samansayad93/HomeIntelligence/documents/پایان نامه کارشناسی.pdf

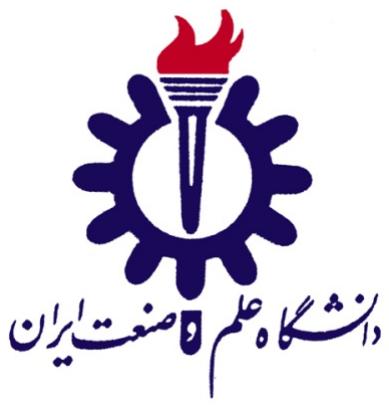
[picture p38: figure]

هدکشناد یسدنهم رتویپماک
هژورپ ینایاپ یسانشراک

## ناونع هژورپ : یحارط و هدایپ يزاس هناماس دنمشوه صیخشت دود و لرتنک تازیهجت یگناخ یتبم رب 32ESP

هدنراگن :
ناماس دایص لاعف
401521408

داتسا امنهار :
رتکد ریما يدهم ینیسح هزنم

رویرهش هام 1405

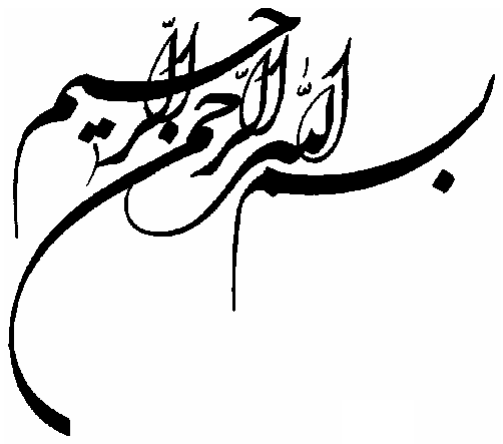
[picture p39: figure]

أ

هدیکچ

رد نیا ،هژورپ کی هناماـس دنمـشوه ینتبم رب درب 32ESP اب فده یحارط و هدایپ يزاـس کی دحاو هچراپکی يارب شیاپ طیارـش ،یطیحم صیخـشت طیارـش رطخ و لرتنک تازیهجت یکینورتکلا هعـسوت هداد هدـش تـسا . فده یلـصا ،هناماـس مهارف ندرک ناکما تفایرد و شزادرپ تاعلاطا یطیحم و لاقتنا اهنآ هب کی هناماـس مرن يرازفا زا قیرط هکبـش یب ،میـس رد رانک داجیا تیلباق لرتنک و را لاـس نامرف هب یخرب تازیهجت یکینورتکلا دوجوم رد طیحم تـسا . هب نم ظ رو شیاپ تیعـضو ،طیحم هاگتـسد هب هعومجم يا زا اهرگـسح لماـش رگـسح زاگ -2MQ، رگـسح امد و تبوطر 11DHT، رگـسح تدـش رون LDR و رگـسح صیخـشت تکرح PIR زهجم هدـش تـسا . رگـسح -2MQ اب هدافتـسا زا یجورخ ،گولانآ ناکما دنا هزا يریگ حطـس یبـسن زاگ و دود دوجوم رد طیحم ار مهارف یم دنک و رد تروـص روبع رادقم هزادنا يریگ هدـش زا هناتـسآ نییعت ،هدـش طیارـش هب ناونع تیعـضو رادشه ییاسانش هدش و هناماس مادقا هب لاعف يزاس رادشه یتوص یم دنک . نینچمه تاعلاطا طوبرم هب ،امد ،تبوطر تدـش رون و تیعـضو رح تک رد هزاب ياه ینامز صخـشم زا طیحم تفایرد هدـش و يارب شیاپ و شیامن تیعــضو متــسیــس رد رایتخا هناماــس مرن يرازفا رارق یم دریگ . هب روظنم شیازفا تیلباق يدربراک هاگتــسد رد هزوح لرتنک ،تازیهجت ود رتــسب یطابترا ییویدار RF رد سناکرف ياه 315 و 433 زترهاگم و نینچمه طابترا م نودا زمرق IR رد هناماـس رد رظن هتفرگ هدـش تـسا . نیا شخب ناکما تفایرد و ییاـسانـش نامرف ياه ییویدار و نودام ،زمرق هریخذ يزاـس اهنآ و هدافتـسا ددجم زا نامرف ياه هریخذ هدـش يارب لرتنک تازیهجت راگزاـس ار مهارف یم دنک . طابترا هاگتـسد اب هکبـش زا قیرط تیلباق WiFi درب 32ESP رارقرب هدـش و هب روظنم لاقتنا هداد و نامرف نایم هاگتــسد و هناماــس مرن يرازفا زا لکتورپ MQTT هدافتــسا هدــش تــسا . نینچمه يارب هداـس يزاـس هار يزادنا هیلوا و يریگولج زا یگتـسباو هب تاعلاطا هکبـش ،تباث کی راکوزاـس provisioning رد هاگتـسد هدایپ يزاـس هدـش تـسا هک زا یرط ق کی هطقن یـسرتـسد یب میـس و هاگرد يدنبرکیپ تحت ،بو ناکما نت ظ می تاـصخـشم هکبـش WiFi، تاعلاطا Broker MQTT ار مهارف یم دنک . رد شخب مرن يرازفا ربراک زین کی دروبـشاد تحت بو يارب شیامن هداد ياه تفایرد هدـش زا هاگتـسد و لاـسرا نامرف ياه یلرتنک یحارط هدـش تـسا . هب نیا ،بیترت ربراک یم دناوت نودب زاین هب یـسرتـسد میقتـسم هب تخـس ،رازفا تیعــضو طیحم ار شیاپ ،هدرک طیارــش رادــشه ار هدهاــشم هدومن و نامرف ياه دروم زاین ار يارب تازیهجت لاـسرا دنک . نیا هناماـس یم دناوت هب ناونع کی هنومن هیاپ يارب هعـسوت راکهار ياه دنمـشوه يزاـس طیحم ياه ینوکسم و دا ،يرا هناماس ياه شیاپ یطیحم و متسیس ياه لرتنک تازیهجت دروم هدافتسا رارق دریگ .

هژاو ياه يدیلک : هناخ ،دنمشوه نویساموتا ،یگناخ 32ESP، تنرتنیا ایشا ( IoT(

تسرهف بلاطم

ب

لصف :1 همدقم 1
-1-1 بی نا هلئسم | 2
-1-2 مها یت و ترورض هژورپ | 3
-1-3 فادها هژورپ | 4
-1-4 هدودحم هژورپ | 5
-1-5 شور ماجنا هژورپ | 5

لصف :2 نابم ی رظن ي 7
-2-1 ای تنرتن شا یا | 8
-2-1-1 ازجا ي لصا ی یک هناماس IoT | 8
-2-1-2 دربراک ای تنرتن شا یا رد هناخ دنمشوه | 9
-2-2 سی متس اه ي هناخ دنمشوه | 9
-2-3 می رلرتنکورک 32ESP | 10
10 | | | | | | | | | | | GPIO-2-3-2
-2-3-3 لدبم گولانآ هب دیجی لات ADC | 11
-2-4 رگسح اه ي حم یطی | 11
-2-4-1 رگسح -2MQ | 11
-2-4-2 رگسح 11DHT | 12
-2-4-3 رگسح تدش رون LDR | 13
-2-4-4 رگسح خشت یص تکرح PIR | 14
-2-5 رزاب | 14
-2-6 طابترا نودام زمرق | 15
-2-7 طابترا دار یو یی RF | 16
-2-8 طابترا WiFi | 17
18 ....... | | | | | | | | | Captive Portal-2-8-1
-2-9 لکتورپ MQTT | 18
18 ...... | | | | | | | | | MQTT Broker-2-9-1
-2-9-2 کیفیت ورس یس | 19
-2-9-3 طابترا MQTT زا رط یق WebSocket | 19
-2-10 خذ ی هر زاس ي تاعلاطا رد 32ESP | 20

لصف :3 لحت یل و حارط ی سی متس 21
-3-1 لحت یل نی دنمزا ي اه ي سی متس | 22
-3-2 رامعم ي لک ی سی متس | 24
-3-2-2 لایه تخس رازفا و عمج روآ ي هداد | 24
-3-2-3 لایه شزادرپ و لرتنک | 25
-3-2-4 لایه طابترا ی و طبار ربراک | 25
-3-3 حارط ی تخس رازفا | 26
-3-3-1 دحاو شزادرپ زکرم ي و لاصتا اهرگسح | 26
-3-3-2 سی متس طابترا سناکرف دار یو یی | 27
-3-3-3 سی متس طابترا نودام زمرق | 27
-3-3-4 سی متس رادشه و امن یش عضو یت | 28

تسرهف بلاطم

ج

-3-4 حارط ی مرن رازفا و راتخاس Firmware | 29
-3-4-1 راتخاس رلاوژام Firmware | 29
-3-4-2 هار زادنا ي و ارجا ي لصا ی سی متس | 30
-3-4-3 دم یریت اهرگسح و قطنم رادشه | 31
-3-5 حارط ی طابترا WiFi و MQTT | 32
-3-5-1 پی دنبرک ي و طابترا WiFi | 33
-3-5-2 طابترا MQTT | 33
-3-6 حارط ی سی متس RF | 34
-3-6-1 رد ی تفا و خذ ی هر زاس ي سی لانگ RF | 34
-3-6-2 شخپزاب و دم یریت سی لانگ RF | 35
-3-7 حارط ی سی متس نودام مرق ز | 35
-3-7-1 رد ی تفا و خذ ی هر زاس ي سی لانگ IR | 36
-3-7-2 شخپزاب و دم یریت سی لانگ IR | 36
-3-8 حارط ی سی متس خذ ی هر زاس ي | 36
-3-8-1 خذ ی هر ظنت ی تام و تاعلاطا هاگتسد | 37
-3-8-2 خذ ی هر زاس ي سی لانگ RF و IR | 37
-3-9 حارط ی سی متس Provisioning و Portal Captive | 38
-3-10 حارط ی Dashboard Web | 38

لصف :4 پی هدا زاس ي هناماس 40
-4-1 حم یط و رازبا اه ي هعسوت | 41.
-4-2 پی هدا زاس ي تخس رازفا | 42
-4-2-1 پی هدا زاس ي رگسح اه ي حم یطی | 42
-4-2-2 پی هدا زاس ي سی متس شه راد توص ی | 45
-4-3 پی هدا زاس ي سی متس طابترا دار یو یی RF | 46
-4-3-1 رد ی تفا و خذ ی هر زاس ي سی لانگ RF | 47
-4-3-2 شخپزاب و دم یریت سی لانگ RF | 47
-4-3-3 قطنم لک ی رد ی تفا و لاسرا RF | 49
-4-4 پی هدا زاس ي سی متس ودام ن زمرق IR | 49
-4-4-1 رد ی تفا و خذ ی هر زاس ي سی لانگ IR | 50
-4-4-2 شخپزاب و دم یریت سی لانگ IR | 51
-4-4-3 قطنم لک ی رد ی تفا و لاسرا IR | 53
-4-5 پی هدا زاس ي طابترا WiFi و MQTT | 53
-4-5-1 ای داج و هار زادنا ي Client MQTT | 53
-4-5-2 رارقرب ي و دم یریت لاصتا WiFi و MQTT | 54
-4-5-3 رد ی تفا و راشتنا نامرف اه ي MQTT | 56
-4-6 پی هدا زاس ي پی دنبرک ي لوا یه و دم یریت لاصتا هب هکبش | 57
-4-6-1 راتخاس تاعلاطا و هار زادنا ي | 57
-4-6-2 پی هدا زاس ي Portal Captive و دم یریت تساوخرد اه ي HTTP | 59
-4-6-3 رد ی تفا ، جنسرابتعا ی و خذ ی هر ظنت ی تام | 60
-4-7 پی هدا زاس ي دم یریت هظفاح و خذ ی هر زاس ي تاعلاطا | 60
-4-7-1 خذ ی هر و زاب ی با ی عضو یت هاگتسد | 61
-4-7-2 خذ ی هر و زاب ی با ی سی لانگ اه ي RF و IR | 61

تسرهف بلاطم

د

-4-8 هار زادنا ي و گنهامه ی لوژام اه | 61
-4-8-1 دم یریت نامرف اه ي سی متس | 63
-4-8-2 دم یریت اهرگسح و اظو یف هرود اي | 64
-4-9 پی هدا زاس ي دروبشاد بو و طبار ربراک ي | 65
-4-9-2 لاصتا هب Broker MQTT و رد ی تفا تاعلاطا | 65
-4-9-3 لاسرا نامرف و دم یریت عضو یت هناماس | 66

لصف :5 نومزآ و زرا ی با ی سی متس 67
-5-1 شور نومزآ و زرا ی با ی هناماس | 68
-5-2 نومزآ درکلمع اهرگسح | 68
-5-2-1 نومزآ رگسح امد و تبوطر | 69
-5-2-2 نومزآ رگسح رون | 69
-5-2-3 نومزآ رگسح دود و شتآ | 70
-5-2-4 نومزآ رگسح خشت یص تکرح | 71
-5-3 نومزآ هناماس رادشه | 71
-5-4 نومزآ لاصتا هب WiFi و Broker MQTT | 72
-5-5 نومزآ دروبشاد هناماس | 72
-5-6 نومزآ سی متس RF | 74
-5-6-1 نومزآ رد ی تفا سی لانگ RF | 74
-5-6-2 نومزآ لاسرا سی لانگ RF | 74
-5-6-3 نومزآ دم یریت سی لانگ RF | 75
-5-7 نومزآ سی متس IR | 75
-5-7-1 نومزآ رد ی تفا سی لانگ IR | 76
-5-7-2 نومزآ لاسرا سی لانگ IR | 76
-5-7-3 نومزآ دم یریت سی لانگ IR | 77
-5-8 نومزآ زیر هناماس Provisioning | 77

لصف :6 تن ی هج گیري 79
-6-1 عمج دنب ي لحارم ماجنا هژورپ | 80
-6-2 اتن یج لصاح زا پی هدا زاس ي | 80
-6-3 دودحم یت اه ي هژورپ | 81
-6-4 پی داهنش اه ي هعسوت رد آی هدن | 81
-6-5 عمج دنب ي اهن یی | 82

لصف :7 عجارم 83

لصف :8 تسویپ اه 85

تسرهف لاکشا

ه

لکش ( 1-2 ) می رلرتنکورک 32ESP | 10.
لکش ( 2-2 ) رگسح -2MQ | 12
لکش ( 3-2 ) رگسح 11DHT | 12
لکش ( 4-2 ) رگسح تدش رون | 13
لکش ( 5-2 ) رگسح خشت یص تکرح PIR | 14
لکش ( 6-2 ) رزاب | 14.
لکش ( 7-2 ) گی هدنر و هدنتسرف نودام زمرق | 15
لکش ( 8-2 ) گی هدنر دار یو یی | 16
لکش ( 9-2 ) هدنتسرف دار یو یی | 16
لکش ( 1-3 ) رامعم ي لک ی سی متس | 24.
لکش ( 2-3 ) دنور هار زادنا ي سی متس | 30
لکش ( 3-3 ) دنور ارجا ي هقلح لصا ی سی متس | 31
لکش ( 4-3 ) دنور دم یریت رگسح اه | 31
لکش ( 5-3 ) دنور دم یریت رگسح -2MQ | 31
لکش ( 1-4 ) دنور تخاس و راذگراب ي Firmware | 42
لکش ( 2-4 ) ارف ی دن رد ی تفا سی لانگ RF | 49
لکش ( 3-4 ) ارف ی دن لاسرا سی لانگ RF | 49
لکش ( 4-4 ) ارف ی دن رد ی تفا سی لانگ IR | 53
لکش ( 5-4 ) ارف ی دن لاسرا سی لانگ IR | 53
لکش ( 6-4 ) هحفص ظنت ی تام | 59
لکش ( 7-4 ) دروبشاد بو | 65
لکش ( 1-5 ) اتن یج رگسح امد و تبوطر | 69
لکش ( 2-5 ) تن ی هج رگسح رون | 69
لکش ( 3-5 ) اتن یج رگسح دود و شتآ | 70
لکش ( 4-5 ) اتن یج رگسح خشت یص تکرح | 71
لکش ( 5-5 ) تن ی هج نومزآ لاصتا هب هکبش و Broker MQTT | 72
لکش ( 6-5 ) امن یش تاعلاطا اهرگسح رد دروبشاد | 72
لکش ( 7-5 ) امن یش رادشه رد دروبشاد | 73
لکش ( 8-5 ) لاسرا نامرف زا دروبشاد | 73
لکش ( 9-5 ) رد ی تفا سی لانگ RF | 74
لکش (10-5 ) لاسرا سی لانگ RF | 74
لکش ( 11-5 ) دم یریت سی لانگ RF | 75
لکش ( 12-5 ) رد ی تفا سی لانگ IR | 76
لکش (13-5 ) لاسرا سی لانگ IR | 76
لکش ( 14-5 ) دم یریت سی لانگ IR | 77
لکش ( 15-5 ) هحفص ظنت ی تام Provisioning | 78

تسرهف لوادج

و

لودج ( 1-3) اپ یه اه ي 32ESP | 28
لودج ( 2-3) ظو ی هف لوژام اه ي Firmware | 29
لودج ( 3-3)Topic اه ي برم طو هب اهرگسح | 33
لودج ( 4-3) تاصخشم AP | 38
لودج ( 1-4) راتخاس هداد ظنت ی تام Provisioning | 58.

# لصف 1 :

# همدقم

حارط ی و پی هدا زاس ی خشت دنمشوھ ھناماس یص ھجت لرتنک و دود ی تاز گناخ ی تبم ی رب 32ESP

2

ھمدقم
رد لاـس ياه ،ریخا هعـسوت يروانف ياه یطابترا و هناماـس ياه هتفهن بجوم شرتـسگ هدافتـسا زا متـسیـس ياه دنمـشوه رد طیحم ياه ،ینوکـسم يرادا و یتعنـص هدـش تـسا . یکی زا مهم نیرت هزوح ياه لـصاح زا نیا ،هعـسوت تنرتنیا یـشا ا ( Things of Internet ای IoT ( تـسا . تنرتنیا ایـشا هب کبـش ه يا زا تازیهجت یکیزیف قلاطا یم دوـش هک اب هرهب يریگ زا ،اهرگـسح دنزادرپ ه ،اه مرن اهرازفا و طـساو ياه ،یطابترا تیلباق مج ع ،يروآ ،شزادرپ لدابت تاعلاطا و رد یخرب دراوم لامعا لرتنک رب طیحم نوماریپ دوخ ار دنراد .[1] رد نینچ هناماـس ،ییاه اهرگــسح هفیظو تفایرد تاعلاطا زا ،طیحم دحاو یــشزادرپ هفیظو لیلحت و تیریدم هداد اه و شخب یطابترا هفیظو لاقتنا تاعلاطا و تفایرد نامرف ياه یلرتنک ار رب هدهع دراد [1] [2]. یکی زا ياهدربراک مهم تنرتنیا ،ایـشا هعـسوت هناماـس ياه دنمـشوه یگناخ تـسا . رد کی طیحم ،دنمـشوه تازیهجت فلتخم یم دنناوت زا قیرط کی هکبـش یطابترا اب رگیدکی و اب ربراک لماعت هتـشاد دنـشاب . نیا لماعت یم دناوت لماــش شیاپ طیارــش ،یطیحم صیخــشت دادخر ياه ،يداعریغ لاــسرا ،رادــشه لرتنک تازیهجت یکیرتکلا و تبث تاعلاطا دــشاب . هدافتــسا زا نینچ هناماــس ییاه یم دناوت ناکما تراظن زا هار رود و شهاک یگتسباو هب لرتنک یتسد تازیهجت ار مهارف دنک . رد نیا ،هژورپ کی باه دنمـشوه ینتبم رب درب 32ESP یحارط و دایپ ه يزاـس هدـش ـسا ت . 32ESP کی هناماـس يور هـــشارت اـب تـیلباـق WiFi رد دـناـب 2.4 ،زترهاـگیگ هدـنزادرپ 32 یتیب و هـعومجم يا زا طـــساو ياـه يدورو / یجورخ لاتیجید و انآ گول تـسا هک طـسوت تکرـش Espressif هئارا هدـش و يارب ییاهدربراک زا هلمج تازیهجت دنمـشوه یگناخ و تنرتنیا ایـشا بـسانم ـسا ت [3]. نیا گژیو ی اه ثعاب هدـش تـسا 32ESP دناوتب هولاع رب شزادرپ داد ه ياه ،اهرگـسح طابترا کبـش ه يا و لرتنک تازیهجت یبناج را زین رد کی دحاو تخـس يرازفا ماجنا دهد .
متـسیـس هعـسوت هتفای رد نیا هژورپ هولاع رب صیخـشت دود و ،زاگ ناکما هزادنا يریگ ،امد تبوطر و تدـش رون و نینچمه صیخـــشت تـکرح ار مهارف یم دـنک . نینچمه يارب شیازفا تـیلباـق لرتنک تازیهجت ،فلتخم ود هـعومجم طاـبترا ییویدار رد سناـکرف ياـه 315 و 433 زترهاـگم و کـی هـعومجم طاـبترا نوداـم زمرق رد رظن هتفرگ هدـش تـسا . هب نیا ،بیترت متـسیـس رداق تـسا یخرب لانگیـس ياه ییویدار و نودام زمرق ار ،تفایرد هریخذ و رد تروص زاین شخپزاب دنک . طابترا نایم باه دنمـشوه و تخاـسریز مرن يرازفا متـسیـس زا قیرط WiFi و لکتورپ MQTT ماجنا یم دوـش . MQTT کی لکتورپ یطابترا کبـس ینتبم رب يوگلا راـشتنا / كارتـشا (Subscribe/Publish (تـسا هک هب روط هژیو يارب طیحم ياه ياراد تیدودحم عبانم و ياهدربراک نیـشام به نیـشام و تنرتنیا ایـشا بـسانم یحارط هدـش ـسا ت [4]. رد یا ن ،هژورپ هداد ياه اهرگـسح زا قیرط MQTT رـشتنم هدـش و امرف ن ياه یلرتنک زین زا قیرط نیمه رتسب هب 32ESP لاسرا یم دنوش . زا يوــس ،رگید يارب لماعت ربراک اب ،متــسیــس کی دروبــشاد تحت بو یحارط هدــش تــسا هک زا قیرط WebSocket هب Broker MQTT لـصتم یم دوـش . نیا دروبـشاد ناکما هدهاـشم تاعلاطا ،اهرگـسح هدهاـشم اهرادـشه و لاـسرا نامرف ياه یلرتنک ار مهارف یم دنک . رد ،هجیتن هژورپ رـضاح ار یم ناوت کی باه دنمـشوه نچ د هروظنم تــسناد هک فیاظو شیاپ ،طیحم صیخــشت ،دادخر داجیا ،رادــشه طابترا بــش هک يا و لرتنک تازیهجت ار رد کی هناماس هچراپکی ماجنا یم دهد .

-1-1 نایب هلئسم

رد يرایـسب زا طیحم ياه ینوکـسم و ،يرادا تازیهجت یکیرتکلا و هناماـس ياه فلتخم هب تروـص لقتـسم دروم هدافتـسا رارق یم دنریگ و تاعلاطا طوبرم هب طیارـش یطیحم زین ًلاومعم هب تروـص زکرمتم و رمتـسم عمج

3

ھمدقم
يروآ من ی دوــش . رد شور ياه ،یتنــس صیخــشت ییاهدادخر دننام یازفا ش نازیم دود ای ،زاگ تارییغت ،امد روـضح دارفا ای رییغت دیدـش طیارـش يرون نکمم تـسا هب تروـص یتـسد ای طـسوت تازیهجت لقتـسم ماجنا دوـش . نینچ يدرکیور هولاع رب شیازفا یگدـیچیپ ،متـــسیـــس ناـکما شیاـپ هـچراـپکی و لرتنک زا هار رود ار دودـحم یم دنک .
زا فرط ،رگید يرایــسب زا تازیهجت وم دوج رد طیحم ياه یگناخ زا شور ياه یطابترا یتوافتم يارب لرتنک هداـفتـــسا یم دـننک . یخرب تازیهجت زا ومیر ت ياـه نوداـم زمرق و یخرب رگید زا تومیر ياـه ییویدار رد سناـکرف ییاـه دـنناـم 315 اـی 433 زترهاـگم هداـفتـــسا یم دـننک . رد ،هـجیتن يارب لرتنک هـچراـپکی نیا تازیهجت ًلاومعم این ز هب نیدنچ رتنک ل هدننک و طساو ازجم دوجو دراد . هلئـسم یلـصا نیا ،هژورپ یحارط و هدایپ يزاـس کی هناماـس هچراپکی تـسا هک دناوتب تاعلاطا طوبرم هب طیارـش طیحم ار زا قیرط هعومجم يا زا اهرگـسح تفایرد ،هدرک اهنآ ار رد کی دحاو یـشزادرپ تیریدم ،دنک تاعلاطا ار زا قیرط هـکبـــش WiFi و MQTT رد راـیتخا مرن رازفا رارق دـهد و ناـکما لرتنک تازیهجت یکیرتکلا ار زین مهارف دنک .
يارب یبایتسد هب نیا ،فده زا 32ESP هب ناونع هتسه یشزادرپ و یطابترا متسیس هدافتسا هدش تسا . رد شخب شیاپ ،طیحم روـسنـس -2MQ يارب صیخـشت دود و ياهزاگ لباق ،لاعتـشا روـسنـس 11DHT يارب هزادنا يریگ امد و ،تبوطر رگـسح يرون LDR يارب هزادنا يریگ یبـسن تدـش رون و رگـسح یتکرح PIR يارب صیخـشت تکرح دروم هدافتـسا رارق هتفرگ دنا . تاعلاطا به تـسد هدمآ زا نیا اهرگـسح هب تروـص هرود يا شزادرپ و زا قیرط MQTT رشتنم یم دنوش . رد شخب لرتنک زین متــسیــس زا گ هدنری و هدنتــسرف ياه RF رد ود دناب 315 و 433 زترهاگم و نینچمه هدنریگ و هدنتـسرف نودام زمرق هدافتـسا یم دنک . هناخباتک RCSwitch ناکما تفایرد و لاـسرا ياهدک یخرب تازیهجت ییویدار جیار رد سناـکرف ياـه 315 و 433 زترهاـگم ار مهارف یم دـنک [5] . نینچمه هـناـخباـتک 8266IRremoteESP يارب تفایرد و لاسرا لانگیس ه يا نودام زمرق دروم هدافتسا رارق هتفرگ تسا [6]. ،نیاربانب هلئـسم نیا هژورپ ار یم ناوت هب تروـص یحارط کی باه دنمـشوه فیرعت درک هک هـس هفیظو یلـصا شیاپ طیارـش ،یطیحم صیخـشت دادخر و داجیا رادـشه و لرتنک تازیهجت یکیرتکلا ار رد کی رتـسب دحاو بیکرت یم نک د.

-1-2 تیمها و ترورض هژورپ

شیازفا هدافتـسا زا تازیهجت یکیرتکلا و شرتـسگ متـسیـس ياه ،دنمـشوه زاین هب هناماـس ییاه ار شیازفا هداد تـسا هک دناوتب هولاع رب لرتنک ،تازیهجت تیعضو طیحم ار زین شیاپ دننک . یکی زا تیزم ياه یلصا هدافتسا زا تنرتنیا ایـشا رد نینچ هناماـس ،ییاه داجیا طابترا نایم يایند یکیزیف و هناماـس ياه مرن يرازفا ؛تـسا هب گ هنو يا هک تاعلاطا رگسح اه یم دنناوت ،تفایرد لقتنم و رد شخب مرن يرازفا شزادرپ دنوش . دوجو نیدنچ رگـسح رد کی هناماـس ناکما عمج آ يرو هم نامز تاعلاطا فلتخم یطیحم ار مهارف یم دنک . رد هژورپ ،رـضاح تاعلاطا طوبرم هب ،امد ،تبوطر تدـش ،رون نازیم دود و تیعـضو تکرح رد رایتخا متـسیـس رارق یم دریگ . نیا تاعلاطا یم دنناوت يارب یـسررب تیعـضو ظحل ه يا طیحم و صیخـشت یخرب طیارـش يداعریغ دروم هدافتسا رارق دنریگ .
هدافتسا زا روسنس ياه یطیحم ناکما شنکاو یرس ع رت متسیس تبسن هب ییاهدادخر دننام شیازفا رادقم زاگ ای دود و صیخـشت تکرح ار مهارف یم دنک . رد هژورپ ،رـضاح رد تروـص روبع رادقم دناوخ ه هدـش زا روـسنـس -2MQ زا هناتسآ نییعت ،هدش متسیس تیعضو رادشه ار لاعف هدرک و مایپ هطوبرم ار زا قیرط MQTT رشتنم

4

ھمدقم
یم دنک . نینچمه رد تروص صیخشت ،تکرح ناکما داجیا رادشه و لاعف يزاس رزاب دوجو دراد . طابترا WiFi و MQTT ثعاب یم ـش دو تاعلاطا مج ع يروآ هدـش اهنت رد حطـس دوخ هاگتـسد یقاب دنامن و ناوتب اـهنآ ار هـب کـی Broker و مرن ياـهرازفا رگید لـقتنم درک . MQTT هـب لـیلد هداـفتـــسا زا لدـم Subscribe/Publish، ناکما يزاـسادج هدننکدیلوت و فرـصم هدننک هداد ار مهارف یم دنک و يارب طابترا نایم تازیهجت IoT م بسان تسا [4]. یکی زا یگژیو ياه مهم ،هژورپ بیکرت شیاپ طیحم اب لرتنک تازیهجت یکیرتکلا تــسا . متــسیــس یم دناوت انگیـس ل ياه RF رد ود دناب 315 و 433 زترهاگم ار تفایرد و هریخذ هدرک و رد نامز بـسانم شخپزاب دنک . هـناـخباـتک RCSwitch زین يارب لرتنک تازیهجت ییویدار جیار اـب دـنتـــسرف ه اـه و هدـنریگ ياـه 315 و 433 زترهاگم یحارط هدـش تـسا [5]. نینچمه هدافتـسا زا طابترا نودام زمرق ثعاب یم دوـش متـسیـس دناوتب اب یخرب تازیهجت زهجم هب تومیر IR لماعت هتـشاد دـشاب . هناخباتک 8266IRremoteESP يارب 32ESP ناکما تفایرد و لاسرا لانگیس ياه نودام زمرق و ینابیتشپ زا لکتورپ ياه ددعتم ار مهارف یم دنک [6]. بیکرت نیدنچ تیلباق رد کی درب 32ESP ثعاب یم دوـش هب ياج هدافتـسا زا دنچ متـسیـس لقتـسم يارب شیاپ ،طیحم تفایرد نامرف ياه بی میس و لرتنک ،تازیهجت ناوتب شخب لباق یهجوت زا نیا فیاظو ار رد کی باه دحاو هدایپ يزاـس درک . نینچمه يرامعم رلاوژام مرن ،رازفا هدافتـسا زا MQTT و تیلباق ياه یطابترا 32ESP ناکما هعـسوت متـسیـس رد هدنیآ ار مهارف یم دنک . يارب ،لاثم یم ناوت ياهرگـسح ،دیدج تازیهجت یلرتنک رتشیب ای سیورس ياه مرن يرازفا رگید ار نودب رییغت یساسا رد راتخاس یلک متسیس هب نآ هفاضا درک .

-1-3 فادها هژورپ

فده یلـصا نیا ،هژورپ یحارط و هدایپ يزاـس کی هناماـس دنمـشوه ینتبم رب 32ESP يارب صیخـشت دود و شتآ و شیاپ طیحم و لرتنک تازیهجت یکیرتکلا زا قیرط هکبـش WiFi تـسا و نینچمه فادها یعرف هژورپ ترابع دنا زا :
.1 یحارط و هدایپ يزاس شخب تخس يرازفا ینتبم رب 32ESP .2 صیخشت دوجو دود و طیارش طبترم اب شتآ اب هدافتسا زا -2MQ .3 هزادنا يریگ امد و تبوطر طیحم اب هدافتسا زا 11DHT .4 هزادنا يریگ تدش رون طیحم اب هدافتسا زا LDR .5 صیخشت روضح ای تکرح رد طیحم اب هدافتسا زا رگسح PIR .6 داجیا متسیس رادشه یتوص اب هدافتسا زا رزاب .7 تفایرد لانگیس ياه نودام زمرق زا رلرتنک تازیهجت فلتخم .8 هریخذ نامرف ياه نودام زمرق تفایرد هدش .9 لاسرا لانگیس ياه نودام زمرق يارب لرتنک تازیهجت لتخم ف .10 تفایرد و لاسرا لانگیس ياه ییویدار يارب لرتنک تازیهجت ییویدار .11 يرارقرب طابترا هاگتسد اب هکبش WiFi .12 هدافتسا زا MQTT يارب لدابت تاعلاطا نایم هاگتسد و هناماس مرن يرازفا

5

ھمدقم
.13 داجیا تیلباق شیاپ متسیس زا هار رود .14 مهارف ندرک ناکما لرتنک تازیهجت یکیرتکلا زا قیرط هناماس مرن يرازفا .15 داجیا يراتخاس لباق هعسوت يارب هفاضا ندرک اهرگسح و تیلباق ياه دیدج رد هدنیآ

-1-4 هدودحم هژورپ

هدودحم نیا هژورپ لماـش یحارط و هدایپ يزاـس کی هنومن یتایلمع زا هناماـس دنمـشوه شیاپ و لرتنک طیحم ینتبم رب 32ESP تـــسا . رد نیا ،هژورپ 32ESP هـب ناونع دـحاو شزادرپ يزکرم هـفیظو تـفاـیرد ا تاـعلاط زا ،اهرگـسح شزادرپ هداد ،اه تیریدم تاطابترا و لاـسرا ای تفایرد لانگیـس ياه نودام زمرق و ییویدار ار رب هدهع دراد .
- صیخشت دود و طیارش طبترم اب شتآ
- هزادنا يریگ امد و تبوطر و تدش رون
- صیخشت تکرح
- لاسرا و تفایرد لانگیس ياه نودام زمرق
- لاسرا و تفایرد لانگیس ياه ییویدار
- لاصتا هاگتسد هب WiFi
- طابترا اب هناماس مرن يرازفا
- لاسرا تاعلاطا اهرگسح هب هناماس مرن يرازفا
- تفایرد نامرف زا هناماس مرن يرازفا يارب لرتنک تاریهجت یکیرتکلا اب دوجو تیلباق ياه ،قوف هژورپ ياراد هدودحم یـصخـشم تـسا . يارب ،لاثم درکلمع صیخـشت شتآ رد نیا هژورپ رد حطـس کی هناماـس هنومن و یـشزومآ / یـسدنهم رد رظن هتفرگ هدـش و دیابن نآ ار هب ناونع نیزگیاج تازیهجت ینمیا و ملاعا قیرح ياراد هـیدـییاـت درادـناـتـــسا يارب دربراـک ياـه یتاـیح رد رظن تـفرگ . نینچمه لرتنک تازیهجت زا قیرط IR و RF هب عون لکتورپ و يراگزاس تازیهجت دصقم هتسباو سا ت.

-1-5 شور ماجنا هژورپ

دنیارف ماجنا هژورپ هب تروـص هلحرم يا و رب ساـسا يدنمزاین ياه تخـس يرازفا و مرن يرازفا متـسیـس ماجنا هدـش تـسا . رد هلحرم ،تـسخن هلئـسم و يدنمزاین ياه یلـصا متـسیـس لماـش صیخـشت طیارـش ،رطخ شیاپ طیحم و لرتنک تازیهجت یکیرتکلا یـسررب دـش . سپـس يرامعم یلک متـسیـس و هوحن طابترا ایم ن ،اهرگـسح 32ESP و هناماـس مرن يرازفا صخـشم دیدرگ . رد هلحرم ،دعب تاعطق تخـس يرازفا زایندروم باختنا و رادم هیلوا یحارط دش . 32ESP هب ناونع لرتنک هدننک يزکرم باختنا ؛دش اریز هولاع رب تیلباق ،یشزادرپ تاناکما یطاـبترا زاـیندروم هژورپ زا هـلمج WiFi ار رد راـیتخا رارق یم دـهد . سپ زا یحارط تـخـــس ،رازفا Firmware هاگتــسد هعــسوت هداد دــش . نیا شخب هفیظو ندناوخ تاعلاطا ،اهرگــسح صیخــشت تیعــضو ياه ،فلتخم تیریدم يدورو و یجورخ ،اه تفایرد و لاـسرا لانگیـس ياه IR و RF و نینچمه تیریدم طابترا هکبـش ار رب هدهع دراد . رد شخب ،یطابترا هاگتــسد زا قیرط WiFi هب هکبــش لــصتم هدــش و طابترا نایم 32ESP و

6

ھمدقم
هناماـس مرن يرازفا اب هدافتـسا زا MQTT رارقرب هدـش تـسا . رد نیا ،يرامعم هاگتـسد یم دناوت تاعلاطا طوبرم هب اهرگـسح و تیعـضو دوخ ار رد Topic ياه صخـشم رـشتنم دنک و رد ،لباقم مایپ ياه یلرتنک ار زا Topic ياه هطوبرم تفایرد یامن د. رد همادا شخب مرن يرازفا هعـسوت هداد هدـش و تیلباق هدهاـشم تاعلاطا و لاـسرا نامرف ياه یلرتنک رد نآ مهارف هدـش تـسا . سپ زا لاـصتا يازجا ،فلتخم شیامزآ ياه طوبرم هب ،اهرگـسح طابترا WiFi، لدابت مایپ MQTT و درکلمع هدنتـسرف و هدنریگ ياه IR و RF ماجنا هدـش تـسا . رد ،تیاهن درکلمع یلک هناماس اب یسررب ویرانس ياه فلتخم دروم یبایزرا رارق هتفرگ تسا .

# لصف 2 :

# ینابم يرظن

نابم ی رظن ی

شرتـسگ يروانف ياه ،یطابترا رلرتنکورکیم ياه مک فرـصم و هکبـش ياه یب میـس ثعاب هدـش تـسا هک تازیهجت یکینورتکلا دـنناوتب هولاع رب ماـجنا فیاـظو ،یلرتنک تاـعلاطا طیحم نوماریپ دوخ ار زین تـفاـیرد و زا قیرط هکبــش لقتنم دننک . نیا درکیور یکی زا هیاپ ياه یلــصا لکــش يریگ تنرتنیا ایــشا ( of Internet Things ای IoT ( تسا .
رد هناماـس ياه ،دنمـشوه بیکرت رگـسح ،اه دحاو ،شزادرپ طابترا هکبـش و مرن رازفا يدربراک ناکما شیاپ رــش طیا یطیحم و لرتنک تازیهجت ار مهارف یم دنک . رد کی هناخ ،دنمــشوه نینچ هناماــس يا یم دناوت یتاعلاطا دننام ،امد ،تبوطر تدـش ،رون دوجو دود ای شتآ ار تفایرد هدرک و رد ،لباقم تازیهجت فلتخم ار زا قیرط تاطابترا یب میس لرتنک دنک . هژورپ رــضاح کی متــسیــس دنمــشوه ینتبم رب 32ESP تــسا هک هولاع رب شیاپ طیارــش ،یطیحم تیلباق یخـشت ص دود و ،شتآ صیخـشت ،تکرح داجیا رادـشه یتوـص و تفایرد و لاـسرا نامرف ياه نودام زمرق و ییویدار ار مهارف یم دنک . طابترا هاگتــسد اب تخاــسریز هکبــش زا قیرط WiFi و لدابت هداد اب تــسا هداف زا لکتورپ MQTT ماجنا یم دوش .

-2-1 تنرتنیا ایشا

تنرتنیا ایــشا هب هعومجم يا زا تازیهجت یکیزیف هتفگ یم دوــش هک ياراد ،رگــسح تیلباق شزادرپ و طابترا هکبـش هدوب و یم دنناوت تاعلاطا طوبرم هب طیحم ای تیعـضو دوخ ار عمج يروآ و اب ریاـس هناماـس اه هلدابم دننک [1]. رد کی هناماـس IoT ًلاومعم هـس هفیظو یلـصا تفایرد تاعلاطا زا طیحم ، شزادرپ و ریـسفت تاعلاطا ، لاــسرا تاعلاطا ای يارجا نامرف دوجو دراد . رد هژورپ ،رــضاح ياهرگــسح -2MQ، 11DHT،LDR و PIR هـفیظو تـفاـیرد تاـعلاطا یطیحم ار رب هدـهع دـنراد 32.ESP هـفیظو شزادرپ هـیلوا ار ماـجنا هداد و WiFi و MQTT يارب لاقتنا تاعلاطا هب راک یم دنور .

-2-1-1 يازجا یلصا کی هناماس IoT

کی هناماـس تنرتنیا ایـشا زا هعومجم يا زا يازجا تخـس يرازفا و مرن يرازفا لیکـشت یم دوـش هک هفیظو تـفاـیرد تاـعلاطا زا ،طیحم شزادرپ هداد ،اـه يرارقرب طاـبترا و هـئارا تاـمدـخ هـب ربراـک ار رب هدـهع دـنراد . لاومعم یم ناوت درکلمع یلک اهنآ ار رد راهچ شخب یلــصا لماــش هیلا ،رگــسح هیلا ،شزادرپ هیلا یطابترا و هیلا دربراک یـسررب درک . رد نیا ،راتخاـس هداد ادتبا زا طیحم تفایرد یم ،دوـش سپـس طـسوت دحاو یـشزادرپ دروم شزادرپ رارق هتفرگ و زا قیرط ب رتـس یطابترا هب ریاـس يازجا هناماـس لقتنم یم دوـش . رد ،تیاهن هداد ياه شزادرپ هدـش رد رایتخا ربراک ای ریاـس سیورـس ياه يدربراک رارق هتفرگ و ناکما ماجنا تایلمع یلرتنک زین مهارف یم دوش .

-2-1-1-1 هیلا رگسح
هیلا رگـسح نیتـسخن شخب هناماـس IoT تـسا هک امیقتـسم اب طیحم یکیزیف طابترا د درا . هفیظو یلـصا نیا ،هـیلا تـفاـیرد تـیمک اـه و دادـخر ياـه یکیزیف دوجوم رد طیحم و لـیدـبت اـهنآ هـب هداد يا تـــسا هـک دـحاو یــشزادرپ دناوتب نآ ار تفایرد و لیلحت دنک . تیمک ییاه دننام ،امد ،تبوطر تدــش ،رون دوجو دود ای زاگ و تکرح دارفا زا هلمج یتاعلاطا دنتــسه هک یم دنناوت ــسوت ط رگــسح ياه فلتخم هزادنا يریگ دنوــش . عون

نابم ی رظن ی

رگـسح ياه دروم هدافتـسا رد نیا هیلا هب دربراک هناماـس یگتـسب دراد و لاومعم يارب شـشوپ هداد نیدنچ هبنج زا تیعضو ،طیحم زا هعومجم يا زا رگسح اه هب تروص مه نامز هدافتسا یم دوش .

-2-1-1-2 هیلا شزادرپ
هیلا شزادرپ هفیظو تفایرد هداد ياه صاح ل زا هیلا ،رگسح تیریدم اهنآ و يارجا قطنم یلرتنک هناماس ار رب هدهع دراد . نیا هیلا رد عقاو هتـسه میمـصت يریگ هناماـس IoT بوـسحم یم دوـش و یم دناوت یتایلمع دننام ندناوخ هرود يا رگـسح ،اه یـسررب طیارـش ،صاخ صیخـشت دادخر ،اه تیریدم اهرادـشه و هدامآ يزاـس هداد اه يارب لاقتنا هب هکبـش ار ماجنا دهد . رد هناماـس ياه ینتبم رب ،رلرتنکورکیم نیا فیاظو لاومعم طـسوت کی درب یــشزادرپ ماجنا یم دوــش هک ع هولا رب تردق ،یــشزادرپ طبار ياه يدورو و یجورخ و تاناکما یطابترا دروم زاین ار رد رایتخا متسیس رارق یم دهد .

-2-1-1-3 هیلا یطابترا
هیلا یطابترا لوئـسم داجیا طابترا نایم ،تازیهجت دحاو یـشزادرپ و سیورـس ياه مرن يرازفا تـسا . رد کی هناماـس IoT، هداد ياه دیلوت هدـش طـسوت اهرگـسح مز ینا شزرا يدربراک يرتشیب ادیپ یم دننک هک ناوتب اهنآ ار زا قیرط کی هکبـش هب ریاـس شخب ياه متـسیـس لقتنم درک . نینچمه نیا هیلا دیاب ناکما نا ت لاق تاعلاطا رد تهج ،سوکعم ینعی زا ریاـس شخب ياه متـسیـس هب هاگتـسد ار زین مهارف دنک . باختنا يروانف و لکتورپ یطابترا بسانم ریثات یمیقتسم رب هوحن درکلمع و هعسوت يریذپ هناماس IoT دراد .

-2-1-1-4 هیلا دربراک
هیلا دربراک نیرتلااب حطــس يرامعم هناماــس IoT تــسا و هفیظو نآ لیدبت هداد اه و تیلباق ياه هیلا ياه نییاپ رت هب تامدخ لباق هدافتـسا يارب ربراک تـسا . رد نیا ،هیلا تاعلاطا تفایرد هدـش زا تازیهجت و گـسح ر اه یم دنناوت هب لکش بسانم هب ربراک شیامن هداد دنوش و رد ،لباقم نامرف ياه دروم رظن ربراک زین زا قیرط طبار يربراک هب هناماس لاسرا دنوش . رد عقاو نیا هیلا هطقن لماعت میقتسم ربراک اب هناماس بوسحم یم دوش و دیاب دناوتب تیعضو متسیس ار هب یلکش لباق مهف هئارا دنک .

-2-1-2 دربراک تنرتنیا ایشا رد هناخ دنمشوه

هناخ دنمشوه یکی زا مهم نیرت هزوح ياه دربراک تنرتنیا ایشا تسا . رد کی هناماس هناخ دنمشوه ، تازیهجت و رگـسح ياه فلتخم زا قیرط کی هکبـش یطابترا هب رگیدکی لـصتم یم دنوـش و ناکما عمج يروآ ،تاعلاطا شیاپ تیعضو و لرتنک تازیهجت مهارف می دوش . نیا تازیهجت یم دناوت لماش رگسح ياه ،یطیحم متسیس ياه ،رادـشه تازیهجت ،ییانـشور مزاول یگناخ و ریاـس تازیهجت یکینورتکلا دنـشاب . لاـصتا نیا ازجا هب کی هناماـس يزکرم ای رتـسب مرن يرازفا ثعاب یم دوـش تاعلاطا یطیحم رد کی لحم لباق هدهاـشم هدوب و يرایـسب زا تایلمع تنک یلر نودب زاین هب روضح یکیزیف ربراک ماجنا دنوش .

-2-2 متسیس ياه هناخ دنمشوه

هناخ دنمـشوه هب یطیحم قلاطا یم دوـش هک رد نآ تازیهجت و هناماـس ياه فلتخم اب هدافتـسا زا يروانف ياه یطابترا و یـشزادرپ هب رگیدکی لـصتم هدـش و ناکما ،شیاپ تیریدم و لرتنک تازیهجت و طیارـش یطیحم

نابم ی رظن ی

هب تروـص راکدوخ ای زا هار دود مهارف یم دوـش . رد نینچ هناماـس ،ییاه تاعلاطا طیحم طـسوت گـسح ر ياه فلتخم عمج يروآ هدـش و سپ زا ،شزادرپ زا قیرط کی رتـسب یطابترا هب شخب مرن يرازفا لقتنم یم دنوـش . رد ،لباقم ربراک زین یم دناوت اب لاـسرا نامرف ياه ،یلرتنک درکلمع تازیهجت لـصتم هب هناماـس ار رییغت دهد . يرواـنف ییاـه دـنناـم Zigbee، Bluetooth، WiFi و Wave-Z زا هـلمج يرواـنف ياـه دروم هداـفتـــسا رد هداـیپ يزاس هناماس ياه هناخ دنمشوه دنتسه .

-2-3 رلرتنکورکیم 32ESP

SoC (تکرـش Systems Espressif تـسا هک يارب | 1 | 32ESP هداوناخ يا زا هـشارت ياه متـسیـس يور هـشارت (
دربراک ياه یطابترا و متـسیـس ياه هتفهن یحارط هدـش تـسا . نیا هداوناخ ياراد هدنزادرپ 32 ،یتیب ،هظفاح WiFi، ADC، Bluetooth و هعومجم يا زا طبار ياه یبناج تـسا . قبط تادنتـسم ،یمـسر 32ESP زا WiFi اب درادناتـــسا ياه n/g/b802.11 ینابیتـــشپ هدرک و ياراد ADC دزاود ه ،یتیب GPIO ياه ،ددعتم PWM، C2I، SPI و ریاـس دحاو ياه یبناج تـسا [3]. دوجو WiFi یلخاد یکی زا لیلاد یلـصا باختنا 32ESP يارب نیا هژورپ ؛تسا اریز هاگتسد یم دناوت نودب زاین هب لوژام یطابترا هناگادج هب هکبش لصتم دوش .

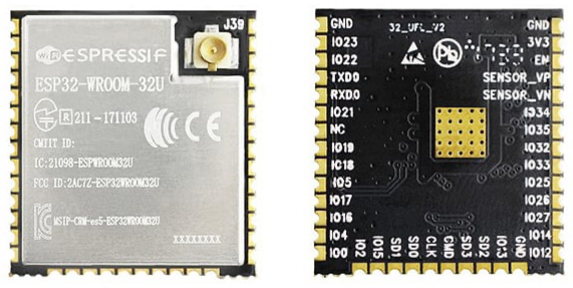
[picture p40: figure]

لکش (2-1 ) رلرتنکورکیم 32ESP

GPIO -2-3-2

2
GPIO ففخم تراـبع Output/Input Purpose General تـــسا و هـب هـیاـپ ياـه يدورو و یجورخ یمومع رلرتنکورکیم قلاطا یم دوـش . نیا هیاپ اه لباق تی همانرب يزیر دنراد و یم دنناوت هتـسب هب زاین متـسیـس هب ناونع يدورو ای یجورخ دروم هدافتـسا رارق دنریگ . زا قیرط GPIO یم اوت ن تیعـضو تازیهجت فلتخم ار تفایرد ای لانگیس ياه نک ت یلر دروم زاین ار هب تازیهجت یجراخ لاسرا درک .
رادـم عمتجم هـچراـپکی يا هـک شخب ياـه فلتخم دروم زاـین يارب شزادرپ و ،لرتنک زا هـلمج دـحاو ،هدـنزادرپ هـظفاـح و یخرب طبار ياـه یطاـبترا و یبناـج | 1
ار رد کی هشارت بیکرت یم نک د.
هیاپ ياه لباق همانرب يزیر رلرتنکورکیم هک یم دنناوت يارب تفایرد ای لاـسرا لانگیـس ياه لاتیجید هب تازیهجت و رگـسح ياه یجراخ دروم هدافتـسا | 2
رارق نریگ د.

نابم ی رظن ی

-2-3-3 لدبم گولانآ هب لاتیجید ADC

ADC ای Converter Digital-to-Analog یکی زا دحاو ياه مهم 32ESP تـسا هک هفیظو لیدبت لانگیـس | 1
ياه ژاتلو گولانآ هب قم ادیر لاتیجید لباق شزادرپ ت طـسو رلرتنکورکیم ار رب هدهع دراد . يرایـسب زا اهرگـسح یجورخ دوخ ار هب تروـص کی ژاتلو ریغتم دیلوت یم دننک و يارب شزادرپ نیا لانگیـس طـسوت ،رلرتنکورکیم مزلا تسا رادقم نآ طسوت ADC هنومن يرادرب و هب کی رادقم لاتیجید لیدبت دوش . رد هژورپ رـضاح ، یجورخ گولانآ ود رگـسح یلـصا هب ADC لـصتم هدـش تـسا . نیا اهرگـسح لماـش LDR يارب هزادنا يریگ تدــش رون طیحم و -2MQ يارب صیخــشت و هزادنا يریگ یبــسن اهزاگ و دود دنتــسه . ریداقم هدناوخ هدـش زا نیا اهرگـسح سپ زا لیدبت هب هداد ،لاتیجید طـسوت 32ESP شزادرپ هدـش و یم دنناوت يارب اپ شی تیعضو طیحم و يارجا قطنم یلرتنک متسیس دروم هدافتسا رارق دنریگ . ADC دروم هدافتــسا رد 32ESP ياراد حوــضو 12 تیب تــسا . ،نیاربانب رد تلاح هدیا لآ رادقم لاتیجید لـــصاـح زا لـیدـبت کـی يدورو گولاـنآ رد هزاـب 0 اـت 4095 رارق یم دریگ . رد نیا ،تـلاـح رادـقم رفـــص رگناـیب نیرتمک دقم را لباق هزادنا يریگ و 4095 رگنایب نیرتـشیب رادقم رظانتم اب هدودحم هزادنا يریگ ADC تـسا . رادقم یعقاو هدناوخ هدـش یم دناوت تحت ریثات یلماوع دننام هدودحم ژاتلو ،يدورو نویـساربیلاک ADC، زیون و طیارش رادم رارق دریگ .

-2-4 رگسح ياه یطیحم

رگـسح ياه یطیحم یکی زا يازجا یلـصا ـس هناما یحارط هدـش رد نیا هژورپ دنتـسه و هفیظو تفایرد تاعلاطا طوبرم هب طیارــش طیحم فارطا ار رب هدهع دنراد . هداد ياه لــصاح زا نیا اهرگــسح طــسوت رلرتنکورکیم 32ESP تفایرد و شزادرپ هدـش و رد ،همادا يارب شیاپ تیعـضو طیحم و يارجا ياهدرکلمع فلتخم متـسیـس دروم هدافتسا رارق یم دنریگ .

-2-4-1 رگسح -2MQ

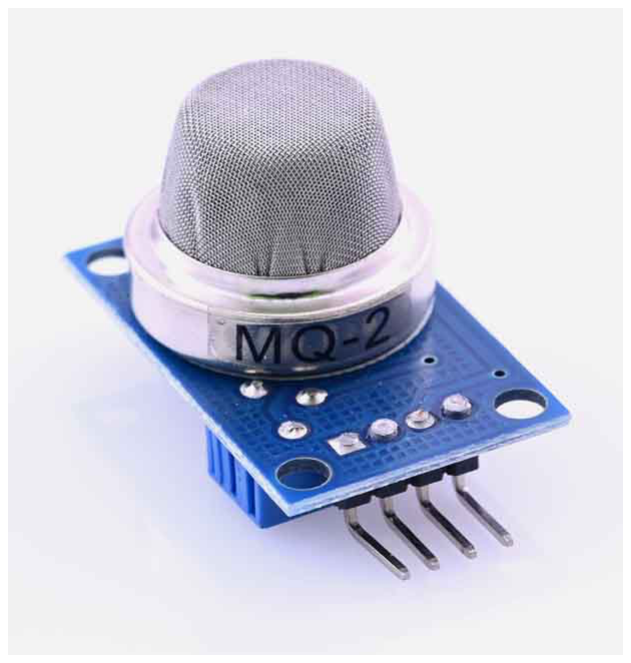
[picture p41: figure]

یلدبم هک لانگیس یکیرتکلا گولانآ ار هب کی رادقم لاتیجید لباق شزادرپ طسوت دحاو هدنزادرپ لیدبت یم دنک . | 1

نابم ی رظن ی
لکش (2-2 ) رگسح -2MQ

-2MQ یکی زا رگـسح ياه يزاگ دربراکرپ زا هداوناخ رگـسح ياه يزاگ یتمواقم تـسا هک هب روظنم صیخـشت دوجو یخرب زاگ ياه لباق لاعتـشا و نینچمه دود رد طیحم دروم هدافتـسا رارق یم دریگ . نیا رگـسح هب لیلد راتخاـس هداـس و هنیزه ًاتبـسن ،نییاپ رد هژورپ ياه ،یـشزومآ هناماـس ياه شیاپ طیحم ی و یخرب دربراک ياه یهاگـشیامزآ دروم هدافتـسا رارق یم دریگ . قباطم تاعلاطا ینف رـشتنم هدـش ، نیا رگـسح يارب صیخـشت يداوم دننام LPG، ،ناتم ،ناپورپ ،ناتوب ،لکلا نژوردیه و دود دربراک دراد [7]. درکلمع -2MQ رب ساـسا رییغت تمواقم یکیرتکلا هدام ساـسح هب زاگ رد رثا رارق نتفرگ رد ضرعم زاگ ياه رظندروم تــسا . اب رییغت تظلغ زاگ رد ،طیحم تمواقم رــصنع ساــسح رییغت هدرک و رد ،هجیتن هــصخــشم یکیرتکلا یجورخ رگسح زین رییغت یم دنک . رد لوژام ياه لوادتم -2MQ ، نیا رییغت یم دناوت هب تروص کی ژاتلو گولانآ رد رایتخا رلرتنکورکیم رارق دریگ . شیپ شیامرگ -2MQ
رگـسح ياه هداوناخ MQ يارب یبایتـسد هب طیارـش يراک ًاتبـسن رادیاپ هب کی هرود مرگ ندـش زاین دنراد . هب نیمه ،لیلد رادقم یجورخ رگـسح هلـصافلاب سپ زا نـشور ندـش یمن دناوت هب ناونع کی رادقم رادیاپ و لباق اکتا يارب میمـصت يریگ رد رظن هتفرگ دوـش . رد نیا هژورپ زین سپ زا نـشور ندـش ،متـسیـس کی هرود شیپ شیامرگ يارب رگـسح -2MQ رد رظن هتفرگ هدـش تـسا ات رـصنع ساـسح رگـسح هب طیارـش يراک بـسانم کیدزن دوش [7].
تیدودحم -2MQ
-2MQ کی رگـسح یمومع يارب صیخـشت دوجو دود و یخرب زاگ ياه لباق لاعتـشا تـسا و رادقم یجورخ نآ هب لماوع یفلتخم زا هلمج عون و تظلغ ،زاگ يامد ،طیحم ،تبوطر تدم نامز شیپ شیامرگ و طیارــش رادم هتـسباو تـسا . ،نیاربانب یجورخ نیا رگـسح ار یمن ناوت نودب نویـساربیلاک و لیلحت بـسانم هب ناونع هزادنا يریگ قیقد تظلغ کی زاگ صاخ رد رظن تفرگ . ،نینچمه -2MQ هب ییاهنت کی هناماـس درادناتـسا صیخـشت و ملاعا قیرح بوـسحم یمن دوـش . رد هژورپ ،رـضاح نیا رگـسح هب ناونع یکی زا عبانم یتاعلاطا يارب شیاپ طیارـش طیحم و صیخـشت هیلوا دود ای دوجو زاگ دروم هدافتـسا رارق رگ هتف تـسا و میمـصت يریگ متـسیـس یم دناوت اب رد رظن نتفرگ ریاس تاعلاطا یطیحم ماجنا دوش .

-2-4-2 رگسح 11DHT

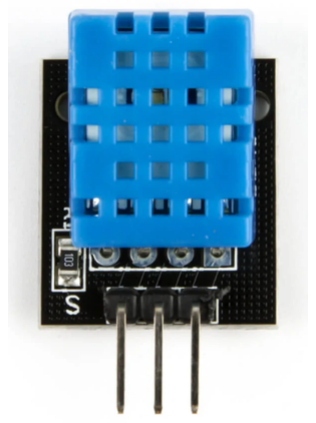
[picture p42: figure]

لکش (2-3 ) رگسح 11DHT

نابم ی رظن ی

11DHT کی رگـسح لاتیجید يارب هزادنا يریگ مه نامز امد و تبوطر یبـسن تـسا . رب فلاخ رگـسح ییاه هک یجورخ اهنآ هب تروـص گولانآ هئارا یم ،دوـش 11DHT هداد ياه هزادنا يریگ هدـش ار هب تروـص لاتیجید و زا قیرط کی طبار یطابترا صخــشم هب رلرتنکورکیم لقتنم یم دنک . هدافتــسا زا 11DHT رد نیا هژورپ ناکما شیاپ ود رتماراپ مهم یطیحم امد و تبوطر ار مهارف یم دنک . طاـبترا 11DHT اـب رلرتنکورکیم زا قیرط کـی طخ هداد و رب ساـــسا کـی لـکتورپ يدـنبناـمز هدـــش ماـجنا یم دوش . رد نیا ،دنیارف رلرتنکورکیم تساوخرد تفایرد تاعلاطا ار هب رگسح لاسرا هدرک و سپس 11DHT هداد ياـه طوبرم هـب اـمد و تـبوطر ار زا قیرط طخ یطاـبترا هـب رلرتنکورکیم لـقتنم یم دـنک . رد نیا هژورپ يارب هداـس يزاـس دنیارف طابترا و تفایرد هداد اه زا 11DHT، زا هناخباتک DHT Adafruit هدافتـسا هدـش تـسا . نیا هناخباتک ناکما داجیا یـش DHT و ندناوخ میقتـسم امد و تبوطر ار مهارف یم دنک . تادنتـسم یمـسر نیا هناخباتک یعباوت دننام ()readTemperature و ()readHumidity ار هئارا یم دهد [8].

-2-4-3 رگسح تدش رون LDR

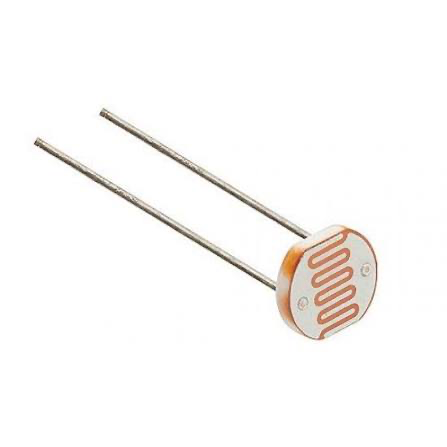
[picture p43: figure]

لکش (2-4 ) رگسح تدش رون

LDR ای Resistor Dependant Light کی تمواقم هتــسباو هب رون تــسا هک رادقم تمواقم یکیرتکلا نآ اب نازیم رون یتفایرد رییغت یم دنک . نیا یگژیو ثعاب یم دوـش ناوتب زا LDR هب ناونع کی رـصنع هداـس يارب صیخـشت و شیاپ تدـش رون طیحم هدافتـسا درک . زا اجنآ هک رلرتنکورکیم 32ESP يارب تفایرد نیا تاعلاطا دنمزاین کی لانگیـس لباق هزادنا يریگ ،تـسا LDR لاومعم رد رانک کی تمواقم رگید هب تروـص رادم میـسقت ژاتلو رق را یم دریگ . رد نیا ،راتخاـس رییغت تمواقم LDR ثعاب رییغت ژاتلو یجورخ رادم هدـش و نیا ژاتلو یم دناوت طسوت ADC رلرتنکورکیم هزادنا يریگ دوش .

نابم ی رظن ی

-2-4-4 رگسح صیخشت تکرح PIR

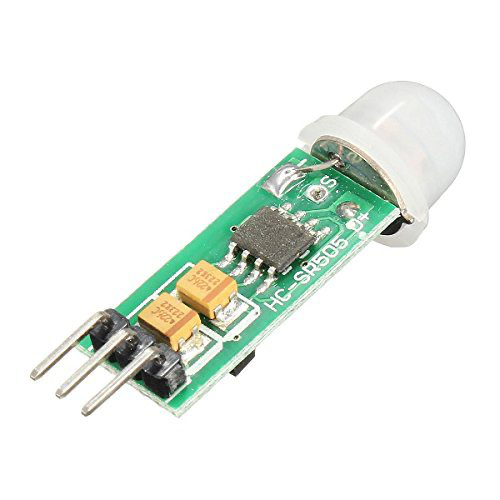
[picture p44: figure]

لکش (2-5 ) رگسح صیخشت تکرح PIR

رگـسح PIR ای Sensor Infrared Passive یکی زا رگـسح ياه جیار يارب صیخـشت تکرح ماـسجا ،مرگ هب هژیو ،ناـسنا رد طیحم تـسا . نیا رگسح اب هدافتسا زا تارییغت شبات نودام زمرق دوجوم رد هدودحم دید ،دوخ تکرح ار صیخــشت یم دهد . مامت ماــسجا ياراد يامد رتلااب زا رفــص ،قلطم بــسانتم اب يامد دوخ شبات یـسیطانغمورتکلا رـشتنم یم دننک هک شخب لباق یهجوت زا نآ رد هدودحم نودام زمرق رارق دراد . ندب ناـسنا زین هب لیلد نتـشاد يامد رتلااب زا ،طیحم شبات نودام زمرق رـشتنم یم دنک . یماگنه هک کی مـسج مرگ رد هدودحم صیخـشت رگـسح تکرح یم ،دنک يوگلا شبات نودام زمرق تفایرد هدـش طـسوت رگـسح رییغت هدرک و نیا رییغت طـسوت رادم PIR صیخـشت داد ه یم دوـش . یجورخ لوژام ياه PIR لاومعم هب تروـص کی لانگیـس لاتیجید هئارا یم دوـش . ،نیاربانب رد تروـص صیخـشت ،تکرح تیعـضو یجورخ رییغت هدرک و رلرتنکورکیم یم دناوت نیا رییغت تیعضو ار زا قیرط یکی زا هیاپ ياه GPIO صیخشت دهد .

-2-5 رزاب

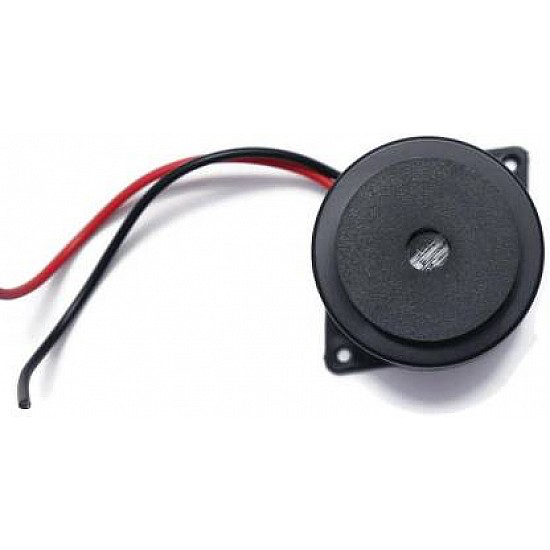
[picture p45: figure]

لکش (2-6 ) رزاب

رزاب کی لدبم یکیرتکلا هب یتوـص ـسا ت هک اب تفایرد کی لانگیـس یکیرتکلا بـسانم ، يژرنا یکیرتکلا ار هب تاعاـشترا یکیناکم و رد تیاهن توـص لیدبت یم دنک . زا رزاب اه هب لیلد راتخاـس هداـس و تیلباق دیلوت يادـص

نابم ی رظن ی

،رادشه رد هناماس ياه ،یکینورتکلا تازیهجت ملاعا تیعضو و متسیس ياه رادشه هدافتسا یم دوش . رد هژورپ ح ،رـضا رزاب هب یکی زا هیاپ ياه GPIO رلرتنکورکیم لـصتم هدـش و يارب داجیا رادـشه یتوـص دروم هدافتـسا رارق هتفرگ تسا .

-2-6 طابترا نودام زمرق

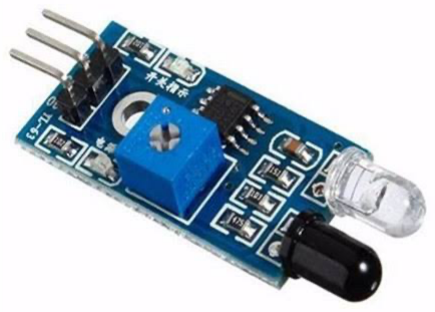
[picture p46: figure]

لکش (2-7 ) هدنریگ و هدنتسرف نودام زمرق

Infrared یـشخب زا فیط جاوما یـسیطانغمورتکلا تـسا هک لوط جوم نآ رتـشیب زا رون زمرق | 1 | نودام زمرق ای
یئرم تـــسا . نیا هیحان زا فیط یـــسیطانغمورتکلا رد يرایـــسب زا دربراک ياه یکینورتکلا و یطابترا دروم هدافتـسا رارق یم دریگ . یکی زا دربراک ياه جیار نودام ،زمرق هدافتـسا رد متـسیـس ياه لرتنک زا هار رود تـسا هک رد نآ لاطا تاع و نامرف ياه لاتیجید اب تارییغت ینامز تدـش شبات نودام زمرق لقتنم یم دنوـش . لرتنک زا هار رود يرایــسب زا تازیهجت ،یگناخ زا هلمج ،نویزیولت متــسیــس ياه هیوهت ،عوبطم شخپ هدننک ياه یتوص و يریوصت و ریاس تازیهجت ،یکینورتکلا رب هیاپ طابترا نودام زمرق ماجنا یم دوش . یگ هدـنر IR هـفیظو تـفاـیرد شباـت نوداـم زمرق لاـــسرا هدـــش زا لرتنک هدـننک و لـیدـبت نآ هـب کـی لاـنگیـــس یکیرتکلا لباق شزادرپ طـسوت رلرتنکورکیم ار رب هدهع دراد . هدنریگ اب صیخـشت تارییغت تدـش شبات و نامز يدنب سلاپ ياه ،یتفایرد يوگلا لانگیــس ار رد رایتخا رلرتنکورکیم رارق یم دهد . در ،لباقم هدنتــسرف IR هفیظو لیدبت لانگیـس یکیرتکلا دیلوت هدـش طـسوت رلرتنکورکیم هب شبات نودام زمرق و لاـسرا نآ هب تمـس هاگتسد دصقم ار رب هدهع دراد . لرتنک ياـه زا هار رود تازیهجت فلتخم زا لـکتورپ ياـه یطاـبترا یتواـفتم يارب يراذـگدـک و لاـقتنا ناـمرف اـه هدافتسا یم دننک . ره ،لکتورپ راتخاس و هوحن نامز يدنب یصاخ يارب شیامن تاعلاطا دراد . زا هلمج لکتورپ ياه جیار دروم هدافتـسا رد تازیهجت یکینورتکلا یم ناوت هب NEC، Sony، Samsung و Panasonic هراـشا درک . تواـفت ناـیم نیا لـکتورپ اـه رد هوحن يراذـگدـک هداد ،اـه راـتخاـــس ،میرف ناـمز يدـنب سلاـپ اـه و ریاـــس تاصخشم لانگیس تسا .
رد نیا هژورپ يارب هداـیپ يزاـــس تـیلباـق تـفاـیرد و لاـــسرا لاـنگیـــس ياـه نوداـم زمرق زا هـناـخباـتک 8266IRremoteESP هدافتــسا هدــش تــسا . نیا هناخباتک کی هژورپ نتم زاب يارب مرفتلپ ياه 8266ESP و 32ESP تـسا هک تاناکما مزلا يارب ،تفایرد شزادرپ و لاـسرا یـس لانگ ياه نودام زمرق ار مهارف یم دنک .

1
یعون شبات یـسیطانغمورتکلا رد هدودحم خرـسورف تـسا هک رد هناماـس ياه لرتنک زا هار رود يارب لاـسرا و تفایرد نامرف اه دروم هدافتـسا رارق یم دریگ .

نابم ی رظن ی

هـناـخباـتک 8266IRremoteESP زا فیط هدرتـــسگ يا زا لـکتورپ ياـه جیار لرتنک زا هار رود و عاونا فلتخم هدنریگ اه و هدنتــسرف ياه نودام زمرق ینابیتــشپ یم دنک [6] . هب نیا ،بیترت شخب نودام زمرق متــسیــس هولاع رب ناـکما تـفاـیرد ناـمرف ياـه لرتنک زا هار ،رود تـیلباـق هریخذ و شخپزاـب ناـمرف ياـه IR ار زین مهارف یم دنک . نیا تیلباق یکی زا شخب ياه یلـصا درکلمع یلرتنک هاگتـسد هدوب و ناکما هدافتـسا زا 32ESP هب ناونع یطساو يارب لرتنک تازیهجت یکینورتکلا زهجم هب هدنریگ نودام زمرق ار مهارف یم دزاس .

-2-7 را طابت ییویدار RF

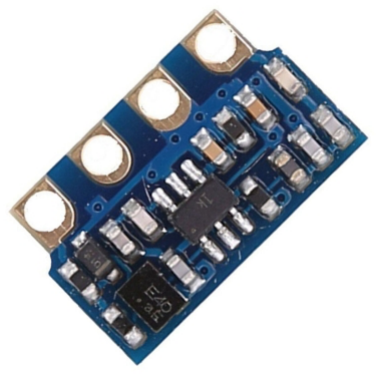
[picture p47: figure]

لکش (2-8 ) هدنریگ ییویدار

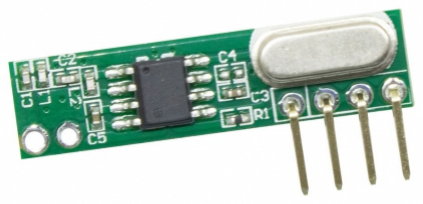
[picture p48: figure]

لکش (2-9 ) هدنتسرف ییویدار

سناکرف ییویدار ¹ ای Frequency Radio هب یــشخب زا فیط جاوما یــسیطانغمورتکلا هتفگ یم دوــش هک یم ناوت زا نآ يارب لاقتنا تاعلاطا هب تروـص یب میـس هدافتـسا درک . تاطابترا RF رد يرایـسب زا هناماـس ياه یکینورتکلا و تازیهجت لرتنک زا هار رود دروم هدافتـسا رارق یم دنریگ و ناکما لاقتنا هداد نودب زاین هب لاـصتا کیزیف ی نایم هدنتـسرف و هدنریگ ار مهارف یم دنک . کی متـسیـس ییویدار هداـس یم دناوت زا ود شخب ،یلـصا ینعی هدنتسرف و هدنریگ لیکشت دوش . هدنتسرف هفیظو لیدبت تاعلاطا ای دک یلرتنک هب کی لانگیس ییویدار و لاــسرا نآ ار رب هدهع دراد . رد فرط ،لباقم هدنریگ لانگیــس ياه ییویدار ار رد تفای هدرک و نآ ار هب کی

هب هدودحم يا زا جاوما یسیطانغمورتکلا هتفگ یم دوش هک يارب لاقتنا تاعلاطا هب تروص یب میس دروم هدافتسا رارق یم دنریگ . | 1

نابم ی رظن ی

لانگیـس یکیرتکلا لباق شزادرپ لیدبت یم دنک . رد تازیهجت لرتنک زا هار رود ،جیار دناب ياه یـسناکرف 315 و 433 زترهاگم زا هلمج سناکرف ياه دروم هدافتسا دنتسه . هـناـخباـتک RCSwitch یکی زا هـناـخباـتک ياـه رپ دربراـک يارب راـک اـب یخرب تازیهجت RF هداـــس در دـناـب ياـه یـسناکرف 315 و 433 زترهاگم تـسا . نیا هناخباتک تاناکما مزلا يارب تفایرد و لاـسرا دک ياه ییویدار دروم هدافتـسا رد يرایـسب زا لرتنک ياه زا هار رود هداـس ار مهارف یم دنک [5] . اب هدافتـسا زا RCSwitch، یم ناوت لانگیــس ياه یتفایرد زا هدنریگ RF ار طــسوت رلرتنکورکیم تفایرد و دک طوبرم هب نآ ار جارختــسا درک . سپـس رد تروـص ،زاین نامه دک یم دناوت زا قیرط لوژام هدنتـسرف RF اددجم لاـسرا دوـش . نیا تیلباق ناکما هدایپ يزاس درکلمع ،تفایرد هریخذ و شخپزاب دک ياه RF ار رد متسیس مهارف یم دنک .

-2-8 طابترا WiFi

WiFi کی يروانف طابترا ی یب میـس ینتبم رب هعومجم درادناتـسا ياه 802.11 IEEE تـسا هک ناکما يرارقرب طابترا و لدابت هداد نایم تازیهجت فلتخم ار زا قیرط هکبــش یب میــس مهارف یم دنک . نیا يروانف هب لیلد تلوهـس ،هدافتـسا شـشوپ بـسانم و ینابیتـشپ هدرتـسگ رد تازیهجت ،یکینورتکلا یکی زا شور ياه لوادتم يارب لاـصتا تازیهجت دنمـشوه و هناماـس ياه تنرتنیا ایـشا هب هکبـش بوـسحم یم دوـش . رلرتنکورکیم 32ESP هب تروـص یلخاد زا تیلباق WiFi ینابیتـشپ یم دنک و ناکما رب يرارق طابترا اب هکبـش ياه یب میـس ینتبم رب درادناتـسا ياه n/g/b802.11 ار مهارف یم دزاـس [3]. دوجو نیا تیلباق یلخاد ثعاب یم دوـش 32ESP نودب زاین هب هدافتـسا زا کی لوژام یطابترا یجراخ دناوتب هب هکبـش لـصتم هدـش و هداد ياه زایندروم ار لاـسرا ای تفایرد دنک .
32ESP یم دناوت رد دنچ تلاح فلتخم يارب يرارقرب طابترا WiFi دروم هدافتــسا رارق دریگ . یکی زا تلاح ياه ،یلـصا Station ای STA ا تـس . رد نیا ،تلاح 32ESP دننامه کی Client هب کی Point Access ،دوجوم دننام رتور ای ،مدوم لــصتم یم دوــش . سپ زا يرارقرب ،لاــصتا 32ESP یم دناوت زا قیرط هکبــش هب ریاــس تازیهجت و سیورـس ياه دوجوم یـسرتـسد هتـشاد دـشاب [9]. تلاح ،رگید Point Access ای AP تـسا . رد نیا ،تلاح دوخ 32ESP شقن هطقن یـسرتـسد یب میـس ار رب هدهع هتفرگ و کی هکبـش WiFi داجیا یم دنک . ریاـس تازیهجت یم دنناوت ًامیقتـسم هب هکبـش اجیا د هدـش طـسوت 32ESP لـصتم دنوـش . نیا تلاح هب هژیو رد یطیارـش هک هاگتـسد زونه هب هکبـش یلـصا یـسرتـسد درادن ای زاین هب ماجنا تامیظنت هیلوا دوجو ،دراد دربراک دراد [9]. نینچمه 32ESP زا تلاح STA+AP ینابیتـشپ یم دنک . رد نیا ،تلاح 32ESP هب تروـص نامزمه زا قیرط طبار STA هب هکبــش یلــصا لــصتم هدــش و رد شقن Point Access زین کی هکبــش WiFi داجیا یم دنک . ،نیاربانب ریاـس تازیهجت یم دنناوت هب هکبـش داجیا هدـش طـسوت 32ESP لـصتم وـش ،دن رد یلاح هک دوخ 32ESP نانچمه طابترا دوخ ار اب هکبـش یلـصا ظفح هدرک تـسا [9] . نیا تیلباق رد رف ا دنی يدنبرکیپ هیلوا هاگتسد یم دناوت دربراک هژیو يا هتشاد دشاب .

نابم ی رظن ی
Captive Portal -2-8-1
Portal Captive یـشور يارب هئارا کی هحفـص بو ای طبار تامیظنت هب ربراک سپ زا لاـصتا هب کی هکبـش | 1
تـسا . رد نیا ،شور هاگتـسد ربراک سپ زا لاـصتا هب هکبـش یب ،میـس هب ياج یـسرتـسد میقتـسم هب دـصقم ،رظندروم هب هحفـص يا تیاده یم دوـش هک یم دناوت يارب ماجنا تامیظنت ای دورو تاعلاطا دروم هدافتـسا رارق گ دری . رد هژورپ ،رـضاح زا Portal Captive هب روظنم يدنبرکیپ هیلوا هاگتـسد هدافتـسا هدـش تـسا . یماگنه هک 32ESP يارب نیتــسخن راب هار يزادنا یم دوــش ای تاعلاطا هکبــش دروم زاین ار رد رایتخا ،درادن یم دناوت رد تلاح Point Access کی هکبــش یب میــس داجیا دنک . ربراک اب لاــصتا فلت ن هارمه ای هنایار هب نیا ،هکبــش هب هحفـص تامیظنت هاگتـسد یـسرتـسد ادیپ هدرک و تاعلاطا دروم ،زاین دننام تاـصخـشم هکبـش WiFi و ریاـس تامیظنت ،یطابترا ار دراو یم دنک .

-2-9 لکتورپ MQTT

ای Transport Telemetry Queuing Message کی لکتورپ مایپ یناـسر کبـس و مک مجح تـسا | 2MQTT
هک رب ا ساـس يرامعم Server/Client و يوگلا یطابترا Subscribe/Publish یحارط هدـش تـسا . نیا لکتورپ هب روط هژیو يارب هناماـس ياه تنرتنیا ،ایـشا تازیهجت ياراد عبانم یـشزادرپ و هظفاح دودحم و هکبـش ییاه اب يانهپ دناب دودحم دروم هدافتـسا رارق یم دریگ . درادناتسا MQTT هخسن 5.0 طسوت نامزاس OASIS رشتنم هدـش تـسا [4]. یکی زا مهم نیرت یگژیو ياه MQTT، رابرـس مک و یگداـس راتخاـس مایپ اه تـسا . نیا یگژیو ثعاب یم دوـش نیا لکتورپ يارب طابترا نایم رلرتنکورکیم ،اه اهرگـسح و ریاـس تازیهجت دنمـشوه بـسانم دشاب . نینچمه MQTT با هدافتسا زا يرامعم Subscribe/Publish، هدنتسرف و هدنریگ مایپ ار زا رگیدکی ادج یم دنک و تیریدم طابترا نایم اهنآ ار هب کی هفلوم يزکرم هب مان Broker راذگاو یم دنک .

-2-9-1 MQTT Broker³

Broker هتــسه يزکرم طابترا رد يرامعم MQTT تــسا و هفیظو ،تفایرد تیریدم و لاــسرا مایپ اه ار رب هدهع دراد . یماگنه هک کی Client یمایپ ار رد کی Topic رـشتنم یم ،دنک Broker مایپ ار تفایرد هدرک و نآ ار يارب Client ییاه هک نآ Topic ار Subscribe درک ه دنا لاـسرا یم دنک . Client يا هک کی مایپ ار رد کی Topic رــشتنم یم ،دنک Publisher هدیمان یم دوــش . رد ،لباقم Client يا هک يارب تفایرد مایپ ياه طوبرم هـب کـی Topic تـبث ماـن یم ،دـنک Subscriber ماـن دراد . ،نیارباـنب کـی Client یم دـناوت ناـمزمه شقن Publisher و Subscriber ار هتـشاد دـشاب . Topic کی ریـسم یقطنم يارب هتـسد يدنب و ییاـسانـش مایپ ياه

هحفـص يا بو تـسا هک سپ زا لاـصتا ربراک هب کی ،هکبـش يارب ماجنا تامیظنت ای هئارا تاعلاطا زایندروم شیپ زا یـسرتـسد يداع هب هکبـش شیامن هداد | 1
یم دوش .
کی لکتورپ یطابترا کبـس ینتبم رب يوگلا راـشتنا / كارتـشا تـسا هک يارب لدابت مایپ نایم تازیهجت و هناماـس ياه ،لـصتم هب هژیو رد طیحم ياه | 2
تنرتنیا ،ایشا دافتسا ه یم دوش .
مرن يرازفا هک هفیظو ،تفایرد تیریدم و عیزوت مایپ ياه MQTT ار نایم Client ياه هدننکرشتنم و كرتشم رب هدهع دراد . | 3

نابم ی رظن ی

MQTT تـسا . ره مایپ رد کی Topic صخـشم رـشتنم یم دوـش و Subscriber اه اب Subscribe ندرک هب Topic ،رظندروم مایپ ياه طوبرم هب نآ ار تفایرد یم دننک . Topic اه ًلاومعم هب تروــص هلــسلــس یبتارم فیرعت یم دنوش ات هتسد يدنب و تیریدم مایپ اه هداس رت دوش . راتخاس یلک Topic اه هب تروص یز ر تسا : < topic > / < subtopic > / < subtopic >

Payload شخب یلـصا ياوتحم مایپ MQTT تـسا هک هداد رظندروم ار رد دوخ يرادهگن یم دنک . درادناتـسا | 1
MQTT بلاق یـصخـشم يارب ياوتحم Payload نییعت یمن دنک و باختنا بلاق هداد هب حارط متـسیـس راذگاو هدـش تـسا . ،نیاربانب Payload یم دناوت هب تروـص نتم ،هداـس JSON ای ریاـس بلاق ياه بـسانم يارب دربراک رظندروم لاسرا دوش [4].

-2-9-2 تیفیک سیورس

یکی زا تیلباق ياه مهم MQTT، ینابیتــشپ زا حوطــس فلتخم (QoS (Service of Quality تــسا . QoS صخـشم یم دنک هک مایپ اه اب هچ یحطـس زا نیمـضت لیوحت نایم Client و Broker لقتنم دنوـش . MQTT هس حطس QoS ار فیرعت یم دنک [4]: :(At Most One) راب کی رثکادح -QoS 0 رد نیا ،حطـس مایپ طقف رابکی لاـسرا یم دوـش و چیه ینیمـضت يارب لیوحت قفوم مایپ دوجو درادن . رد ،هجیتن رد تروـص زورب اطخ ای عطق ،طابترا نکمم تـسا مایپ هب دـصقم دـسرن . نیا حطـس نیرتمک رابرـس یطابترا ار دراد و يارب هداد ییاه هک زا تسد نتفر یخرب هنومن ياه اهنآ تیمها يدایز ،درادن بسانم تسا .

### 1 QoS- لقادح کی ب را (Once Least At(:

رد نیا ،حطـس لیوحت مایپ هب دـصقم نیمـضت یم ،دوـش اما رد یخرب طیارـش نکمم تـسا کی مایپ شیب زا کی راب تفایرد دوش . ،نیاربانب هدنریگ دیاب رد تروص زاین ناکما تیریدم مایپ ياه يرارکت ار هتشاد دشاب .

### 2 QoS- اقیقد کی راب (Once Exactly(:

رد نیا ،حطـس ورپ لکت يراکوزاـس يارب نانیمطا زا لیوحت مایپ هب تروـص اقیقد کی راب رد رظن یم دریگ . نیا حطس نیرتشیب نازیم نانیمطا و رد هجیتن رابرس و یگدیچیپ يرتشیب تبسن هب ود حطس رگید دراد .

-2-9-3 طابترا MQTT زا قیرط WebSocket

گرورم ر ياه بو هب تروـص لومعم يارب يرارقرب طابترا میقتـسم اب Broker MQTT زا قیرط لاـصتا TCP ماـخ یحارط هدـــشن دـنا . هـب نیمه ،لـیلد يارب داـجیا طاـبترا ناـیم کـی هـماـنرب تـحت بو و Broker MQTT 2WebSocket ًلاومعم زا
هداـفتـــسا یم دوـــش . WebSocket کـی طاـبترا ود هـفرط و رادـیاـپ ناـیم Browser و
شخب یلـصا و ياوتحم هداد کی مایپ تـسا هک تاعلاطا رظندروم يارب لاقتنا ار رد دوخ ياج یم ؛دهد رد MQTT، Payload یم دناوت لماـش هداد ياه | 1
،ینتم يددع ای راتخاس هتفای دشاب .
کـی لـکتورپ یطاـبترا تـــسا هـک ناـکما داـجیا کـی طاـبترا رادـیاـپ و ود هـیوـــس ناـیم Client و Server ار مهارف یم دـنک و يارب لداـبت هداد ياـه ردلاب گـن | 2
بسانم تسا .

نابم ی رظن ی

Server داجیا یم دنک و ناکما لاـــسرا و یرد تفا هداد ار نودب زاین هب داجیا کی لاـــصتا دیدج يارب ره مایپ مهارف یم دزاس .
رد نیا ،شور رگرورم زا قیرط WebSocket هب یـسیورـس لـصتم یم دوـش هک ناکما طابترا MQTT يور WebSocket ار مهارف هدرک تـــسا . سپ زا يرارقرب ،لاـــصتا همانرب تحت بو یم دناوت دننامه کی Client MQTT رد Topic ياه رظندروم Subscribe هدرک ای مایپ ییاه ار رد Topic ياه صخشم رشتنم دنک .

-2-10 هریخذ يزاس تاعلاطا رد 32ESP

32ESP ياراد هظفاح Flash يارب يرادهگن Firmware و هداد ياه یمئاد تسا . زا نیا هظفاح یم ناوت يارب
LittleFS کی لیاف متــسیــس بــسانم يارب | 1 | یتاعلاطا هدافتــسا درک هک دیاب دعب زا restart زین یقاب دنامب .
هظفاح Flash متـسیـس ياه هتفهن تـسا . رد 32ESP-Arduino، LittleFS هب ناونع یکی زا لیاف متـسیـس ياه لباق هدافتسا رد 32ESP یفرعم هدش تسا [10]
کی لیاف متـسیـس کبـس يارب هظفاح شلف تـسا هک ناکما هریخذ و یبایزاب لیاف اه و هداد ياه رادیاپ ار رد هناماـس ياه ینتبم رب رلرتنکورکیم مهارف | 1
یم دنک .

# لصف 3 :

# لیلحت و یحارط متسیس

لحت یل حارط و ی سی متس

رد نیا ،لصف دنیارف لیلحت و یحارط هناماس دنمشوه شیاپ طیحم و لرتنک تاریهجت ینتبم رب تنرتنیا ایشا هئارا یم دوـش . فده زا یحارط نیا ،هناماـس داجیا کی باه دنمـشوه ینتبم رب رلرتنکورکیم 32ESP تـسا هک دناوتب نمـض تفایرد و شزادرپ تاعلاطا ،یطیحم ناکما لاـسرا هداد اه زا یرط ق هکبـش یب ،میـس داجیا رادـشه رد طیارــش صخــشم و نینچمه تفایرد و شخپزاب لانگیــس ياه یلرتنک نودام زمرق و سناکرف ییویدار ار مهارف دنک .
هناماـس یحارط هدـش زا هعومجم يا زا رگـسح ياه یطیحم لماـش رگـسح امد و تبوطر 11DHT، رگـسح دود و زاگ -2MQ، رگسح رون ینتبم رب LDR و رگسح خشت صی تکرح PIR لیکشت هدش تسا . هداد ياه لصاح زا نیا رگـسح اه طـسوت 32ESP تفایرد و شزادرپ هدـش و رد هزاب ياه ینامز صخـشم زا قیرط هکبـش WiFi هب Broker MQTT لاسرا یم دنوش . هولاع رب تیلباق شیاپ ،طیحم هناماس ياراد متسیسریز یطابترا RF رد ود دناب یسناکرف 315 و 433 زترهاگم و کی متـسیـسریز طابترا نودام زمرق تـسا . نیا متـسیـسریز اه ناکما ،تفایرد هریخذ يزاـس و شخپزاب یخرب لانگیـس ياه یلرتنک تازیهجت فلتخم ار مهارف یم دننک . هب نیا ،بیترت 32ESP هب ناونع کی طـساو نایم تازیهجت ،یکیزیف هکبش و طبار يربراک لمع یم دنک .

-3-1 لیلحت يدنمزاین ياه متسیس

اب هجوت هب فادها هژورپ و تیلباق ياه دروم راظتنا زا ،هناماــس يدنمزاین ياه متــسیــس هب ود هورگ یلــصا يدنمزاین ياه يدرکلمع و يدنمزاین ياه يدرکلمعریغ میــسقت یم دنوــش . يدنمزاین ياه يدرکلمع ایب ن هدننک فیاظو و تیلباق ییاه دنتـسه هک هناماـس دیاب هئارا دهد و يدنمزاین ياه يدرکلمعریغ زین یگژیو ياه یفیک و تامازلا طوبرم هب هوحن ،درکلمع ،هعـسوت يرادهگن و يرادیاپ متـسیـس ار صخـشم یم دننک . رد یحارط هناماـس ،رـضاح فده یلـصا داجیا کی هاگتـسد دنمـشوه يارب شیاپ طیارـش ،یطیحم صیخـشت تیعـضو ياه ،يداعریغ داجیا رادــشه و مهارف ندرک ناکما لرتنک تازیهجت یکینورتکلا زا قیرط هکبــش ؛تــسا ،نیاربانب هعومجم يدنمزاین ياه فیرعت هدـش دیاب هولاع رب شـشوپ درکلمع ياه یلـصا ،هاگتـسد ناکما طابترا نایم شخب تخــس ،يرازفا مرن رازفا Firmware، رورــس ای Broker MQTT و طبار يربراک تحت بو ار زین مهارف دنک .
زا رظن يدنمزاین ه يا يدرکلمع ، هناماـس دیاب رداق دـشاب تاعلاطا یطیحم فلتخم ار طـسوت ياهرگـسح لـصتم هب 32ESP تفایرد و شزادرپ ؛دنک هب نیا تروـص هک يامد طیحم و تبوطر یبـسن طـسوت رگـسح 11DHT ، تدـش رون طـسوت LDR، تارییغت یـشان زا دوجو دود ای یخرب اهزاگ طـسوت -2MQ و تکرح رد طیحم طـسوت رگـسح PIR ییاـسانـش و هزادنا يریگ دنوـش . تاعلاطا تفایرد هدـش زا اهرگـسح دیاب طـسوت رلرتنکورکیم شزادرپ هدـش و رد تروـص روبع رتماراپ ياه ،صخـشم هب هژیو رادقم طوبرم هب دود ای ،زاگ زا هناتـسآ نییعت ،هدـش متـسیـس دناوتب تیعـضو رادـشه ار لاعف هدرک و اب هدافتـسا زا رزاب رادـشه یتوـص داجیا ک دن . نینچمه هناماـس دیاب ناکما لاقتنا تاعلاطا اهرگـسح و تیعـضو یلعف هاگتـسد ار زا قیرط هکبـش WiFi مهارف هدرک و دناوتب اب یک Broker MQTT طابترا رارقرب ؛دنک هب هنوگ يا هک هداد ياه طوبرم هب اهرگـــسح و تیعـــضو متـسیـس رد Topic ياه صخـشم رـشتنم هدـش و نامرف ياه یتفایرد زا یرط ق MQTT زین طـسوت 32ESP ،تفایرد شزادرپ و ارجا دنوش . یکی رگید زا يدنمزاین ياه یلـصا ،هناماـس مهارف ندرک ناکما لرتنک تازیهجت یکینورتکلا زا قیرط لانگیـس ياه RF و IR تـسا . رد نیا ،اتـسار متـسیـس دیاب تیلباق تفایرد لانگیـس ياه RF رد ود دناب یـسناکرف 315 و 433 زترهاگم و مه نینچ تفایرد لانگیس ياه نودام زمرق ار هتشاد دشاب و دناوتب لانگیس ياه تفایرد هدش

لحت یل حارط و ی سی متس

ار رد هظفاح هریخذ دنک ات رد نامز رظندروم اددجم زا قیرط هدنتـسرف هطوبرم لاـسرا دنوـش . ،نیاربانب هناماـس دیاب هولاع رب تفایرد ،لانگیـس تیلباق هریخذ يزاـس و شخپزاب لانگیـس ياه RF و IR ار زین هتـشاد دـشاب و تاعلاطا ریخذ ه هدـش دیاب سپ زا شوماخ و نـشور ندـش هاگتـسد نانچمه لباق یـسرتـسد دنـشاب . نینچمه يارب يریگولج زا یگتـسباو تامیظنت هاگتـسد هب دک Firmware هناماـس، دیاب ناکما میظنت تاعلاطا هکبـش WiFiو اصخشم ت MQTT ار نودب زاین هب رییغت و لیاپماک ددجم همانرب مهارف ؛دنک هب نیمه ،روظنم دنیآرف يدنبرکیپ هیلوا زا قیرط کی لاتروپ تامیظنت ماجنا هدش و ربراک یم دناوت تاعلاطا زایندروم ار زا قیرط طبار هئارا هدش دراو ای رییغت دهد . رد رانک ياهدرکلمع ،یلحم هناماــس دیاب کی طبار يربراک تحت بو زین رد رایتخا ربراک رارق هد د ات تاعلاطا تفایرد هدـش زا اهرگـسح و تیعـضو یلک متـسیـس رد نآ شیامن هداد دوـش و ربراک دناوتب نامرف ياه یلرتنک رظندروم دوخ ار لاـسرا دنک . طابترا نایم دروبـشاد تحت بو و شخب یطابترا متـسیـس رب هیاپ MQTT ماجنا هدــش و يارب مهارف ندرک ناکما طابترا MQTT رد طیحم رگرورم زا WebSocket هدافتــسا یم ؛دوــش رد ،هجیتن تاعلاطا اهرگــسح یم دنناوت رد دروبــشاد شیامن هداد هدــش و نامرف ياه ربراک زین زا قیرط نیمه ریـسم هب هاگتـسد لقتنم دنوـش . نیا راتخاـس ثعاب یم دوـش ربراک دناوتب نودب زاین هب یـسرتـسد میقتـسم هب تخس ،رازفا تیعضو طیحم ار هدهاشم هدرک و هجت تازی لصتم هب هناماس ار لرتنک دنک . زا رظن يدنمزاین ياه يدرکلمعریغ ، راتخاــس متــسیــس دیاب هب هنوگ يا یحارط دوــش هک ناکما هعــسوت و يرادهگن نآ رد هدنیآ دوجو هتـشاد دـشاب . هب نیمه ،روظنم Firmware هناماـس هب تروـص رلاوژام یحارط هدـش و شخب ییاه دننام تیریدم ،اهرگــسح طابترا MQTT، طابترا RF، طابترا IR، تیریدم رادــشه و تیریدم هظفاح زا رگیدکی کیکفت هدـش دنا ات هفاـضا ندرک تیلباق ياه دیدج ای حلاـصا کی ،شخب لقادح ریثأت ار رب ریاـس تمـسق ياه متـسیـس هتـشاد دـشاب . نینچمه تاعلاطا طوبرم هب هکبـش و لانگیـس ياه هریخذ هدـش دیابن اب شوماخ ندــش هاگتــسد زا نیب ؛دنورب نیاربانب زا متــسیــس لیاف LittleFS يارب هریخذ يزاــس رادیاپ نیا تاعلاطا هدافتـسا هدـش تـسا . یکی رگید زا تامازلا ،مهم يرادیاپ درکلمع یلحم متـسیـس ؛تـسا هب نیا انعم هک عطق طاـبترا اـب Broker MQTT اـی زورب للاتخا رد هـکبـــش دـیاـبن ثـعاـب فقوت درکلمع ییاـه دـنناـم ندـناوخ ،اهرگسح صیخشت تکرح ای لاعف يزاس متسیس رادشه دوش و شخب ياه یلصا هاگتسد دیاب دنناوتب لقتسم زا تیعضو طابترا هکبش هب درکلمع دوخ همادا دنهد . رد ،تیاهن هعومجم نیا يدنمزاین اه صخـشم یم دنک هک هناماـس یحارط هدـش اهنت کی هاگتـسد هزادنا يریگ هداـس ،تـسین هکلب کی یـس متـس دنمـشوه هچراپکی تـسا هک فیاظو شیاپ ،طیحم صیخـشت طیارـش ،يداعریغ داجیا ،رادـشه طابترا هکبـش ،يا تفایرد و شخپزاب لانگیـس ياه RF و IR، هریخذ يزاـس تاعلاطا و لرتنک تازیهجت زا قیرط طبار يربراـک تـحت بو ار رب هدـهع دراد . ،نیارباـنب يدـنمزاـین ياـه نییعت هدـــش هـب ناونع ییانبم يارب یحارط يرامعم تخـس رازفا و مرن رازفا متـسیـس دروم هدافتـسا رارق تفرگ ه دنا و رد لحارم يدعب یحارط و هدایپ ،يزاس درکلمع يازجا فلتخم هناماس رب ساسا نیا دنمزاین ي اه نییعت و یبایزرا دهاوخ دش .

لحت یل حارط و ی سی متس

-3-2 يرامعم یلک متسیس

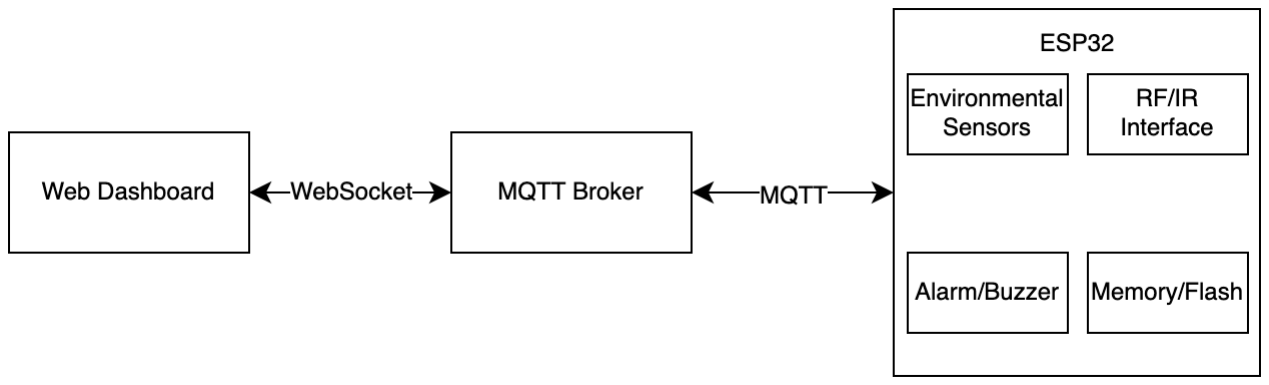
[picture p49: figure]

لکش (3-1 ) يرامعم یلک متسیس

يرامعم هناماـس هب هنوگ يا یحارط هدـش تـسا هک رلرتنکورکیم 32ESP هب ناونع هتـسه یلـصا یـشزادرپ و ،یطاـبترا رد زکرم لـماـعت ناـیم ،اـهرگـــسح تازیهجت ،یلرتنک تـخاـــسریز هـکبـــش و ربراـک رارق دریگ . رد نیا ،يرامعم تاعلاطا طوبرم هب طیارـش یطیحم طـسوت ياهرگـسح لـصتم هب 32ESP تفایرد هدـش و سپ زا ،شزادرپ زا قیرط هکبـش WiFi و لکتورپ MQTT هب تخاـسریز یطابترا هناماـس لاـسرا یم دنوـش . 32ESP هولاع رب تفایرد و شزادرپ تاعلاطا ،اهرگـسح تیلوئـسم تیریدم متـسیـس ،رادـشه تفایرد و لاـسرا لانگیـس ياه RF و IR، هریخذ يزاس تاعلاطا و يارجا نامرف ياه یلرتنک ار زین رب هدهع دراد . رد تمـس ،ربراک کی دروبـشاد تحت بو يارب شیامن تاعلاطا و لرتنک هناماـس رد رظن هتفرگ هدـش تـسا . ربراک یم ت دناو زا قیرط نیا دروبـشاد تیعـضو یلعف اهرگـسح و ریاـس شخب ياه متـسیـس ار هدهاـشم هدرک و نامرف ياـه یلرتنک رظندروم دوخ ار لاـــسرا دـنک . ناـمرف ياـه لاـــسرا هدـــش وت طـــس ربراـک ادـتبا زا قیرط طاـبترا WebSocket هب Broker MQTT لقتنم هدــش و سپــس رد بلاق مایپ MQTT رد رایتخا 32ESP رارق یم دنریگ . 32ESP سپ زا تفایرد ،مایپ نامرف هطوبرم ار شزادرپ هدرک و تایلمع رظندروم ار ارجا یم دنک . هب نیا ،بیترت طابترا نایم تخـس رازفا و ربراک هب روـص ت هفرطود رارقرب هدوب و مه تاعلاطا هاگتـسد هب تمـس ربراک لاسرا یم دنوش و مه نامرف ياه ربراک هب هاگتسد لقتنم یم دنوش . هب تروـص ،یلک يرامعم هناماـس ار یم ناوت زا رظن يدرکلمع هب هـس شخب یلـصا لماـش هیلا تخـس رازفا و عمج يروآ ،هداد هـیلا شزادرپ و لرتنک ینتبم رب 32ESP و هـیلا یطاـبترا و طبار ربراـک میـــسقت درک . نیا کیکفت هب روظنم صخـشم ندرک فیاظو ره شخب و شهاک یگتـسباو نایم يازجا فلتخم متـسیـس ماجنا هدـش تسا . هشقن کیتامش لماک رادم و هوحن لاصتا يازجا تخس يرازفا رد تسویپ -8-1 هئارا هدش تسا .

-3-2-2 هیلا تخس رازفا و عمج يروآ هداد

رد هیلا تخـس رازفا و عمج يروآ ،هداد هعومجم يا زا اهرگـسح و لوژام ياه یطابترا هب 32ESP لـصتم هدـش دنا هک هفیظو اهنآ تفایرد تاعلاطا زا طیحم و يرارقرب ا طابتر اب تازیهجت یجراخ تــسا . رگــسح 11DHT يارب هزادنا يریگ امد و تبوطر ،یبـسن رگـسح -2MQ يارب صیخـشت تارییغت یـشان زا دوجو دود و یخرب ،اهزاگ رگـسح LDR يارب شیاپ تدـش رون طیحم و رگـسح PIR يارب صیخـشت تکرح دروم هدافتـسا رارق

لحت یل حارط و ی سی متس

هتفرگ دنا . یجورخ نیا اهرگـسح هتـسب هب عون اهنآ هب تروـص لاتیجید ای گولانآ رد رایتخا 32ESP رارق هتفرگ و طسوت مرن رازفا Firmware شزادرپ یم دنوش . هولاع رب ياهرگسح ،یطیحم رد نیا هیلا تازیهجت یطابترا طوبرم هب لرتنک تازیهجت یجراخ زین رارق دنراد . هناماــس ياراد هدنریگ و هدنتــسرف RF يارب ياهدناب یــسناکرف 315 و 433 زترهاگم و نینچمه هدنریگ و هدنتــسرف نودام زمرق IR تــسا . نیا تازیهجت ناکما تفایرد لانگیــس ياه ،یلرتنک هریخذ يزاــس تاعلاطا طوبرم هب اهنآ و لاــسرا ددجم لانگیــس ياه هریخذ هدــش ار مهارف یم دننک . رد ،هجیتن هیلا تخــس يرازفا هولاع رب عمج يروآ تاعلاطا ،یطیحم هفیظو داجیا طــساو نایم 32ESP و تازیهجت یجراخ لباق لرتنک ار زین رب هدهع دراد .

-3-2-3 هیلا شزادرپ و لرتنک

32ESP هتسه یلصا شزادرپ و لرتنک هناماس تسا و هفیظو تیریدم شخب هدمع يا زا تایلمع متسیس ار رب هدهع دراد . هداد ياه تفایرد هدـش زا اهرگـسح رد نیا هیلا شزادرپ هدـش و تیعـضو یلعف طیحم نییعت یم دوـش . نینچمه قطنم طوبرم هب متـسیـس رادـشه رد نیا شخب ارجا هدـش و رد تروـص رارقرب ندـش طیارـش فیرعت ،هدـش رزاب لاعف یم دوـش . تیریدم هدنریگ اه و هدنتـسرف ياه RF و IR، شزادرپ نامرف ياه یتفایرد زا MQTT ، تیریدم تاعلاطا هریخذ هدش و قرب يرار طابترا اب Broker MQTT زین رد نیا هیلا ماجنا یم دوش . Firmware طوبرم هب 32ESP هب تروـص رلاوژام یحارط هدـش تـسا ات فیاظو فلتخم متـسیـس زا رگیدکی کیکفت دنوـش . يارب ره کی زا ياهرگـسح ،یلـصا زا هلمج 11DHT، -2MQ، LDR و PIR، شخب ياه مرن يرازفا هطوبرم رد رظن هتفرگ هدـش و تیریدم طابترا RF، طابترا IR، MQTT، ،هظفاح رادـشه و LED زین رد لوژام ياه لقتـسم ماجنا یم دوـش . نیا راتخاـس ثعاب یم دوـش ره شخب تیلوئـسم یـصخـشم هتـشاد دـشاب و ،رییغت حلاـصا ای هعـسوت کی ،تیلباق یگتـسباو يرتمک هب ریاـس شخب ياه مرن رازفا داجیا دنک . نینچمه نیا يرامعم کما نا هفاضا ندرک تیلباق اه و تازیهجت دیدج ار رد لحارم يدعب هعسوت هداس رت یم دنک .

-3-2-4 هیلا یطابترا و طبار ربراک

طابترا نایم 32ESP و تخاـسریز مرن يرازفا هناماـس زا قیرط WiFi رارقرب یم دوـش . سپ زا لاـصتا 32ESP هب ،هکبـش تاعلاطا هزادنا يریگ هدـش و تیعـضو متـسیـس رد بلاق مایپ ياه MQTT هب Broker MQTT لاـسرا یم دنوـش . رد نیا هژورپ زا io.emqx.broker هب ناونع Broker دروم هدافتـسا رد تاطابترا MQTT هدافتـسا هدـش تـسا . 32ESP یم دناوت تاعلاطا اهرگـسح و تیعـضو شخب ياه فلتخم متـسیـس ار رد Topic ياه صخــشم رــشتنم هدرک و نینچمه مایپ اه و نامرف ياه یلرتنک تفایرد هدــش زا قیرط MQTT ار شزادرپ دنک .
دروبـشاد تحت بو زین هب روظنم مهارف ندرک ناکما شیاپ و لرتنک متـسیـس يارب ربراک یحارط هدـش تـسا . نیا دروبـشاد زا قیرط WebSocket هب Broker MQTT لـصتم یم دوـش و یم دناوت یپ ما ياه رـشتنم هدـش طــسوت 32ESP ار تفایرد هدرک و یتاعلاطا دننام تیعــضو ،اهرگــسح ریداقم هزادنا يریگ هدــش و تیعــضو رادشه ار هب ربراک شیامن دهد . زا فرط ،رگید نامرف ییاه هک ربراک زا قیرط دروبشاد لاسرا یم ،دنک رد بلاق مایپ MQTT هب تمـس 32ESP لقتنم هدـش و سپ زا تفایرد ـسوت ط ،هاگتـسد طـسوت شخب تیریدم نامرف

لحت یل حارط و ی سی متس

شزادرپ و ارجا یم دنوش .

-3-3 یحارط تخس رازفا

رد یحارط تخـس يرازفا ،هناماـس لوژام -32WROOM32-ESP هب ناونع دحاو یـشزادرپ و یلرتنک یلـصا باختنا هدـش تـسا . باختنا نیا لوژام اب هجوت هب تیلباق یـشزادرپ ،بـسانم دادعت یفاک هیاپ ياه يدورو و ،یجورخ يرادروخرب زا لدبم گولانآ هب لاتیجید (ADC(، هظفاح بـــسانم و نینچمه ینابیتـــشپ یلخاد زا طابترا WiFi ماجنا هدـش تـسا . 32ESP رد نیا هناماـس شقن هتـسه يزکرم ار رب هدهع دراد و یمامت يازجا تخـس يرازفا لماـش رگـسح ياه ،یطیحم تازیهجت تفایرد و لاـسرا RF و IR، متـسیـس رادـشه و طبار ياه یطابترا هب تروـص میقتـسم ای میقتـسمریغ اب نآ رد طابترا دنتـسه . نیا راتخاـس ثعاب هدـش تـسا هک شزادرپ ،تاعلاطا لرتنک ،تازیهجت هریخذ يزاــس هداد اه و طابترا اب تخاــسریز مرن يرازفا متــسیــس رد کی دحاو يزکرم ماجنا دوش .

-3-3-1 دحاو شزادرپ يزکرم و لاصتا اهرگسح

لوژام -32WROOM32-ESP هفیظو تفایرد تاعلاطا ،اهرگــسح شزادرپ هداد ياه ،یتفایرد يارجا قطنم یلرتنک و ،رادـشه تیریدم تازیهجت RF و IR، هریخذ يزاـس تاعلاطا و يرارقرب طابترا اب هکبـش ار رب هدهع دراد . تیلباق WiFi یلخاد 32ESP يارب لاـصتا هناماـس هب هکبـش یلحم و يرارقرب طابترا اب Broker MQTT دروم هدافتـسا رارق هتفرگ تسا و هیاپ ياه GPIO زین يارب لاصتا تازیهجت لاتیجید و لرتنک یخرب لوژام اه هب راک هتفرگ هدـش دنا . نینچمه يارب تفایرد یجورخ گولانآ رگـسح ییاه دننام -2MQ و LDR زا هیاپ ياه ياراد تیلباق ADC هدافتسا هدش تسا . يارب هزادنا يریگ مد يا طیحم و تبوطر یبـسن زا رگـسح 11DHT هدافتـسا هدـش تـسا . نیا رگـسح زا قیرط کی طخ هداد لاتیجید اب 32ESP طابترا رارقرب یم دنک و تاعلاطا هزادنا يریگ هدـش ار هب تروـص لاتیجید رد راـیتخا رلرتنکورکیم رارق یم دـهد . رد هداـیپ يزاـــس Firmware، يارب طاـبترا اـب 11DHT زا هـناـخباـتک DHT Adafruit و عباوت ()readTemperature و ()readHumidity هدافتـسا هدـش تـسا و هیاپ هداد رگـسح هب 15GPIO لـصتم هدـش تـسا . تاعلاطا تفایرد هدـش سپ زا شزادرپ رد Firmware، هب تروـص هناگادج يارب امد و تبوطر تیریدم هدـش و زا قیرط MQTT رد رایتخا ریاـس شخب ياه هناماـس و دروبـشاد تحت بو رارق یم دنریگ .
يارب شیاپ دوجو دود و یخرب زاگ ياه لباق لاعتــشا زا رگــسح -2MQ هدافتــسا هدــش تــسا . رد نیا هژورپ یجورخ گولانآ نیا رگـسح هب 33GPIO لـصتم هدـش و رادقم نآ طـسوت ADC یلخاد 32ESP هزادنا يریگ یم دوــش . رگــسح -2MQ يارب یبایتــسد هب طیارــش يراک بــسانم هب کی رود ه شیپ شیامرگ زاین دراد و نیاربانب رادقم یجورخ نآ هلـصافلاب سپ زا هار يزادنا متـسیـس هب ناونع کی رادقم رادیاپ رد رظن هتفرگ یمن دوـش . رد یحارط ،رـضاح دنیارف هار يزادنا و مرگ ندـش رگـسح قباطم راتخاـس رادم و Firmware متـسیـس تیریدم یم دوـش و سپ زا هدامآ ندـش ،رگـسح رادقم خ یجور نآ طـسوت ADC هدناوخ یم دوـش . رادقم هب تـسد هدمآ هولاع رب لاـسرا زا قیرط MQTT، اب کی هناتـسآ زا شیپ نییعت هدـش هـسیاقم یم دوـش و رد تروـص روبع رادقم هزادنا يریگ هدش زا ،هناتسآ تیعضو رادشه لاعف هدش و رزاب هب ادص رد یم ؛دیآ نینچمه تیعضو

لحت یل حارط و ی سی متس

رادشه زا قیرط MQTT هب دروبشاد لاسرا یم دوش ات ربراک دناوتب تیعضو متسیس ار هدهاشم دنک . يارب شیاپ تدـش رون طیحم زین زا LDR هدافتـسا هدـش تـسا . زا اجنآ هک یجورخ LDR هب تروـص تارییغت ژاتلو رد کی رادم هزادنا يریگ داجیا یم ،دوش یجورخ نآ هب یکی زا يدورو ياه ADC لصتم هدش تسا . رد نیا هژورپ خ یجور طوبرم هب LDR هب 32GPIO لـصتم هدـش و رادقم نآ طـسوت ADC یلخاد 32ESP هدناوخ یم دوـش . Firmware رد هزاب ياه ینامز صخـشم رادقم یجورخ ار هنومن يرادرب هدرک و رادقم لصاح ار يارب شیاپ تیعضو ییانشور طیحم زا قیرط MQTT رشتنم یم دنک . هب روظنم صیخــشت تکرح رد طیحم زا کی م لوژا PIR هدافتــسا هدــش تــسا هک یجورخ لاتیجید نآ هب 13GPIO لـصتم هدـش تـسا . یماگنه هک رگـسح دوجو تکرح ار رد هدودحم تحت شـشوپ دوخ صیخـشت ،دهد تیعـضو یجورخ لاتیجید نآ رییغت هدرک و 32ESP نیا رییغت تیعـضو ار تفایرد و شزادرپ یم دنک . تیعـضو صیخـشت تکرح سپ زا شزادرپ طـسوت Firmware زا قیرط MQTT رـشتنم یم دوـش و رد تروـص لاعف ندوب تیلباق رادـشه ،تکرح عوقو تکرح یم دناوت بجوم لاعف ندـش متـسیـس رادـشه یتوـص و لاـسرا تیعضو هطوبرم هب دروبشاد دوش .

-3-3-2 متسیس طابترا سناکرف ییویدار

یکی زا تیلباق ياه یلـصا ،هناماـس ناکما ،تفایرد هریخذ يزاـس و شخپزاب لانگیـس ياه سناکرف ییویدار رد ود دناب 315 و 433 زترهاگم تـسا . اب هجوت هب توافت یـسناکرف نیا ود ،هورگ يارب ره دناب کی هدنریگ و کی هدنتـسرف لقتـسم رد رظن هتفرگ هدـش تـسا ات 32ESP دناوتب تفایرد و لاـسرا لانگیـس اه ار هب تروـص هناگادج تـیریدـم دـنک . رد شخب طوبرم هـب دـناـب 315 ،زترهاـگم زا لوژاـم هدـنریگ 61RXB و لوژاـم هدـنتـــسرف S34H هدافتـسا هدـش تـسا هک یجورخ هداد هدنریگ هب 22GPIO و يدورو هداد هدنتـسرف هب 23GPIO لـصتم هدـش دنا . يارب دناب 433 زترهاگم زین زا هدنریگ 35RXB و هدنتـسرف S34H ـسا هدافت هدـش تـسا هک یجورخ هدنریگ هب 14GPIO و يدورو هداد هدنتسرف هب 27GPIO لصتم هدش دنا . رد دنیارف تفایرد ،لانگیــس 32ESP تاعلاطا یتفایرد زا هدنریگ ياه RF ار تفایرد و طــسوت Firmware شزادرپ یم دنک . لانگیــس ياه رظندروم سپ زا تفایرد یم دنناوت اب کی مان صخــشم رد هظفاح متــسیــس هریخذ دنوــش ات رد نامز يرگید ناکما هدافتــسا ددجم زا اهنآ دوجو هتــشاد دــشاب . رد ماگنه لاــسرا ،زین Firmware رب ساـسا تاعلاطا هریخذ هدـش و دناب یـسناکرف طوبرم هب ،لانگیـس هدنتـسرف بـسانم ار باختنا هدرک و هداد رظندروم ار يارب شخپزاب هب نآ لاسرا یم دنک . يارب هدایپ س يزا شخب تفایرد و لاسرا لانگیس ياه RF زا هناخباتک RCSwitch هدافتـسا هدـش تـسا هک ناکما راک اب يرایـسب زا تازیهجت لرتنک زا هار رود RF هداس رد ياهدناب رظندروم ار مهارف یم دنک .

-3-3-3 متسیس طابترا نودام زمرق

يارب مهارف ندرک تیلباق تفایرد و شخپزاب لانگیـس ياه نودام ،زمرق زا کی هدنریگ IR و هعومجم يا لماـش راهچ LED نودام زمرق هدافتــسا هدــش تــسا . هدنریگ نودام زمرق هب 17GPIO لــصتم هدــش و LED ياه هدنتـسرف نودام زمرق زا قیرط 4GPIO لرتنک یم دنوـش . هدنریگ IR لانگیـس ياه لاـسرا هدـش طـسوت لرتنک ياه نودام زمرق ار تفایرد هدرک و تاعلاطا برم طو هب لانگیس طسوت 32ESP شزادرپ یم دوش . لانگیس ياه

لحت یل حارط و ی سی متس

تفایرد هدـش یم دنناوت اب کی مان صخـشم رد هظفاح متـسیـس هریخذ دنوـش ات رد نامز يرگید لباق یبایزاب و شخپزاب دنـشاب . رد دنیارف ،لاـسرا 32ESP تاعلاطا لانگیـس هریخذ هدـش ار یبایزاب هدرک و يوگلا هطوبرم ار زا قیرط LED ياه م نودا زمرق لاـسرا یم ؛دنک هب نیا ،بیترت هاگتـسد یم دناوت شقن کی طـساو دنمـشوه يارب تـفاـیرد و شخپزاـب ناـمرف ياـه لرتنک زا هار رود نوداـم زمرق ار اـفیا دـنک . يارب هداـیپ يزاـــس تـیلباـق تـفاـیرد و لاسرا لانگیس ياه IR زا هناخباتک 8266IRremoteESP هدافتسا هدش تسا .

-3-3-4 متسیس رادشه و شیامن تیعضو

يارب داجیا رادـشه یتوـص رد هناماـس زا کی Buzzer Active هدافتـسا هدـش تـسا هک يدورو نآ هب 19GPIO لـصتم هدـش تـسا . لاعف يزاـس رزاب طـسوت Firmware و رب ساـسا طیارـش فیرعت هدـش رد قطنم متـسیـس ماجنا یم ؛دوـش يارب ،لاثم رد تروـص روبع رادقم هدناوخ هدـش زا رگـسح -2MQ زا هناتـسآ نییعت هدـش ای رد تروـص صیخـشت تکرح یماگنه هک تیلباق رادـشه تکرح لاعف ،دـشاب 32ESP یم دناوت رزاب ار لاعف هدرک و رادـشه یتوـص داجیا دنک . تیعـضو رادـشه زین نامزمه یم دناوت زا قیرط MQTT هب دروبـشاد لاـسرا دوـش ات ربراک هولاع رب تفایرد رادشه ،یلحم تیعضو هاگتسد ار زا قیرط طبار يربراک زین هدهاشم دنک . هب روظنم هئارا دروخزاب يرـصب زا تیعـضو درکلمع هاگتـسد زین کی LED تیعـضو رد رظن هتفرگ هدـش تـسا . نیا LED هب 25GPIO لـصتم هدـش و طـسوت Firmware يارب شیامن تیعـضو تیلاعف متـسیـس و نینچمه شیامن یخرب ياهدادیور مهم دننام تفایرد ای لاـسرا ـس لانگی ياه RF و IR دروم هدافتـسا رارق یم دریگ . هدافتـسا زا LED تیعـضو ثعاب یم دوـش ربراک دناوتب نودب زاین هب هدهاـشم دروبـشاد ای لاـصتا هب ،هکبـش یخرب تیعضو ياه یتایلمع هاگتسد ار هب تروص میقتسم هدهاشم دنک .

لودج (3-1 ) هیاپ ياه 32ESP
| | | ر فید زیهجت هیاپ 32ESP عون يدورو / یجورخ
| | | 1 11DHT 15GPIO يدورو لاتیجید
لاتیجید یجورخ | GPIO26 | MQ-2 Heater | 2
گولانآ يدورو | GPIO33 | MQ-2 ADC | 3
گولانآ يدورو | GPIO32 | LDR ADC | 4
| | | 5 PIR 13GPIO يدورو لاتیجید
لاتیجید يدورو | GPIO22 | RF 315MHz Receiver | 6
لاتیجید یجورخ | GPIO23 | RF 315MHz Transmitter | 7
لاتیجید يدورو | GPIO14 | RF 433MHz Receiver | 8
لاتیجید یجورخ | GPIO27 | RF 433 MHz Transmitter | 9
لاتیجید يدورو | GPIO17 | IR Receiver | 10
لاتیجید یجورخ | GPIO4 | IR LED | 11
| | | 12 Buzzer 19GPIO یجورخ لاتیجید
لاتیجید یجورخ | GPIO25 | Status LED | 13

لحت یل حارط و ی سی متس

-3-4 یحارط مرن رازفا و راتخاس Firmware

Firmware هناماــس رب يور لوژام -32WROOM32-ESP و اب هدافتــسا زا طیحم هعــسوت PlatformIO و بوچراچ Arduino هدایپ يزاـس هدـش تـسا . اب هجوت هب ددعت فیاظو متـسیـس و دوجو شخب ياه یفلتخم دننام تیریدم ،اهرگـسح طابترا ،هکبـش طابترا MQTT، تفایرد و لاـسرا لانگیـس ياه RF و IR، تیریدم رادـشه و هریخذ يزاـس ،تاعلاطا راتخاـس Firmware هب تروـص رلاوژام یحارط هدـش تـسا . رد نیا ،راتخاـس ره شخب زا مرن رازفا تیلوئـسم یـصخـشم دراد و فیاظو متـسیـس نایم لوژام ياه فلتخم میـسقت هدـش ؛دنا هب نیمه ،لیلد رییغت ای هعـسوت کی تیلباق یم دناوت اب نیرتمک یگتـسباو هب ریاـس تمـسق اه ماجنا دوـش و دنیارف ،یسررب لاکشا ییادز و يرادهگن Firmware زین هداس رت دهاوخ دوب .

-3-4-1 راتخاس وژام رلا Firmware

لوژام ياه فلتخم Firmware رب ساسا فیاظو متسیس زا رگیدکی کیکفت هدش دنا . لوژام main لوئسم هار يزادـنا هـیلوا و لرتنک ناـیرج یلـــصا هـماـنرب تـــسا و لوژاـم Sensors هـفیظو یگنهاـمه و تـیریدـم هرود يا اهرگـسح و دادیور ياه یطیحم ار رب هدهع دراد . رد شخب اهرگـسح زین م لوژا ياه یـصاـصتخا DHT، -MQ ،2 LDR و PIR هـب بـیترت يارب تـفاـیرد تاـعلاطا اـمد و ،تـبوطر شیاـپ دود و ،زاـگ هزادـنا يریگ تدـــش رون و صیخـشت تکرح دروم هدافتـسا رارق هتفرگ دنا . لوژام MQTT هفیظو يرارقرب طابترا اب Broker MQTT و تیریدم لاـسرا و تفایرد مایپ اه ار رب هدهع ،دراد رد یلاح هک لوژام ياه RF و IR يارب ،تفایرد شزادرپ و لاــسرا ددجم لانگیــس ياه سناکرف ییویدار و نودام زمرق هدافتــسا یم دنوــش . نینچمه لوژام Alarm تیعــضو رادــشه و درکلمع رزاب ار تیریدم ،هدرک لوژام LED لوئــسم لرتنک LED تیعــضو تــسا و
Provisioning دنیارف تفایرد و میظنت تاعلاطا WiFi و MQTT ار تیریدم یم دنک . يارب هریخذ و یبایزاب | 1
تاـعلاطا زین لوژاـم Memory اـب متـــسیـــس لـیاـف LittleFS رد طاـبترا هدوب و لوژاـم Serial يارب ،تـفاـیرد شزادرپ و شیامن نامرف اه و تاعلاطا زا قیرط طابترا لایرــس دروم هدافتــسا رارق هتفرگ تــسا . رد ،تیاهن رتماراپ اه و تامیظنت تباث دروم زاین متسیس رد لوژام Config يرادهگن یم دنوش .

لودج (3-2 ) هفیظو لوژام ياه Firmware لوژام هفیظو
main هار يزادنا و لرتنک نایرج یلصا همانرب Sensors تیریدم هرود يا رگسح اه و دادیور ياه یطیحم DHT تفایرد امد و تبوطر
-2MQ تفایرد رادقم زاگ و دود LDR تفایرد رادقم رون
PIR صیخشت تکرح
دنیارف هدامآ يزاـس و يدنبرکیپ هیلوا کی هاگتـسد يارب لاـصتا هب هکبـش و سیورـس ياه ،زایندروم زا هلمج ،تفایرد یجنـسرابتعا و هریخذ تامیظنت | 1
یطابترا تسا .

لحت یل حارط و ی سی متس

| MQTT يرارقرب طابترا اب Broker و لاسرا و تفایرد مایپ
| RF تفایرد و لاسرا لانگیس ياه RF
| IR تفایرد و لاسرا لانگیس ياه نودام زمرق
| Alarm تیریدم تیعضو رادشه و رزاب
| LED تیریدم LED تیعضو
MQTT و WiFi يدنبرکیپ | Provisioning
| Memory هریخذ و یبایزاب تاعلاطا رد LittleFS
شزادرپ نامرف ياه ینتم | Serial پاچ و تفایرد و
| Config يرادهگن تامیظنت و رتماراپ ياه تباث

-3-4-2 هار يزادنا و يارجا یلصا متسیس

سپ زا نـشور ندـش 32ESP، همانرب دراو عبات ()setup یم دوـش هک هفیظو هدامآ يزاـس هیلوا يازجا فلتخم هناماـس ار رب هدهع دراد . رد هلحرم ،تـسخن طابترا لایرـس يارب شیامن تاعلاطا هار يزادنا و تفایرد نامرف ياه یلامتحا رارقرب یم دوـش و سپـس تامیظنت و رتماراپ ياه زایندروم متـسیـس زا هظفاح هدناوخ یم دنوـش . رد یتروــص هک تاعلاطا زایندروم هکبــش WiFi و MQTT دوجوم دنــشابن ای زاین هب يدنبرکیپ ددجم دوجو هتـشاد ،دـشاب دنیآرف Provisioning ارجا هدـش و لاتروپ تامیظنت يارب تفایرد تاعلاطا هکبـش و تاـصخـشم MQTT رد راـیتخا ربراـک رارق یم دریگ . سپ زا لـیمکت ،يدـنبرکیپ اـهرگـــسح و لوژاـم ياـه یطاـبترا زاـیندروم هار يزادنا هدـش و متـسیـس شلات یم دنک ادتبا هب هکبـش WiFi و سپـس هب Broker MQTT لـصتم دوـش . سپ زا لـیمکت تـیقفوم زیمآ نیا ،لـحارم متـــسیـــس هداـمآ دورو هـب هـخرچ یلـــصا يارجا هـماـنرب ـهاوخ د دوب .

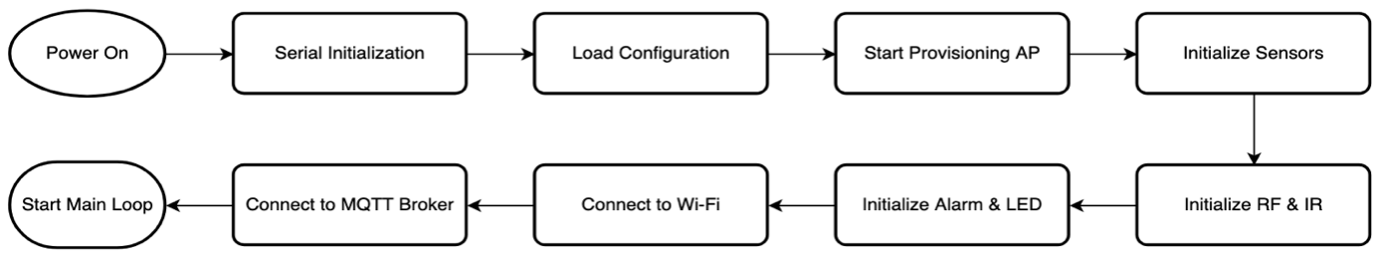
[picture p50: figure]

لکش (3-2 ) دنور هار يزادنا متسیس

پس زا نایاپ تایلمع هار ،يزادنا همانرب دراو عبات ()loop یم دوـــش . نیا عبات هب تروـــص موادم ارجا هدـــش و فیاظو یلـصا هناماـس ار تیریدم یم دنک . رد ره ،هخرچ تیعـضو طابترا لایرـس و MQTT یـسررب هدـش و رد تروـص تفایرد نامرف ،دیدج مایپ هطوبرم ادرپ شز یم ؛دوـش سپـس لوژام تیریدم اهرگـسح تیعـضو رگـسح ياه فلتخم ار یـــسررب هدرک و رد تروـــص ندیـــسر نامز هنومن ،يرادرب ریداقم دیدج ار تفایرد یم دنک . تاعلاطا لصاح زا اهرگسح سپ زا شزادرپ رد Topic ياه طوبرم هب MQTT رشتنم یم دنوش و دادیور ییاه دننام صیخـشت تکرح ای روبع رادقم -2MQ زا هناتـسآ نییعت هدـش زین رد نیمه دنیارف یـسررب و تیریدم یم دنوـش . راتخاـس يارجا همانرب هب هنوگ يا یحارط هدـش تـسا هک تایلمع فلتخم نودب فقوت ینلاوط رد کی شخب ماجنا دنوش و للاتخا رد طابترا ،هکبش ات دح ناکما بجوم فقوت درکلمع ياه یلحم هاگتسد دوشن .

لحت یل حارط و ی سی متس

لکش (3-3 ) دنور يارجا هقلح یلصا متسیس

-3-4-3 تیریدم اهرگسح و قطنم رادشه

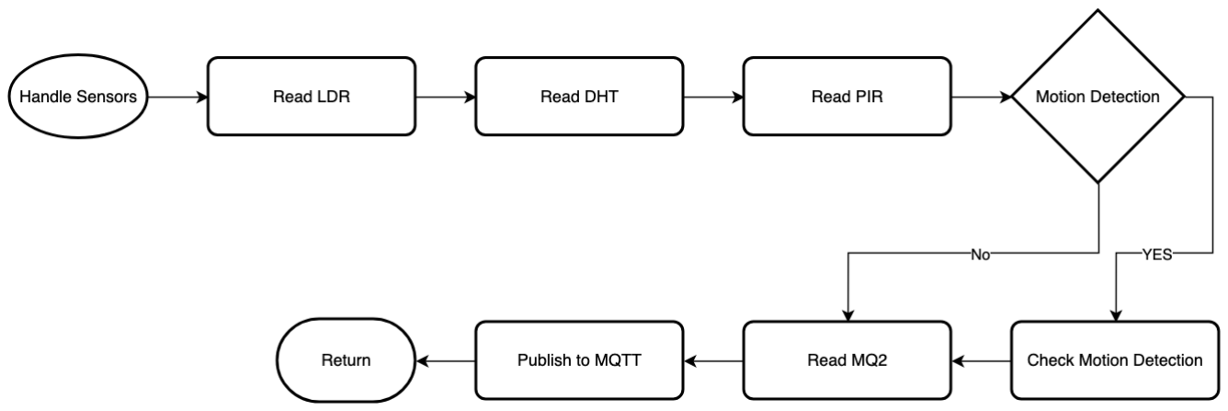
[picture p51: figure]

لکش (3-4 ) دنور تیریدم رگسح اه

تیریدم رگـسح ياه یطیحم طـسوت لوژام Sensors ماجنا یم دوـش و نیا لوژام شقن گنهامه هدننک نایم رویارد ياه طوبرم هب 11DHT، -2MQ، LDR و PIR ار رب هدهع دراد . تاعلاطا اهرگـسح رد هزاب ياه ینامز صخـشم تفایرد هدـش و سپ زا ،شزادرپ رادقم ره رگـسح رد Topic هطوبرم زا قیرط MQTT رـشتنم یم دوـش . رد هخـسن یلعف Firmware، هزاب ینامز یلـصا يارب هنومن يرادرب و راـشتنا تاعلاطا اهرگـسح 10 هیناث رد رظن هتفرگ هدـش تـسا . نیا شور ثعاب یم دوـش هداد ياه یطیحم هب تروـص هرود يا یناـسرزورب ،دنوـش رد یلاح هک شزادرپ موادم و يرورضریغ اهرگسح شهاک ادیپ یم دنک .

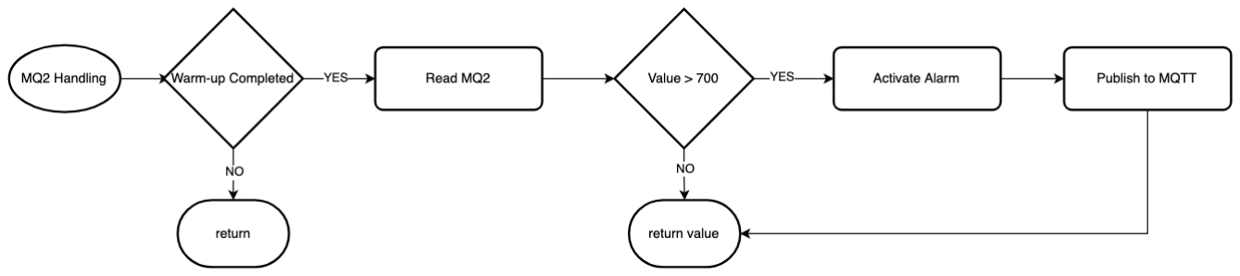
[picture p52: figure]

لکش (3-5 ) دنور تیریدم رگسح -2MQ

رد دروم رگـسح -2MQ، هب لیلد زاین نیا رگـسح هب شیپ ،شیامرگ Firmware سپ زا هار يزادنا هاگتـسد کی هرود هیلوا ار يارب هدامآ يزاـس نآ رد رظن یم دریگ و ات نایاپ نیا هرود رادقم رگـسح هب ناونع هداد لباق اکتا يارب میمـصت يریگ رادـشه هدافتـسا یمن دوـش . سپ زا نایاپ نامز شیپ ،شیامرگ یجورخ گولانآ -2MQ طـسوت ADC هدناوخ هدـش و رادقم هب تـسد هدمآ هولاع رب راـشتنا زا قیرط MQTT، اب هناتـسآ نییعت هدـش رد

لحت یل حارط و ی سی متس

Firmware هــسیاقم یم دوــش . رد هخــسن یلعف ،هژورپ نامز شیپ شیامرگ هیلوا هب لیلد تیدودحم ینامز شیامزآ اه 5 هقیقد و رادقم هناتـسآ 700 رد رظن هتفرگ هدـش تـسا . رد تروـص روبع رادقم هدناوخ هدـش زا نیا ،هناتـسآ لوژام Alarm لاعف هدـش و تیعـضو رادـشه هولاع رب يزاـسلاعف ،رزاب زا قیرط MQTT زین هب دروبـشاد لاـسرا یم دوـش . مزلا هب رکذ تـسا هک نیا ریداقم اب هجوت هب طیارـش شیامزآ و فده هنومن هیلوا باختنا هدـش دنا و رادقم بـسانم هناتـسآ -2MQ رد کی طیحم یعقاو دیاب رب ساـسا طیارـش ،طیحم ویـساربیلاک ن رگـسح و نومزآ ياه یلمع نییعت دوش . امد و تبوطر طیحم طـسوت رگـسح 11DHT هزادنا يریگ یم دنوـش و هداد ياه نآ رد لـصاوف ینامز نییعت هدــش طــسوت لوژام Sensors تفایرد یم دنوــش . يارب طابترا اب نیا رگــسح زا هناخباتک DHT Adafruit هدافتـسا هدـش تـسا و Firmware اب هدافتـسا زا عباوت ()readTemperature و ()readHumidity هب بیترت رادقم امد و تبوطر یبـسن ار تفایرد یم دنک . رادقم تدـش رون زین طـسوت LDR و يدورو ADC هدناوخ هدـش و دننام ریاـس هداد ياه یطیحم سپ زا شزادرپ رد رایتخا لوژام MQTT رارق یم دریگ . رگـسح PIR زین هب تروـص یجید لات یـسررب هدـش و رییغت تیعـضو یجورخ نآ هب ناونع دادیور صیخـشت تکرح رد رظن هتفرگ یم دوـش . تیلباق صیخـشت تکرح رد Firmware لباق لاعف ای لاعفریغ ندـش تـسا و نیا راک زا قیرط نامرف ياه on motion و off motion ماجنا یم دوـش . رد یتروـص هک تیلباق صیخـشت تکرح لاعف دـشاب وPIR و عوق تکرح ار شرازگ ،دنک دادیور هطوبرم طسوت متسیس شزادرپ هدش و یم دناوت ثعاب لاعف ندش تیعضو رادشه و لاسرا مایپ هطوبرم هب MQTT دوش . تیریدم تیعـضو رادـشه طـسوت لوژام Alarm ماجنا یم دوـش و نیا لوژام لوئـسم لرتنک Buzzer Active و نییعت تیعضو رادشه متسیس تسا . رد هدایپ يزاس یلعف ود دادیور یلصا یم دنناوت بجوم لاعف ندش رادشه دنوـش هک لماـش روبع رادقم -2MQ زا هناتـسآ نییعت هدـش و صیخـشت تکرح رد تروـص لاعف ندوب تیلباق صیخــشت تکرح تــسا . هولاع رب رادــشه ياه ،راکدوخ ناکما لرتنک میقتــسم رزاب زین زا قیرط نامرف ياه on buzzer و off buzzer مهارف هدـش تـسا . یماگنه هک تیعـضو رادـشه لاعف یم ،دوـش رزاب رب ساـسا قطنم ینامز فیرعت هدـش طـسوت Firmware لرتنک یم دوـش . رد هخـسن یلعف هخرچ ینامز لاعف و لاعفریغ ندـش نآ 2 هیناث رد رظن هتفرگ هدـش تـسا . نیا راتخاـس ثعاب یم دوـش متـسیـس دناوتب مه رد شنکاو هب ياهدادیور یطیحم و مه رد خساپ هب نامرف میقتسم ،ربراک رادشه یتوص داجیا دنک .

-3-5 یحارط طابترا WiFi و MQTT

طابترا کبـش ه يا هناماـس رب هیاپ تیلباق WiFi یلخاد 32ESP یحارط هدـش تـسا و نیا ،طابترا ریـسم یلـصا لدابت تاعلاطا نایم ،هاگتــسد Broker MQTT و اد دروبــش تحت بو ار مهارف یم دنک . 32ESP سپ زا هار يزادنا و تفایرد تامیظنت ،هکبـش هب هکبـش WiFi رظندروم لـصتم هدـش و زا قیرط نیا طابترا ناکما لاـسرا تاعلاطا ،اهرگــسح تیعــضو رادــشه و ریاــس هداد ياه هناماــس هب تخاــسریز مرن يرازفا ار مهارف یم دنک . نینچمه نیمه ریـسم يارب فایرد ت نامرف ياه یلرتنک زا تمـس ربراک دروم هدافتـسا رارق یم ؛دریگ نیاربانب طابترا هکبش يا متسیس هب تروص هفرطود یحارط هدش تسا .

لحت یل حارط و ی سی متس

-3-5-1 يدنبرکیپ و طابترا WiFi

رد هناماـس رـضاح زا تلاح STA_AP_WIFI هدافتـسا هدـش تـسا . رد نیا ،تلاح 32ESP یم دناوت هب تروـص نامزمه رد شقن Station هب هکبـش WiFi رظندروم لـصتم هدـش و رد رانک نآ کی Point Access یـصاـصتخا زین داجیا دنک . نیا تیلباق رد دنیآرف Provisioning دروم هدافتـسا رارق یم دریگ و هب هاگتـسد هزاجا یم دهد نودب زاین هب رییغت ای لیاپماک ددجم Firmware، لاطا تاع طوبرم هب هکبـش WiFi و ریاـس تامیظنت زایندروم ار زا ربراک تفایرد دنک . سپ زا ماجنا يدنبرکیپ و يرارقرب لاـصتا هب هکبـش ،یلـصا 32ESP زا طابترا WiFi هب ناونع ریسم یطابترا دوخ اب Broker MQTT هدافتسا یم دنک . هدافتـسا زا نیا راتخاـس ثعاب هدـش تـسا هک دنیآرف هار يزادنا هیلوا هاگتـسد زا تامیظنت تباث Firmware ادج دوــش و ربراک دناوتب تاعلاطا هکبــش ار رد نامز هار يزادنا ای رد تروــص زاین رد لحارم يدعب رییغت دهد . رد ،هجیتن هاگتــسد يارب هدافتــسا رد هکبــش ياه فلتخم يزاین هب رییغت دک همانرب دهاوخن تــشاد و تاعلاطا يدنبرکیپ هدـش زین یم ناوت دن رد هظفاح یلخاد هاگتـسد هریخذ هدـش و رد هار يزادنا ياه يدعب دروم هدافتـسا رارق دنریگ .

-3-5-2 طابترا MQTT

يارب لدابت تاعلاطا نایم 32ESP، Broker MQTT و دروبـشاد تحت بو زا لکتورپ MQTT هدافتـسا هدـش تـسا . نیا لکتورپ رب ساسا لدم Subscribe/Publish لمع یم دنک و ثعاب یم دوش ف هدنتسر و هدنریگ مایپ اه ًامیقتـسم هب رگیدکی هتـسباو دنـشابن . رد نیا ،يرامعم 32ESP تاعلاطا اهرگـسح و تیعـضو متـسیـس ار رد Topic ياه صخـشم رـشتنم یم دنک و دروبـشاد ای ریاـس Client ياه لـصتم هب Broker یم دنناوت Topic ياـه رظندروم ار Subscribe هدرک و ماـیپ ياـه هـطوبرم ار ـیرد تـفا دـننک . زا فرط ،رگید دروبـــشاد یم دـناوت نامرف ياه یلرتنک ار رد Topic ياه صخـشم رـشتنم دنک و 32ESP اب Subscribe ندرک هب نیا Topic ،اه مایپ ياه تفایرد هدش ار شزادرپ و ارجا دنک . رد نیا هژورپ زا io.emqx.broker هب ناونع Broker MQTT هدافتـسا هدـش تسا . يارب يریگولج زا یگدنکارپ Topic اه و داجیا کی راتخاـس ،مظنم کی Topic هیاپ اب رادقم homeintelligence رد رظن هتفرگ هدـش تـسا و مان هاگتـسد زین طـسوت ربراک نییعت یم دوـش . رب نیا ،ساـسا Topic ياه فلتخم هناماـس زا کی راتخاـس كرتـشم يوریپ یم دننک و عون داد ه ای درکلمع ره Topic زا شخب ییاهتنا ریـسم نآ صخـشم یم دوـش . هب تروص یلک یم ناوت راتخاس Topic ار هب تروص ریز رد رظن تفرگ : ℎomeintelligence / < device > / < subtopic > يارب تاعلاطا ،اهرگــسح ره عون هداد رد کی Topic ازجم رــشتنم یم دوــش ات رد تفای و شزادرپ نآ يارب دروبـشاد و ریاـس Client اه هداـس دـشاب . راتخاـس Topic ياه طوبرم هب ياهرگـسح یلـصا هناماـس رد لودج ریز هئارا هدش تسا

لودج (3-3 ) Topic ياه طوبرم هب اهرگسح
| Topic هداد
امد | ... /sensor/TEMP

لحت یل حارط و ی سی متس

تبوطر | ... /sensor/HUM
| LDR/sensor/ …تدش رون
| PIR/sensor/ …صیخشت تکرح
| 2MQ/sensor/ …دود و زاگ

رد رانک تاعلاطا ،اهرگـسح يارب علاطا یناـسر ادیور د ياه مهم متـسیـس زا Topic طوبرم هب رادـشه اب راتخاـس alarm.../ هدافتـسا هدـش تـسا . نیا Topic يارب لاـسرا مایپ ییاه هک ناـشن هدنهد عوقو ای رییغت تیعـضو کی دادیور رادـشه دنتـسه دروم هدافتـسا رارق یم دریگ . يارب ،لاثم رد تروـص روبع رادقم -2MQ زا هناتـسآ نییعت ،هدــش مایپ exceed threshold 2MQ رــشتنم یم دوــش و رد تروــص صیخــشت تکرح زین مایپ Motion Detected هب دروبــشاد لاــسرا یم دوــش . نینچمه رییغت تیعــضو تیلباق صیخــشت تکرح اب مایپ ياه ON Motion و OFF Motion علاطا یناسر یم دوش . يارب تفایرد نامرف ياه یلرتنک زا تمـس دروبـشاد زین Topic اب راتخاـس command.../ رد رظن هتفرگ هدـش ــسا ت . Firmware نیا Topic ار Subscribe هدرک و رد تروــص تفایرد مایپ ،دیدج نآ ار هب شخب تیریدم نامرف لقتنم یم دنک . نیا شخب رب ساـسا ياوتحم ،مایپ یلمع تا رظانتم ار ییاـسانـش و ارجا می دنک . هب نیا ،بیترت تیلباق ییاه دننام لاعف ای لاعفریغ ندرک صیخـشت ،تکرح لرتنک رزاب و ریاـس تایلمع یلرتنک یم دنناوت زا قیرط کی ریسم یطابترا صخشم تیریدم دنوش . هولاع رب هداد ياه رگـسح و نامرف ياه ،یلرتنک هناماـس دیاب تـسرهف لانگیـس ياه هریخذ هدـش RF و IR ار زین رد رایتخا دروبـشاد رارق دهد . يارب نیا روظنم زا Topic ياه list/RF.../ و list/IR.../ هدافتسا هدش تسا . مایپ ياه رـشتنم هدـش رد یا ن Topic اه رد بلاق JSON لاـسرا یم دنوـش و لماـش تاعلاطا طوبرم هب لانگیـس ياه هریخذ هدـش دنتـسه . دروبـشاد اب تفایرد نیا تاعلاطا یم دناوت تـسرهف انگیـس ل ياه دوجوم ار هب ربراک شیاـمن هداد و ناـکما باـختنا لاـنگیـــس رظندروم يارب ماـجنا تاـیلمع ،يدـعب دـنناـم لاـــسرا ددـجم اـی تـیریدـم تاعلاطا ریخذ ه ،هدش ار مهارف دنک .

-3-6 یحارط متسیس RF

یکی زا تیلباق ياه یلـصا ،هناماـس ناکما ،تفایرد هریخذ اـس يز و شخپزاب لانگیـس ياه ییویدار رد ود دناب یـسناکرف 315 و 433 زترهاگم تـسا . اب هجوت هب هکنیا هدنریگ اه و هدنتـسرف ياه دروم هدافتـسا رد ره دناب هب تروــص کت سناکرف لمع یم ،دننک يارب ره کی زا نیا ود دناب کی ریــسم لقتــسم يارب تفایرد و لاــسرا لانگیــس رد رظن هتفرگ هدــش تــسا . هب نیا ،بیترت هناماــس یم دناوت لانگیــس ياه طوبرم هب ره ود دناب ار تفایرد هدرک و سپ زا ییاــسانــش و هریخذ تاعلاطا ،اهنآ رد نامز زایندروم لانگیــس ار زا قیرط هدنتــسرف بـسانتم اب دناب یـسناکرف نآ شخپزاب دنک . تیریدم طابترا اب لوژام ياه RF و تفایرد و لاـسرا لانگیـس اه رد Firmware طسوت هناخباتک RCSwitch ماجنا هدش تسا .

-3-6-1 تفایرد و هریخذ يزاس لانگیس RF

دنیارف تفایرد لانگیـس RF زا قیرط نامرف <name <rx rf زاغآ یم دوـش هک رد نآ <name <یمان تـسا هک

لحت یل حارط و ی سی متس

ربراک يارب لانگیـس رظندروم نییعت یم دنک . سپ زا يارجا نیا ف ،نامر Firmware ره ود ریـسم تفایرد RF طوبرم هب ياهدناب 315 و 433 زترهاگم ار لاعف هدرک و تیعضو هدنریگ اه ار یسررب یم دنک . یماگنه هک کی لانگیـس طـسوت یکی زا هدنریگ اه تفایرد ،دوـش تاعلاطا طوبرم هب لانگیـس طـسوت هناخباتک RCSwitch جارختـسا هدـش و دناب یـسناکرف طوبرم هب هدنریگ يا هک لانگیـس ار تفایرد هدرک تـسا زین صخـشم یم دوـش . نیا تاعلاطا سپـس رد بلاق راتخاـس دروم هدافتـسا Firmware رارق هتفرگ و اب مان نییعت هدـش طـسوت ربراک رد هظفاح یمئاد هاگتسد هریخذ یم دوش . تاعلاطا لانگیـس ياه RF رد لیاف json.signals_rf/ رد متـسیـس لیاف LittleFS يرادهگن یم دنوـش . هدافتـسا زا هظفاح یمئاد ثعاب یم دوـش تاعلاطا لانگیـس ياه هریخذ هدـش اب شوماخ ای هار يزادنا ددجم 32ESP زا نیب دنورن و هاگتــسد دناوتب سپ زا هار يزادنا ،ددجم تاعلاطا یلبق ار زا هظفاح یبایزاب دنک . نینچمه هریخذ مان لانگیـس رد رانک تاعلاطا طوبرم هب دناب یـسناکرف ثعاب یم دوـش رد ماگنه ،شخپزاب متـسیـس دناوتب نودب تفایرد ددجم تاعلاطا زا ،ربراک هدنتسرف بسانم ار باختنا دنک .

-3-6-2 شخپزاب و تیریدم لانگیس RF

يارب شخپزاب کی لانگیس هریخذ هدش زا نامرف <name <tx rf هدافتسا یم دوش . سپ زا تفایرد نیا ،نامرف Firmware مان نگیـس لا رظندروم ار رد تاعلاطا هریخذ هدـش تـسج و وج هدرک و سپ زا یبایزاب تاعلاطا ،نآ دناب یـسناکرف طوبرم هب لانگیـس ار یـسررب یم دنک . سپـس رب ساـسا دناب تبث ،هدـش هدنتـسرف بـسانم باختنا هدـش و تاعلاطا لانگیـس زا قیرط نآ لاـسرا یم دوـش . رد ،هجیتن ربراک ماگنه شخپزاب لانگیـس زاین ي هب صخشم ندرک سناکرف درادن و باختنا ریسم لاسرا هب تروص راکدوخ طسوت Firmware ماجنا یم دوش . يارب تیریدم لانگیـس ياه هریخذ هدـش زین نامرف ياه list rf و <name <del rf رد رظن هتفرگ هدـش دنا . نامرف list rf تــسرهف لانگیــس ياه دوجوم رد هظفاح ار شیامن هداد و تاعلاطا یا ن تــسرهف ار زا قیرط MQTT زین رد رایتخا دروبـشاد رارق یم دهد ات ربراک دناوتب لانگیـس ياه هریخذ هدـش ار هدهاـشم و باختنا دنک . نامرف <name <del rf زین يارب فذح کی لانگیس صخشم زا هظفاح هدافتسا یم دوش .

-3-7 یحارط متسیس نودام زمرق

متـسیـس نودام زمرق هناماـس زا ود شخب یلـصا یگ هدنر و هدنتـسرف لیکـشت هدـش تـسا و هفیظو نآ ،تفایرد ،شزادرپ هریخذ يزاـس و شخپزاب نامرف ياه نودام زمرق دروم هدافتـسا رد تازیهجت فلتخم تـسا . رد نیا ،شخب هدنریگ نودام زمرق لانگیـس لاـسرا هدـش طـسوت لرتنک ياه زا هار رود ار تفایرد هدرک و تاعلاطا نآ طـسوت 32ESP شزادرپ یم ؛دوـش سپـس لانگیـس تفایرد هدـش اب کی مان صخـشم رد هظفاح یمئاد هاگتـسد هریخذ هدـش و رد نامز زایندروم یم ناوت نآ ار یبایزاب و زا قیرط LED ياه نودام زمرق شخپزاب درک . يارب هدایپ يزاس دنیارف تفایرد و لاسرا لانگیس ياه IR زا هناخباتک 8266IRremoteESP هدافتسا دش ه تسا هک ناکما راک اب يدادعت زا لکتورپ ياه جیار لرتنک زا هار رود ار مهارف یم دنک .

لحت یل حارط و ی سی متس

-3-7-1 تفایرد و هریخذ يزاس لانگیس IR

دنیارف تفایرد لانگیـس نودام زمرق اب يارجا نامرف <name <rx ir زاغآ یم دوـش هک رد نآ <name <یمان تــسا هک ربراک يارب لانگیــس رظندروم نییعت یم دنک . سپ از يارجا ،نامرف Firmware دراو تلاح تفایرد هدـش و رظتنم تفایرد کی لانگیـس نودام زمرق یم دنام . اب تفایرد ،لانگیـس تاعلاطا طوبرم هب نآ طـسوت هدنریگ تفایرد هدـــش و هناخباتک 8266IRremoteESP هداد ياه طوبرم هب لکتورپ و ياوتحم لانگیـــس ار جارختـسا و يارب شزادرپ رد رایتخا Firmware رارق یم دهد . هناماـس رداق هب ییاـسانـش و شزادرپ يدادعت زا لکتورپ ياه جیار دننام NEC، SONY، SAMSUNG و PANASONIC تــسا و رد یتروــص هک لکتورپ تفایرد هدـش طـسوت هناخباتک ییاـسانـش ای ینابیتـشپ ،دوـشن تاعلاطا ماخ لانگیـس زین لباق تفایرد و هریخذ يزاس دهاوخ دوب .
سپ زا تفایرد ،لانگیــس تاعلاطا نآ اب مان نییعت هدــش طــسوت ربراک رد هظفاح یمئاد هاگتــسد و رد بلاق JSON هریخذ یم دوــش . تاعلاطا طوبرم هب لانگیــس ياه IR رد لیاف json.signals_ir/ رد متــسیــس لیاف LittleFS يرادهگن یم دنوـش . هریخذ يزاـس رد هظفاح یمئاد ثعاب یم دوـش لانگیـس ه يا تبث هدـش سپ زا شوماخ و نـشور ندـش هاگتـسد زین ظفح دنوـش و رد هار يزادنا ياه يدعب ناکما یبایزاب و هدافتـسا ددجم زا اهنآ دوجو هتشاد دشاب .

-3-7-2 شخپزاب و تیریدم لانگیس IR

يارب شخپزاب کی لانگیس هریخذ هدش زا نامرف <name <tx ir هدافتسا یم دوش . سپ زا تفایرد نیا ،نامرف Firmware تاعلاطا لانگیــس رظندروم ار زا هظفاح یبایزاب هدرک و رب ساــسا تاعلاطا هریخذ ،هدــش شور بـسانم يارب لاـسرا نآ ار باختنا یم دنک . رد یتروـص هک لکتورپ لانگیـس طـسوت هناخباتک ینابیتـشپ ،دوـش هداد ياه طوبرم هب نآ اب هدافتـسا زا لکتورپ انـش ییاـس هدـش دیلوت و زا قیرط LED ياه نودام زمرق لاـسرا یم ؛دنوـش رد ریغ نیا ،تروـص تاعلاطا ماخ هریخذ هدـش دروم هدافتـسا رارق هتفرگ و لانگیـس هب تروـص ماخ شخپزاب یم دوـش . هب نیا ،بیترت هناماـس هولاع رب ینابیتـشپ زا لکتورپ ياه هتخانـش ،هدـش ناکما هریخذ و شخپزاب لانگیس ییاه ار هک لکتورپ اهنآ لباق ییاسانش تسین زین مهارف یم دنک . يارب تیریدم لانگیـس ياه هریخذ هدـش زین ود نامرف list ir و <name <del ir رد رظن هتفرگ هدـش تـسا . نامرف list ir تـسرهف لانگیـس ياه دوجوم رد هظفاح ار شیامن هداد و تاعلاطا طوبرم هب نیا تـسرهف ار زا قیرط MQTT زین رد رایتخا دروبــشاد رارق یم دهد ات ربراک دناوتب لانگیــس ياه تبث هدــش ار هدهاــشم و باختنا دنک . نامرف <name <del ir زین يارب فذح کی لانگیس صخشم زا هظفاح هدافتسا یم دوش .

-3-8 یحارط متسیس هریخذ يزاس

يارب هریخذ يزاـس یتاعلاطا هک دیاب سپ زا شوماخ و نـشور ندـش اگتـسد ه زین ظفح ،دنوـش زا متـسیـس لیاف LittleFS دوجوم رد 32ESP هدافتسا هدش تسا . هدافتسا زا نیا متسیس لیاف ناکما هریخذ يزاس تاعلاطا هب تروـص یمئاد و نودب زاین هب هظفاح یجراخ ار مهارف یم دنک و ثعاب یم دوـش تامیظنت هاگتـسد و تاعلاطا لانگیـس ياه تبث هدـش سپ زا هار يزادنا جم دد زین لباق یبایزاب دنـشاب . رد نیا هژورپ تاعلاطا یمئاد هناماـس

لحت یل حارط و ی سی متس

رد بلاق لیاف ياه JSON نامزاـس یهد هدـش تـسا ات راتخاـس هداد اه ،هداـس لباق ندناوخ و لباق شزادرپ طسوت Firmware دشاب .
رد ،عومجم راهچ لیاف یلــصا يارب يرادهگن تاعلاطا یمئاد هناماــس رد رظن هتفرگ هدــش تــسا هک هر کی هفیظو یـصخـشم رب هدهع دنراد . لیاف json.provisioning يارب يرادهگن تاعلاطا طوبرم هب هکبـش WiFi و MQTT، لیاف json.settings يارب تامیظنت یلخاد ،هاگتـسد لیاف json.signals_rf يارب يرادهگن لانگیـس ياه RF و لیاف json.signals_ir يارب يرادهگن لانگیس ياه نودام زمرق هدافتسا یم دوش .

-3-8-1 هریخذ تامیظنت و تاعلاطا هاگتسد

تاعلاطا طوبرم هب يدنبرکیپ هکبـش رد لیاف json.provisioning و هب تروـص JSON هریخذ یم دنوـش . نیا تاعلاطا لماــش SSID و زمر روبع هکبــش WiFi، سردآ و تروپ Broker MQTT، مان يربراک و زمر روبع MQTT رد تروـص هدافتـسا و مان یـصاـصتخا هاگتـسد تـسا . يرادهگن نیا تاعلاطا رد هظفاح یمئاد ثعاب یم دوـش هاگتـسد سپ زا هار يزادنا ددجم دناوتب تامیظنت یلبق ار یبایزاب هدرک و نودب زاین هب دراو ندرک ددجم تاعلاطا ،هکبش دنیارف لاصتا ار ماجنا دهد . تامیظنت طوبرم هب تیعـضو یلخاد هاگتـسد زین رد لیاف json.settings هریخذ یم دنوـش . رد هخـسن یلعف ،هژورپ یکی زا مهم نیرت تاعلاطا نیا لیاف تیعـضو لاعف ای لاعفریغ ندوب تیلباق صیخـشت تکرح تـسا . هب نیا ،بیترت یتامیظنت هک دیاب سپ زا شوماخ و نــشور ندــش هاگتــسد ظفح ،دنوــش زا تاعلاطا طوبرم هب يدنبرکیپ هکبـش و تاعلاطا لانگیـس اه ادج يرادهگن هدـش و ره هورگ زا هداد اه لیاف صوـصخم هب دوخ ار دراد .

-3-8-2 هریخذ يزاس لانگیس RF و IR

تاعلاطا طوبرم هب لانگیـس ياه RF رد لیاف json.signals_rf هریخذ یم دنوـش . يارب ره ،لانگیـس هولاع رب مان نییعت هدـــش طـــسوت ،ربراک تاعلاطا زایندروم يارب شخپزاب نآ زین رد هظفاح يرادهگن یم دوـــش . نیا تاعلاطا لماـش دک ،لانگیـس دادعت ،تیب ،لکتورپ لوط سلاپ و دناب یـسناکرف تـسا . هریخذ دناب یـسناکرف رد رانک ریاـس تاعلاطا لانگیـس تیمها ،دراد اریز متـسیـس ماگنه شخپزاب یم دناوت رب ساـسا نیا ،رادقم هدنتـسرف بسانم طوبرم هب دناب 315 ای 433 زترهاگم ار هب تروص راکدوخ باختنا دنک . لانگیـس ياه نودام زمرق زین رد لیاف json.signals_ir هریخذ یم دنوـش . تاعلاطا یلـصا ره لانگیـس لماـش مان ،لانگیـس ،لکتورپ دک انگیـس ل و دادعت تیب تـسا و رد يدراوم هک لکتورپ لانگیـس لباق ییاـسانـش ای ینابیتـشپ ،دـشابن تاعلاطا ماخ لانگیـس زین رد راتخاـس هریخذ يزاـس يرادهگن یم دوـش ات ناکما شخپزاب نآ رد هدنیآ دوجو هتـشاد دـشاب . نیا شور ثعاب هدـش تـسا هک متـسیـس اهنت هب لکتورپ ياه هتخانـش هدـش هتـسباو دشابن و دناوتب لانگیس ياه ماخ ار زین يارب هدافتسا ددجم هریخذ دنک .

لحت یل حارط و ی سی متس

### -3-9 یحارط متسیس Provisioning و Portal Captive

یکی زا تیلباق ياه مرن يرازفا ،هناماـس ناکما يدنبرکیپ تاعلاطا طوبرم هب هکبـش WiFi و MQTT نودب زاین هب رییغت ای لیاپماک ددجم Firmware تــسا . نیا تیلباق اب افتــسا هد زا مزیناکم Provisioning هدایپ يزاــس هدـش تـسا و هب ربراک هزاجا یم دهد رد نامز هار يزادنا ،هاگتـسد تاعلاطا زایندروم يارب لاـصتا هب هکبـش و Broker MQTT ار زا قیرط کـی طبار تـحت بو دراو و هریخذ دـنک . يارب يارجا نیا ،دـنیآرف 32ESP رد تلاح STA_AP_WIFI رارق یم ؛دریگ هب نیا بیترت هاگتـسد هولاع رب شلات يارب لاـصتا هب هکبـش WiFi میظنت ،هدـش کی Point Access یـصاـصتخا زین داجیا یم دنک هک يارب یـسرتـسد ربراک هب شخب يدنبرکیپ دروم هدافتسا رارق یم دریگ .

لودج (3-4 ) تاصخشم AP
| هصخشم رادقم
Intelligence_Setup | SSID
12345678 | Password
192.168.4.1 | IP
سپ زا لاصتا ربراک هب Point Access ،هاگتسد کی Portal Captive رد رایتخا يو رارق یم دریگ هک هب ناونع طبار يدنبرکیپ هناماـس لمع یم دنک . نیا هحفـص ناکما دراو ندرک تاعلاطا زایندروم يارب لاـصتا 32ESP هب هکبش WiFi و Broker MQTT ار مهارف یم دنک و ربراک یم دناوت یتاعلاطا دننام مان ،هکبش زمر روبع WiFi، سردآ و تروپ Broker MQTT و رد تروــص زاین تاعلاطا زارحا تیوه MQTT ار رد نآ دراو دنک . سپ زا لاـسرا و دییأت ،تاعلاطا Firmware هداد ياه تفایرد هدـش ار رد بلاق JSON رد لیاف json.provisioning دوجوم رد متسیس لیاف LittleFS هریخذ هدرک و سپس هاگتسد ار هار يزادنا ددجم یم دنک .

### Web Dashboard یحارط -3-10

دروبـشاد تحت بو هناماـس اب فده شیامن تاعلاطا ،یطیحم هدهاـشم تیعـضو درکلمع هاگتـسد و لاـسرا نامرف ياه یلرتنک هب 32ESP یحارط هدـش تـسا . نیا دروبـشاد هب تروـص Serverless هدایپ يزاـس هدـش و ب يار لدابت تاعلاطا ًامیقتــسم زا قیرط WebSocket هب Broker MQTT لــصتم یم ؛دوــش نیاربانب يارب طابترا نایم طبار ربراک و 32ESP يزاین هب داجیا کی رورـس طـساو یـصاـصتخا دوجو درادن . زا اجنآ هک رگرورم ياه بو هب تروـص میقتـسم زا طابترا MQTT رب رتـسب TCP ینابیتـشپ یمن ،دننک Broker MQTT دروم هدافتـسا دیاب تیلباق WebSocket ار لاعف هدرک دـشاب ات دروبـشاد دناوتب زا قیرط نیا لکتورپ هب Broker لـصتم هدـش و مایپ ياه MQTT ار تفایرد و لاسرا دنک . سپ زا يرارقرب ،لاــصتا دروبــشاد Topic ياه طوبرم هب تاعلاطا اهرگــسح ار Subscribe هدرک و هداد ياه رـشتنم دـش ه طـسوت 32ESP ار هب تروـص هظحل يا تفایرد یم دنک . تاعلاطا طوبرم هب ،امد ،تبوطر تدـش ،رون تیعـضو صیخـشت تکرح و رادقم طوبرم هب دود و زاگ رد شخب ياه هطوبرم شیامن هداد یم دنوـش و اب تفایرد ره مایپ ،دیدج رادقم شیامن هداد هدـش رد طبار ربراک یناـسرزورب یم ؛دوـش نیاربانب رب يا هدهاـشم تارییغت يزاین هب Refresh ندرک هحفـص دوجو درادن . هولاع رب تاعلاطا ،اهرگـسح دروبـشاد مایپ ياه طوبرم

لحت یل حارط و ی سی متس

هب تیعــضو رادــشه ار زین تفایرد هدرک و رد تروــص عوقو دادیور ییاه دننام روبع رادقم -2MQ زا هناتــسآ نییعت هدش ای صیخشت تکرح رد تلاح ،لاعف تیعضو رادشه ار هب ربراک شیامن یم دهد . دروبــشاد هولاع رب شیامن ،تاعلاطا ناکما لاــسرا نامرف ياه یلرتنک هب 32ESP ار زین مهارف یم دنک . نیا نامرف اه زا قیرط MQTT و رد Topic طوبرم هب command.../ لاــسرا هدــش و سپ زا تفایرد طــسوت 32ESP، طـسوت شخب تیریدم نامرف شزادرپ و ارجا یم دنوـش . نامرف ياه on buzzer و off buzzer يارب لرتنک رزاب و نامرف ياه on motion و off motion يارب لاعف ای لاعفریغ ندرک تیلباق صیخــشت تکرح دروم هدافتـسا رارق یم گ دنری . نینچمه نامرف ياه طوبرم هب تیریدم لانگیـس ياه RF و نامرف ياه طوبرم هب متـسیـس نودام زمرق هک ناکما تفایرد ، ،شخپزاب فذح و هدهاـشم تـسرهف لانگیـس ياه هریخذ هدـش ار زا قیرط طبار ربراک مهارف یم دنک .

# لصف 4 :

# هدایپ يزاس هناماس

پی هدا زاس ی ھناماس

رد نیا ،لـصف دنیارف هدایپ يزاـس هناماـس حیرـشت یم دوـش . سپ زا یـسررب ینابم يرظن و یحارط هناماـس رد لـصف ياه ،نیـشیپ رد نیا لـصف هوحن لیدبت یحارط هئارا هدـش هب کی هناماـس یتایلمع دروم یـسررب رارق یم دریگ . هدایپ يزاس ماجنا هدش لماش ود شخب یلصا Firmware هاگتسد و طبار يربراک تحت بو تسا . Firmware رب يور درب 32ESP و اـب هداـفتـــسا زا بوچراـچ Arduino هـعـــسوت هداد هدـــش و هـفیظو تـیریدـم ،اهرگسح شزادرپ هداد ياه ،یتفایرد لرتنک متسیس ،رادشه تفایرد و لاسرا لانگیس ياه RF و IR، تیریدم طابترا WiFi و MQTT و نینچمه هریخذ يزاـس تاعلاطا ار رب هدهع دراد . رد شخب تخـس ،يرازفا 32ESP هب هعومجم يا زا اهرگـسح و تازیهجت یبناج لماـش رگـسح امد و تبوطر 11DHT، رگـسح زاگ و دود -2MQ، رگـسح رون ینتبم رب LDR، رگـسح صیخـشت تکرح PIR، هدنریگ و هدنتـسرف RF رد دناب ياه 315 و 433 ،زترهاگم هدنریگ و هدنتـسرف نودام زمرق و رزاب لـصتم هدـش تـسا . تاعلاطا تفایرد دـش ه زا رگـسح اه طـسوت 32ESP شزادرپ هدـش و رد لـصاوف ینامز صخـشم هداتـسرف یم دوـش . رد شخب یطابترا هاگتـسد اب هدافتـسا زا WiFi هب هکبـش لـصتم هدـش و يارب لدابت هداد و تفایرد نامرف ياه یلرتنک زا لکتورپ MQTT هدافتـسا یم دنک . Broker MQTT دروم هدافتـسا رد هدایپ يزاـس ییاهن هژورپ ، سیورـس یمومع io.emqx.broker تـسا . نینچمه يارب يدنبرکیپ هیلوا و رییغت تامیظنت ،هکبش هناماسریز ینتبم رب Point Access و Portal Captive رد Firmware هدایپ يزاس هدش تسا . یکی رگید زا تیلباق ياه یلصا ،هناماس ناکما ،تفایرد هریخذ و شخپزاب لانگیـس ياه RF و IR تـسا . نیا تیلباق هاگتـسد ار زا کی هناماـس افرـص یتراظن هب کی طـساو یطابترا نایم تازیهجت یکینورتکلا و تخاـسریز دنمـشوه لیدبت یم دنک . رد ،تیاهن کی Dashboard Web يارب هدهاـشم هداد ياه ،اهرگـسح تفایرد رادـشه اه و لاـسرا نامرف ياه یلرتنک یحارط هدـش تـسا . نیا دروبـشاد امیقتـسم اب Broker MQTT طابترا رارقرب هدرک و ناکما لماعت ربراک اب هاگتـسد ار نودب زاین هب کی Backend یـصاـصتخا مهارف یم دنک .

-4-1 طیحم و رازبا ياه هعسوت

هعـسوت و هدایپ يزاـس Firmware هناماـس رب يور لوژام -32WROOM32-ESP اب هدافتـسا زا طیحم هعـسوت PlatformIO و بوچراچ مرن يرازفا Arduino ماجنا هدـش تـسا . تامیظنت طوبرم هب طیحم ،هعـسوت تاـصخـشم خـس ت يرازفا ،درب Framework دروم ،هدافتـسا تعرـس طابترا ،لایرـس متـسیـس لیاف و هناخباتک ياه زایندروم هژورپ رد لـیاـف ini.platformio فیرعت هدـــش دـنا . نیا لـیاـف هـب ناونع لـیاـف یلـــصا يدـنبرکیپ هژورپ رد PlatformIO، م طیح زاـیندروم يارب تـخاـــس و يراذـگراـب Firmware ار صخـــشم یم دـنک و ثـعاـب یم دوـــش یگتـسباو ياه مرن يرازفا و تامیظنت طوبرم هب درب هب تروـص هچراپکی رد هژورپ فیرعت دنوـش . رد نیا هژورپ زا مرفتلپ 32espressif يارب هعـسوت مرن رازفا طوبرم هب هداوناخ 32ESP هدافتـسا هدـش و Framework باختنا هدـش زین Arduino تـسا . رتماراپ platform مرفتلپ دروم هدافتـسا ار صخـشم یم دنک و رتماراپ board زین تامیظنت طوبرم هب درب ار نییعت یم دنک هک رد هژورپ رـضاح اب هجوت هب هدافتـسا زا درب یمومع DevKit 32ESP ، رادقم dev32esp يارب نآ رد رظن هتفرگ هدش تسا . يارب هاــشم هد مایپ ياه یجورخ Firmware و یــسررب تیعــضو درکلمع ،هاگتــسد طابترا لایرــس اب تعرــس baud 115200 میظنت هدـش تـسا . نیا طابترا رد لحارم ،هعـسوت شیامزآ و یبایاطخ هناماـس شقن یمهم دراد و ناکما هدهاـشم تاعلاطا طوبرم هب هار يزادنا هیلوا ،هاگتـسد تیعـضو ،اهرگـسح دنیآرف لاـصتا هب هکبـش WiFi و Broker MQTT، تـفاـیرد و يارجا ناـمرف اـه و نینچمه ماـیپ ياـه طوبرم هـب درکلمع شخب ياـه فلتخم Firmware ار مهارف یم دنک . هدافتـسا زا Monitor Serial ثعاب یم دوـش رد نامز هعـسوت ناوتب تیعـضو یلخاد

پی هدا زاس ی ھناماس

متـسیـس ار نودب زاین هب رازبا ياه یجراخ یـسررب درک و رد تروـص زورب اطخ رد شخب ییاه دننام لاصتا ،هکبش تفایرد لانگیس ياه RF و IR ای يارجا نامرف ،اه تاعلاطا مزلا يارب صیخشت لکشم رد رایتخا هعسوت هدنهد رارق دریگ .
رد شخب هریخذ يزاـس تاعلاطا یمئاد زین زا متـسیـس لیاف LittleFS هدافتـسا هدـش تـسا هک ناکما هدافتـسا زا هـظفاـح یلخاد 32ESP يارب يرادـهگن هداد ییاـه ار مهارف یم ک دـن هـک دـیاـب سپ زا شوماـخ و نـــشور ندـــش هاـگتـــسد ناـنچمه یقاـب دـنناـمب . رد نیا هژورپ زا LittleFS يارب هریخذ تاـعلاطا طوبرم هـب تاـمیظنت Provisioning، تامیظنت یلخاد هاگتـسد و نینچمه لانگیـس ياه هریخذ هدـش RF و IR هدافتـسا هدـش تـسا . ف لیا ياه طوبرم هب نیا تاعلاطا رد نامز هار يزادنا طــسوت Firmware یــسررب و رد تروــص ،دوجو تاعلاطا زایندروم زا اهنآ یبایزاب یم ؛دوـش نیاربانب رییغت تیعـضو هیذغت ای هار يزادنا ددجم هاگتـسد بجوم زا نیب نتفر تاعلاطا هریخذ هدش دهاوخن دش . سپ زا هدامآ يزاـس طیحم هعـسوت و ـصن ب هناخباتک اه و یگتـسباو ياه فیرعت هدـش رد لیاف ini.platformio، دنیارف تخاــس Firmware طــسوت PlatformIO ماجنا یم دوــش . رد نیا هلحرم دک ياه عبنم هژورپ هب هارمه هناخباتک ه يا دروم هدافتـسا لیاپماک هدش و لیاف ییارجا بسانم يارب 32ESP دیلوت یم دوش و سپ زا تیقفوم زیمآ ندوب دنیارف ،تخاــس Firmware زا قیرط طبار یطابترا بــسانم رب يور درب يراذگراب یم دوــش . سپ زا يراذگراب زین یم ناوت اب هدافتــسا زا Monitor Serial مایپ ياه یجورخ هاگتــسد ار هدهاــشم و درکلمع شخب ياه فلتخم متـسیـس ار یـسررب درک . رد ،هجیتن طیحم هعـسوت هژورپ هولاع رب رف مها ندرک رازبا ياه زایندروم يارب همانرب یــسیون و تخاــس Firmware، تاناکما مزلا يارب تیریدم یگتــسباو ،اه يراذگراب ،همانرب هریخذ يزاس تاعلاطا و یسررب درکلمع هناماس رد هلحرم هعسوت و شیامزآ ار زین رد رایتخا رارق یم دهد .

لکش (4-1 ) دنور تخاس و يراذگراب Firmware

-4-2 هدایپ يزاس تخس رازفا

رد هدایپ يزاـس تخـس يرازفا ،هناماـس ره کی زا اهرگـسح و تازیهجت یبناج هب یکی زا هیاپ ياه GPIO لوژام 32ESP لـصتم هدـش و طابترا نایم تخـس رازفا و Firmware رب ساـسا نیا تـشاگن ماجنا یم دوـش . هب روظنم يریگولج زا یگدنکارپ هرامــش هیاپ اه رد شخب ياه فلتخم انرب هم و نینچمه هداــس رت ندــش دنیارف رییغت تلااـصتا رد تروـص ،زاین یمامت هیاپ ياه دروم هدافتـسا رد لیاف يدنبرکیپ h.config فیرعت هدـش ؛دنا نیاربانب ره لوژام مرن يرازفا هب ياج هدافتـسا میقتـسم زا هرامـش ،هیاپ زا تباث فیرعت هدـش طوبرم هب نآ زیهجت هدافتـسا یم دنک و رد هجیتن رییغت کی لاـصتا تخـس يرازفا اهنت اب حلاـصا رادقم هطوبرم رد لیاف يدنبرکیپ ناکما ریذپ دهاوخ دوب . تشاگن لماک هیاپ ياه دروم هدافتسا رد لودج ( 1-3) هئارا هدش تسا

-4-2-1 هدایپ يزاس رگسح ياه یطیحم

يارب هزادنا يریگ امد و تبوطر طیحم زا رگـسح 11DHT و هناخباتک DHT Adafruit هدافتـسا هدـش تـسا . رد

پی هدا زاس ی ھناماس

ناـمز هار يزادـنا Firmware، عباـت ()setupDHT یناوخارف هدـــش و اـب يارجا ()begin.dht طاـبترا مرن رازفا اـب رگـسح هدامآ یم دوـش . سپ زا هار ،يزادنا تاعلاطا امد و تبوطر طـسوت عباوت هناگادج تفایرد یم دنوـش و رد تروص ربتعمان ندوب رادقم هدناوخ ،هدش مایپ اطخ رد Monitor Serial شیامن هداد یم دوش .

void setupDHT()
{
dht.begin();
}

float readHumidity()
{
float input = dht.readHumidity();
if (isnan(input))
{
Serial.println("Failed to read humidity from DHT sensor"); }
return input;
}

float readTemperature()
{
float input = dht.readTemperature();
if (isnan(input))
{
Serial.println("Failed to read temperature from DHT sensor"); }
return input;
}
رد نیا هداـیپ ،يزاـــس عباـت ()setupDHT اـهنت کـی راـب رد هـلحرم هار يزادـنا ارجا یم ،دوـــش رد یلاـح هـک عباوت ()readHumidity و ()readTemperature رد ناـمز هـنومن يرادرب رگـــسح یناوخارف هدـــش و رادـقم تـبوطر و يامد هزادنا يریگ هدـش ار رب یم دننادرگ . هدافتـسا زا ()isnan زین ثعاب یم دوـش رد تروـص مدع تفایرد هداد ربتعم زا ،رگسح تیعضو اطخ صخشم هدش و زا شزادرپ یب علاطا کی رادقم ربتعمان يریگولج دوش . ب يار هزادنا يریگ تدــش رون طیحم زا لوژام LDR هدافتــسا هدــش تــسا هک یجورخ نآ هب يدورو گولانآ 32ESP لـصتم هدـش و رادقم نآ طـسوت ADC هدناوخ یم دوـش . زا اجنآ هک رادقم یجورخ LDR هب تروـص ژاتلو گولانآ ،تـسا يارب لیدبت نیا رادقم هب هداد لباق شزادرپ طـسوت Firmware زا عبات ()analogRead هدافتـسا هدش تسا .

void setupLDR()
{
pinMode(LDR_PIN,INPUT);
}

int readLDR()
{
int input = analogRead(LDR_PIN);
return input;
}
عبات ()readLDR اب یناوخارف ()analogRead رادقم ADC طوبرم هب هیاپ PIN_LDR ار تفایرد هدرک و رادقم ماخ لیدبت هدش ار رب یم دنادرگ . نیا رادقم رد همادا طسوت لوژام تیریدم اهرگسح دروم هدافتسا رارق هتفرگ و

پی هدا زاس ی ھناماس

زا قیرط MQTT يارب شیامن رد دروبشاد لاسرا یم دوش . يارب صیخـشت دود و یخرب هزاگ يا لباق لاعتـشا زا رگـسح -2MQ هدافتـسا هدـش تـسا . یجورخ گولانآ رگـسح هب يدورو ADC لـصتم هدـش و رادقم نآ هب تروـص کی رادقم لاتیجید طـسوت 32ESP هدناوخ یم دوـش . زا اجنآ هک رادقم ماخ رگسح هب ییاهنت ناشن هدنهد عوقو طیارش رادشه ،تسین سپ زا تفایرد رادقم ADC ، رادقم نآ اب تسآ هنا زا شیپ نییعت هدش هسیاقم یم دوش .

void setupMQ2()
{
pinMode(MQ2_PIN, INPUT);
}

int readMQ2()
{
return analogRead(MQ2_PIN); }

bool checkThreshold(int value) {
if (value > MQ2_THRESHOLD) {
return true;
}
return false;
}
رد عبات ()2readMQ رادقم یجورخ گولانآ رگسح طسوت ADC هدناوخ یم دوش و رد عبات ()checkThreshold رادقم تفایرد هدـش اب تباث THRESHOLD_2MQ هـسیاقم یم دوـش . رد یتروـص هک رادقم هزادنا يریگ هدش زا هناتسآ نییعت هدش رتشیب ،دشاب رادقم true هدنادرگزاب هدش و متسیس یم دناوت نیا تیعضو ار هب ناونع طیارش رادـشه رد رظن دریگب . قطنم طوبرم هب لاعف ندرک رادـشه و لاـسرا تیعـضو نآ زا قیرط MQTT رد لوژام تیریدم اهرگسح و متسیس رادشه ماجنا یم دوش . يارب صیخـشت تکرح زا لوژام PIR هدافتـسا هدـش تـسا هک یجورخ لاتیجید نآ هب هیاپ صخـشم هدـش رد 32ESP لـصتم ـش هد تـسا . رد نامز هار ،يزادنا هیاپ طوبرم هب PIR هب ناونع يدورو میظنت هدـش و تیعـضو لاعف ندوب تیلباق صیخـشت تکرح زین زا هظفاح یمئاد یبایزاب یم دوـش ات میظنت باختنا هدـش طـسوت ربراک سپ زا هار يزادنا ددجم هاگتسد ظفح دوش .

void setupPIR()
{
pinMode(PIR_PIN, INPUT);

motionDetectionEnabled = loadMotionDetection();
if (motionDetectionEnabled)
{
Serial.println("Motion detection restored to ON"); }
}

int readPIR()
{
int input = digitalRead(PIR_PIN);

پی هدا زاس ی ھناماس

if (input == HIGH)
{
return 1;
}
return 0;
}
سپ زا هار ،يزادنا تیعـضو یجورخ PIR طـسوت عبات ()readPIR یـسررب یم دوـش . رد نیا ،عبات رادقم HIGH هب ناونع صیخشت تکرح و رادقم LOW هب ناونع مدع صیخشت تکرح رد رظن هتفرگ هدش تسا . هـب روظنم تـیریدـم تـیعـــضو تـیلباـق صیخـــشت ،تـکرح ود ریغتم motionDetectionEnabled و motionDetectionTriggered رد Firmware فیرعت هدش دنا هک ریغتم تسخن تیعضو لاعف ای لاعفریغ ندوب تیلباق صیخـشت تکرح ار صخـشم هدرک و ریغتم مود تیعـضو کیرحت ندـش متـسیـس رد هجیتن صیخـشت تکرح ار يرادهگن یم دنک . لاعف و لاعفریغ ندرک نیا تیلباق زین زا قیرط عباوت هطوبرم ماجنا هدـش و هولاع رب رییغت تیعـضو ،یلخاد ت میظن دیدج رد هظفاح هریخذ یم دوـش ات رد هار يزادنا يدعب زین لباق یبایزاب دـشاب . هب تروــص ،هباــشم يارب لاعفریغ ندرک تیلباق صیخــشت ،تکرح تیعــضو یلخاد رییغت هدرک و رادقم دیدج رد هظفاح هریخذ یم دوـش . رد ،هجیتن تیعـضو صیخـشت تکرح اهنت رد یتروـص یم دناوت بجوم داجیا رادـشه ـش دو هک رادقم motionDetectionEnabled لاعف دشاب و رد تروص ییاسانش ،تکرح تیعضو متسیس طسوت لوژام تیریدم اهرگـسح شزادرپ و رد تروـص زاین زا قیرط MQTT هب دروبـشاد ملاعا دهاوخ دـش . تایئزج هدایپ يزاـس نیا شخب رد لیاف cpp.pir/PIR/src رارق دراد .

-4-2-2 هدایپ يزاس متسیس رادشه یتوص

يارب داجیا رادــشه یتوــص زا کی Buzzer Active هدافتــسا هدــش تــسا هک اب قطنم Low-Active لرتنک یم ؛دوـش هب نیا ینعم هک رارق نتفرگ هیاپ یجورخ رد حطـس یقطنم LOW ثعاب لاعف ندـش رزاب و رارق نتفرگ نآ رد حطــس HIGH بجوم لاعفریغ ندــش نآ یم دوــش . رد نامز هار يزادنا Firmware، یاپ ه رزاب هب ناونع یجورخ میظنت هدــش و يارب يریگولج زا لاعف ندــش هتــساوخان ،رزاب تیعــضو نآ رد تلاح شوماخ رارق یم دریگ .

void setupBuzzer()
{
pinMode(BUZZER_PIN, OUTPUT); stopAlarm();
}

void startAlarm()
{
alarmActive = true;
buzzerOn = true;
lastBuzzerToggle = millis(); digitalWrite(BUZZER_PIN, LOW); }

void stopAlarm()
{
alarmActive = false;

پی هدا زاس ی ھناماس

buzzerOn = false;
digitalWrite(BUZZER_PIN, HIGH);
}
عبات ()startAlarm هفیظو لاعف ندرک تیعـضو رادـشه ار رب هدهع دراد و اب هجوت هب Low-Active ندوب ،رزاب هـیاـپ هـطوبرم ار رد حطـــس LOW رارق یم ،دـهد رد یلاـح هـک عباـت ()stopAlarm اـب رارق نداد هـیاـپ رد حطـــس HIGH رزاب ار لاعفریغ یم دنک . زا اجنآ هک رادـشه یتوـص هناماـس هب تروـص هتـسویپ لاعف یمن دوـش و يارب داجیا يوگلا ،رادـشه رزاب دیاب رد هزاب ياه ینامز صخـشم نـشور و شوماخ ،دوـش عبات ()updateAlarm رد هقلح یلـصا Firmware یناوخارف یم دوـش و رب ساـسا تیعـضو ینامز ،متـسیـس یجورخ رزاب ار رییغت یم دهد . رد ،هجیتن رد تروص لاعف ندوب ،رادشه رزاب قباطم هخرچ ینامز فیرعت هدش لاعف و لاعفریغ دش ه و رد تروص نایاپ طیارـش ،رادـشه هب تلاح شوماخ زاب یم ددرگ . تایئزج لماک هدایپ يزاـس متـسیـس رادـشه یتوـص رد لیاف . دراد رارق src/Alarm/alarm.cpp

-4-3 هدایپ يزاس متسیس طابترا ییویدار RF

یکی زا تیلباق ياه یلـصا ،هناماـس ناکما ،تفایرد هریخذ يزاـس و شخپزاب لانگیـس ياه ییویدار RF تـسا هک اـب فدـه مهارف ندرک ناـکما لرتنک تازیهجت یکیرتکلا زهجم هـب لرتنک زا هار رود رد نیا هژورپ هداـیپ يزاـــس هدـش تـسا . رد یحارط ماجنا ،هدـش متـسیـس RF زا ود دناب یـسناکرف 315 و 433 زترهاگم ینابیتـشپ یم دنک و يارب ره کی زا نیا دناب اه کی ریـسم لقتـسم يارب ایرد تف و لاـسرا لانگیـس رد رظن هتفرگ هدـش تـسا . زا اجنآ هک هدنریگ اه و هدنتـسرف ياه دروم هدافتـسا هب تروـص کت سناکرف لمع یم ،دننک يارب تیریدم ره دناب کی هنومن لقتـسم زا سلاک RCSwitch رد Firmware داجیا هدـش تـسا و نیدب بیترت متـسیـس یم دناوت لانگیـس ياه ود دناب ار هب تروـص م لقتـس تفایرد و شخپزاب دنک . تیریدم طابترا اب لوژام ياه RF زین اب هدافتـسا زا هناخباتک RCSwitch ماجنا هدــش تــسا هک ناکما تفایرد و لاــسرا دک ياه جیار تازیهجت RF ار رد رایتخا Firmware رارق یم دهد .
دنیارف هار يزادنا متـسیـس RF رد عبات ()setupRF ماجنا یم دوـش و رد نیا م هلحر هدنریگ و هدنتـسرف طوبرم هب ره ود دـناـب لاـعف یم دـنوـــش . رد ،هـجیتن سپ زا يارجا نیا ،عباـت ره ود هدـنریگ يارب تـفاـیرد لاـنگیـــس و ره ود هدنتــسرف يارب لاــسرا لانگیــس هدامآ دنهاوخ دوب . هیاپ ياه دروم هدافتــسا يارب نیا تازیهجت زین رد لیاف يدنبرکیپ هژورپ فیرعت هدـش دنا ات ن تـشاگ هیاپ اه زا قطنم یلـصا همانرب ادج دـشاب و رد تروـص رییغت رادم تخس ،يرازفا زاین هب رییغت شخب ياه فلتخم Firmware دوجو هتشادن دشاب .

void setupRF()
{
rfSwitch433.enableReceive(RF_RX_433_PIN); rfSwitch433.enableTransmit(RF_TX_433_PIN); rfSwitch315.enableReceive(RF_RX_315_PIN); rfSwitch315.enableTransmit(RF_TX_315_PIN);
}
يارب يرادهگن تاعلاطا لانگیـس ياه تفایرد ،هدـش يراتخاـس اب مان RFSignal فیرعت هدـش تـسا هک رتماراپ ياه یلـصا زایندروم يارب ،ییاـسانـش هریخذ و شخپزاب لانگیـس ار رد دوخ يرادهگن یم دنک . رد نیا ،راتخاـس ریغتم name مان صاــصتخا هداد هدــش هب ،لانگیــس code دک تفایرد ،هدــش bits دادعت تیب ياه ،لانگیــس protocol هرامـش لکتورپ صیخـشت هداد ،هدـش pulse لوط سلاپ و band دناب یـسناکرف لانگیـس ار صخـشم یم دنک . تاعلاطا لانگیـس ياه تفایرد هدـش رد هیارآ signals يرادهگن یم دنوـش و دادعت رـصانع ربتعم نیا

پی هدا زاس ی ھناماس

هیارآ زین طـسوت ریغتم signalCount صخـشم یم ـش دو . هدافتـسا زا نیا راتخاـس ثعاب هدـش تـسا تاعلاطا طوبرم هب ره لانگیـس هب تروـص کی هعومجم مجـسنم ن يرادهگ دوـش و تایلمع تـسج و ،وج ،فذح هریخذ يزاس و شخپزاب نآ هداس رت ماجنا دریگ .

RFSignal signals[MAX_SIGNALS];
size_t signalCount = 0;

struct RFSignal
{
String name;
uint32_t code;
uint16_t bits;
uint16_t protocol;
uint16_t pulse;
uint16_t band;
};

-4-3-1 تفایرد و هریخذ يزاس لانگیس RF

دنیارف تفایرد لانگیـس طـسوت عبات ()readRFSignal ماجنا یم دوـش . نیا ،عبات تیعـضو هدنریگ ياه 315 و 433 زترهاگم ار یــسررب هدرک و رد تروــص تفایرد ،لانگیــس هدنریگ يا هک لانگیــس ار تفایرد هدرک تــسا ییاـسانـش یم دنک . سپ زا ییاـسانـش هدنریگ ،لاعف رتماراپ ياه لانگیـس زا قیرط API هناخباتک RCSwitch جارختـسا هدـش و رد تروـص ربتعم ندوب ،هداد تاعلاطا طوبرم هب لانگیـس رد نیلوا تیعقوم دازآ هیارآ signals رارق یم دریگ . سپ زا ناـیاـپ شزادرپ زین هدـنریگ هـب تـیعـــضو بـــساـنم هدـنادرگزاـب یم دوـــش اـت ناـکما تـفاـیرد لانگیس يدعب مهارف دشاب .
تیریدم یلک دنیارف تفایرد و هریخذ يزاـس طـسوت عبات ()handleRFReceive ماجنا یم ؛دوـش هب نیا تروـص هک ادتبا تیعـضو متـسیـس زا رظن لاعف ندوب تلاح تفایرد یـسررب هدـش و سپ زا تفایرد قفوم ،لانگیـس تلاح تفایرد لاعفریغ هدـش و تاعلاطا هب تـسد هدمآ يارب هریخذ يزاـس یمئاد رد رایتخا شخب تیریدم هظفاح رارق یم دریگ . ،نیاربانب تفایرد لانگیـس و هریخذ يزاـس نآ هب تروـص ود هلحرم ازجم ماجنا هدـش تـسا هک نیا عوـضوم ثعاب کیکفت نم بـسا یلوئـسم ت اه رد راتخاـس Firmware یم دوـش . ایئزج ت لماک هدایپ يزاـس نیا شخب رد لیاف ياه cpp.receiver/RF/src و cpp.general/RF/src لباق هدهاشم تسا .

-4-3-2 شخپزاب و تیریدم لانگیس RF

يارب شخپزاب لانگیــس ياه هریخذ ،هدــش عبات ()transmitRFSignal دروم هدافتــسا رارق یم دریگ . رد نیا دنیارف ادتبا دوجو لانگیـس رظندروم و ربتعم ندوب رتماراپ ياه هریخذ هدـش یـسررب هدـش و سپـس رب ساـسا رادقم band، هدنتـسرف بـسانم باختنا یم دوـش . سپ زا باختنا ،هدنتـسرف لکتورپ و لوط سلاپ هریخذ هدـش هب نآ صاـصتخا هداد هدـش و رد تیاهن دک و ت دادع تیب ياه لانگیـس يارب لاـسرا رد رایتخا هناخباتک RCSwitch رارق یم دریگ . هب نیا ،بیترت ربراک ماگنه لاـسرا ددجم کی لانگیـس اهنت یفاک تـسا مان نآ ار صخـشم دنک و باختنا هدنتسرف و رتماراپ ياه دروم زاین طسوت Firmware ماجنا یم دوش .

پی هدا زاس ی ھناماس

هب روظنم یسرتسد هب لانگیس ياه ریخذ ه ،هدش عبات ()findRFSignalByName يارب تسج و يوج لانگیس رب ساـسا مان نآ هدایپ يزاـس هدـش تـسا . نیا عبات رـصانع ربتعم هیارآ signals ار زا ادتبا ات اهتنا یـسررب یم دنک و رد تروـص ادیپ ندـش یلانگیـس اب مان ،رظندروم ناکم نآ ار رب یم ؛دنادرگ رد یتروـص هک لانگیـس رظندروم رد هظفاح دوجو هتشادن ،دشاب رادقم nullptr هدنادرگزاب یم دوش .

RFSignal *findRFSignalByName(const String &name)
{
for (size_t i = 0; i < signalCount; i++)
{
if (signals[i].name == name)
{
return &signals[i];
}
}
return nullptr;
}
يارب فذح کی لانگیـس زین ادتبا اب هدافتـسا زا نیمه عبات دوجو لانگیـس یـسررب یم دوـش و سپ زا ادیپ ندـش ،نآ تیعقوم لانگیـس رد هیارآ صخـشم یم دوـش . سپـس رـصانع هتفرگرارق سپ زا نآ کی تیعقوم هب تمـس پچ لقتنم یم دنوــش ات ياــضف یلاخ اجیا د هدــش فذح دوــش و رادقم signalCount زین کی دحاو شهاک ادیپ یم دنک . رد ،همادا هیارآ دیدج رد هظفاح یمئاد هریخذ یم دوش .

RFSignal *signal = findRFSignalByName(name);
if (signal == nullptr)
{
Serial.println("RF signal not found"); return;
}

size_t index = signal - signals;
for (size_t i = index; i + 1 < signalCount; i++) {
signals[i] = signals[i + 1];
}
signalCount--;

if (saveRFSignals())
{
Serial.print("Deleted RF signal: "); Serial.println(name);
}
else
{
loadRFSignals();
Serial.println("Failed to delete RF signal");
}
نینچمه يارب شیامن تـسرهف لانگیـس ياه هریخذ ،هدـش عبات ()listRFSignals هدایپ يزاـس هدـش تـسا هک تاعلاطا لانگیـس اه ار لماـش ،مان دناب ،یـسناکرف ،دک دادعت تیب و لکتورپ جارختـسا هدرک و هولاع رب شیامن رد Monitor Serial، تاعلاطا ار رد بلاق JSON زا قیرط MQTT رـشتنم یم دنک . تاعلاطا نیا شخب زا قیرط Topic طوبرم هب list/RF رشتنم یم دوش .

پی هدا زاس ی ھناماس

تایئزج لماک هدایپ يزاـس نیا شخب رد لیاف cpp.transmitter/RF/src و cpp.general.RF/src لباق ـشم ا هده تسا .

-4-3-3 قطنم یلک تفایرد و ا لاسر RF

دنیارف تفایرد لانگیس رد هناماس هب تروص ریز تسا :


لکش (4-2 ) دنیارف تفایرد لانگیس RF

دنیارف لاسرا لانگیس رد هناماس هب تروص ریز تسا :

لکش (4-3 ) دنیارف لاسرا لانگیس RF

-4-4 هدایپ يزاس متسیس نودام زمرق IR

یکی رگید زا تیلباق ياه یلـصا ،هناماـس ناکما ،تفایرد هریخذ يزاـس و شخپزاب نامرف ياه نودام زمرق تـسا هک اب فده مهارف ندرک ناکما لرتنک یتازیهجت دننام ،نویزیولت متـسیـس ياه ،هیوهت شخپ هدننک اه و ریاـس تازیهجت یگناخ زهجم هب لرتنک زا هار رود نودام زمرق رد هژورپ هدایپ يزاــس هدــش تــسا . رد نیا ،شخب کی هدنریگ نودام زمرق يارب تفایرد انگیــس ل ياه یلاــسرا زا لرتنک اه و راهچ LED نودام زمرق يارب شخپزاب

پی هدا زاس ی ھناماس

لانگیـس ياه هریخذ هدـش دروم هدافتـسا رارق هتفرگ تـسا . ،شزادرپ صیخـشت لکتورپ و لاـسرا لانگیـس ياه IR طـسوت هناخباتک 8266IRremoteESP ماجنا یم دوـش و راتخاـس مرن يرازفا متـسیـس هب هنوگ يا یحارط هدـش تـسا هک هولاع بر لانگیـس ياه لباق Decode، ناکما هریخذ و شخپزاب لانگیـس ياه هتخانـشان هب تروـص هداد ماخ زین دوجو هتشاد دشاب .
يارب تیریدم شخب تفایرد و ،لاسرا کی یش زا سلاک IRrecv و کی یش زا سلاک IRsend داجیا هدش تسا هک هب بیترت لوئـسم تفایرد و Decode ندرک لانگیـس ياه نودام زمرق و هدامآ يزاـس و لاـسرا ددجم اهنآ دنتـسه . هار يزادنا نیا ود شخب رد عبات ()setupIR ماجنا یم دوـش . اب يارجا نیا ،عبات هدنریگ IR يارب تفایرد لانگیـس هدامآ هدـش و شخب لاـسرا زین هار يزادنا یم دوـش ات رد همادا Firmware دناوتب رب ساـسا نامرف ياه تفایرد ،هدش تایلمع رد تفای ای لاسرا لانگیس ار ماجنا دهد .

IRrecv irReceiver(IR_RX_PIN);
IRsend irTransmitter(IR_TX_PIN);

void setupIR()
{
irReceiver.enableIRIn();
irTransmitter.begin();
}
يارب يرادهگن تاعلاطا لانگیـس ياه تفایرد ،هدـش يراتخاـس اب مان IRSignal فیرعت هدـش تـسا هک هولاع رب تاعلاطا Decode ،هدـش هداد ماخ لانگیـس ار زین رد دوخ يرادهگن یم دنک . رد نیا ،راتخاـس ریغتم name مان صاـصتخا هداد هدـش هب ،لانگیـس protocol عون لکتورپ صیخـشت هداد ،هدـش value رادقم Decode ،هدـش bits دادـعت تـیب ياـه ،لاـنگیـــس rawLength دادـعت هـنومن ياـه هداد ماـخ و rawData هـیارآ طوبرم هـب هداد ماـخ لانگیـس ار يرادهگن یم دنک . هدافتـسا نامزمه زا تاعلاطا Decode هدـش و هداد ماخ تیمها ،دراد اریز همه لانگیـس ياه نودام زمرق امازلا طـسوت هناخباتک هب کی لکتورپ هتخانـش هدـش لباق صیخـشت دنتـسین و رد نینچ یطیارـش يارب شخپزاب حیحـص لانگیـس دیاب تاعلاطا ماخ نآ ظفح دوـش . لانگیـس ياه تفایرد هدـش رد هیارآ irSignals يرادهگن هدش و دادعت لانگیس ياه ربتعم زین طسوت ریغتم irSignalCount صخشم یم دوش . يارب هریخذ لاطا تاع لانگیس ياه نودام ،زمرق راتخاس IRSignal فیرعت هدش تسا :

IRSignal irSignals[MAX_SIGNALS];
size_t irSignalCount = 0;

struct IRSignal
{
String name;
decode_type_t protocol;
uint64_t value;
uint16_t bits;
uint16_t rawLength;
uint16_t rawData[MAX_IR_RAW_LENGTH]; };

-4-4-1 تفایرد و هریخذ يزاس لانگیس IR

دنیارف تفایرد و Decode لانگیــس نودام زمرق طــسوت عبات ()readIRSignal ماجنا یم دوــش . رد نیا دنیارف

پی هدا زاس ی ھناماس

ادتبا کی راتخاـس results_decode يارب يرادهگن هجیتن تفایرد و Decode داجیا هدـش و هدنریگ IR ـسررب ی یم دنک هک ایآ لانگیــس يدیدج تفایرد هدــش تــسا ای ریخ . سپ زا تفایرد ،لانگیــس ياهرتماراپ طوبرم هب تیعــضو تفایرد زا هلمج overflow و لوط هداد ماخ یــسررب یم دنوــش ات زا ربتعم ندوب تاعلاطا نانیمطا لـصاح دوـش . رد تروـص ربتعم ندوب ،هداد کی تیعقوم دازآ رد هیارآ irSignals خا صاـصت هداد هدـش و تاعلاطا طوبرم هب ،لکتورپ رادقم Decode ،هدش دادعت تیب اه و هداد ماخ لانگیس رد راتخاس هطوبرم هریخذ یم دنوش . یکی زا تاکن مهم رد نیا هدایپ ،يزاس هریخذ يزاس هداد ماخ رد رانک تاعلاطا Decode هدش ؛تسا اریز نکمم تـسا لکتورپ کی لرتنک زا هار رود طـسوت هناخباتک 8266IRremoteESP ییاـسانـش ،دوـشن اما لکـش جوم تفایرد هدـش نانچمه لباق شخپزاب دـشاب . ،نیاربانب يرادهگن هیارآ rawData ثعاب یم دوـش هناماـس دودحم هب لکتورپ ياه هتخانـش هدـش دـشابن و دناوتب رد تروـص هتخانـشان ندوب لکتورپ زین لانگیـس تفایرد هدـش ار رد بلاق ماخ هریخذ دنک .
تیریدم یلک دنیارف تفایرد طـسوت عبات ()handleIRReceive ماجنا یم دوـش . نیا عبات ادتبا یـسررب یم دنک هک متـسیـس رد تلاح تفایرد IR رارق هتـشاد دـشاب و رد تروـص تفایرد قفوم ،لانگیـس تلاح تفایرد ار لاعفریغ هدرک و تاعلاطا هب تـسد هدمآ ار يارب هریخذ يزاـس یمئاد رد رایتخا شخب تیریدم هظفاح رارق یم دهد . رد ،هجیتن تفایرد کی لانگیـس سپ زا يارجا نامرف هطوبرم اهنت ات نامز تفایرد نیلوا لانگیـس ربتعم همادا ادیپ یم دنک و سپ زا هریخذ ،تاعلاطا متسیس هب تلاح يداع يارجا Firmware زاب یم ددرگ . تایئزج هدایپ يزاس نیا شخب رد لیاف ياه cpp.receiver/IR/src و cpp.general/IR/src لباق هدهاشم تسا .

-4-4-2 شخپزاب و تیریدم لانگیس IR

يارب شخپزاب لانگیـس ياه هریخذ ،هدـش عبات ()transmitIRSignal دروم هدافتـسا رارق یم دریگ . رد يادتبا نیا دنیارف دوجو لانگیـس رظندروم و ربتعم ندوب تاعلاطا نآ یـسررب هدـش و سپـس رب ساـسا رادقم protocol، شور بـسانم يارب لاـسرا باختنا یم دوـش . رد یتروـص هک لکتورپ لانگیـس طـسوت Firmware ینابیتـشپ ،دوـش تاعلاطا Decode هدـش اب هدافتـسا زا ر شو لاـسرا طوبرم هب نامه لکتورپ لقتنم یم دوـش و رد یتروـص هک لکتورپ هتخانـشان دـشاب ای ناکما لاـسرا نآ هب تروـص Decode هدـش دوجو هتـشادن ،دـشاب هداد ماخ هریخذ هدـش رد rawData اب سناکرف لماح 38 زترهولیک شخپزاب یم دوش . رد هخــسن یلعف Firmware، لکتورپ ياه جیار NEC، SONY، SAMSUNG و PANASONIC ینابیتــشپ یم دنوـش و يارب ریاـس لانگیـس ،اه رد تروـص دوجو هداد ماخ ،ربتعم شور لاـسرا ماخ دروم هدافتـسا رارق یم دریگ . نیا شور ثعاب یم دوـش تیلباق شخپزاب هناماـس اهنت هب لکتورپ ياه هتخانـش هدـش دودحم دـشابن و ناکما هریخذ و هدافتــسا ددجم زا یخرب لانگیــس ییاه هک طــسوت هناخباتک لباق Decode دنتــسین زین مهارف دوش .
يارب ادیپ ندرک لانگیـس رب ساـسا ،مان عبات ()findIRSignalByName هدایپ يزاـس هدـش تـسا . نیا عبات رـصانع ربتعم هیارآ irSignals ار زا ادتبا ات اهتنا یـسررب یم دنک و رد تروـص ادیپ ندـش یلانگیـس اب مان ،رظندروم ناکم نآ ار رب یم ؛دنادرگ رد یتروـص هک لانگیـس رظندروم رد هظفاح دوجو هتـشادن ،دـشاب رادقم nullptr هدنادرگزاب یم دوش .

IRSignal *findIRSignalByName(const String &name)
{
for (size_t i = 0; i < irSignalCount; i++)

پی هدا زاس ی ھناماس

{
if (irSignals[i].name == name) {
return &irSignals[i];
}
}
return nullptr;
}
يارب فذح کی لانگیـس زین اب هدافتـسا زا نیمه عبات دوجو لانگیـس یـسررب یم دوـش و سپ زا ادیپ ندـش ،نآ تیعقوم لانگیـس رد هیارآ صخـشم یم دوـش . سپـس رـصانع هتفرگرارق سپ زا نآ کی تیعقوم هب تمـس پچ لقتنم یم دنوــش ات ياــضف یلاخ داجیا هدــش فذح دوــش و رادقم irSignalCount زین کی دحاو شهاک ادیپ یم دنک . رد ،همادا هیارآ دیدج رد هظفاح یمئاد هریخذ یم دوش .

IRSignal *signal = findIRSignalByName(name);
if (signal == nullptr)
{
Serial.println("IR signal not found"); return;
}

size_t index = signal - irSignals;
for (size_t i = index; i + 1 < irSignalCount; i++) {
irSignals[i] = irSignals[i + 1];
}
irSignalCount--;

if (saveIRSignals())
{
Serial.print("Deleted IR signal: "); Serial.println(name);
}
else
{
loadIRSignals();
Serial.println("Failed to delete IR signal");
}
نینچمه يارب شیامن تـسرهف لانگیـس ياه هریخذ ،هدـش عبات ()listIRSignals رد رظن هتفرگ هدـش تـسا هک تاعلاطا ره لانگیــس لماــش ،مان ،لکتورپ دادعت تیب و لوط هداد ماخ ار جارختــسا هدرک و هولاع رب شیامن رد Monitor Serial، اهنآ ار رد بلاق کی یــش JSON امآ هد هدرک و زا قیرط MQTT رــشتنم یم دنک . تاعلاطا تـسرهف لانگیـس اه زا قیرط Topic طوبرم هب list/IR رد رایتخا دروبـشاد رارق یم دریگ و رد هجیتن ربراک یم دناوت نودب یسرتسد میقتسم هب هظفاح ،هاگتسد لانگیس ياه هریخذ هدش ار هدهاشم و تیریدم دنک . تایئزج هدایپ يزاس رد لیاف cpp.transmitter/IR/src و cpp.general/IR/src لباق هدهاشم تسا .

پی هدا زاس ی ھناماس

-4-4-3 قطنم یلک تفایرد و لاسرا IR

دنیارف تفایرد لانگیس رد هناماس هب تروص ریز تسا :

لکش (4-4 ) دنیارف تفایرد لانگیس IR

دنیارف لاسرا لانگیس رد هناماس هب تروص ریز تسا :


لکش (4-5 ) دنیارف لاسرا لانگیس IR

-4-5 هدایپ يزاس طابترا WiFi و MQTT

هب روظنم داجیا طابترا نایم هاگتـسد و تخاـسریز مرن يرازفا ،هناماـس زا ود يروانف WiFi و MQTT هدافتـسا هدش تسا هک رد نیا ،راتخاس طابترا WiFi هفیظو لاصتا 32ESP هب هکبش یلحم و مهارف ندرک ریسم یطابترا نایم هاگتـسد و Broker MQTT ار رب هدهع دراد و لکتورپ MQTT زین يارب لدابت تاعلاطا ،اهرگـسح تیعـضو متـسیـس و نامرف ياه یلرتنک نایم 32ESP، Broker و دروبـشاد تحت بو دروم هدافتـسا رارق یم دریگ . هدایپ يزاـس نیا شخب هب هنوگ يا ماجنا هدـش تـسا هک عطق ای للاتخا تقوم رد طابترا هکبـش ثعاب فقوت درکلمع شخب ياه یلحم متسیس هدشن و Firmware دناوتب رد نامز بسانم يارب يرارقرب ددجم طابترا شلات دنک .

-4-5-1 داجیا و هار يزادنا Client MQTT

يارب هدایپ يزاـس طابترا MQTT زا هناخباتک PubSubClient هدافتـسا هدـش تـسا و رد يادتبا ،لوژام کی یـش زا سلاک WiFiClient هب ناونع تخاـسریز طابترا هکبـش و کی یـش زا سلاک PubSubClient يارب تیریدم طابترا MQTT داجیا هدــش ؛تــسا نینچمه هب روظنم يزاــسادج قطنم تفایرد مایپ زا شخب ،یطابترا کی Callback يارب تفایرد نامرف ياه MQTT فیرعت هدش تسا .

پی هدا زاس ی ھناماس

static WiFiClient wifiClient;
static PubSubClient mqttClient(wifiClient);
static MqttCommandHandler mqttCommandHandler = nullptr;
هفیظو هار يزادنا هیلوا طابترا MQTT طـسوت عبات ()setupMQTT ماجنا یم دوـش هک رد نآ Handler طوبرم هب نامرف اه تبث ،هدـش تاـصخـشم Broker MQTT زا تامیظنت Provisioning ای ریداقم شیپ ضرف هدناوخ هدش و سپس تاصخشم رورس يارب Client MQTT میظنت یم دوش .

void setupMQTT(MqttCommandHandler commandHandler)
{
mqttCommandHandler = commandHandler;

const char *host = provisioningConfig.mqttHost.length() > 0 ? provisioningConfig.mqttHost.c_str() : MQTT_HOST;
uint16_t port = provisioningConfig.mqttPort > 0
? provisioningConfig.mqttPort
: MQTT_PORT;

WiFi.setAutoReconnect(true); connectWiFi();
mqttClient.setServer(host, port); mqttClient.setCallback(mqttCallback); }

-4-5-2 يرارقرب و تیریدم لاصتا WiFi و MQTT

لاـصتا 32ESP هب هکبـش WiFi طـسوت عبات ()connectWiFi ماجنا یم دوـش هک ادتبا تیعـضو یلعف هکبـش ار یـسررب هدرک و رد تروـص لـصتم ندوب ،هاگتـسد زا داجیا لاـصتا ددجم يریگولج یم ؛دنک رد ریغ نیا ،تروـص تاصخشم هکبش زا تامیظنت هریخذ هدش Provisioning تفایرد هدش و رد تروص دوبن تاعلاطا ،ربتعم ریداقم ضرفشیپ دروم هدافتسا رارق یم دنریگ و رد تیاهن لاصتا هب هکبش اغآ ز یم دوش .

static void connectWiFi()
{
if (WiFi.status() == WL_CONNECTED) {
return;
}

const char *ssid = provisioningConfig.wifiSSID.length() > 0
? provisioningConfig.wifiSSID.c_str()
: WIFI_SSID;
const char *wpass = provisioningConfig.wifiPassword.length() > 0 ? provisioningConfig.wifiPassword.c_str() : WIFI_PASSWORD;

WiFi.begin(ssid, wpass);
}
سپ زا يرارقرب طابترا WiFi، لاـصتا هب Broker MQTT طـسوت عبات ()connectMQTT ماجنا یم دوـش . رد

پی هدا زاس ی ھناماس

نیا عبات ادتبا تاـصخـشم Broker لماـش ،سردآ ،تروپ مان يربراک و زمر روبع زا تامیظنت Provisioning ای ریداقم ضرفـشیپ تفایرد هدـش و سپـس اب هجوت هب دوجو ای مدع دوجو تاعلاطا زارحا ،تیوه شور بسانم يارب لاـصتا باختنا یم دوـش . سپ زا لاـصتا ،قفوم هاگتـسد رد Topic طوبرم هب نامرف اه Subscribe یم دنک ات دناوتب نامرف ياه لاـسرا هدـش زا تمـس دروبـشاد ای ریاـس Publisher اه ار تفایرد دنک . هب نیا ،بیترت 32ESP هولاع رب شقن Publisher يارب سرا لا تاعلاطا ،اهرگسح هب ناونع Subscriber زین رد متسیس MQTT تیلاعف یم دنک .

static bool connectMQTT()
{
const char *host = provisioningConfig.mqttHost.length() > 0
? provisioningConfig.mqttHost.c_str() : MQTT_HOST;
uint16_t port = provisioningConfig.mqttPort > 0
? provisioningConfig.mqttPort
: MQTT_PORT;
const char *mqttUser = provisioningConfig.mqttUser.length() > 0
? provisioningConfig.mqttUser.c_str()
: MQTT_USER;
const char *mqttPass = provisioningConfig.mqttPassword.length() > 0 ? provisioningConfig.mqttPassword.c_str() : MQTT_PASSWORD;

bool connected = false;
if (strlen(mqttUser) > 0)
{
connected = mqttClient.connect(MQTT_CLIENT_ID, mqttUser, mqttPass); }
else
{
connected = mqttClient.connect(MQTT_CLIENT_ID); }

if (!connected)
{
Serial.print("MQTT connect failed, state="); Serial.println(mqttClient.state());
return false;
}

String commandTopic = topicFor(MQTT_COMMAND_TOPIC); mqttClient.subscribe(commandTopic.c_str());
return true;
}
هب روظنم يریگولج زا فقوت همانرب رد تروـص عطق ،طابترا تیریدم لاـصتا رد لوط يارجا عبات ()loop طـسوت ()handleMQTT ماجنا یم دوـش . نیا عبات ادتبا تیعـضو WiFi و سپـس تیعـضو Broker MQTT ار یـسررب هدرک و رد تروــص عطق ندوب ره ،کی سپ زا تــشذگ هزاب ینامز صخــشم ،هدــش اددجم يارب ب يرارقر طابترا شلات یم ؛دنک رد یتروص هک طابترا رارقرب دشاب زین عبات ()loop.mqttClient ارجا یم دوش ات مایپ ياه دیدج تفایرد وCallback ياه هطوبرم شزادرپ دنوش .

void handleMQTT()
{

پی هدا زاس ی ھناماس

if (WiFi.status() != WL_CONNECTED)
{
unsigned long now = millis();
if (now - lastReconnectAttempt >= MQTT_RECONNECT_INTERVAL) {
lastReconnectAttempt = now;
connectMQTT();
}
return;
}

if (!mqttClient.connected())
{
unsigned long now = millis();
if (now - lastReconnectAttempt >= MQTT_RECONNECT_INTERVAL) {
lastReconnectAttempt = now;
connectMQTT();
}
return;
}

mqttClient.loop();
}

-4-5-3 تفایرد و راشتنا نامرف ياه MQTT

يارب تفایرد نامرف ياه MQTT زا Callback فیرعت هدـش رد نامز هار يزادنا Client هدافتـسا هدـش تـسا . نیا عبات Payload یتفایرد ار زا هیارآ تیاب هب کی هتـشر ینتم لیدبت ،هدرک هلـصاف ياه یفاـضا ار فذح یم دنک و سپــس نامرف لــصاح ار هب mqttCommandHandler لقتنم یم دیامن ات قطنم طوبرم هب شزادرپ نامرف رد شخب يرگید زا Firmware ماجنا دوـش . رد نیا ،راتخاـس لوژام MQTT لوئـسم صیخـشت عون نامرف ای يارجا میقتـــسم نآ ،تـــسین هـکلب اـهنت هـفیظو تـفاـیرد ماـیپ و لاـقتنا نآ هـب Handler هـطوبرم ار رب هدـهع ؛دراد نیا يزاـسادج بجوم شهاک یگتـسباو نایم شخب یطابترا و قطنم یلرتنک متـسیـس هدـش و ناکما هعـسوت نامرف ياه دیدج ار نودب داجیا تارییغت هدرتسگ رد لوژام MQTT مهارف یم دنک .

static void mqttCallback(char *topic, byte *payload, unsigned int length) {
String command;
command.reserve(length + 1);

for (unsigned int i = 0; i < length; i++)
{
command += static_cast<char>(payload[i]); }

command.trim();

پی هدا زاس ی ھناماس

Serial.print("MQTT command on "); Serial.print(topic);
Serial.print(": ");
Serial.println(command);

if (command.length() > 0 && mqttCommandHandler != nullptr) {
mqttCommandHandler(command);
}
}
يارب راـشتنا تاعلاطا زین عبات ()publishMQTT رد رظن هتفرگ هدـش تـسا هک ادتبا تیعـضو لاـصتا هب Broker ار یـسررب هدرک و رد تروـص رارقرب ندوب ،طابترا Topic ییاهن ار اب هدافتـسا زا Topic هیاپ متـسیـس داجیا و Payload ار رد نآ رشتنم یم دنک .

bool publishMQTT(const String &subTopic, const String &payload, bool retained)
{
if (!mqttClient.connected())
{
return false;
}

String topic = topicFor(subTopic);
return mqttClient.publish(topic.c_str(), payload.c_str(), retained); }

-4-6 هدایپ يزاس يدنبرکیپ هیلوا و تیریدم لاصتا هب هکبش

هب روظنم يریگولج زا یگتــسباو میقتــسم تامیظنت هکبــش و Broker MQTT هب Firmware و مهارف ندرک ناکما هدافتـسا زا هناماـس رد هکبـش ياه ،فلتخم کی ریز هناماـس لقتـسم اب ناونع Provisioning رد Firmware یحارط و هدایپ يزاس هدش تسا هک هفیظو نآ ، ،تفایرد ،یجنسرابتعا هریخذ يزاس و یبایزاب تاعلاطا زایندروم يارب لاـصتا 32ESP هب هکبـش WiFi و Broker MQTT ؛تـسا هب کمک نیا ،هناماـسریز ربراک یم دناوت نودب زاین هب رییغت رد دک همانرب ای لیاپماک ددجم Firmware، تاـصخـشم ،هکبـش تاعلاطا MQTT و مان هاگتسد ار زا قیرط کی طبار تحت بو میظنت هدرک و تامیظنت دیدج ار رد هظفاح یمئاد هاگتسد هریخذ دنک .

-4-6-1 راتخاس تاعلاطا و هار يزادنا

تاعلاطا طوبرم هب يدنبرکیپ یطابترا هاگتـسد رد يراتخاـس اب مان ProvisioningConfig يرادهگن یم دنوـش هک لماــش مان و زمر روبع هکبــش WiFi، سردآ و تروپ Broker MQTT، تاعلاطا زارحا تیوه MQTT و مان یصاصتخا هاگتسد تسا .

struct ProvisioningConfig
{
String wifiSSID;
String wifiPassword;

پی هدا زاس ی ھناماس

String mqttHost;
uint16_t mqttPort;
String mqttUser;
String mqttPassword;
String client;
};
راتخاــس قوف ثعاب یم دوــش مامت تاعلاطا زایندروم يارب يرارقرب طابترا هکبــش رد کی راتخاــس صخــشم و زکرمتم رارق هتـشاد دـشاب و ریاـس شخب ياه Firmware دنناوتب نودب ریگرد ندـش اب تایئزج طوبرم هب تفایرد ای هریخذ يزاــس ،تاعلاطا تامیظنت زایندروم دوخ ار زا نیا راتخاــس تفایرد دننک . تاــصخــشم ياهریغتم نیا راتخاس رد دج لو ریز هئارا هدش تسا .

لودج (4-1 ) راتخاس هداد تامیظنت Provisioning
| | | ریغتم عون هداد دربراک
يرابجا | AP مان | String | wifiSSID
يرابجا | | | wifiPassword String زمر روبع WiFi
| MQTT Broker سردآ | String | mqttHost يرابجا
| MQTT Broker تروپ | uint16_t | mqttPort يرابجا
| MQTT Broker يربراک مان | String | mqttUser يرایتخا
| MQTT Broker روبع زمر | String | mqttPassword يرایتخا
| مان هاگتسد يرابجا | | client String
يارب مهارف ندرک ناـکما يدـنبرکیپ ،هاـگتـــسد 32ESP رد تـلاـح STA_AP_WIFI رارق یم دریگ هـک رد نیا تلاح یم دناوت هب تروـص نامزمه هب هکبـش WiFi یلـصا هب ناونع Station لـصتم هدـش و کی Point Access یـصاـصتخا زین يارب ماجنا تامیظنت داجیا ؛دنک نیاربانب لاعف ندوب AP هب لاصتا هاگتسد هب هکبش یلصا هتسباو تـسین و ربراک یم دناوت یتح رد ینامز هک هاگتـسد هب هکبـش لـصتم تـسا زین هب طبار Provisioning یـسرتـسد هتـشاد ب دـشا و تامیظنت نآ ار رییغت دهد . تاـصخـشم Point Access داجیا هدـش رد ( لودج 4-3 ) رکذ هدـش تـسا . سپ زا لاصتا ربراک هب نیا Point Access، کی Server Web يور 32ESP ارجا هدش و ص هحف يدنبرکیپ زا قیرط سردآ 192.168.4.1 رد رایتخا ربراک رارق یم دریگ .

پی هدا زاس ی ھناماس

-4-6-2 هدایپ يزاس Portal Captive و تیریدم تساوخرد ياه HTTP

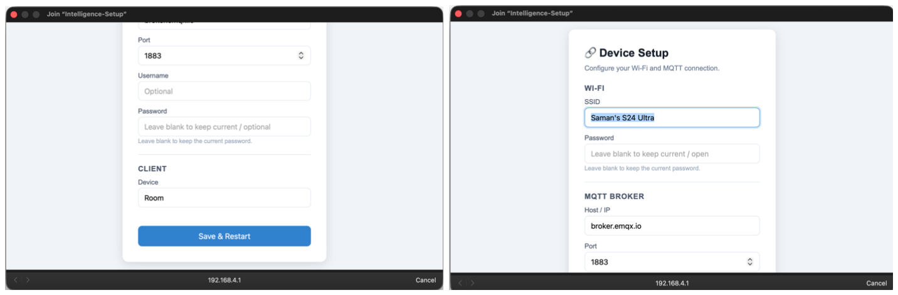
[picture p53: figure]

لکش (4-6 ) هحفص تامیظنت

يارب هداس رت ندش دنیارف ،يدنبرکیپ رد هژورپ زا مزیناکم Portal Captive هدافتسا هدش تسا . يارب نیا روظنم کی Server DNS داجیا هدــش و یمامت تــساوخرد ياه DNS هب سردآ IP طوبرم هب Point Access تیاده یم دنوـش . رد لوژام Provisioning ياهریـسم یفلتخم يارب تیریدم تـساوخرد ياه HTTP فیرعت هدـش تـسا هک ریـسم / هفیظو شیامن هحفـص یلـصا ،تامیظنت ریـسم save/ هفیظو تفایرد تاعلاطا لاـسرا هدـش طـسوت ربراک و ریـسم handleNotFound زین هفیظو تیاده تـساوخرد ياه هتخانـشان هب هحفـص يدنبرکیپ ار رب هدهع ؛دراد هولاع رب ،نیا هب روظنم ییاـسانـش راکدوخ Portal Captive طـسوت متـسیـس لماع ياه ،فلتخم ریـسم ییاه دننام 204_generate/ يارب Android ، ریـسم html.detect-hotspot/ يارب Apple و ریـسم ياه txt.ncsi/ و txt.connecttest/ يارب Windows زین هب هحفص يدنبرکیپ تیاده یم دنوش .

server.on("/", HTTP_GET, handleRoot);
// OS connectivity-check probes — redirecting them (instead of returning the // expected "success"/204 response) is what makes the captive portal pop up
// automatically on iOS / Android / Windows.
server.on("/generate_204", HTTP_GET, redirectToPortal); | // Android
server.on("/gen_204", HTTP_GET, redirectToPortal); | // Android (alt)
server.on("/hotspot-detect.html", HTTP_GET, redirectToPortal); // Apple
server.on("/ncsi.txt", HTTP_GET, redirectToPortal); | // Windows
server.on("/connecttest.txt", HTTP_GET, redirectToPortal); | // Windows
server.on("/redirect", HTTP_GET, redirectToPortal); | // Windows
server.on("/save", HTTP_POST, handleSave);
server.onNotFound(handleNotFound);
اب هدافتـسا زا نیا ،راتخاـس ینامز هک ربراک هب Point Access هاگتـسد لـصتم یم ،دوـش متـسیـس لماع اب لاـسرا تـساوخرد ياه یـسررب ،لاـصتا دوجو کی هکبـش ياراد Portal Captive ار صیخـشت هداد و 32ESP هب ياج خـساپ ،يداع ربراک ار هب هحفـص يدنبرکیپ تیاده یم ؛دنک رد ،هجیتن رد يرایسب زا هاگتسد اه هحفص تامیظنت نودب زاین هب دراو ندرک یتـسد سردآ IP رد رگرورم شیامن هداد یم دوـش و دنیارف يدنبرکیپ يارب ربراک هداـس رت دهاوخ دوب .

پی هدا زاس ی ھناماس

-4-6-3 تفایرد ، یجنسرابتعا و هریخذ تامیظنت

سپ زا شیامن هحفــص ،يدنبرکیپ ربراک تاعلاطا طوبرم هب هکبــش WiFi و Broker MQTT ار دراو هدرک و اب لاــسرا ،مرف تــساوخرد POST هب ریــسم save/ لاــسرا یم ؛دوــش عبات ()handleSave تاعلاطا یتفایرد ار شزادرپ ،هدرک کی هنومن دیدج زا ProvisioningConfig داجیا یم دنک و سپــس ریداقم دراو هدــش ار زا رظن دوجو ياهرتماراپ يرورــض یــسررب یم ،دیامن هب يروط هک رد تروــص یلاخ ندوب مان هکبــش WiFi، سردآ Broker MQTT ای مان ،هاگتسد تساوخرد ربتعم صیخشت هداد هدشن و اب ياطخ 400 HTTP در یم دوش . یکی زا تاکن مهم رد نیا هدایپ ،يزاـس هوحن تیریدم زمر ياه روبع ؛تـسا رد یتروـص هک ربراک دلیف طوبرم هب زمر روبع WiFi ای MQTT ار یلاخ لاـسرا ،دنک رادقم یلبق زمر روبع ظفح یم دوـش و هب نیا ،بیترت زمر ياه هریخذ هدـش رد هظفاح يزاین هب شیامن ددجم رد طبار يربراک دنرادن و ربراک يارب رییغت ریاـس تامیظنت روبجم هب دراو ندرک ددجم زمر یلعف هاوخن د دوب . سپ زا دـییأـت راـبتعا ،تاـعلاطا تاـمیظنت دـیدـج طـــسوت عباـت ()saveProvisioningConfig رد هـظفاـح یمئاد متـسیـس هریخذ هدـش و سپـس هاگتـسد Restart یم دوـش ات Firmware اب هدافتـسا زا تامیظنت ،دیدج دنیارف لاـصتا هب هکبـش و Broker MQTT ار زا ادتبا ماجنا دهد . تاعلاطا هریخذ دـش ه سپ زا هار يزادنا ددجم طـسوت متسیس Provisioning یبایزاب هدش و رد رایتخا لوژام ياه WiFi و MQTT رارق یم ؛دنریگ نیاربانب تامیظنت امعا ل هدش سپ زا شوماخ و نشور ندش هاگتسد زین ظفح دنهاوخ دش . تایئزج لماک هدایپ يزاس نیا شخب رد لیاف cpp.provisioning/Provisioning/src لباق هدهاشم تسا .

-4-7 هدایپ يزاس تیریدم هظفاح و هریخذ يزاس تاعلاطا

رد نیا ،هژورپ هب روظنم ظفح تاعلاطا دروم زاین هناماـس سپ زا شوماخ و نـشور ندـش 32ESP، زا متـسیـس لیاف LittleFS هدافتـسا هدـش تـسا هک ناکما هریخذ يزاـس تاعلاطا رد هظفاح یلخاد هاگتـسد ار نودب زاین هب هـظفاـح یجراـخ مهارف یم دـنک . لوژاـم تـیریدـم هـظفاـح تـیلوئـــسم هریخذ يزاـــس و یباـیزاـب تاـعلاطا فلتخم هناماـس لماـش تامیظنت Provisioning، تیعـضو لاعف ای لاعفریغ ندوب صیخـشت تکرح و نینچمه نگیـس لا ياه هریخذ هدـش RF و IR ار رب هدهع دراد و هب نیا بیترت ریاـس لوژام ياه Firmware یم دنناوت نودب ریگرد ندـش اب تایئزج هوحن یـسرتـسد هب ،هظفاح تاعلاطا زایندروم دوخ ار زا قیرط عباوت هطوبرم هریخذ ای یبایزاب دننک .
يارب یهدراتخاــس تاعلاطا هریخذ هدــش زین زا هناخباتک ArduinoJson هدافتــسا هدــش ؛تــسا رد نیا ،شور تاعلاطا شیپ زا هریخذ يزاــس هب راتخاــس JSON لیدبت هدــش و رد لیاف هطوبرم رارق یم دنریگ و ماگنه هار يزادنا ای زاین هب یبایزاب ،تاعلاطا لیاف JSON هدناوخ هدــش و هداد ياه نآ اددجم هب اهراتخاــس و ریغتم ياه دروم هدافتـسا Firmware ت لیدب یم دنوـش . نیا شور هولاع رب هداـس رت ندرک تیریدم ،تاعلاطا ثعاب یم دوـش راتخاس لیاف ياه هریخذ هدش اناوخ و لباق هعسوت دشاب . شیپ زا هنوگره تایلمع ندناوخ ای ،نتـشون هدامآ ندوب متـسیـس لیاف طـسوت عبات یلخاد ()ensureLittleFS یــسررب یم دوــش ات رد تروــص Mount ندوبن LittleFS، تایلمع هار يزادنا زایندروم ماجنا هدــش و زا يارجا تایلمع يور کی متسیس لیاف هدامآ هدشن يریگولج دوش .

پی هدا زاس ی ھناماس

-4-7-1 هریخذ و یبایزاب تیعضو هاگتسد

یکی زا یتاعلاطا هک دیاب سپ زا Restart هاگتـسد ظفح ،دوـش تیعـضو لاعف ای لاعفریغ ندوب تیلباق صیخـشت تـکرـح ؛تــــسا هـب نـیـمـه روـظـنـم نـیا رادـقـم رد لـیاـف json.settings/ هرـیـخذ یـم دوـــش و عـباـت ()saveMotionDetection هفیظو لیدبت تیعـضو یلعف هب هداد JSON و هریخذ نآ ار رب هدهع ،دراد رد یلاح هک عبات ()loadMotionDetection ماگنه هار يزادنا هاگتـسد لیاف ار هدناوخ و تیعـضو یلبق ار یبایزاب یم دنک و رد یتروـص هک لیاف تامیظنت دوجو هتـشادن ،دـشاب رادقم ضرفـشیپ يارب تیعـضو صیخـشت تکرح ربارب اب لاعفریغ رد رظن هتفرگ یم دوش . تایئزج هدایپ يزاس نیا شخب رد لیاف cpp.memmory/Memmory/src لباق هاشم هد تسا .

-4-7-2 هریخذ و یبایزاب لانگیس ياه RF و IR

لانگیـس ياه RF تفایرد هدـش طـسوت متـسیـس رد لیاف json.signals_rf/ و لانگیـس ياه نودام زمرق تفایرد هدـش زین رد لیاف json.signals_ir/ هریخذ یم دنوـش و راتخاـس هریخذ يزاـس اهنآ هب هنوگ يا یحارط هدش تسا هک تاعلاطا یلــصا زایندروم يارب شخپزاب لانگیــس رد رانک مان یــصاــصتخا نآ يرادهگن دوــش . يارب هریخذ لانگیـس ياه RF، عبات ()saveRFSignals ادتبا کی هیارآ JSON داجیا هدرک و سپـس يارب ره رـصنع دوجوم رد هیارآ signals کی یـش JSON داجیا یم دنک و رتماراپ ییاه دننام ،مان ،دک دادعت ،تیب ،لکتورپ لوط لاپ س و دناب یـسناکرف ار رد نآ رارق یم دهد و رد تیاهن هیارآ داجیا هدـش رد لیاف json.signals_rf/ هریخذ یم دوش . هب تروص ،هباشم عبات ()loadRFSignals ماگنه هار يزادنا هاگتسد لیاف هریخذ هدش ار زاب هدرک و هیارآ JSON ار یم دناوخ و سپـس تاعلاطا ره رـصنع ار جارختـسا هدرک و رد هیارآ signals رارق یم دهد ات لانگیـس اه يارب هدافتسا رد تایلمع تسج و وج و شخپزاب رد سرتسد Firmware رارق هتشاد دنشاب . رد دروم لانگیـس ياه IR زین دنیارف یهباـشم ماجنا یم ،دوـش اب نیا توافت هک هولاع رب علاطا تا Decode هدـش دننام ،لکتورپ رادقم لانگیـس و دادعت ،تیب تاعلاطا ماخ لانگیـس زین رد لیاف هریخذ یم دوـش ات رد تروـص هتخانـشان ندوب لکتورپ ای مدع ینابیتـشپ هناخباتک زا ،نآ ناکما شخپزاب لانگیـس نانچمه دوجو هتـشاد دـشاب . رد ناـمز هار يزادـنا زین ()loadIRSignals تاـعلاطا جوم دو رد json.signals_ir/ ار یباـیزاـب هدرک و رد هـیارآ irSignals رارق یم دهد ات لانگیس ياه یلبق IR رد رایتخا متسیس رارق هتشاد دنشاب . تایئزج هدایپ يزاس نیا شخب رد لیاف cpp.memmory/Memmory/src لباق هدهاشم تسا .

-4-8 هار يزادنا و یگنهامه لوژام اه

هتـسه یلـصا Firmware لماـش ود عبات ()setup و ()loop تـسا هک هب بیترت هفیظو هار يزادنا هیلوا و يارجا موادم هناماـس ار رب هدهع دنراد . عبات ()setup اهنت کی راب سپ زا نـشور ندش 32ESP ارجا هدش و رد نآ طابترا ،لایرـس تامیظنت هریخذ ،هدـش Point Access طوبرم هب Provisioning، اهرگـسح و طابترا MQTT هار يزادنا یم ؛دنوـش سپ زا نایاپ نیا ،هلحرم لرتنک همانرب هب عبات ()loop لقتنم یم دوـش هک هب تروـص هتـسویپ ارجا هدش و فیاظو فلتخم هناماس ار رد لوط نامز تیریدم یم دنک .

void setup()

پی هدا زاس ی ھناماس

{
Serial.begin(115200);
delay(200);

loadProvisioningConfig();
startConfigAP();

setupSensors();
setupMQTT(handleMqttCommand);
printHelp();
}
رد يادتبا دنیارف هار ،يزادنا طابترا لایرــس اب تعرــس baud 115200 رارقرب یم دوــش ات مایپ ياه طوبرم هب تیعـضو متـسیـس و تایلمع ماجنا هدـش رد Monitor Serial لباق هدهاـشم دنـشاب . سپـس تامیظنت طوبرم هب هکبش WiFi و MQTT هک رد هظفاح یلخاد هریخذ هدش ،دنا طسوت عبات ()loadProvisioningConfig یبایزاب هدـش و Point Access یـصاـصتخا متـسیـس طـسوت ت عبا ()startConfigAP لاعف یم دوـش . رد ،همادا عبات ()setupSensors هفیظو هدامآ يزاـــس اهرگـــسح و تازیهجت یبناج لماـــش 11DHT، -2MQ، LDR، PIR، Buzzer، متـسیـس RF، متـسیـس IR و LED تیعـضو ار رب هدهع دراد و تاعلاطا لانگیـس ياه هریخذ هدـش RF و IR زین رد نیمه هلحرم زا هظفاح یبایزاب یم دنوـش . سپ زا هدامآ يزاـس يازجا تخـس ،يرازفا طابترا MQTT اب هدافتــسا زا عبات ()setupMQTT میظنت هدــش و رد تیاهن تــسرهف نامرف ياه لباق هدافتــسا طــسوت عبات ()printHelp رد رایتخا ربراک رارق یم دریگ .

void loop()
{
handleSerial();
handleMQTT();
handleConfigAP();
handleSensors();
}
سپ زا لـیمکت تاـیلمع هار ،يزادـنا عباـت loop هـب تروـــص موادـم ارجا یم دوـــش و یگنهاـمه ناـیم شخب ياـه فلتخم Firmware ار ماـجنا یم دـهد . رد ره هـخرچ يارجا نیا ،عباـت ادـتبا يدورو ياـه تـفاـیرد هدـــش زا Serial Monitor شزادرپ ،هدـش سپـس تیعـضو طابترا MQTT یـسررب و مایپ ياه دیدج تفایرد یم دنوـش . رد همادا تـساوخرد ياه طوبرم هب لاتروپ يدنبرکیپ شزادرپ هدـش و رد تیاهن عبات ()handleSensors هفیظو تیریدم ،اهرگـسح تیعـضو ،رادـشه LED، تفایرد لانگیـس ياه RF و IR و راـشتنا تاعلاطا اهرگـسح ار ماجنا یم دهد . نیا راتخاـس ثعاب یم دوـش فیاظو فلتخم متـسیـس هب تروـص لقتـسم رد لوژام ياه هطوبرم هدایپ يزاـس هدـش و عبات ()loop اهنت شقن گنهامه هدننک نایم نیا شخب اه ار هتشاد دشاب .

void setupSensors()
{
setupMQ2();
setupDHT();
setupPIR();
setupBuzzer();
setupRF();
setupIR();
setupLDR();
nextMQ2ReadAt = millis() + MQ2_PREHEAT_DURATION; loadRFSignals();

پی هدا زاس ی ھناماس

loadIRSignals();
setupStatusLED();
}
هار يزادنا تازیهجت تخـس يرازفا طـسوت عبات ()setupSensors ماجنا یم دوـش . رد نیا ،عبات ادتبا يازجا طوبرم هب ياهرگـسح -2MQ، 11DHT، PIR و LDR هار يزادنا هدـش و سپـس متـسیـس رادـشه ،یتوـص هدنریگ اه و هدنتـسرف ياه RF و متـسیـس نودام زمرق هدامآ هب راک یم دنوـش . يارب رگـسح -2MQ، نامز نیلوا شناوخ اب هجوت هب تدم نامز شیپ شیامرگ نییعت یم دوــش . رد همادا لانگیــس ياه هریخذ هدــش RF و IR زا هظفاح یلخاد یبایزاب هدش و LED تیعضو زین هار يزادنا یم دوش .

-4-8-1 تیریدم نامرف ياه متسیس

یکی زا خب ش ياـه مهم Firmware، ناـکما لرتنک تـیلباـق ياـه فلتخم هاـگتـــسد زا قیرط ناـمرف ياـه ینتم تـسا . نیا نامرف اه یم دنناوت زا قیرط Monitor Serial ای MQTT تفایرد هدـش و سپ زا شزادرپ طـسوت Handler Command، تایلمع رظانتم اب اهنآ ارجا دوـش . راتخاـس نامرف اه هب هنوگ يا یحارط هدـش تـسا هک تیلباق ياه فلتخم ،هناماـس زا هلمج متـسیـس RF، متـسیـس IR، رادـشه یتوـص و صیخـشت ،تکرح زا قیرط کی طبار ینامرف كرتشم لباق لرتنک دنشاب .

-4-8-1-1 تیریدم نامرف ياه RF و IR رد تروـص تفایرد نامرف <name <rx rf، ادتبا مان لانگیـس یـسررب هدـش و رد تروـص ربتعم ندوب ،تـساوخرد متـسیـس دراو اح تل تفایرد RF یم دوـش ات لانگیـس یتفایرد اب مان نییعت هدـش هریخذ دوـش . رد نامرف tx rf <name<، لانگیـس رظندروم رد نایم لانگیـس ياه هریخذ هدـش تـسج و وج هدـش و رد تروـص ،دوجو طـسوت هدنتـسرف بـسانم شخپزاب یم دوـش . نامرف list rf زین تـسرهف لانگیـس ياه هریخذ هدـش ار شیامن هداد و تاعلاطا اهنآ ار زا قیرط MQTT رد رایتخا دروبــشاد رارق یم ،دهد رد یلاح هک نامرف <name <del rf يارب فذح لانگیس صخشم زا هظفاح دروم هدافتسا رارق یم دریگ . نامرف ياه طوبرم هب متـسیـس نودام زمرق زین زا راتخاـس یهباـشم هدافتـسا یم دننک . هب نیا ،بیترت ربراک یم دناوت کی لانگیـس IR ار اب مان هاوخلد تفایرد و هریخذ ،دنک لانگیـس هریخذ هدـش ار شخپزاب ،دنک لانگیـس وم رظندر ار فذح هدرک ای تسرهف لانگیس ياه هریخذ هدش ار هدهاشم دنک . تایئزج شزادرپ نیا نامرف اه رد لیاف cpp.serial/Serial/src هدایپ يزاس هدش تسا .

-4-8-1-2 تیریدم نامرف ياه متسیس رادشه و صیخشت تکرح رد تروـص تفایرد on buzzer، عبات ()startAlarm ارجا هدـش و رادـشه یتوـص لاعف یم دوـش و رد تروـص تفایرد off buzzer، عبات ()stopAlarm هفیظو لاعفریغ ندرک نآ ار رب هدهع دراد . هولاع رب لرتنک میقتـــسم طـسوت ،ربراک لاعف ندـش رادـشه یم دناوت رد هجیتن دادیور ياه رگـسح -2MQ ای صیخـشت تکرح زین ماجنا دوـش . اب يارجا on motion تیلباق صیخـشت تکرح لاعف و اب يارجا off motion لاعفریغ یم دوـش . تیعـضو نیا تیلباق هولاع رب رییغت رد هظفاح ،ییارجا رد هظفاح یمئاد زین هریخذ یم دوــش ات سپ زا هار يزادنا ددجم ،هاگتسد تیعضو یلبق لباق یبایزاب دشاب . تایئزج شزادرپ نیا نامرف اه رد لیاف cpp.serial/Serial/src هدایپ يزاس هدش تسا .

پی هدا زاس ی ھناماس

-4-8-2 تیریدم اهرگسح و فیاظو هرود يا

تیریدم هرود يا اهرگـسح و ریاـس فیاظو هتـسباو هب نامز رد عبات ()handleSensors ماجنا یم دوـش . نیا عبات رد ره هخرچ زا ()loop یناوخارف هدـش و تیعـضو تفایرد RF و IR، متـسیـس ،رادـشه LED ياه تیعـضو و صیخـشت تکرح ار یـسررب یم دنک و رد تروـص ندیـسر نامز هنومن ،يرادرب تاعلاطا اهرگـسح ار تفایرد و رشتنم یم دنک .

void handleSensors()
{
handleRFReceive(receivingRF, receiveName); handleIRReceive(receivingIR, receiveName); updateAlarm();
updateStatusLED();
updatePulseLED();
checkMotionDetection();
printSensors();
}
رد يادتبا يارجا ،عبات تیعـضو تفایرد لانگیـس ياه RF و IR یـسررب یم دوـش ات رد تروـص رارق نتـشاد متـسیـس رد تلاح ،تفایرد هداد دیدج شزادرپ و هریخذ دوـش . سپـس و تیعـض رادـشه و LED ياه متـسیـس یناـسرزورب هدـش و تیلباق صیخـشت تکرح یـسررب یم دوـش . رد تیاهن عبات ()printSensors هفیظو یـسررب نامز هنومن يرادرب و تفایرد ریداقم اهرگـسح ار رب هدهع یم دریگ و هداد ياه هب تـسد هدمآ ار يارب راـشتنا زا قیرط MQTT هدامآ یم دنک .
يارب يریگولج زا شناوخ شیب زا هزادـنا اـهرگـــسح و لاـــسرا موادـم ماـیپ هـب Broker MQTT، هـنومن يرادرب اهرگسح اب کی هزاب ینامز صخشم ماجنا یم دوش . رد هدایپ يزاس ،یلعف تاعلاطا ياهرگسح 11DHT، LDR و PIR اب هلصاف ینامز 10 هیناث یسررب و رد تروص ندیسر نامز هنومن ،يرادرب داقم ری دیدج زا قیرط MQTT رـشتنم یم دنوـش . رگـسح -2MQ هب لیلد زاین هب شیپ ،شیامرگ قطنم ینامز یلقتـسم دراد و نیلوا شناوخ نآ سپ زا نایاپ تدم شیپ شیامرگ ماجنا یم دوش . تایئزج هدایپ يزاس نیا شخب رد لیاف cpp.sensors/Sensors/src لباق هدهاشم تسا .

پی هدا زاس ی ھناماس

-4-9 هدایپ يزاس دروبشاد بو و ار طب يربراک


لکش (4-7 ) دروبشاد بو

هب روظنم مهارف ندرک کی طبار يربراک بـسانم يارب هدهاـشم تیعـضو ،هناماـس تفایرد تاعلاطا ،اهرگـسح هدهاـشم دادیور ياه رادـشه و لاـسرا نامرف ياه ،یلرتنک کی دروبـشاد تحت بو يارب هژورپ یحارط و هدایپ يزاـس هدـش تـسا . نیا دروبـشاد هب تروـص less-Server یحارط هدـش و يارب لدابت تاعلاطا نایم طبار يربراک و 32ESP، ًامیقتـسم هب Broker MQTT لـصتم یم ؛دوـش زا اجنآ هک رگرورم اه ناکما يرارقرب طابترا میقتـسم اب MQTT يور لکتورپ TCP ار ،دنرادن طابترا دروبـشاد اب Broker زا قیرط WebSocket over MQTT ماجنا یم دوـش . رد ،هجیتن د دروبـشا نودب زاین هب کی Backend یـصاـصتخا یم دناوت مایپ ياه رـشتنم هدـش طـسوت 32ESP ار تفایرد هدرک و نامرف ياه رظندروم ربراک ار زین رد Topic طوبرم هب هاگتسد رشتنم دنک .

-4-9-2 لاصتا هب Broker MQTT و تفایرد تاعلاطا

رد شخب تاـمیظنت ،دروبـــشاد رتماراـپ ياـه زاـیندروم يارب يرارقرب طاـبترا اـب Broker MQTT رد راـیتخا ربراـک رارق هتفرگ تـسا . ربراک یم دناوت سردآ Broker، تروپ ،یطابترا مان يربراک و زمر روبع و نینچمه عون طابترا WebSocket ار صخـشم دنک . دروبـشاد زا ود تلاح WebSocket و (WSS (Secure WebSocket ینابیتـشپ یم دنک هک ناکما هدافتسا زا طابترا یلومعم ای طابترا يراگنزمر هدش ار مهارف یم دزاس . سپ زا يرارقرب ،لاـصتا دروبـشاد رد Topic ياه طوبرم هب هاگتـسد Subscribe یم دنک و مایپ ياه یتفایرد ار هب تروــص هظحل يا شزادرپ یم دیامن . هداد ياه طوبرم هب ياهرگــسح 11DHT، LDR، PIR و -2MQ رد Topic ياه صخشم م رشتن هدش و دروبشاد سپ زا تفایرد ره ،مایپ Topic نآ ار یسررب هدرک و رادقم تفایرد

پی هدا زاس ی ھناماس

هدـش ار رد شخب طوبرم هب نامه رگـسح شیامن یم دهد . هب نیا ،بیترت رییغت ریداقم اهرگـسح نودب زاین هب Refresh ندرک هحفص رد طبار يربراک شیامن هداد یم دوش . يارب شیازفا تیلباق یـسررب و یلحت ل هداد ،اه يارب رگـسح ياه ياراد یجورخ ،يددع رادومن تارییغت زین رد رظن هتفرگ هدـش تـسا ات ربراک دناوتب دنور تارییغت تاعلاطا رگـسح ار رد لوط نامز هدهاـشم دنک . نینچمه هب روظنم يریگولج زا شیامن هداد ییاه هک نکمم تـسا طوبرم هب نامز هتـشذگ ،دنـشاب نامز نیرخآ تفایرد مایپ ره رگـسح رد دروبـشاد تبث یم دوـش و رد یتروـص هک رتـشیب زا 30 هیناث زا نیرخآ مایپ تفایرد هدـش هتـشذگ ،دشاب هداد هطوبرم هب ناونع Data Stale ای هداد یمیدق تملاع يراذگ یم دوش .

-4-9-3 لاسرا مرف نا و تیریدم تیعضو هناماس

دروبـشاد هولاع رب شیامن ،تاعلاطا ناکما لاـسرا نامرف ياه یلرتنک هب 32ESP ار زین مهارف یم دنک . نامرف اه رد Topic طوبرم هب تاروتـسد رـشتنم هدـش و سپ زا تفایرد طـسوت 32ESP، هب Handler Command لقتنم یم دنوـش ات تایلمع رظانتم اب اهنآ ارجا دوـش . زا قیرط نیا ،شخب ربراک یم دناوت تیلباق ياه فلتخم متـسیـس ار نودـب هداـفتـــسا زا Monitor Serial لرتنک دـنک . اـب هداـفتـــسا زا نیا ناـمرف ،اـه ربراـک یم دـناوت زا قیرط طبار یکیفارگ دروبـشاد کی لانگیـس دیدج تفایرد و هریخذ ،دنک لانگیـس هریخذ هدـش ار شخپزاب ،دیامن لانگیـس یصخشم ار فذح دنک ای تسرهف لانگیس ياه دوجوم ار هدهاشم دیامن . تسرهف لانگیس اه سپ زا فایرد ت زا Topic ياه list/RF و list/IR رد شخب هطوبرم شیامن هداد یم دوـش و هب نیا بیترت تیریدم لانگیـس ياه هریخذ هدـش نودب زاین هب یـسرتـسد میقتـسم هب هاگتـسد ناکما ریذپ تـسا . نینچمه لرتنک متـسیـس رادـشه و تیلباق صیخشت تکرح زین زا قیرط دروبشاد ماجنا یم دوش . يارب شیامن دادیور ياه ،مهم کی شخب رادـشه رد تمـسق ییلااب دروبـشاد یحارط هدـش تـسا هک مایپ ياه طوبرم هب صیخـشت تکرح و روبع رادقم -2MQ زا هناتـسآ نییعت هدـش ار هب ربراک شیامن یم دهد . نیا شخب ثعاب یم دوـش دادیور ياه مهم متـسیـس رد رانک تاعلاطا ع يدا اهرگـسح لباق هدهاـشم هدوب و ربراک دناوتب رد هاتوک نیرت نامز تبسن هب تیعضو يداعریغ شنکاو ناشن دهد .

# لصف 5 :

# نومزآ و یبایزرا متسیس

زرا و نومزآ ی با ی سی متس

سپ زا یحارط و هدایپ يزاـس شخب ياه تخـس يرازفا و مرن يرازفا ،هناماـس درکلمع یلک متـسیـس رد طیارـش فلتخم دروم نومزآ و یباـیزرا رارق تـفرگ اـت زا تـحـــص درکلمع يازجا فلتخم و یگنهاـمه ناـیم لوژاـم ياـه تخـس يرازفا و مرن يرازفا نانیمطا لـصاح دوـش . رد نیا ،دنیارف درکلمع ،اهرگـسح متـسیـس ،رادـشه طابترا WiFi و MQTT، تیلباق Provisioning، تفایرد و شخپزاب لانگیـس ياه RF و IR، هریخذ زاـس ي تاعلاطا رد هظفاح یلخاد و نینچمه درکلمع دروبـشاد بو یـسررب دـش . نومزآ اه هب هنوگ يا ماجنا دندـش هک هولاع رب یـسررب درکلمع لقتـسم ره ،شخب هوحن لماعت لوژام اه اب رگیدکی و شنکاو هناماـس رد طیارـش فلتخم زین دروم یبایزرا رارق دریگ .

-5-1 شور نومزآ و یبایزرا هناماس

هب روظنم یبایزرا درکلمع هناماــس و یــسررب تحــص درکلمع شخب ياه فلتخم ،نآ نومزآ اه رب يور درب هعـسوت DevKit 32ESP و اب هدافتـسا زا تازیهجت تخـس يرازفا هب راک هتفر رد هنومن ییاهن ماجنا هدـش تـسا . رد شخب هزادنا يریگ رتماراپ ياه ،یطیحم زا رگـسح 11DHT يارب هزادنا يریگ امد و ،تبوطر لوژام LDR يارب هزادنا يریگ تدــش ،رون یجورخ گولانآ رگــسح -2MQ يارب صیخــشت دود و زاگ ياه لباق لاعتــشا و لوژام PIR يارب صیخـشت تکرح هدافتـسا هدـش تـسا . نینچمه يارب یـسررب درکلمع متـسیـس ،رادـشه کی Buzzer Active و يارب شیاـمزآ تـیلباـق لرتنک تازیهجت ياراد لرتنک زا هار ،رود هـعومجم هدـنتـــسرف و هدنریگ RF رد ود دناب یسناکرف 315 و 433 زترهاگم و هعومجم هدنریگ و هدنتسرف نودام زمرق دروم هدافتسا رارق هتفرگ تــسا . نومزآ ياه مرن يرازفا زین اب هدافتــسا زا Broker MQTT، دروبــشاد بو و طبار Serial Monitor ماجنا هدـش دنا ات هولاع رب درکلمع لقتـسم ره ،شخب طابترا نایم يازجا فلتخم هناماـس زین دروم یسررب رارق دریگ .
يارب یبایزرا ،هناماس رایعم ییاه رد رظن هتفرگ هدش تسا هک مه درکلمع تخس رازفا و مه درکلمع یطابترا و مرن يرازفا متـسیـس ار شـشوپ یم دنهد . رد شخب تخـس ،يرازفا تحـص تفایرد تاعلاطا زا رگـسح ياه ،یطیحم صیخـشت حیحـص طیارـش رادـشه و درکلمع متـسیـس رادـشه یتوـص یـسررب هدـش تـسا . رد شخب ،یطابترا تحـص لاـصتا 32ESP هب هکبـش Fi-Wi، يرارقرب طابترا اب Broker MQTT و تفایرد حیحـص نامرف ياه یلرتنک دروم یبایزرا رارق هتفرگ تـسا . نینچمه تیلباق ،تفایرد هریخذ يزاـس و شخپزاب لانگیـس ياه RF رد ره ود دناب 315 و 433 زترهاگم و تیلباق ،تفایرد هریخذ يزاــس و شخپزاب لانگیــس ياه IR دروم نومزآ رارق هتفرگ تــسا . رد ،همادا درکلمع متــسیــس Provisioning لماــش داجیا Point Access، شیامن Portal Captive، تفایرد و هریخذ تامیظنت و يرارقرب لاـصتا رب ساـسا تامیظنت دیدج یـسررب هدـش و رد تیاهن درکلمع دروبــشاد بو زا رظن تفایرد هدنز تاعلاطا ،اهرگــسح شیامن ،اهرادــشه لاــسرا نامرف اه و تیریدم لانگیس ياه هریخذ هدش یبایزرا هدش تسا .

-5-2 نومزآ درکلمع اهرگسح

هب روظنم یـسررب تحـص درکلمع شخب هزادنا يریگ و صیخـشت طیارـش ،یطیحم ره کی زا رگـسح اه ي دروم هدافتـسا رد هناماـس هب تروـص لقتـسم دروم نومزآ رارق دنتفرگ . رد نیا نومزآ اه ادتبا راتفر رگـسح رد طیارـش يداع یـسررب هدـش و سپـس اب داجیا رییغت رد رتماراپ یطیحم ،رظندروم خـساپ رگـسح و هوحن شزادرپ تاعلاطا طـسوت Firmware یبایزرا دـش . هولاع رب یـسررب رادقم ماخ تفایرد هدـش زا ،اهرگـسح هوحن لاـسرا تاعلاطا زا

زرا و نومزآ ی با ی سی متس

قیرط MQTT و درکلمع قطنم رادشه رد طیارش نییعت هدش زین دروم یسررب رارق تفرگ .

-5-2-1 نومزآ رگسح امد و تبوطر

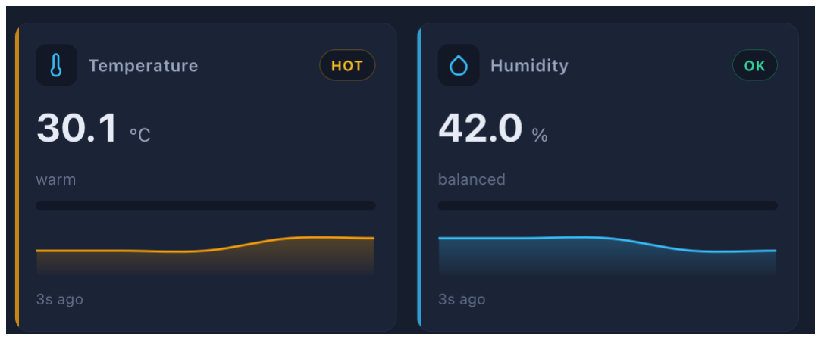
[picture p54: figure]

لکش (5-1 ) جیاتن رگسح امد و تبوطر

يارب یـسررب درکلمع رگـسح 11DHT، هاگتـسد رد طیارـش یطیحم يداع رارق تفرگ و ریداقم امد و تبوطر هب تروــص هرود يا طــسوت Firmware زا رگــسح تفایرد و رد یجورخ Monitor Serial شیامن هداد دــش . نینچمه تحص راشتنا ریداقم تفایرد هدش رد Topic ياه طوبرم هب امد و تبوطر MQTT دروم یسررب رارق تفرگ . اب هدهاـشم تارییغت یقطنم و رادیاپ ریداقم و تفایرد حیحـص هداد ،اه صخـشم دـش هک طابترا 32ESP اب رگـسح 11DHT و دنیارف ندناوخ و لاـسرا تاعلاطا هب یتـسرد ماجنا یم دوـش و رگـسح رد طیارـش نومزآ درکلمع یبولطم دراد .

-5-2-2 نومزآ رگسح رون

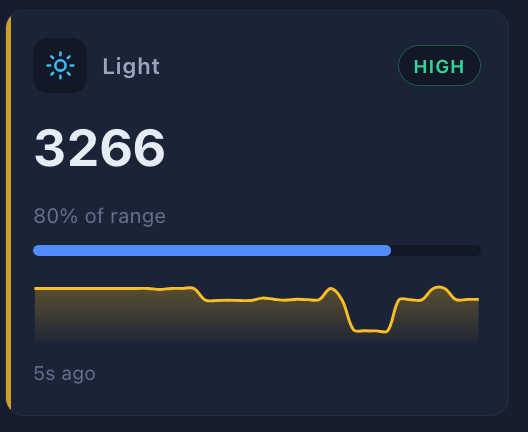
[picture p55: figure]

لکش (5-2 ) هجیتن رگسح رون

يارب یــسررب درکلمع لوژام LDR، طیارــش يرون طیحم رد دنچ تیعــضو فلتخم رییغت هداد دــش و رادقم

زرا و نومزآ ی با ی سی متس

یجورخ گولانآ رگـسح طـسوت لدبم ADC طوبرم هب 32ESP هزادنا يریگ دیدرگ . رد نیا نومزآ راظتنا یم دور اب رییغت تدـش رون ،طیحم رادقم هدناوخ هدـش زا يدورو گولانآ زین رییغت دنک و نیا تارییغت رد یجورخ متـسیـس لباق هدهاـشم دـشاب . جیاتن هب تـسد هدمآ ناـشن داد هک اب رییغت طیارـش ،يرون رادقم ADC زین رییغت هدرک و نیاربانب رگـسح LDR رداق تسا تارییغت تدش رون طیحم ار هب یتسرد صیخشت هداد و رادقم رظانتم ار رد رایتخا Firmware رارق دهد .

-5-2-3 نومزآ رگسح دود و شتآ

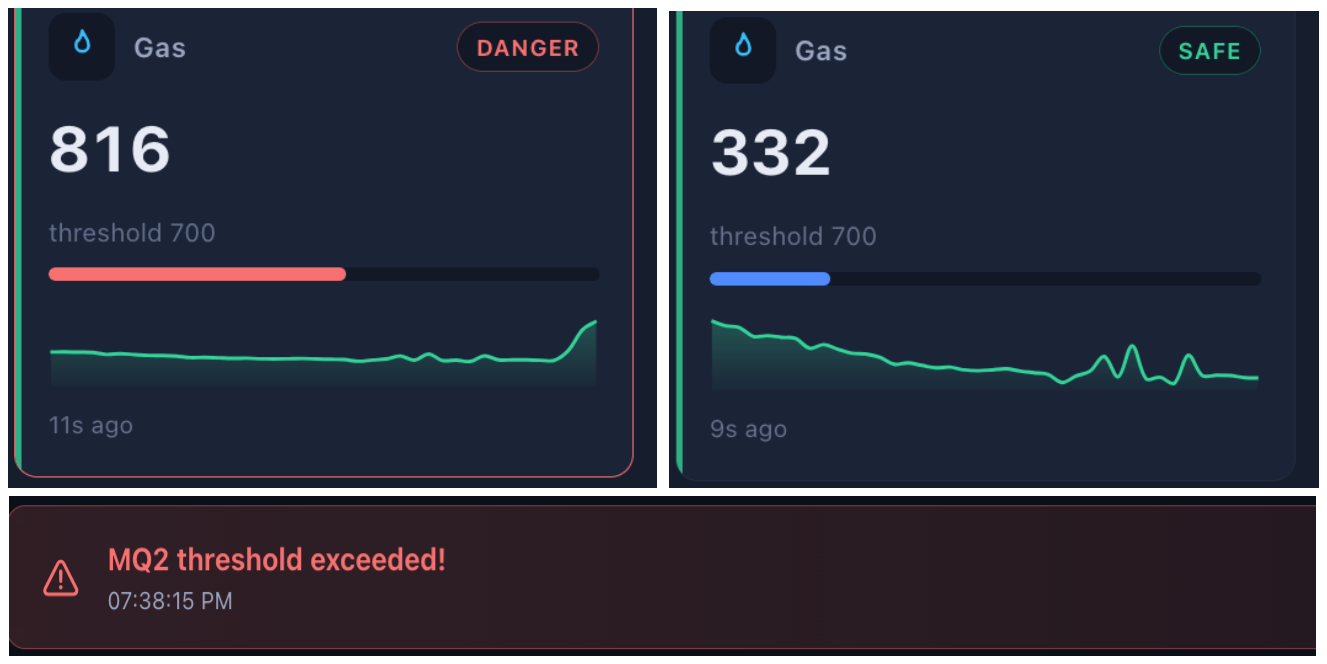
[picture p56: figure]

لکش (5-3 ) جیاتن رگسح دود و شتآ

هب روظنم یبایزرا درکلمع رگـسح -2MQ، ادتبا هاگتـسد رد طیارـش يداع طیحم رارق هداد دـش و رادقم یجورخ گولانآ رگـسح هزادنا يریگ ؛دیدرگ سپـس اب رارق نداد رگـسح رد ضرعم دود و طیارـش یـشیامزآ طوبرم هب ،شتآ شیازفا رادقم یجورخ و شنکاو قطنم صیخـشت رادـشه دروم یـسررب رارق تفرگ . رد طیارـش ،يداع رادقم دناوخ ه هدـش زا رگـسح رد دودح هزاب 300 ات 350 رارق ،تـشاد رد یلاح هک رد طیارـش شیامزآ شتآ رادقم یجورخ هب شیب زا 700 شیازفا تفای هک رد هدایپ يزاـس متـسیـس هب ناونع هناتـسآ صیخـشت تیعـضو شتآ رد رظن هتفرگ هدـش تـسا . اب روبع رادقم رگـسح زا نیا تـسآ ،هنا متـسیـس هولاع رب صیخـشت طیارـش ،رادـشه تیعـضو Alarm ار لاعف هدرک و مایپ طوبرم هب عوقو رادـشه ار زا قیرط MQTT رـشتنم ؛درک نیاربانب درکلمع رگسح -2MQ و طابترا نآ اب قطنم صیخشت رادشه قباطم راظتنا یبایزرا دش .

زرا و نومزآ ی با ی سی متس

-5-2-4 نومزآ رگسح صیخشت تکرح

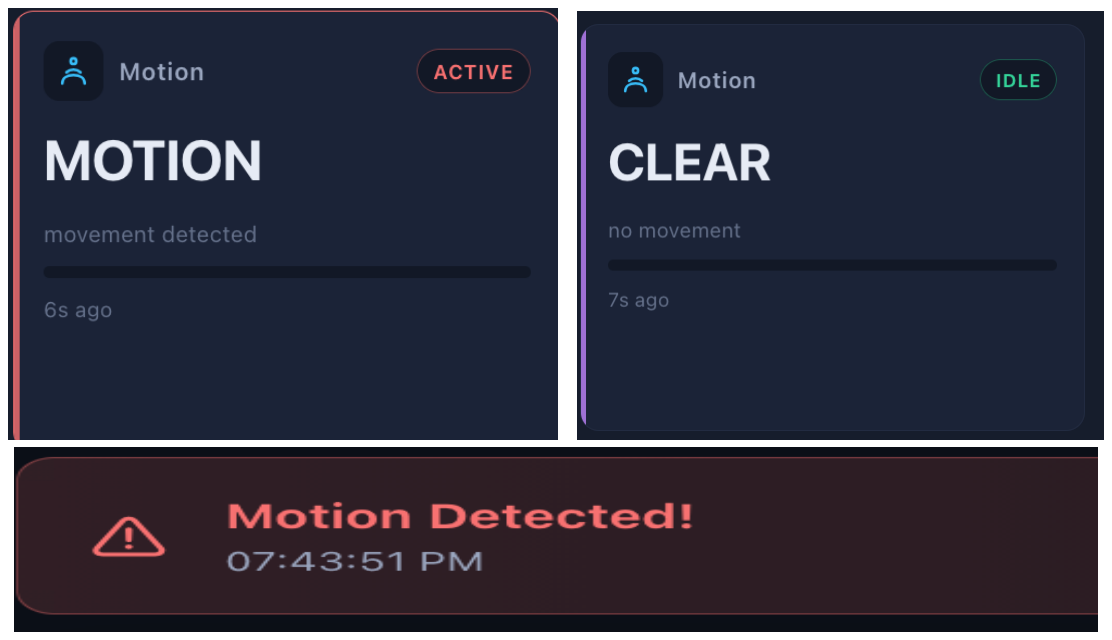
[picture p57: figure]

لکش (5-4 ) جیاتن رگسح صیخشت تکرح

يارب یـسررب درکلمع لوژام PIR، ادتبا هاگتـسد رد یطیحم نودب تکرح رارق هداد دـش ات تیعـضو هیلوا رگـسح صخـشم دوـش و سپـس اب داجیا تکرح رد هدودحم صیخـشت ،رگـسح رییغت تیعـضو یجورخ نآ و شنکاو Firmware دروم یـسررب رارق تفرگ . جیاتن نومزآ ناـشن داد هک رگـسح PIR رد طیارـش نییعت هدـش داق ر هب صیخـشت تکرح هدوب و رییغت تیعـضو یجورخ نآ طـسوت 32ESP هب یتـسرد ییاـسانـش یم دوـش . نینچمه رد یتروـص هک تیلباق صیخـشت تکرح رد تامیظنت متـسیـس لاعف ،دـشاب سپ زا ییاـسانـش ،تکرح قطنم رادـشه ارجا هدـش و مایپ طوبرم هب عوقو دادیور زا قیرط MQTT لاـسرا یم ؛دوـش رد هجیتن درکلمع رگـسح PIR و طابترا نآ اب متسیس رادشه زین قباطم یحارط ماجنا هدش دروم دییأت رارق تفرگ .

-5-3 نومزآ هناماس رادشه

رد نیا ،نومزآ درکلمع هناماـس رادـشه یتوـص و هوحن شنکاو نآ هب تیعـضو ياه فلتخم متـسیـس دروم یـسررب رارق تفرگ . رد هلحرم ،تــسخن درکلمع Buzzer زا قیرط نامرف ياه رتنک یل متــسیــس دروم شیامزآ رارق تفرگ . هولاع رب لرتنک میقتــسم طــسوت ،ربراک درکلمع طابترا Buzzer اب دادیور ياه صیخــشت هداد هدــش طـسوت اهرگـسح زین یـسررب ؛دـش هب نیا تروـص هک اب روبع رادقم یجورخ رگـسح -2MQ زا هناتـسآ نییعت هدـش و نینچمه رد تروـص لاعف ندوب تیلباق صیخـشت تکرح و ییاـسانـش ،تکرح تیعـضو رادـشه لاعف هدـش و Buzzer قباطم قطنم فیرعت هدـش عورـش هب تیلاعف یم دنک . جیاتن نومزآ ناـشن داد هک هناماـس رادـشه یتوـص قباطم یحارط ماجنا هدـش لمع یم دنک و رد ماگنه لاعف ندـش تیعـضو ،رادـشه Buzzer هب تروـص بوانتم لاعف و لاعفریغ هدــش و اب لاعفریغ ندرک ه رادــش زین درکلمع نآ فقوتم یم دوــش . نینچمه طابترا نایم دادیور ياه اهرگـسح و متـسیـس رادـشه هب یتـسرد رارقرب هدوب و رد طیارـش نییعت ،هدـش رادـشه یتوـص و مایپ طوبرم هب دادیور زا قیرط هناماس لاسرا یم دوش .

زرا و نومزآ ی با ی سی متس

### -5-4 نومزآ لاصتا هب WiFi و Broker MQTT

لکش (5-5 ) هجیتن نومزآ لاصتا هب هکبش و Broker MQTT

رد نیا ،نومزآ درکلمع هناماـس رد يرارقرب طابترا اب هکبـش WiFi و سپـس لاـصتا هب Broker MQTT دروم یـسررب رارق تفرگ . فده زا ماجنا نیا ،نومزآ نانیمطا زا تحـص درکلمع شخب یطابترا 32ESP و نینچمه یـسررب ناکما لدابت تاعلاطا نایم گتـسد ها و Broker MQTT دوب . رد نیا ،دنیارف ادتبا هاگتـسد اب هدافتـسا زا تامیظنت هریخذ هدـش رد شخب Provisioning يارب لاـصتا هب هکبـش WiFi شلات یم دنک و سپ زا يرارقرب تیقفوم زیمآ ،طابترا لاـصتا هب Broker MQTT رارقرب یم دوـش . سپ زا لاـصتا هب Broker، ناکما راـشتنا مایپ ياه م طوبر هب تاعلاطا اهرگسح و نینچمه تفایرد مایپ ياه یلرتنک زا قیرط Topic هطوبرم دروم شیامزآ رارق تفرگ .
روطنامه هک هدهاـشم یم ،دوـش هاگتـسد ادتبا اب تیقفوم هب هکبـش WiFi لـصتم هدـش و سپ زا نآ طابترا اب Broker MQTT زین رارقرب هدـش تـسا . نینچمه نومزآ لاـسرا و تفایرد مایپ ناـشن داد هک هاگتـسد رداق تـسا تاعلاطا ار هب Broker رـشتنم هدرک و مایپ ياه لاـسرا هدـش زا تمـس Broker ار زین تفایرد و شزادرپ دنک . ،نیاربانب طابترا ود هفرط نایم 32ESP و Broker MQTT قباطم یحارط ماجنا هدـش هب یتـسرد رارقرب هدوب و تخاسریز یطابترا زایندروم يارب لدابت طا تاعلا و نامرف ياه یلرتنک هناماس درکلمع یحیحص دراد .

-5-5 نومزآ دروبشاد هناماس

رد نیا ،نومزآ درکلمع شخب ياه فلتخم دروبـشاد بو و هوحن طابترا نآ اب 32ESP زا قیرط MQTT دروم یـسررب رارق تفرگ . فده زا ماجنا نیا ،نومزآ نانیمطا زا تحـص تفایرد و شیامن تاعلاطا ،اهرگـسح شیامن دادیور ياه رادـشه و نینچمه ناکما لاـسرا نامرف ياه یلرتنک زا طبار يربراک هب هاگتـسد دوب . اب هجوت هب هکنیا دروبــشاد هب تروــص میقتــسم زا قیرط WebSocket over MQTT اب Broker طابترا رارقرب یم ،دنک درکلمع طابترا نایم ،دروبشاد Broker و 32ESP زین رد نایرج نیا نومزآ دروم یبایزرا رارق تفرگ .


لکش (5-6 ) شیامن تاعلاطا اهرگسح رد دروبشاد

زرا و نومزآ ی با ی سی متس

رد هلحرم ،تـسخن شخب شیامن تاعلاطا اهرگـسح دروم یـسررب رارق تفرگ . سپ زا يرارقرب طابترا دروبـشاد اب Broker MQTT، تاعلاطا لاـسرا هدـش طـسوت 32ESP زا Topic ياه طوبرم هب اهرگـسح تفایرد هدـش و ریداقم ،امد ،تبوطر تدـش ،رون تیعـضو تکرح و رادقم رگـسح -2MQ رد شخب ياه هطوبرم شیامن هداد دندـش . نینچمه رییغت ریداقم اهرگـسح نودب زاین هب يراذگراب ددجم هحفـص رد دروبـشاد شیامن هداد دـش هک ناشن هدنهد درکلمع حیحص طابترا گنردلاب نایم هاگتسد و طبار يربراک تسا .

لکش (5-7 ) شیامن رادشه رد دروبشاد

رد هلحرم ،مود درکلمع شخب شیامن تیعـضو رادـشه دروم یـسررب رارق تفرگ . اب داجیا طیارـش رادـشه طـسوت رگــسح ياه ،هناماــس مایپ طوبرم هب دادیور زا قیرط MQTT رــشتنم هدــش و دروبــشاد سپ زا تفایرد ،نآ تیعـضو رادـشه ار رد شخب هطوبرم شیامن داد . جیاتن نیا نومزآ ناـشن داد هک دادیور ياه رادـشه هب یتـسرد زا هاگتسد هب Broker و سپس هب دروبشاد لقتنم هدش و رد طبار يربراک شیامن هداد یم دنوش .

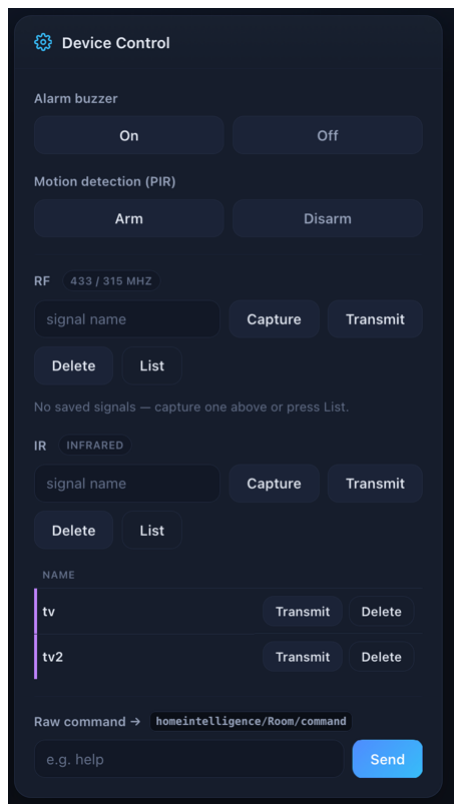
[picture p58: figure]

لکش (5-8 ) لاسرا نامرف زا دروبشاد

رد هلحرم ،ینایاپ تیلباق لاـسرا نامرف ياه یلرتنک زا دروبـشاد هب 32ESP دروم شیامزآ رارق تفرگ . رد نیا ،نومزآ نامرف ییاه دننام لاعف و فریغ لاع ندرک Buzzer، لرتنک تیلباق صیخـشت تکرح و نینچمه نامرف ياه طوبرم هب ،تفایرد ،لاــسرا فذح و شیامن لانگیــس ياه RF و IR زا قیرط دروبــشاد لاــسرا دندــش . 32ESP سپ زا تـفاـیرد ماـیپ زا Topic ،ناـمرف نآ ار شزادرپ هدرک و تاـیلمع هـطوبرم ار ارجا درک . ،نیارباـنب جیاتن نومزآ ناـشن داد هک ریـسم یطابترا زا دروبـشاد ات Broker MQTT و سپـس 32ESP هب یتـسرد لمع هدرک و دروبشاد رداق تسا هولاع رب شیامن ،تاعلاطا لرتنک شخب ياه فلتخم هناماس ار زین ماجنا دهد .

زرا و نومزآ ی با ی سی متس

-5-6 نومزآ متسیس RF

هـب روظنم یباـیزرا درکلمع شخب طاـبترا ییویدار ،هـناـماـــس تـیلباـق ياـه ،تـفاـیرد خذ هری ،يزاـــس شخپزاـب و تـیریدـم لاـنگیـــس ياـه RF دروم شیاـمزآ رارق تـفرگ . رد نیا ،نومزآ درکلمع طاـبترا ناـیم دـنریگ ه ياـه RF، Firmware و هظفاح یلخاد هاگتـسد یـسررب دـش و نینچمه ناکما لرتنک و تیریدم لانگیـس ياه هریخذ هدش زا قیرط نامرف ياه متسیس دروم یبایزرا رارق تفرگ .

-5-6-1 نومزآ تفایرد لانگیس RF

لکش (5-9 ) تفایرد لانگیس RF

رد نیا ،نومزآ تیلباق تفایرد لانگیـس RF زا قیرط کی تومیر لرتنک دروم یـسررب رارق تفرگ . يارب ماجنا ،نومزآ متـسیـس رد تلاح تفایرد رارق هداد هدـش و سپـس کی نامرف زا تومیر لرتنک لاـسرا دـش ات هدنریگ ياـه RF لاـنگیـــس ار تـفاـیرد و راـپ ياـهرتما طوبرم هـب نآ ار جارختـــسا دـننک . سپ زا تـفاـیرد تـیقفوم زیمآ ،لانگیـس تاعلاطا نآ لماـش ،دک دادعت ،تیب ،لکتورپ لوط سلاپ و دناب یـسناکرف ییاـسانـش هدـش رد راتخاـس طوبرم هب لانگیـس هریخذ دـش و مان نییعت هدـش طـسوت ربراک زین هب نآ صاـصتخا هداد دـش . روطنامه هک هدهاشم یم وش ،د لانگیس لاسرا هدش زا تومیر هب یتسرد طسوت متسیس تفایرد و شزادرپ هدش و تاعلاطا نآ اب مان نییعت هدـش رد هظفاح هاگتـسد هریخذ هدـش ؛تـسا ،نیاربانب درکلمع شخب تفایرد و هریخذ يزاـس هیلوا لانگیس RF قباطم یحارط ماجنا هدش حیحص تسا .

-5-6-2 نومزآ لاسرا لانگیس RF

لکش (5-10 ) لاسرا لانگیس RF

رد نیا ،نومزآ تیلباق شخپزاب لانگیـس RF هریخذ هدـش دروم یـسررب رارق تفرگ . يارب ماجنا ،نومزآ مان یکی زا لانگیـس ياه هریخذ هدـش هب متـسیـس لاـسرا دـش و Firmware سپ زا ادیپ ندرک لانگیـس ،رظندروم دناب یـسناکرف هریخذ هدـش ار یـسررب هدرک و هدنتـسرف بـسانتم اب نآ ار باختنا درک . سپـس ياهرتماراپ طوبرم هب ،لانگیـس لماـش ،لکتورپ لوط ،سلاپ دک و دادعت ،تیب يارب شخپزاب دروم هدافتـسا رارق دنتفرگ . امه ن روط که هدهاـشم یم ،دوـش لانگیـس هریخذ هدـش نودب زاین هب نییعت ددجم سناکرف طـسوت ،ربراک هب یتـسرد زا قیرط

زرا و نومزآ ی با ی سی متس

هدنتـسرف هطوبرم لاـسرا هدـش و ع درکلم شخپزاب لانگیـس RF اب تیقفوم ماجنا هدـش تـسا . نیا هجیتن ناـشن یم دهد هک تاعلاطا هریخذ هدـش لانگیـس يارب يزاـسزاب و لاـسرا ددجم نآ هب یتـسرد دروم هدافتـسا رارق یم دریگ .

-5-6-3 نومزآ تیریدم لانگیس RF

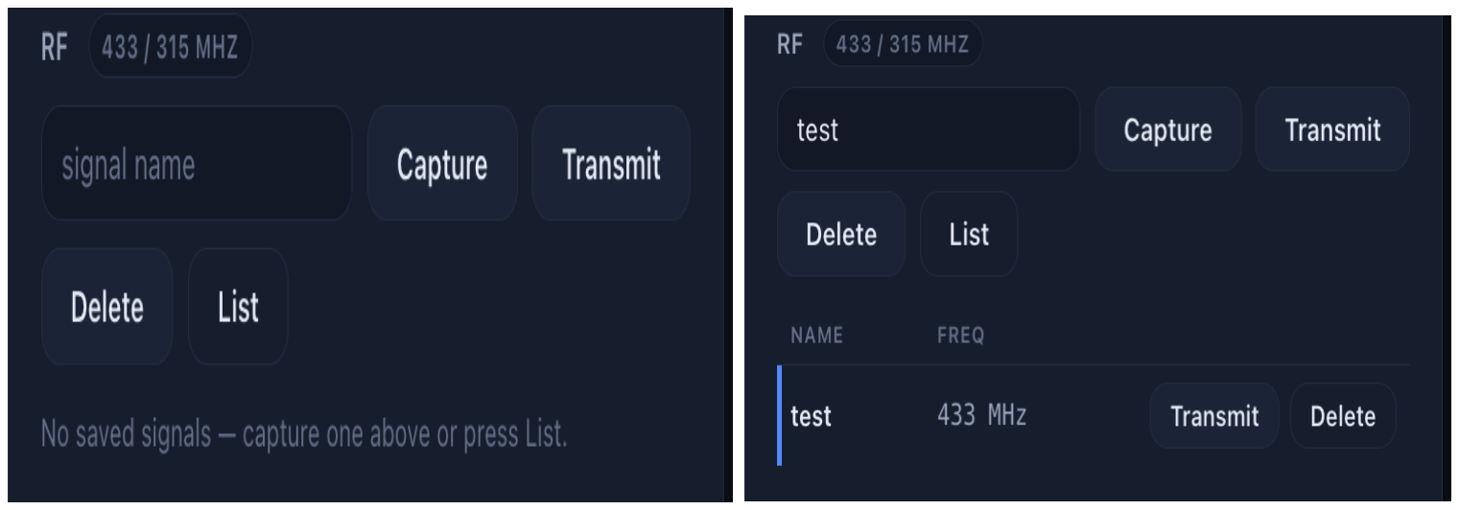
[picture p59: figure]

لکش (5-11 ) تیریدم لانگیس RF

رد نیا ،نومزآ تیلباق تیریدم لانگیـس ياه هریخذ هدـش لماـش شیامن تـسرهف لانگیـس اه و فذح کی لانگیـس صخـشم دروم یـسررب رارق تفرگ . ادتبا اب هدافتـسا زا نامرف طوبرم هب تـسرهف لانگیـس ،اه تاعلاطا لانگیــس ياه دوجوم رد هظفاح یبایزاب و شیامن هداد دــش و سپــس یکی زا لانگیــس ياه هریخذ هدــش اب هدافتــسا زا مان نآ يارب فذح نا باخت دــش . سپ زا ،فذح تاعلاطا لانگیــس ياه دوجوم هرابود شیامن هداد دـش . روطنامه هک هدهاـشم یم ،دوـش تـسرهف لانگیـس ياه هریخذ هدـش هب یتـسرد شیامن هداد هدـش و تاعلاطا طوبرم هب لانگیــس اه لباق هدهاــشم تــسا . نینچمه سپ زا يارجا نامرف ،فذح لانگیــس رظندروم زا هیارآ لانگیس اه و هظفاح یمئاد فذح هدش و رد تسرهف لانگیس ياه دوجوم زین شیامن هداد یمن دوش . ،نیاربانب تیلباق ياه یلصا تیریدم لانگیس ياه RF قباطم یحارط ماجنا هدش هب یتسرد لمع یم دننک .

-5-7 نومزآ متسیس IR

هب روظنم یبایزرا درکلمع شخب طابترا نودام زمرق ،هناماــس تیلباق ياه ،تفایرد ریخذ ه ،يزاــس شخپزاب و تیریدم لانگیـس ياه IR دروم شیامزآ رارق تفرگ . رد نیا ،نومزآ درکلمع هدنریگ و هدنتـسرف نودام زمرق و نینچمه هوحن شزادرپ تاعلاطا تفایرد هدـش طـسوت Firmware و هریخذ اهنآ رد هظفاح یلخاد دروم یـسررب رارق تفرگ ات تحص درکلمع نیا شخب رد طیارش یلمع یبایزرا دوش .

زرا و نومزآ ی با ی سی متس

-5-7-1 نومزآ تفایرد لانگیس IR

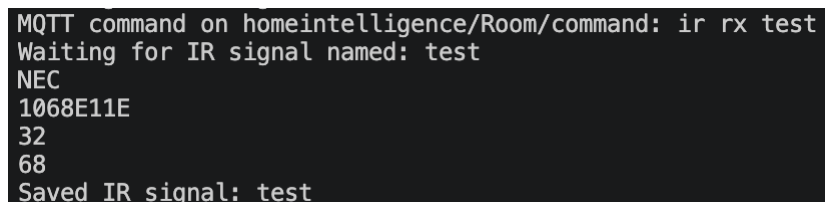
[picture p60: figure]

لکش (5-12 ) تفایرد لانگیس IR

رد نیا ،نومزآ تـیلباـق تـفاـیرد لاـنگیـــس نوداـم زمرق زا قیرط کـی لرتنک زا هار رود IR دروم یـــسررب رارق تفرگ . يارب ماجنا ،نومزآ متـسیـس رد تلاح تفایرد رارق هداد دـش و سپـس یکی زا نامرف ياه لرتنک زا هار رود هب تمـس هدنریگ نودام زمرق لاـسرا دیدرگ . سپ زا تفایرد ،لانگیـس تاعلاطا نآ طـسوت هناخباتک هطوبرم شزادرپ هدـش و رد تروص ییاسانش ،لکتورپ تاعلاطا Decode هدش و نینچمه هداد ماخ لانگیس رد راتخاس هطوبرم هریخذ دـش . روطنامه هک هدهاـشم یم ،دوـش لانگیـس لاـسرا هدـش زا لرتنک IR هب یتـسرد طـسوت هدنریگ تفایرد و شزادرپ هدـش و تاعلاطا نآ اب مان نییعت هدـش طـسوت ربراک رد هظفاح هاگتـسد هریخذ هدـش تـسا . ،نیاربانب درکلمع شخب تفایرد و هریخذ يزاـس لانگیـس ياه نودام زمرق قباطم یحارط ماجنا هدـش حیحـص تسا .

-5-7-2 نومزآ لاسرا لانگیس IR

لکش (5-13 ) لاسرا لانگیس IR

رد نیا ،نومزآ باق تیل شخپزاب لانگیـس نودام زمرق هریخذ هدـش دروم یـسررب رارق تفرگ . يارب ماجنا ،نومزآ مان یکی زا لانگیس ياه هریخذ هدش هب متسیس لاسرا دش و Firmware سپ زا ادیپ ندرک لانگیس ،رظندروم تاعلاطا طوبرم هب لکتورپ و هداد هریخذ هدـش ار یبایزاب هدرک و شور بـسانم يارب لاـسرا نآ را باختنا درک . رد یتروـص هک لکتورپ لانگیـس طـسوت متـسیـس ینابیتـشپ ،دوـش لانگیـس رب ساـسا تاعلاطا Decode هدـش لاـسرا هدـش و رد ریغ نیا ،تروـص هداد ماخ هریخذ هدـش يارب شخپزاب دروم هدافتـسا رارق یم دریگ . روطنامه هک هدهاـشم یم ،دوـش لانگیـس هریخذ هدـش هب یتـسرد طـسوت LED ياه نودام زمرق شخپزاب هدـش و نامرف هطوبرم هب زیهجت دـصقم لقتنم هدـش تـسا . نیا هجیتن ناـشن یم دهد هک تاعلاطا هریخذ هدـش لانگیـس IR هب یتسرد یبایزاب هدش و دنیارف شخپزاب لانگیس قباطم یحارط متسیس ماجنا یم دوش .

زرا و نومزآ ی با ی سی متس

-5-7-3 نومزآ تیریدم لانگیس IR

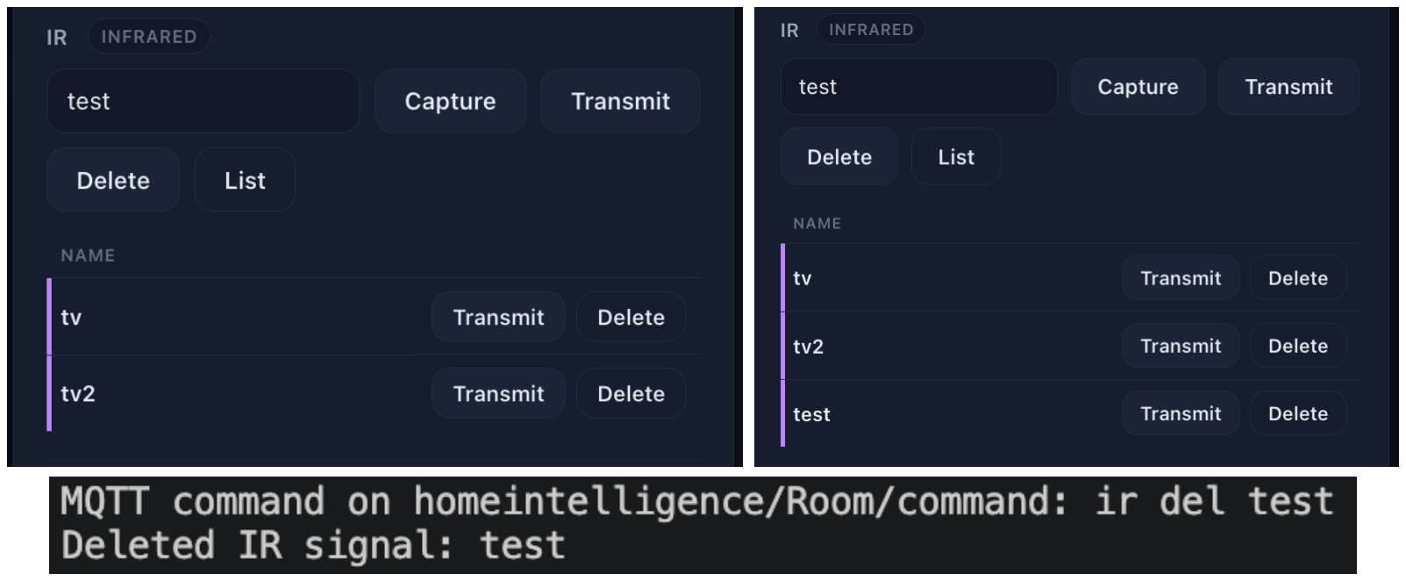
[picture p61: figure]

لکش (5-14 ) تیریدم لانگیس IR

رد نیا ،نومزآ تیلباق تیریدم لانگیـس ياه نودام زمرق هریخذ ،هدـش لماـش شیامن تـسرهف لانگیـس اه و فذح کی لانگیـس ،صخـشم دروم یـسررب رارق تفرگ . ادتبا اب هدافتـسا زا نامرف طوبرم هب شیامن ،تـسرهف تاعلاطا لانگیـس ياه دوجوم رد هظفاح یبایزاب و شیامن هداد دـش و سپـس یکی زا لانگیـس اه رب ساـسا ن ما نآ باختنا و فذح دیدرگ . سپ زا ،فذح تاعلاطا لانگیـس ياه دوجوم هرابود شیامن هداد دـش . روطنامه هک هدهاـشم یم ،دوـش تـسرهف لانگیـس ياه IR هریخذ هدـش هب یتـسرد شیامن هداد هدـش و تاعلاطا طوبرم هب لانگیـس اه لباق هدهاـشم تـسا . نینچمه سپ زا فذح کی لانگیـس ،صخـشم نآ لانگیـس زا تـسرهف دوجوم فذح هدـش و رد شیامن ياه يدعب زین هدهاـشم یمن دوـش . رد ،هجیتن تیلباق ياه ،تفایرد لاـسرا و تیریدم لانگیس ياه IR رد هناماس قباطم یحارط ماجنا هدش هب یتسرد لمع یم دننک .

-5-8 نومزآ ریز هناماس Provisioning

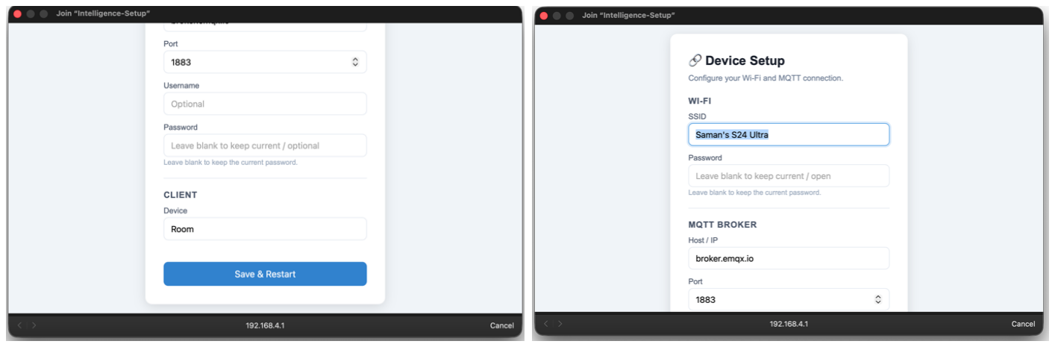
[picture p62: figure]

زرا و نومزآ ی با ی سی متس

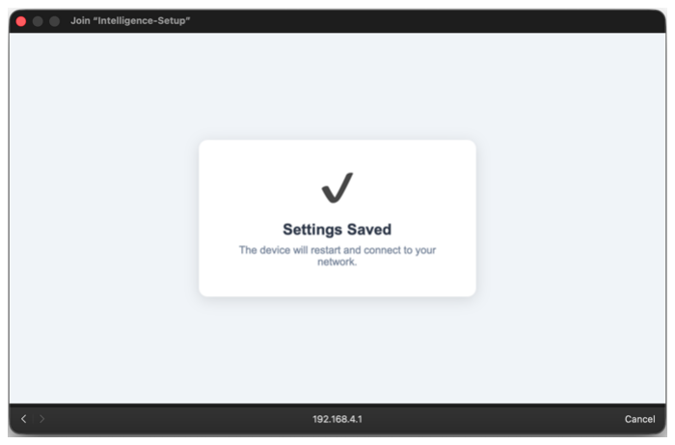
[picture p63: figure]

لکش (5-15 ) هحفص تامیظنت Provisioning

رد نیا ،نومزآ درکلمع هناماــسریز Provisioning زا رظن داجیا هکبــش ،یــصاــصتخا شیامن راکدوخ لاتروپ ،يدنبرکیپ تفایرد تاعلاطا و هریخذ يزاـس تامیظنت دروم یـسررب رارق هتفرگ تـسا . ادتبا هاگتـسد رد تلاح Provisioning رارق هتفرگ و کی Point Access یـصاـصتخا داجیا دـش و سپ زا لاـصتا ربراک هب نیا ،هکبـش هحفص تامیظنت هب تروص راکدوخ شیامن هداد دش . سپس تاعلاطا زایندروم لماش تاصخشم هکبش WiFi و ياهرتماراپ لاـصتا هب Broker MQTT دراو و لاـسرا دیدرگ و درکلمع هناماـس رد د تفایر و یجنـسرابتعا نیا تاعلاطا یــسررب دــش . رد ،همادا تامیظنت اب تیقفوم رد هظفاح یلخاد 32ESP هریخذ هدــش و هاگتــسد هب تروــص راکدوخ هار يزادنا ددجم دــش ات تامیظنت دیدج رد دنیارف لاــصتا دروم هدافتــسا رارق دنریگ . جیاتن نومزآ ناــشن داد هک هناماــسریز Provisioning قباطم ارط یح ماجنا هدــش لمع هدرک و ناکما يدنبرکیپ و رییغت تامیظنت یطابترا هاگتسد ار نودب زاین هب رییغت ای يراذگراب ددجم Firmware مهارف یم دنک .

# لصف 6 :

# هجیتن يریگ

تن ی هج گیری
رد نیا ،لـصف جیاتن لـصاح زا ،یحارط هدایپ يزاـس و یبایزرا هناماـس دنمـشوه صیخـشت دود و شتآ و لرتنک تازیهجت یکیرتکلا هئارا یم دوش . فده یلصا ،هژورپ یحارط و هعسوت کی هناماس ینتبم رب تنرتنیا ایشا هدوب تـسا هک دناوتب اب هدافتـسا زا رگـسح ياه ،فلتخم یخرب رتماراپ ياه یطیحم را هب تروـص رمتـسم شیاپ هدرک و طیارـش يداعریغ دننام شیازفا نازیم دود و زاگ ياه لباق لاعتـشا ای عوقو تکرح ار ییاـسانـش دنک و رد تروـص صیخـشت تیعـضو ،رادـشه تامادقا مزلا ار ماجنا دهد . هولاع رب تیلباق ياه طوبرم هب شیاپ و صیخشت طیارــش ،یطیحم اب هدافتــسا زا تاطابترا نودام رق زم (IR (و سناکرف ییویدار (RF (، ناکما ،تفایرد هریخذ يزاس و شخپزاب نامرف ياه لرتنک زا هار رود زین رد هناماس مهارف هدش تسا .

-6-1 عمج يدنب لحارم ماجنا هژورپ

رد ،ادتبا يدنمزاین ياه یلـصا هناماـس یـسررب و رب ساـسا ،نآ يرامعم تخـس يرازفا و مرن يرازفا بـسانم ینتبم رب درب 32ESP یحارط دـش . رد شخب تخـس فا ،راز رگـسح 11DHT يارب هزادنا يریگ امد و ،تبوطر لوژام LDR يارب هزادنا يریگ تدـش رون ،طیحم رگـسح -2MQ يارب صیخـشت دود و زاگ ياه لباق لاعتـشا و رگـــسح PIR يارب صیخـــشت تکرح دروم هدافتـــسا رارق دنتفرگ . نینچمه هب روظنم داجیا تیلباق لرتنک تازیهجت ياراد لرتنک زا هار ،رود زا هدنریگ اه و هدنتسرف ياه RF رد ود دناب یسناکرف 315 و 433 زترهاگم و کی هدنریگ و هدنتـسرف نودام زمرق هدافتـسا دـش و کی Buzzer Active زین يارب داجیا رادـشه یتوـص رد رظن هتفرگ دش .
رد شخب مرن رازفا ، Firmware هناماـس هب تروـص رلاوژام یحارط و هدایپ يزاـس دـش و فیاظو فلتخم زا هلمج تیریدم ،اهرگـسح طابترا WiFi وMQTT، متـسیـس Provisioning، تیریدم ،هظفاح شزادرپ لانگیـس اه ي RF و IR و تیریدم متـسیـس رادـشه رد لوژام ياه لقتـسم رارق دنتفرگ . نیا راتخاـس ثعاب هدـش تـسا هک ره شخب زا مرن رازفا هفیظو یــصخــشم هتــشاد دــشاب و رد ،هجیتن ،هعــسوت ،شیامزآ کــشا لا ییادز و يرادهگن Firmware اب تلوهــس يرتــشیب ماجنا دوــش . نینچمه يارب ظفح تاعلاطا سپ زا شوماخ و نــشور ندــش ،هاگتـسد زا متـسیـس لیاف یلخاد LittleFS و راتخاـس JSON يارب هریخذ تامیظنت و لانگیـس ياه تفایرد هدش هدافتسا دش .

-6-2 جیاتن لصاح زا هدایپ يزاس

جیاتن لـصاح زا هدایپ يزاـس و نومزآ ياه ماجنا هدـش ناـشن داد هک هناماـس هتـسناوت تـسا تیلباق ياه یلـصا فیرعت هدـش رد هلحرم یحارط ار رد بلاق کی متـسیـس هچراپکی هدایپ يزاـس و ارجا دنک . رگـسح 11DHT تـسناوت ریداقم امد و تبوطر طیحم ار تفایرد دنک و لوژام LDR زین تارییغت تدـش ون ر ار زا قیرط يدورو گولانآ 32ESP ییاسانش درک . رگسح -2MQ زین ناکما یسررب نازیم دود و زاگ ياه لباق لاعتشا و صیخشت روبع رادقم هزادنا يریگ هدـش زا هناتـسآ نییعت هدـش ار مهارف درک و رد طیارـش شیامزآ ،هدـش اب شیازفا رادقم یجورخ ،رگـسح تیعـضو رادـشه لاعف دـش . نینچمه رگـسح PIR رد تروـص لاعف ندوب تیلباق صیخـشت ،تکرح تسناوت عوقو تکرح ار ییاسانش هدرک و دادیور هطوبرم ار هب هناماس ملاعا دنک . متـسیـس رادـشه یتوـص زین قباطم یحارط ماجنا هدـش لمع درک و رد ماگنه لاعف ندـش تیعـضو ،رادـشه Buzzer هب تروـص بوانتم لاعف و لاعفریغ دـش و سپ زا عطق تیعـضو ـشه ،راد درکلمع نآ فقوتم دیدرگ . رد

تن ی هج گیری
شخب ،یطابترا 32ESP تـسناوت هب هکبـش WiFi لـصتم هدـش و سپ زا نآ طابترا دوخ ار اب Broker MQTT رارقرب دنک و مایپ ياه طوبرم هب هداد ياه اهرگـسح و نامرف ياه یلرتنک ار لاـسرا و تفایرد دیامن . نینچمه دروبـشاد تحت بو تـسناوت تاعلاطا تفایرد دـش ه زا MQTT ار هب تروـص هدنز شیامن هداد و ناکما لاـسرا نامرف ياه یلرتنک هب هاگتسد ار مهارف دنک . یکی رگید زا جیاتن مهم ،هژورپ هدایپ يزاـس متـسیـس تفایرد و شخپزاب لانگیـس ياه RF رد ود دناب یـسناکرف 315 و 433 زترهاگم و متسیس تفایرد و شخپزاب لانگیس ياه IR تسا . رد نومزآ ياه ماجنا ،هدش لانگیس ياه RF و IR زا لرتنک ياه هطوبرم ،تفایرد اب مان صخـشم هریخذ و رد نامز زایندروم اددجم لاـسرا دندـش و نینچمه تیلباق تـسرهف ندرک و فذح لانگیـس ياه هریخذ هدـش زین هب یتـسرد لمع درک . هدافتـسا زا LittleFS زین ثعاب دـش تاعلاطا طوبرم هب تامیظنت Provisioning، تیعـضو صیخـشت تکرح و لانگیـس ياه هریخذ هدش سپ زا اره ا يزادن ددجم هاگتسد ظفح دنوش . رد شخب Provisioning، هاگتـسد تـسناوت کی Point Access یـصاـصتخا داجیا هدرک و سپ زا لاـصتا ،ربراک هحفـص يدنبرکیپ ار هب تروـص راکدوخ شیامن دهد . تاعلاطا دراو هدـش طـسوت ربراک سپ زا ا یجنـسرابتع رد هظفاح یلخاد هریخذ دـش و هاگتـسد اب هار يزادنا ،ددجم تامیظنت دیدج ار يارب لاـصتا هب هکبـش و MQTT Broker دروم هدافتـسا رارق داد . رد ،عومجم جیاتن نومزآ ياه ماجنا هدـش ناـشن داد هک يازجا یلـصا هناماـس و طابترا نایم شخب ياه تخس يرازفا و مرن يرازفا قباطم این يدنمز ياه فیرعت هدش لمع هدرک دنا .

-6-3 م تیدودح ياه هژورپ

اب دوجو هدایپ يزاـس و درکلمع حیحـص تیلباق ياه ،یلـصا هناماـس رـضاح ياراد تیدودحم ییاه تـسا هک دیاب رد ماگنه هدافتـسا زا نآ دروم هجوت رارق دریگ . یکی زا مهم نیرت تیدودحم اه طوبرم هب رگـسح -2MQ ؛تـسا اریز رد نیا هژورپ رادقم یجورخ نآ هب تروص میقتسم زا ADC هدناوخ هدش و اب کی رادقم هناتسآ مرن يرازفا هـسیاقم یم ،دوـش نیاربانب هجیتن هزادنا يریگ یم دناوت تحت ریثأت یلماوع دننام طیارـش ،یطیحم نامز مرگ ندـش ،رگـسح تیفیک رگـسح و هوحن يریگرارق نآ رارق دریگ و هدافتـسا زا نیا هناماـس هب ناونع کی متـسیـس درادناتسا ملاعا ،قیرح دنمزاین ساربیلاک نوی قیقد و ماجنا نومزآ ياه یصصخت و درادناتسا دهاوخ دوب . تیدودحم رگید طوبرم هب متــسیــس ياه RF و IR ،تــسا اریز ناکما تفایرد و شخپزاب لانگیــس اه هب عون ،لکتورپ تاصخشم ،لانگیس سناکرف دروم هدافتسا و يراگزاس تازیهجت اب تخس رازفا و هناخباتک ياه هب راک هتفر هتــسباو ؛تــسا نیاربانب یمن ناوت نیمــضت درک هک یمامت تازیهجت دوجوم رد رازاب اب نیا هناماــس لباق لرتنک دنــشاب . رد شخب یطابترا زین هدافتــسا زا کی Broker MQTT یمومع رد هدایپ يزاــس ،یلعف هچرگا يارب هعـسوت و شیامزآ هناماـس بـسانم هدوب ،تـسا اما يارب هدافتـسا رد طیحم ياه یعقاو و دربراک ياه ساـسح هیـصوت یمن دوـش و مزلا تـسا زا Broker ،یـصاـصتخا زارحا تیوه بـسانم و طابترا يراگنزمر هدـش هدافتـسا دوش .

-6-4 پ داهنشی ياه هعسوت رد هدنیآ

يارب هعـسوت هخـسن ياه هدنیآ ،هناماـس یم ناوت هعومجم يا زا تیلباق ياه دیدج ار هب متـسیـس هفاـضا درک . یکی زا مهم نیرت ،دراوم شیازفا تینما تاطابترا تـسا هک یم دناوت اب هدافتـسا زا TLS over MQTT، زارحا

تن ی هج گیری
تیوه ناربراک و تازیهجت و تیریدم بـسانم یهاوگ ياه اتیجید ل ماجنا دوـش . نینچمه هب ياج هدافتـسا زا Broker ،یمومع یم ناوت کی Broker MQTT یـصاـصتخا ار رب يور رورـس ای تخاـسریز يربا رقتـسم درک ات لرتنک يرتشیب رب یسرتسد ،ناربراک تینما تاعلاطا و تیریدم تازیهجت دوجو هتشاد دشاب . زا رگید تیلباق ياه ،يداهنـشیپ یم ناوت هب هدایپ زاـس ي ب یناـسرزور Firmware هب تروـص Air-The-Over ای OTA هراـشا درک هک ناکما ب یناـسرزور مرن رازفا 32ESP ار نودب زاین هب لاـصتا یکیزیف هاگتـسد هب هنایار مهارف یم دنک . هولاع رب ،نیا یم ناوت شور ياه یطابترا يرگید دننام GSM، LoRa ای ریاس يروانف ياه یطابترا ار رد رانک WiFi دروم هدافتـسا رارق داد ات رد تروـص عطق ندـش طابترا WiFi، ریـسم ینیزگیاج يارب لاـسرا تاعلاطا و اهرادشه دوجو هتشاد دشاب . رد شخب شیاپ طیحم زین یم ناوت اب هفاــضا ندرک رگــسح ياه قیقد رت و هربیلاک ،هدــش تیلباق صیخــشت طیارـش رطخ ار شیازفا داد و متیروگلا ياه هتفرـشیپ يرت يارب لیلحت نامزمه هداد ياه دنچ رگـسح هب راک تفرگ . نینچمه هعـسوت دروبـشاد بو و هفاـضا ندرک یتاناکما دننام هریخذ يزاـس هچخیرات هداد ،اه شیامن رادومن ياه دنلب ،تدم تیریدم نیدنچ هاگتـسد و فیرعت حوطـس یـسرتـسد فلتخم یم دناوت تیلباق هدافتـسا زا هناماس ار رد سایقم گرزب رت ا شیازف دهد .

-6-5 ج عم يدنب ییاهن

رد ،عومجم جیاتن لـصاح زا ،یحارط هدایپ يزاـس و نومزآ هناماـس ناـشن یم دهد هک اب هدافتـسا زا کی درب مک هنیزه 32ESP و بیکرت رگـسح ياه ،یطیحم طابترا WiFi و MQTT و تیلباق ياه RF و IR یم ناوت کی باه دنمـشوه دنچ هروظنم يارب شیاپ و لرتنک طیحم داجیا درک . هناماـس یحارط هدـش لاع هو رب تفایرد و شیامن تاعلاطا اهرگـسح و صیخـشت یخرب طیارـش ،يداعریغ ناکما داجیا رادـشه ،یتوـص لرتنک تازیهجت ياراد لرتنک زا هار ،رود هریخذ يزاـس تاعلاطا رد هظفاح ،یلخاد يدنبرکیپ نودب زاین هب رییغت Firmware و تیریدم هاگتسد زا قیرط دروبشاد بو ار مهارف هدرک تسا .

# لصف 7 :

# عجارم

84

عجارم

[1] National Institute of Standards and Technology (NIST), "IoT Device," 2024. [Online]. Available: https://csrc.nist.gov/glossary/term/iot_device. [Accessed August 2026].
[2] J. Voas, "Networks of 'Things'," National Institute of Standards and Technology, NIST Special Publications 800-183, 2016.
[3] Espressif Systems, "ESP32 series Datasheet," Espressif Systems.
[4] A. Banks, E. Briggs, K. Borgendale and R. Gupta, "MQTT Version 5.0," OASIS Standards, 2019.
[5] S. Ullrich, "rc-switch: Arduino library to operate 315/433 MHz remote controlled devices," [Online]. Available: https://github.com/sui77/rc-switch. [Accessed August 2026].
[6] D. Conran et al., "IRremoteESP8266: Infrared remote library for ESP8266/ESP32," [Online]. Available: https://github.com/crankyoldgit/IRremoteESP8266. [Accessed August 2026].
[7] Hanwei Electronics Group Corporation, "MQ-2 Gas Sensor Datasheet," Hanwei Electronics Group Corporation.
[8] Adafruit Industries, "DHT Sensor Library Documentation," [Online]. Available: https://adafruit.github.io/DHT-sensor-library/. [Accessed August 2026].
[9] Espressif Systems, "Arduino ESP32 Wi-Fi Documentation," Espressif Systems.
[10] Arduino ESP32, "LittleFS File System Documentation," Espressif Systems.

# لصف 8 :

# تسویپ ها

-8-1 هشقن کیتامش رادم

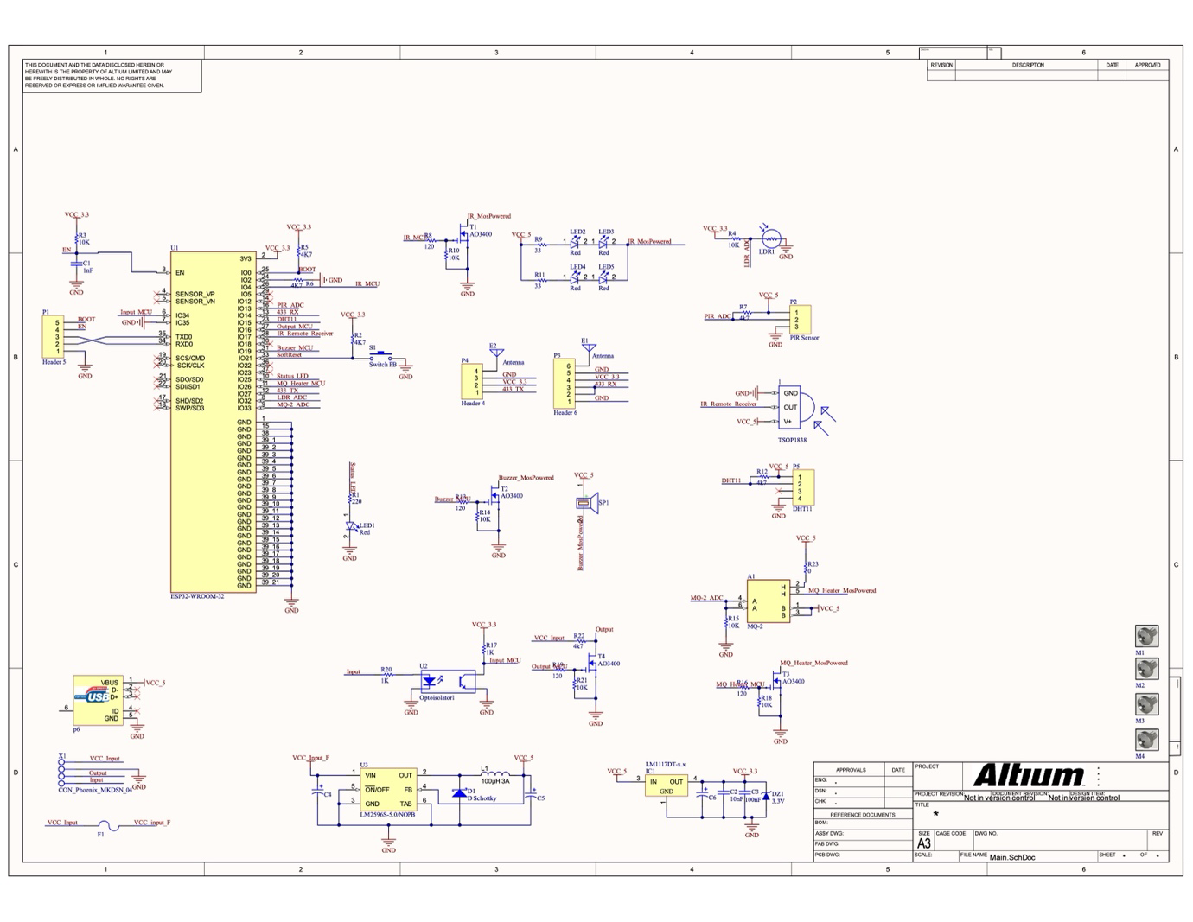
[picture p64: figure]

-8-2 دک عبنم هژورپ

دک عبنم لماک Firmware طوبرم هب هناماـس یحارط ،هدـش هب هارمه لیاف ياه يدنبرکیپ و تادنتـسم ،طبترم رد نزخم GitHub هژورپ رارق هداد هدش تسا . homeintelligence93/samansayad/com.github://https
