samansayad93/HomeIntelligence/documents/Final_Project_revision.pdf

هدکشناد یسدنهم رتویپماک

## یحارط و هدایپ يزاس هناماس دنمشوه صیخشت دود و لرتنک تازیهجت یگناخ یتبم رب 32ESP

ناماس دایص لاعف
401521408

مان داتسا :
رتکد ریما يدهم ینیسح هزنم

هژورپ ینایاپ
رویرهش هام 1405


أ

رکشت و ینادردق :

ب

هدیکچ

رد نیا ،هژورپ کی هناماـس دنمـشوه ینتبم رب 32ESP یحارط و هدایپ يزاـس هدـش تـسا هک فده یلـصا نآ صیخـــشت و ملاعا طیارـــش رطخ دـنناـم دود و شتآ و نینچمه مهارف ندرک تـیلباـق شیاـپ طیحم و لرتنک تازیهجت یکینورتکلا تسا .
هاگتـسد هعـسوت هتفای هولاع رب تیلباق صیخـشت دود و ،شتآ هب رگـسح ياه امد و تبوطر و رون و صیخـشت تکرح زهجم هدـش تـسا ات دناوتب تاعلاطا یفلتخم زا تیعـضو طیحم ار عمج يروآ و شیاپ دنک . نینچمه اب هدافتـسا زا هدنریگ و هدنتـسرف ياه نودام زمرق ( IR ( و ییویدار ( RF(، ناکما ،تفایرد هریخذ و لاـسرا نامرف ياه طوبرم هب تازیهجت یکیرتکلا مهارف هدــش تــسا . ربراک یم دناوت زا قیرط هناماــس مرن فا ،يراز تیعــضو هاگتسد و تاعلاطا طیحم ار هدهاشم هدرک و تازیهجت ار زا هار رود نشور ای شوماخ هدرک و نامرف ياه دروم رظن ار يارب نآ اه لاسرا دنک . طابترا هاگتـسد اب هناماـس مرن يرازفا زا قیرط Fi-Wi رارقرب هدـش و يارب لدابت مایپ و هداد نایم هاگتـسد و هناماس زا لکتورپ MQTT هدافتسا هدش تسا .

هژاو ياه يدیلک : هناخ ،دنمشوه نویساموتا ،یگناخ 32ESP، تنرتنیا ایشا ( IoT(

تسرهف بلاطم

ج

لصف :1 لک ی تا هژورپ 1
1-1- همدقم | 2
-1-2 بی نا هلئسم | 3
-1-3 مها یت و ترورض هژورپ | 3
-1-3-1 ازفا یش لباق یت اپ یش حم یط | 4
-1-3-2 ازفا یش تعرس خشت یص اهدادخر | 4
-1-3-3 ناکما اپ یش زا هار د رو | 4
-1-3-4 ی هچراپک زاس ي لرتنک هجت ی تاز | 4
-1-3-5 شهاک نی زا هب لرتنک هدننک اه ي ازجم | 5.
-1-3-6 لباق یت عسوت ه ذپ یري | 5
-1-4 فادها هژورپ | 5
-1-4-1 فده لصا ی | 5
-1-4-2 فادها عرف ی | 5
-1-5 هدودحم هژورپ | 6
-1-6 شور جنا ما هژورپ | 6

لصف :2 نابم ی رظن ي 8
-2-1 همدقم | 9
-2-2 ای تنرتن شا یا | 9
-2-2-1 رعت یف ای تنرتن شا یا | 9
-2-2-2 ازجا ي لصا ی یک هناماس IoT | 9
-2-2-2-1 لایه رگسح | 10
-2-2-2-2 لایه شزادرپ | 10
-2-2-2-3 لایه طابترا ی | 10
-2-2-2-4 لایه دربراک | 10
-2-2-3 دربراک ای تنرتن شا یا رد هناخ شوه دنم | 10
-2-3 سی متس اه ي هناخ دنمشوه | 11
-2-3-1 موهفم هناخ دنمشوه | 11
-2-3-2 اپ یش حم یط | 11
-2-3-3 لرتنک هجت ی تاز | 11
-2-4 می رلرتنکورک 32ESP | 12
-2-4-1 فرعم ی 32ESP | 12
-2-4-2 وی گژ ی اه ي 32ESP | 12
13 | | | | | | | | | | | GPIO-2-4-3
-2-4-4 لدبم گولانآ هب دیجی لات ADC | 13
-2-5 رگسح اه ي حم یطی | 14
-2-5-1 رگسح -2MQ | 14
-2-5-2 رگسح 11DHT | 15
-2-5-2-2 هوحن طابترا 11DHT | 15
-2-5-3 رگسح تدش رون LDR | 15
-2-5-4 رگسح خشت یص تکرح PIR | 16

تسرهف بلاطم

د

-2-6 سی متس رادشه | 17
-2-6-1 رزاب | 17
-2-7 طابترا نودام زمرق | 17
-2-7-2 موهفم IR | 17
-2-7-3 گی هدنر IR | 18
-2-7-4 هدنتسرف IR | 18
-2-7-5 لکتورپ اه ي IR | 18
-2-7-6 هناخباتک 8266IRremoteESP | 18
-2-8 طابترا دار یو یی RF | 19
-2-8-2 موهفم RF | 19
-2-8-3 هناخباتک RCSwitch | 19
20 | | | | | | | | | | | Wi-Fi طابترا -2-9
-2-9-1 فرعم ی Fi-Wi | 20
-2-9-2 تلاح Station | 20
20 | | | | | | | | | Access Point تلاح -2-9-3
20 .... | | | | | | | | | AP_STA تلاح -2-9-4
20 ..... | | | | | | | | | Captive Portal-2-9-5
-2-10 لکتورپ MQTT | 21
-2-10-1 فرعم ی MQTT | 21
-2-10-2 رامعم ي Subscribe/Publish | 21
21 .. | | | | | | | | | MQTT Broker-2-10-3
21 | | | | | | | | | | | Publisher-2-10-4
22 | | | | | | | | | | | Subscriber-2-10-5
22 .. | | | | | | | | | Topic/Payload-2-10-6
22 | | | | | | | | | | | QoS-2-10-7
-2-10-8 طابترا MQTT زا رط یق WebSocket | 22
-2-11 خذ ی هر زاس ي تاعلاطا رد 32ESP | 23
-2-11-1 هظفاح Flash | 23
23 | | | | | | | | | | | LittleFS-2-11-2

لصف :3 لحت یل و حارط ی سی متس 24
-3-1 همدقم | 25
-3-2 لحت یل نی دنمزا ي اه ي سی متس | 25
-3-2-1 نی دنمزا ي اه ي درکلمع ي | 25
-3-2-2 نی دنمزا ي اه ي غیر درکلمع ي | 26
-3-3 رامعم ي لک ی سی متس | 27
-3-3-2 لایه تخس رازفا و عمج روآ ي هداد | 27
-3-3-3 لایه شزادرپ و لرتنک | 28
-3-3-4 لایه طابترا ی و طبار ربراک | 28
-3-4 حارط ی تخس رازفا | 28
-3-4-1 دحاو شزادرپ زکرم ي | 29
-3-4-2 سی متس هزادنا گیري امد و تبوطر | 29

تسرهف بلاطم

ه

-3-4-3 سی متس خشت یص دود و زاگ | 29
-3-4-4 سی متس هزادنا گیري تدش رون | 30
-3-4-5 سی متس خشت یص تکرح | 30
-3-4-6 سی متس طابترا سناکرف دار یو یی | 30
-3-4-7 سی متس طابترا نودام زمرق | 31
-3-4-8 سی متس رادشه توص ی | 31
-3-4-9LED عضو یت | 31
-3-5 اپ یه اه ي 32ESP | 31
-3-6 حارط ی مرن رازفا و راتخاس Firmware | 32
-3-6-1 راتخاس رلاوژام Firmware | 32
-3-6-2 ارف ی دن هار زادنا ي سی متس | 33
-3-6-3 هقلح لصا ی ارجا ي مانرب ه | 33
-3-6-4 دم یریت اهرگسح | 34
-3-6-5 دم یریت رگسح -2MQ | 34
-3-6-6 دم یریت رگسح 11DHT | 35
-3-6-7 دم یریت رگسح PIR | 35
-3-6-8 دم یریت سی متس رادشه | 35
-3-7 حارط ی طابترا Fi-Wi و MQTT | 36
36 | | | | | | | | | | | Wi-Fi طابترا -3-7-1
-3-7-2 طابترا MQTT | 36
-3-7-2-1 راتخاس Topic اه ي MQTT | 36
-3-7-2-2Topic اه ي طوبرم هب اهرگسح | 36.
-3-7-2-3Topic رادشه | 37
-3-7-2-4Topic نامرف | 37.
-3-7-2-5Topic تسرهف سی لانگ اه ي RF و IR | 37
-3-8 حارط ی سی متس RF | 37
-3-8-1 رد ی تفا سی لانگ RF | 37
-3-8-2 خذ ی هر سی لانگ RF | 38
-3-8-3 شخپزاب سی لانگ RF | 38
-3-8-4 دم یریت سی لانگ اه ي خذ ی هر هدش ًRF | 38
-3-9 حارط ی سی متس نودام زمرق | 38
-3-9-1 رد ی تفا سی لانگ IR | 38
-3-9-2 خذ ی هر سی لانگ IR | 39.
-3-9-3 شخپزاب سی لانگ IR | 39
-3-9-4 دم یریت سی لانگ اه ي خذ ی هر هدش IR | 39
-3-10 حارط ی سی متس خذ ی هر زاس ي | 39
-3-10-2 خذ ی هر ظنت ی تام Provisioning | 40
-3-10-3 خذ ی هر ظنت ی تام سد هاگت | 40
-3-10-4 راتخاس خذ ی هر سی لانگ RF | 40
-3-10-5 راتخاس خذ ی هر سی لانگ IR | 41
-3-11 حارط ی سی متس Provisioning | 41
41 .. | | | | | | | | | Captive Portal-3-11-2

تسرهف بلاطم

و

-3-11-3 لاصتا نامزمه AP و Station | 42
-3-12 حارط ی Dashboard Web | 42
-3-12-1 امن یش تاعلاطا اهرگسح | 42
-3-12-2 امن یش عضو یت رادشه | 43
-3-12-3 لاسرا نامرف زا رط یق روبشاد د | 43
-3-13 حارط ی دم یریت اطخ و تاطابترا | 43
-3-14 هناخباتک اه ي مرن رازفا ي دروم هدافتسا | 43

لصف :4 پی هدا زاس ي هناماس 45
-4-1 همدقم | 46
-4-2 حم یط و رازبا اه ي هعسوت | 46
-4-2-1 ظنت ی تام درب و Framework | 47
-4-2-2 ظنت ی تام طابترا رس ی لا | 47
-4-2-3 سی متس اف یل LittleFS | 47
-4-2-4 ارف ی دن تخاس و راذگراب ي Firmware | 47
-4-3 پی هدا زاس ي تخس رازفا | 48
-4-3-1 فرعم ی راتخاس تخس رازفا ي | 48
-4-3-2 پی هدا زاس ي رگسح امد و تبوطر 11DHT | 48
-4-3-3 پی هدا زاس ي رگسح رون LDR | 49
-4-3-4 پی هدا زاس ي رگسح -2MQ | 49
-4-3-5 پی هدا زاس ي رگسح خشت یص تکرح PIR | 49
-4-3-6 پی هدا زاس ي سی تس م رادشه توص ی | 50
-4-4 پی هدا زاس ي سی متس طابترا دار یو یی RF | 51
-4-4-1 فرعم ی سی متس RF | 51
-4-4-2 هار زادنا ي سی متس RF | 51
-4-4-3 راتخاس هداد سی لانگ RF | 51
-4-4-4 رد ی تفا سی لانگ RF | 52
-4-4-5 دم یریت ارف ی دن رد ی تفا سی لانگ | 52
-4-4-6 شخپزاب سی لانگ RF | 53
-4-4-7 دم یریت سی لانگ اه ي خذ ی هر هدش | 53
-4-4-8 تسج و وج سی لانگ RF | 53
-4-4-9 فذح سی لانگ خذ ی هر هدش | 54
-4-4-10 قطنم لک ی رد ی تفا و لاسرا RF | 54
-4-5 پی هدا زاس ي سی متس نودام زمرق IR | 55
-4-5-1 فرعم ی سی متس نودام زمرق | 55
-4-5-2 هار زادنا ي سی متس IR | 56
-4-5-3 راتخاس هداد سی لانگ IR | 56
-4-5-4 رد ی تفا و Decode سی لانگ IR | 57
-4-5-5 دم یریت ارف ی دن رد ی فا ت سی لانگ | 57
-4-5-6 شخپزاب سی لانگ IR | 57
-4-5-7 دم یریت سی لانگ اه ي خذ ی هر هدش | 57
-4-5-8 تسج و وج سی لانگ IR | 58

تسرهف بلاطم

ز

-4-5-9 فذح سی لانگ خذ ی هر هدش | 58
-4-5-10 قطنم لک ی رد ی تفا و لاسرا IR | 59
-4-6 پی هدا زاس ي طابترا Fi-Wi و MQTT | 59
-4-6-1 همدقم | 59
-4-6-2 ای داج Client MQTT | 60
-4-6-3 رارقرب ي طابترا Fi-Wi | 60
-4-6-4 لاصتا هب Broker MQTT | 60
-4-6-5 هار زادنا ي لوا یه MQTT | 61
-4-6-6 رارقرب ي لاصتا ددجم MQTT | 62
-4-6-7 رد ی تفا نامرف اه ي MQTT | 63
-4-6-8 راشتنا تاعلاطا رد MQTT | 63
-4-7 پی هدا زاس ي پی دنبرک ي لوا یه و دم یریت لاصتا هب هکبش | 64
-4-7-1 راتخاس تاعلاطا پی دنبرک ي | 64
-4-7-2AP صاصتخا ی ارب ي پی دنبرک ي | 65
-4-7-3 لاتروپ تحت بو پی دنبرک ي | 65
-4-7-4 پی هدا زاس ي Portal Captive | 65
-4-7-5 دم یریت تساوخرد اه ي HTTP | 65
-4-7-6 رد ی تفا و جنسرابتعا ی ظنت ی تام | 66
-4-8 پی هدا زاس ي دم یریت هظفاح و خذ ی هر زاس ي تاعلاطا | 66
-4-8-1 سی متس اف یل LittleFS | 66
-4-8-2 بلاق JSON | 66
-4-8-3 خذ ی هر و زاب ی با ی عضو یت خشت یص تکرح | 67
-4-8-4 خذ ی هر و زاب ی با ی سی لانگ اه ي RF | 67
-4-8-5 خذ ی هر و زاب ی با ی سی لانگ اه ي IR | 67
-4-8-6 خذ ی هر و زاب ی با ی ظنت ی تام Provisioning | 67
-4-9 هار زادنا ي و گنهامه ی لوژام اه | 68
-4-9-1 عبات setup | 68
-4-9-2 عبات loop | 68
-4-9-3 هار زادنا ي لوژام اه ي تخس رازفا ي | 69
-4-9-4 دم یریت نامرف اه ي سی متس | 69
-4-9-4-1 شزادرپ نامرف اه ي RF | 69
-4-9-4-2 شزادرپ نامرف اه ي IR | 70
-4-9-4-3 دم یریت نامرف اه ي سی تس م رادشه | 70
-4-9-4-4 دم یریت نامرف اه ي خشت یص تکرح | 71
-4-9-5 دم یریت ندناوخ اهرگسح | 71
-4-9-5-1 نامز دنب ي ندناوخ رگسح ها | 72
-4-10 پی هدا زاس ي دروبشاد بو و طبار ربراک ي | 72
-4-10-2 شخب ظنت ی ام ت طابترا اب MQTT | 73
-4-10-3 رد ی تفا و شزادرپ هداد اه ي رگسح اه | 73
-4-10-4 لاسرا نامرف اه ي لرتنک ی | 73
-4-10-5 سی متس رادشه دروبشاد | 73
-4-10-6 خذ ی هر ظنت ی تام دروبشاد | 73

تسرهف بلاطم

ح

لصف :5 نومزآ و زرا ی با ی سی متس 74
-5-1 همدقم | 75
-5-2 شور نومزآ و زرا ی با ی هناماس | 75
-5-2-1 حم یط و هجت ی تاز دروم هدافتسا | 75
-5-2-2 عم ی را اه ي زرا ی با ی | 75
-5-3 نومزآ درکلمع اهرگسح | 76
-5-3-1 نومزآ رگسح امد و تبوطر | 76
-5-3-2 نومزآ رگسح رون | 76
-5-3-3 نومزآ رگسح دود و شتآ | 77
-5-3-4 نومزآ رگسح خشت یص تکرح | 77
-5-4 نومزآ هناماس رادشه | 78
-5-5 نومزآ لاصتا هب Fi-Wi و Broker MQTT | 78
-5-6 نومزآ دروبشاد س هناما | 78
-5-7 نومزآ سی متس RF | 80
-5-7-1 نومزآ رد ی تفا سی لانگ RF | 80
-5-7-2 نومزآ لاسرا سی لانگ RF | 80
-5-7-3 نومزآ دم یریت سی لانگ RF | 80
-5-8 نومزآ سی متس IR | 81
-5-8-1 نومزآ رد ی تفا سی لانگ IR | 81
-5-8-2 نومزآ لاسرا سی لانگ IR | 81
-5-8-3 نومزآ دم یریت سی لانگ IR | 82
-5-9 نومزآ زیر هناماس Provisioning | 83
-5-10 عمج دنب ي لصف | 83

لصف :6 تن ی هج گیري 84
-6-1 همدقم | 85
-6-2 عمج دنب ي لحارم ماجنا هژورپ | 85
-6-3 اتن یج لصاح زا پی هدا زاس ي | 85
-6-4 دودحم یت اه ي هژورپ | 86
-6-5 پی داهنش اه ي هعسوت رد آی هدن | 86
-6-5-1 ازفا یش نما یت تاطابترا | 86
-6-5-2 هدافتسا زا Broker صاصتخا ی | 86
6-5-3- هعسوت لباق یت OTA | 86.
-6-5-4 هفاضا ندرک تاطابترا اج ی زگ ین | 87
-6-6 عمج دنب ي اهن یی | 87

لصف :7 عجارم 88

لصف :8 تسویپ اه 90
8-1- هشقن تامش یک رادم | 91

تسرهف لاکشا

ط

( لکش 1-2) می رلرتنکورک 32ESP | 12
( لکش 2-2) رگسح -2MQ | 14
( لکش 3-2( رگسح 11DHT | 15
( لکش 4-2) رون تدش رگسح | 15
( لکش 5-2) خشت رگسح یص تکرح PIR | 16
( لکش 6-2) رزاب | 17
( لکش 7-2) گی هدنر زمرق نودام هدنتسرف و | 17
( لکش 8-2) گی هدنر دار یو یی | 19
( لکش 9-2) دار هدنتسرف یو یی | 19
( لکش 1-3) رامعم ی لک ی سی متس | 27
( لکش 2-3) زادنا هار دنور ی سی متس | 33
( لکش 3-3) لصا ھقلح دنور ی سی متس | 33
( لکش 4-3) دم دنور یریت اھ رگسح | 34
( لکش 5-3) دم دنور یریت رگسح -2MQ | 34
( لکش 6-3) ھکبش ھب لاصتا رادومن | 42
( لکش 1-4) راذگراب و تخاس دنور ی Firmware | 47.
( لکش 2-4) ارف ی دن رد ی تفا سی لانگ RF | 55
( لکش 3-4) ارف ی دن س لاسرا ی لانگ RF | 55
( لکش 4-4) ارف ی دن رد ی تفا سی لانگ IR | 59
( لکش 5-4) ارف ی دن س لاسرا ی لانگ IR | 59
( لکش 6-4) بو دروبشاد | 72
( لکش 1-5) اتن ی تبوطر و امد رگسح ج | 76
( لکش 2-5) تن ی رون رگسح ھج | 76
( لکش 3-5) اتن ی شتآ و دود رگسح ج | 77
( لکش 4-5) اتن ی خشت رگسح ج ی تکرح ص | 77
( لکش 5-5) تن ی و ھکبش ھب لاصتا نومزآ ھج Broker MQTT | 78
( لکش 6-5) امن ی دروبشاد رد اھرگسح تاعلاطا ش | 79
( لکش 7-5) امن ی دروبشاد رد رادشھ ش | 79
( لکش 8-5) دروبشاد زا نامرف لاسرا | 79
( لکش 9-5) رد ی س تفا ی لانگ RF | 80
( لکش 10-5) س لاسرا ی لانگ RF | 80
( لکش 11-5) دم یری س ت ی لانگ RF | 81
( لکش 12-5) رد ی س تفا ی لانگ IR | 81
( لکش 13-5) س لاسرا ی لانگ IR | 81
( لکش 14-5) دم یری س ت ی لانگ IR | 82
( لکش 15-5) ظنت ھحفص ی تام Provisioning | 83

تسرهف لوادج

ي

( لودج 1-3) اپ یھ اھ ی 32ESP | 31
( لودج 2-3) ظو ی ھف اھ لوژام ی Firmware | 32
( لودج 3-3)Topic اھ ی اھرگسح ھب طوبرم | 36
( لودج 4-3 اف ) یل اھ ی مئاد تاعلاطا ی سی متس | 39
( لودج 5-3) تاصخشم AP | 41
( لودج 6-3 اھ ھناخباتک ) ی هدافتسا دروم | 44
( لودج 1-4 س هداد راتخاس ) ی لانگ RF | 52
( لودج 2-4 س هداد راتخاس ) ی لانگ IR | 56
( لودج 3-4 ظنت هداد راتخاس ) ی تام پی دنبرک ی | 64

# لصف 1 :

# تایلک هژورپ

حارط ی و پی هدا زاس ی خشت دنمشوھ ھناماس یص ھجت لرتنک و دود ی تاز گناخ ی تبم ی رب 32ESP

2

لک ی تا هژورپ
-1-1 همدقم

رد لاـس ياه ،ریخا هعـسوت يروانف ياه یطابترا و هناماـس ياه هتفهن بجوم شرتـسگ هدافتـسا زا متـسیـس ياه دنمـشوه رد طیحم ياه ،ینوکـسم يرادا و یتعنـص هدـش تـسا . یکی زا مهم نیرت هزوح ياه لـصاح زا نیا ،هعـسوت تنرتنیا یـشا ا ( Things of Internet ای IoT ( تـسا . تنرتنیا ایـشا هب کبـش ه يا زا تازیهجت یکیزیف قلاطا یم دوـش هک اب هرهب يریگ زا ،اهرگـسح دنزادرپ ه ،اه مرن اهرازفا و طـساو ياه ،یطابترا تیلباق مج ع ،يروآ ،شزادرپ لدابت تاعلاطا و رد یخرب دراوم لامعا لرتنک رب طیحم نوماریپ دوخ ار دنراد .[1] رد نینچ هناماـس ،ییاه اهرگــسح هفیظو تفایرد تاعلاطا زا ،طیحم دحاو یــشزادرپ هفیظو لیلحت و تیریدم هداد اه و شخب یطابترا هفیظو لاقتنا تاعلاطا و تفایرد ف نامر ياه یلرتنک ار رب هدهع دراد . [1] [2] یکی زا ياهدربراک مهم تنرتنیا ،ایـشا هعـسوت هناماـس ياه دنمـشوه یگناخ تـسا . رد کی طیحم ،دنمـشوه تازیهجت فلتخم یم دنناوت زا قیرط کی هکبـش یطابترا اب رگیدکی و اب ربراک ت لماع هتـشاد دنـشاب . نیا لماعت یم دناوت لماــش شیاپ طیارــش ،یطیحم صیخــشت دادخر ياه ،يداعریغ لاــسرا ،رادــشه لرتنک تازیهجت یکیرتکلا و تبث تاعلاطا دــشاب . هدافتــسا زا نینچ هناماــس ییاه یم دناوت ناکما تراظن زا هار رود و شهاک یگتسباو هب لرتنک یتسد تازیهجت ار مهارف دنک . رد ا نی ،هژورپ کی باه دنمـشوه ینتبم رب درب 32ESP یحارط و دایپ ه يزاـس هدـش ـسا ت . 32ESP کی هناماـس يور هـــشارت اـب تـیلباـق Fi-Wi رد دـناـب 2.4 ،زترهاـگیگ هدـنزادرپ 32 یتیب و هـعومجم يا زا طـــساو ياـه يدورو / یجورخ لاتیجید و گولانآ تـسا هک طـسوت تکرـش Espressif هئارا هدـش و يارب ییاهدربراک زا هلمج تازیهجت دنمـشوه یگناخ و تنرتنیا ایـشا بـسانم ـسا ت. [3] نیا گژیو ی اه ثعاب هدـش تـسا 32ESP دناوتب هولاع رب شزادرپ داد ه ياه ،اهرگـسح طابترا کبـش ه يا و لرتنک تازیهجت یبناج ار زین رد کی دحاو تخـس يرازفا ماجنا دهد .
متـسیـس هعـسوت هتفای رد نیا هژورپ هولاع رب صیخـشت دود و ،زاگ ناکما هزادنا يریگ ،امد تبوطر و تدـش رون و نینچمه صیخـــشت تـکرح ار مهارف یم دـنک . نینچمه يارب شیازفا تـیلباـق لرتنک تازیهجت ،فلتخم ود هـعومجم طاـبترا ییویدار رد سناـکرف ياـه 315 و 433 زترهاـگم و کـی هـعومجم طاـبترا نوداـم زمرق رد رظن هتفرگ هدـش تـسا . هب نیا ،بیترت متـسیـس رداق تـسا یخرب لانگیـس ياه ییویدار و نودام زمرق ار ،تفایرد هریخذ و رد تروص زاین شخپزاب دنک . طابترا نایم باه دنمـشوه و تخاـسریز مرن يرازفا متـسیـس زا قیرط Fi-Wi و لکتورپ MQTT ماجنا یم دوـش . MQTT کی لکتورپ طابترا ی کبـس ینتبم رب يوگلا راـشتنا / كارتـشا (Subscribe/Publish (تـسا هک هب روط هژیو يارب طیحم ياه ياراد تیدودحم عبانم و ياهدربراک نیـشام به نیـشام و تنرتنیا ایـشا بـسانم یحارط هدـش ـسا ت. [4] رد نیا ،هژورپ هداد ياه اهرگـسح زا قیرط MQTT رـشتنم هدـش و امرف ن ياه یلرتنک زین زا قیرط نیمه رتسب هب 32ESP لاسرا یم دنوش . زا يوــس ،رگید يارب لماعت ربراک اب ،متــسیــس کی دروبــشاد تحت بو یحارط هدــش تــسا هک زا قیرط WebSocket هب Broker MQTT لـصتم یم دوـش . نیا دروبـشاد ناکما هدهاـشم تاعلاطا ،اهرگـسح هدهاـشم اهرادـشه و را لاـس نامرف ياه یلرتنک ار مهارف یم دنک . رد ،هجیتن هژورپ رـضاح ار یم ناوت کی باه دنمـشوه نچ د هروظنم تــسناد هک فیاظو شیاپ ،طیحم صیخــشت ،دادخر داجیا ،رادــشه طابترا بــش هک يا و لرتنک تازیهجت ار رد کی هناماس هچراپکی ماجنا یم دهد .

3

لک ی تا هژورپ
-1-2 نایب هلئسم

رد يرایـسب زا طیحم ياه ینوکـسم و ،يرادا تازیهجت یکیرتکلا و هناماـس ياه فلتخم هب تروـص لقتـسم دروم هدافتــسا رارق یم دنریگ و تاعلاطا طوبرم هب طیارــش یطیحم زین ًلاومعم هب تروــص زکرمتم و رمتــسم عمج يروآ من ی دوــش . رد شور ياه ،یتنــس صیخــشت ییاهدادخر دننام شیازفا نازیم دود ای ،زاگ تارییغت ،امد روـضح دارفا ای رییغت دیدـش طیارـش يرون نکمم تـسا هب تروـص یتـسد ای طـسوت تازیهجت لقتـسم ماجنا دوـش . نینچ يدرکیور هولاع رب شیازفا یگدـیچیپ ،متـــسیـــس ناـکما شیاـپ هـچراـپکی و لرتنک زا هار رود ار دودـحم یم دنک .
زا فرط ،رگید يرایــسب زا تازیهجت دوجوم رد طیحم ياه یگناخ زا شور ياه ابترا یط یتوافتم يارب لرتنک هداـفتـــسا یم دـننک . یخرب تازیهجت زا ومیر ت ياـه نوداـم زمرق و یخرب رگید زا تومیر ياـه ییویدار رد سناـکرف ییاـه دـنناـم 315 اـی 433 زترهاـگم هداـفتـــسا یم دـننک . رد ،هـجیتن يارب لرتنک هـچراـپکی نیا تازیهجت ًلاومعم زاین هب نیدنچ رتنک ل هدننک و طساو ازجم وجو د دراد . هلئـسم یلـصا نیا ،هژورپ یحارط و هدایپ يزاـس کی هناماـس هچراپکی تـسا هک دناوتب تاعلاطا طوبرم هب طیارـش طیحم ار زا قیرط هـعومجم يا زا اـهرگـــسح تـفاـیرد ،هدرک نآ اـه ار رد کـی دـحاو یـــشزادرپ تـیریدـم ،دـنک تاعلاطا ار زا قیرط هکبـش Fi-Wi و MQTT رد رایتخا مرن رازفا رارق د ده و ناکما لرتنک تازیهجت یکیرتکلا ار زین مهارف دنک .
يارب یبایتسد هب نیا ،فده زا 32ESP هب ناونع هتسه یشزادرپ و یطابترا متسیس هدافتسا هدش تسا . رد شخب شیاپ ،طیحم روـسنـس -2MQ يارب صیخـشت دود و ياهزاگ لباق ،لاعتـشا روـسنـس 11DHT يارب هزادنا يریگ امد و ،تبوطر رگـسح ون ير LDR يارب هزادنا يریگ یبـسن تدـش رون و رگـسح یتکرح PIR يارب صیخـشت تکرح دروم هدافتـسا رارق هتفرگ دنا . تاعلاطا به تـسد هدمآ زا نیا اهرگـسح هب تروـص هرود يا شزادرپ و زا قیرط MQTT رشتنم یم دنوش . رد شخب لرتنک زین متــسیــس زا هدنریگ و هدنتــسرف ياه RF رد ود دناب 315 و 433 زترهاگم و نینچمه هدنریگ و هدنتـسرف نودام زمرق هدافتـسا یم دنک . هناخباتک RCSwitch ناکما تفایرد و لاـسرا ياهدک یخرب تازیهجت ییویدار جیار رد سناـکرف ياـه 315 و 433 زترهاـگم ار مهارف یم دـنک . [5] نینچمه هـناـخباـتک 8266IRremoteESP يارب د تفایر و لاسرا لانگیس ه يا نودام زمرق دروم هدافتسا رارق هتفرگ تسا . [6] ،نیاربانب هلئـسم نیا هژورپ ار یم ناوت هب تروـص یحارط کی باه دنمـشوه فیرعت درک هک هـس هفیظو یلـصا ار رد کی رتسب دحاو بیکرت یم نک د:
- شیاپ طیارش یطیحم
- صیخشت دادخر و جیا دا رادشه
- لرتنک تازیهجت یکیرتکلا و تفایرد / شخپزاب نامرف ياه یب میس

-1-3 تیمها و ترورض هژورپ

شیازفا هدافتـسا زا تازیهجت یکیرتکلا و شرتـسگ متـسیـس ياه ،دنمـشوه زاین هب هناماـس ییاه ار شیازفا هداد تـسا هک دناوتب هولاع رب لرتنک ،تازیهجت تیعضو طیحم ار زین شیاپ دننک . یکی زا م تیز ياه یلصا هدافتسا زا تنرتنیا ایـشا رد نینچ هناماـس ،ییاه داجیا طابترا نایم يایند یکیزیف و هناماـس ياه مرن يرازفا ؛تـسا هب هنوگ يا هک تاعلاطا رگسح اه یم دنناوت ،تفایرد لقتنم و رد شخب مرن يرازفا شزادرپ دنوش .

4

لک ی تا هژورپ
تیمها نیا هژورپ ار یم ناوت زا بنج ه ياه فلتخم یسررب درک .

-1-3-1 شیازفا تیلباق شیاپ طیحم

دوجو نیدنچ رگـسح رد کی هناماـس ناکما عمج آ يرو هم نامز تاعلاطا فلتخم یطیحم ار مهارف یم دنک . رد هژورپ ،رـضاح تاعلاطا طوبرم هب ،امد ،تبوطر تدـش ،رون نازیم دود و تیعـضو تکرح رد رایتخا متـسیـس رارق یم دریگ . نیا تاعلاطا یم دنناوت يارب یـسررب تیعـضو ظحل ه يا طیحم و صیخـشت یخرب طیارـش يداعریغ دروم هدافتسا رارق دنریگ .

-1-3-2 شیازفا تعرس صیخشت هدادخر ا

هدافتسا زا روسنس ياه یطیحم ناکما شنکاو یرس ع رت متسیس تبسن هب ییاهدادخر دننام شیازفا رادقم زاگ ای دود و صیخـشت تکرح ار مهارف یم دنک . رد هژورپ ،رـضاح رد تروـص روبع رادقم دناوخ ه هدـش زا روـسنـس -2MQ زا هناتسآ نییعت ،هدش متسیس تیعضو رادشه ار لاعف هدرک و مایپ هطوبرم ار زا قیرط MQTT رشتنم یم دنک . نینچمه رد تروص صیخشت ،تکرح ناکما داجیا رادشه و لاعف يزاس رزاب دوجو دراد .

-1-3-3 ناکما شیاپ زا هار ود ر

طابترا Fi-Wi و MQTT ثعاب یم دوـش تاعلاطا مج ع يروآ هدـش اهنت رد حطـس دوخ هاگتـسد یقاب دنامن و ناوتب نآ اـه ار هـب کـی Broker و مرن ياـهرازفا رگید لـقتنم درک . MQTT هـب لـیلد هداـفتـــسا زا لدـم Subscribe/Publish، ناکما يزاـسادج هدننکدیلوت و فرـصم هدننک هداد ار مهارف یم دنک و يارب طابترا نایم تازیهجت IoT بسانم سا ت. [4]

-1-3-4 هچراپکی يزاس لرتنک تازیهجت

یکی زا یگژیو ياه مهم ،هژورپ بیکرت شیاپ طیحم اب لرتنک تازیهجت یکیرتکلا تــسا . متــسیــس یم دناوت انگیـس ل ياه RF رد ود دناب 315 و 433 زترهاگم ار تفایرد و هریخذ هدرک و رد نامز بـسانم ب شخپزا دنک . هـناـخباـتک RCSwitch زین يارب لرتنک تازیهجت ییویدار جیار اـب دـنتـــسرف ه اـه و هدـنریگ ياـه 315 و 433 زترهاگم یحارط هدش تسا . [5] نینچمه هدافتـسا زا طابترا نودام زمرق ثعاب یم دوـش متـسیـس دناوتب اب یخرب تازیهجت زهجم هب تومیر IR لماعت هتـشاد دـشاب . هناخباتک 8266IRremoteESP يارب 32ESP ناکما تفایرد و لاـسرا لانگیـس ياه نودام زمرق و ینابیتشپ زا لکتورپ ياه ددعتم ار مهارف یم ک دن . [6]

5

لک ی تا هژورپ
-1-3-5 شهاک زاین هب لرتنک هدننک ياه ازجم

بیکرت نیدنچ تیلباق رد کی درب 32ESP ثعاب یم ـش دو هب ياج هدافتـسا زا دنچ متـسیـس لقتـسم يارب شیاپ ،طیحم تفایرد نامرف ياه یب میس و لرتنک ،تازیهجت ناوتب شخب لباق یهجوت زا نیا فیاظو ار رد کی باه دحاو هدایپ يزاس درک .

-1-3-6 تیلباق هعسوت يریذپ

يرامعم رلاوژام مرن ،رازفا هدافتسا زا MQTT و تیلباق ياه یطابترا 32ESP ناکما هعسوت متسیس رد هدنیآ ار مهارف یم دنک . يارب ،لاثم یم ناوت ياهرگــسح ،دیدج تازیهجت یلرتنک رتــشیب ای سیورــس ياه مرن يرازفا رگید ار نودب رییغت یساسا رد راتخاس یلک متسیس هب نآ هفاضا درک .

-1-4 فادها هژورپ

-1-4-1 فده یلصا

فده یلـصا نیا ،هژورپ یحارط و هدایپ يزاـس کی ـس هناما دنمـشوه ینتبم رب 32ESP يارب صیخـشت دود و شتآ و شیاپ طیحم و لرتنک تازیهجت یکیرتکلا زا قیرط هکبش Fi-Wi تسا .

-1-4-2 فادها یعرف

فادها یعرف هژورپ ترابع دنا زا : .1 یحارط و هدایپ يزاس شخب تخس يرازفا ینتبم رب 32ESP .2 صیخشت دوجو دود و طیارش طبترم اب شتآ اب هدافتسا زا -2MQ .3 هزادنا يریگ امد و تبوطر طیحم اب هدافتسا زا 11DHT .4 هزادنا يریگ تدش رون طیحم اب هدافتسا زا LDR .5 صیخشت روضح ای تکرح رد طیحم اب هدافتسا زا رگسح PIR .6 داجیا متسیس رادشه یتوص اب هدافتسا زا رزاب .7 تفایرد لانگیس ياه نودام زمرق زا رلرتنک تازیهجت فلتخم .8 هریخذ نامرف ياه نودام زمرق تفایرد هدش

6

لک ی تا هژورپ
.9 لاسرا لانگیس ياه نودام زمرق يارب لرتنک تازیهجت لتخم ف .10 تفایرد و لاسرا لانگیس ياه ییویدار يارب لرتنک تازیهجت ییویدار .11 يرارقرب طابترا هاگتسد اب هکبش Fi-Wi .12 هدافتسا زا MQTT يارب لدابت تاعلاطا نایم هاگتسد و هناماس مرن يرازفا .13 داجیا تیلباق شیاپ متسیس زا هار رود .14 مهارف ندرک ناکما لرتنک تازیهجت یکیرتکلا زا قیرط هناماس مرن يرازفا .15 داجیا يراتخاس لباق هعسوت يارب هفاضا ندرک اهرگسح و تیلباق ياه دیدج رد هدنیآ

-1-5 هدودحم هژورپ

هدودحم نیا ژورپ ه لماـش یحارط و هدایپ يزاـس کی هنومن یتایلمع زا هناماـس دنمـشوه شیاپ و لرتنک طیحم ینتبم رب 32ESP تـــسا . رد نیا ،هژورپ 32ESP هـب ناونع دـحاو شزادرپ يزکرم هـفیظو تـفاـیرد تاـعلاطا زا ،اهرگـسح شزادرپ هداد ،اه تیریدم تاطابترا و لاـسرا ای تفایرد لانگیـس ياه نودام زمرق و ویدار یی ار رب هدهع دراد .
- صیخشت دود و طیارش طبترم اب شتآ
- هزادنا يریگ امد و تبوطر و تدش رون
- صیخشت تکرح
- لاسرا و تفایرد لانگیس ياه نودام زمرق
- لاسرا و تفایرد لانگیس ياه ییویدار
- لاصتا هاگتسد هب Fi-Wi
- طابترا اب هناماس مرن يرازفا
- لاسرا تاعلاطا اهرگسح هب هناماس مرن يرازفا
- تفایرد نامرف زا هناماس مرن يرازفا يارب لرتنک تاریهجت یکیرتکلا اب دوجو تیلباق ياه ،قوف هژورپ ياراد هدودحم یـصخـشم تـسا . يارب ،لاثم درکلمع صیخـشت شتآ رد نیا هژورپ رد حطـس کی هناماـس هنومن و یـشزومآ / یـسدنهم رد رظن هتفرگ هدـش و دیابن نآ ار هب ناونع نیزگیاج زیهجت تا ینمیا و ملاعا قیرح ياراد هـیدـییاـت درادـناـتـــسا يارب دربراـک ياـه یتاـیح رد رظن تـفرگ . نینچمه لرتنک تازیهجت زا قیرط IR و RF هب عون لکتورپ و يراگزاس تازیهجت دصقم هتسباو تسا .

-1-6 شور ماجنا هژورپ

دنیارف ماجنا هژورپ هب تروـص هلحرم يا و رب ساـسا يدنمزاین ياه تخـس يرازفا و ن مر يرازفا متـسیـس ماجنا هدـش تـسا . رد هلحرم ،تـسخن هلئـسم و يدنمزاین ياه یلـصا متـسیـس لماـش صیخـشت طیارـش ،رطخ شیاپ طیحم و لرتنک تازیهجت یکیرتکلا یـسررب دـش . سپـس يرامعم یلک متـسیـس و هوحن طابترا نایم ،اهرگـسح 32ESP و هناماس مرن يرازفا صخشم دیدرگ .

7

لک ی تا هژورپ
رد هـلحرم ،دـعب تاـعطق تـخـــس ا يرازف زاـیندروم باـختنا و رادـم هـیلوا یحارط دـــش . 32ESP هـب ناونع لرتنک هدننک يزکرم باختنا ؛دـش اریز هولاع رب تیلباق ،یـشزادرپ تاناکما یطابترا زایندروم هژورپ زا هلمج Fi-Wi ار رد رایتخا رارق یم دهد .
سپ زا یحارط تخس ،رازفا Firmware هاگتسد هعسوت هداد دش . نیا شخب فیظو ه ندناوخ تاعلاطا ،اهرگسح صیخـشت تیعـضو ياه ،فلتخم تیریدم يدورو و یجورخ ،اه تفایرد و لاـسرا لانگیـس ياه IR و RF و نینچمه تیریدم طابترا هکبش ار رب هدهع دراد . رد شخب ،یطابترا هاگتـسد زا قیرط Fi-Wi هب هکبـش لـصتم هدـش و طابترا نایم 32ESP و هناماـس مرن يرازفا اب هدافتـسا زا MQTT رارقرب هدـش تـسا . رد نیا ،يرامعم هاگتـسد یم دناوت تاعلاطا طوبرم هب اهرگـسح و تیعـضو دوخ ار رد Topic ياه صخـشم رـشتنم دنک و رد ،لباقم مایپ ياه یلرتنک ار زا Topic ياه هطوبرم تفایرد دیامن .
رد همادا شخب مرن يرازفا هعـسوت هداد دـش ه و تیلباق هدهاـشم تاعلاطا و لاـسرا نامرف ياه یلرتنک رد نآ مهارف هدش تسا .
سپ زا لاـصتا يازجا ،فلتخم شیامزآ ياه طوبرم هب ،اهرگـسح طابترا Fi-Wi، لدابت مایپ MQTT و درکلمع هدنتسرف و هدنریگ ياه IR و RF ماجنا هدش تسا . رد ،تیاهن درکلمع یلک هناماس اب یسررب ویرانس ياه فلتخم دروم یبایزرا رارق هتفرگ تسا .

# لصف 2 :

# ینابم يرظن

نابم ی رظن ی

-2-1 همدقم

شرتـسگ يروانف ياه ،یطابترا رلرتنکورکیم ياه مک فرـصم و هکبـش ياه یب میـس ثعاب هدـش تـسا هک تازیهجت یکینورتکلا دـنناوتب هولاع رب ماـجنا فیاـظو ،یلرتنک تاـعلاطا طیحم نوماریپ دوخ ار زین تـفاـیرد و زا قیرط هکبــش لقتنم دننک . نیا درکیور یکی زا هیاپ ياه یلــصا لکــش يریگ تنرتنیا ایــشا ( of Internet Things ای IoT ( تسا .
رد هناماـس ياه ،دنمـشوه بیکرت رگـسح ،اه دحاو ،شزادرپ بترا طا هکبـش و مرن رازفا يدربراک ناکما شیاپ طیارــش یطیحم و لرتنک تازیهجت ار مهارف یم دنک . رد کی هناخ ،دنمــشوه نینچ هناماــس يا یم دناوت یتاعلاطا دننام ،امد ،تبوطر تدـش ،رون دوجو دود ای شتآ ار تفایرد هدرک و رد ،لباقم تازیهجت فلتخم ار زا قیرط تاطابترا یب میس لرتنک دنک . هژورپ رــضاح کی متــسیــس دنمــشوه ینتبم رب 32ESP تــسا هک هولاع رب شیاپ طیارــش ،یطیحم تیلباق یخـشت ص دود و ،شتآ صیخـشت ،تکرح داجیا رادـشه یتوـص و تفایرد و لاـسرا نامرف ياه نودام زمرق و ییویدار ار مهارف یم دنک . طابترا هاگتــسد اب تخاــسریز هکبــش زا قیرط Fi-Wi و لدابت هداد اب هدافتــسا زا لکتورپ MQTT ماجنا یم دوش .

-2-2 تنرتنیا ایشا

-2-2-1 فیرعت تنرتنیا ایشا

تنرتنیا ایــشا هب هعومجم يا زا تازیهجت یکیزیف هتفگ یم دوــش هک ياراد ،رگــسح تیلباق شزادرپ و طابترا هکبـش هدوب و یم دنناوت تاعلاطا طوبرم هب طیحم ای تیعـضو دوخ ار عمج يروآ و اب ریاـس هناماـس اه هلدابم دننک . [1]
رد کی هناماس IoT ًلاومعم هس هفیظو یلصا دوجو دراد :
- تفایرد تاعلاطا زا طیحم
- شزادرپ و ریسفت تاعلاطا
- لاسرا تاعلاطا ای يارجا نامرف رد هژورپ ،رــضاح ياهرگــسح -2MQ، 11DHT،LDR و PIR هفیظو تفایرد تاعلاطا یطیحم ار رب هدهع دنراد 32.ESP هفیظو شزادرپ هیلوا ار ماجنا هداد و Fi-Wi و MQTT يارب لاقتنا تاعلاطا هب راک یم دنور .

-2-2-2 يازجا یلصا کی هناماس IoT

کی هناماس تنرتنیا ایشا ار یم ناوت هب دنچ شخب میسقت درک :

نابم ی رظن ی
-2-2-2-1 هیلا رگسح
رد نیا هیلا ، تاعلاطا زا طیحم تفایرد یم دوــش . رگــسح یم دناوت یتیمک یکیزیف دننام ،امد ،تبوطر ،رون تکرح ای تظلغ زاگ ار هب لانگیس یکیرتکلا لیدبت دنک . رد هژورپ رضاح نیا هیلا لماش دراوم ریز تسا : DHT11 •
LDR •
MQ-2 •
PIR •

-2-2-2-2 هیلا شزادرپ
رد نیا ،هیلا هداد ياه تفایرد ،هدـش شزادرپ هدـش و میمـصت ياه مزلا هتفرگ یم دوـش . 32ESP هتـسه یلـصا شزادرپ رپ هژو تسا .

-2-2-2-3 هیلا یطابترا
نیا هیلا هفیظو لاقتنا هداد نیب هاگتـسد و ریاـس يازجا هناماـس ار رب هدهع دراد . رد نیا هژورپ زا Fi-Wi يارب طابترا اب هکبش و زا لکتورپ MQTT يارب لاقتنا هداد هدافتسا هدش تسا .

-2-2-2-4 هیلا دربراک
رد نیا ،هیلا تاعلاطا هب ربراک شیامن هداد هدـش و نامرف ياه یلرتنک تفایرد یم دنوـش . دروبـشاد بو هژورپ زا قیرط WebSocket over MQTT اب Broker طابترا رارقرب یم دنک .

-2-2-3 دربراک تنرتنیا ایشا رد هناخ دنمشوه

هناخ دنمـشوه یکی زا دربراک ياه مهم IoT تـسا . رد نینچ هناماـس ،يا تازیهجت فلتخم یم دنناوت هب هکبـش لصتم هدش و زا قیرط کی متسیس يزکرم لرتنک ای شیاپ دنوش . یخرب دربراک ياه جیار ترابع دنا زا :
- لرتنک ییانشور
- لرتنک مزاول کیرتکلا ی
- شیاپ امد و تبوطر
- صیخشت تکرح
- صیخشت دود و گ زا
- متسیس ياه ادشه ر
- ک لرتن تازیهجت ص یتو و يریوصت
- تیریدم فرصم ژرنا ي
رد هژورپ ،رـضاح بیکرت شیاپ یطیحم و لرتنک تازیهجت ثعاب هدـش تـسا هک هاگتـسد هولاع رب شقن کی ،روسنس هب ناونع کی باه لرتنک هدننک و نویساموتا هناخ زین لمع دنک .

نابم ی رظن ی
-2-3 متسیس ياه هناخ دنمشوه

-2-3-1 موهفم هناخ دنمشوه

هناخ دنمــشوه یطیحم تــسا هک رد نآ ت تازیهج فلتخم زا قیرط يروانف ياه یطابترا هب رگیدکی لــصتم هدش و ناکما شیاپ و لرتنک نآ اه هب تروص راکدوخ زا هار رود مهارف یم دوش . رد کی متـــسیـــس هناخ ،دنمـــشوه طابترا نایم تازیهجت یم دناوت اب يروانف ياه یفلتخم دننام Zigbee، Bluetooth، Fi-Wi، Wave-Z ای يروانف ياه بم ینت رب تنرتنیا ایشا ماجنا دوش . رد هژورپ ،رضاح يارب طابترا هاگتسد اب هکبش زا Fi-Wi هدافتسا هدش و يارب لرتنک تازیهجت زا هار رود زا IR و RF هدافتسا یم دوش .

-2-3-2 شیاپ طیحم

شیاپ طیحم هب دنیارف هزادنا يریگ موادم ای هرود يا رتماراپ ياه یطیحم هتفگ یم دوش . رتماراپ ياه دروم هدافتسا رد نیا هژورپ ترابع دنا زا :
- امد
- تبوطر
- تدش رون
- تدش زاگ ياه دوجوم رد طیحم
- تیعضو تکرح و روضح
هداد ياه لصاح زا نیا رگسح اه رد لصاوف ینامز صخشم هدناوخ و زا قیرط MQTT رشتنم یم دنوش .

-2-3-3 لرتنک تازیهجت

یکی زا تیلباق ياه مهم هناخ ،دنمـشوه لرتنک تازیهجت یکیرتکلا نودب زاین هب هدافتـسا میقتـسم زا لرتنک هدننک یلصا نآ تسا .
رد هژورپ ،رضاح يارب نیا روظنم ود شور یلصا دوجو دراد :
- نودام زمرق ( IR :(
نداتسرف لانگیس : هاگتسد → EL I → 32SE نتفرگ لانگیس : 32SE → evieceR I → لرتنک هاگتسد
- ناکرف س ییویدار ( RF :(
نداتسرف لانگیس : هاگتسد → ettimsnarT R → 32SE نتفرگ لانگیس : 32SE → evieceR R → تومیر هاگتسد

نابم ی رظن ی
-2-4 رلرتنکورکیم 32ESP

-2-4-1 یفرعم 32ESP

32ESP کی هداوناخ زا SoC ياه تکرـش Systems Espressif تـسا هک يارب دربراک ياه یطابترا و متـسیـس ياه هتفهن یحارط هدــش تــسا . نیا هداوناخ ياراد هدنزادرپ 32 ،یتیب ،هظفاح Fi-Wi، ADC، Bluetooth و هـعومجم يا زا طبار ياـه یبناـج تـــسا . قبط تادـنتـــسم ،یمـــسر 32ESP زا Fi-Wi اـب درادـناـتـــسا ياـه n/g/b802.11 ینابیتــشپ هدرک و ياراد ADC اود هدز ،یتیب GPIO ياه ،ددعتم PWM، C2I، SPI و ریاــس دحاو ياه یبناج تسا . [3]
دوجو Fi-Wi یلخاد یکی زا لیلاد یلـصا باختنا 32ESP يارب نیا هژورپ ؛تـسا اریز هاگتـسد یم دناوت نودب زاین هب لوژام یطابترا هناگادج هب هکبش لصتم دوش .

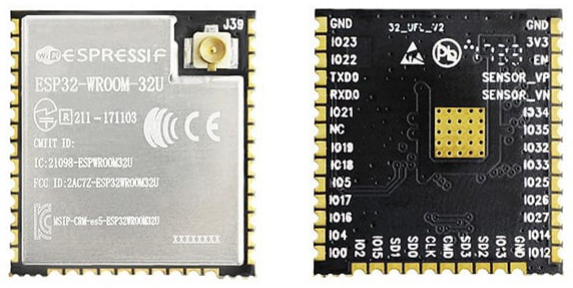
[picture p65: figure]

لکش (2-1 ) رلرتنکورکیم 32ESP

-2-4-2 یگژیو ياه 32ESP

یخرب یگژیو ياه مهم 32ESP ترابع دنا زا : [3]
- هدنزادرپ 32 یتیب 6LX Xtensa Wi-Fi 802.11 b/g/n •
Bluetooth •
- GPIO لباق همانرب يزیر
ADC •
DAC •
PWM •
UART •
SPI •
I2C •

نابم ی رظن ی

RMT •
- رمیات
- هظفاح SRAM
- هظفاح Flash

GPIO -2-4-3

GPIO ای Output/Input Purpose General هیاپ ياه لباق همانرب يزیر رلرتنکورکیم دنتــسه هک یم دنناوت يارب تفایرد ای لاسرا لانگیس لاتیجید هدافتسا دنوش . رد نیا هژورپ زا GPIO اه يارب لاصتا یتازیهجت دننام : PIR •
Buzzer •
IR LED •
IR Receiver •
RF Transmitter •
RF Receiver •
هدافتسا هدش تسا .

-2-4-4 لدبم گولانآ هب لاتیجید ADC

ADC اـی Converter Digital-to-Analog هـفیظو لـیدـبت کـی لاـنگیـــس ژاـتلو گولاـنآ هـب رادـقم لاـتیجید لـباـق شزادرپ طسوت رلرتنکورکیم ار رب هدهع دراد . رد هژورپ رضاح یجورخ گولانآ ود رگسح یلصا هب ADC لصتم هدش تسا : LDR •
MQ-2 •
رد کی ADC هدزاود یتیب رادقم لاتیجید يروئت رد هدودحم : 0 ≤ ADC ≤ 4095
رارق یم دریگ .

نابم ی رظن ی
-2-5 رگسح ياه یطیحم

-2-5-1 رگسح -2MQ

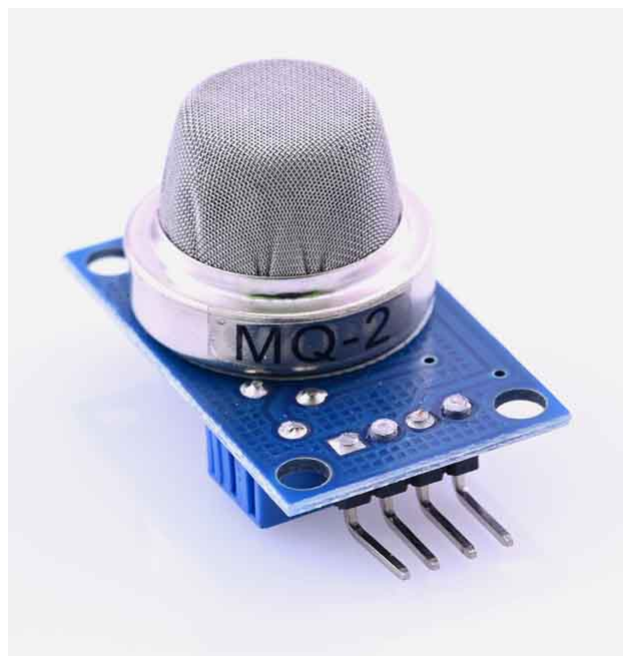
[picture p66: figure]

لکش (2-2 ) رگسح -2MQ

-2MQ کی رگـسح زاگ زا هداوناخ رگـسح ياه يزاگ یتمواقم تـسا هک يارب صیخـشت زاگ ياه لباق لاعتـشا و دود هدافتسا یم دوش .
قباطم تاعلاطا ینف رشتنم هدش يارب -2MQ، نیا رگسح يارب صیخشت يداوم دننام : LPG •
- ناتم
- ناپورپ
- ناتوب
- لکلا
- نژوردیه
- دود
دربراک دراد .[7]
درکلمع رگـسح رب ساـسا رییغت تمواقم هدام ساـسح هب زاگ رد روـضح زاگ ياه رظندروم تـسا . رییغت تمواقم ثعاب رییغت لانگیس یجورخ یم دوش هک یم ناوت نآ ار طسوت ADC ورکیم رلرتنک هزادنا يریگ درک . شیپ شیامرگ -2MQ
رگــسح ياه هداوناخ MQ يارب ندیــسر هب تیعــضو يراک رادیاپ هب نامز گ مر ندــش زاین دنراد و رادقم نآ هلـصافلاب دعب زا نـشور ندـش يارب میمـصت يریگ هدافتـسا یمن دوـش و کی هرود شیپ شیامرگ رد رظن هتفرگ یم دوش .[7]
تیدودحم -2MQ
-2MQ کی رگـسح یمومع صیخـشت زاگ و دود تـسا و دیابن نآ ار هب ییاهنت لداعم کی متـسیـس دناتـسا درا صیخـشت و ملاعا قیرح رد رظن تفرگ . رادقم هدناوخ هدـش زا نیا رگـسح هب طیارـش ،یطیحم زاگ دروم ،رظن ،امد ،تبوطر نامز مرگ ندش و راتخاس رادم هتسباو تسا .

نابم ی رظن ی
-2-5-2 رگسح 11DHT

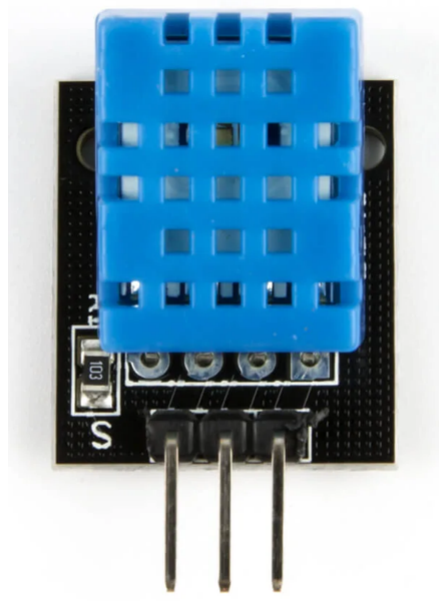
[picture p67: figure]

لکش (2-3 ) رگسح 11DHT

11DHT کی رگـسح لاتیجید يارب هزادنا يریگ مه نامز امد و تبوطر یبـسن تـسا و هداد ياه هزادنا يریگ هدش 11DHT اب کی لکتورپ لاتیجید هب رلرتنکورکیم لقتنم یم دوش .

-2-5-2-2 هوحن طابترا 11DHT طاـبترا 11DHT اـب رلرتنکورکیم رب هـیاـپ کـی طبار کـت یمیـــس و ناـمز يدـنب صخـــشم ماـجنا یم دوـــش . رلرتنکورکیم تـساوخرد هزادنا يریگ ار لاـسرا هدرک و سپـس هداد ياه طوبرم هب امد و تبوطر ار تفایرد یم دنک .
هـناـخباـتک DHT Adafruit ناـکما داـجیا یـــش DHT و ندـناوخ میقتـــسم اـمد و تـبوطر ار مهارف یم دـنک . تادنتسم یمسر نیا هناخباتک یعباوت دننام ()readTemperature و ()readHumidity ار هئارا یم دهد .[8]

-2-5-3 رگسح تدش رون LDR


لکش (2-4 ) رگسح تدش رون

نابم ی رظن ی

LDR ای Resistor Dependant Light کی تمواقم هتــسباو هب رون تــسا هک رادقم تمواقم یکیرتکلا نآ اب تدش رون رییغت یم دنک .
رد تلاح یلک اب شیازفا تدـش ،رون تمواقم LDR رییغت یم دنک و اب رارق نداد نآ رد کی رادم میـسقت ژاتلو یم ناوت رییغت تمواقم ار هب رییغت ژاتلو لیدبت درک .

-2-5-4 رگسح صیخشت تکرح PIR


لکش (2-5 ) رگسح صیخشت تکرح PIR

رگــسح PIR ای Sensor Infrared Passive يارب صیخــشت تارییغت شبات نودام زمرق طیحم هدافتــسا یم دوش .
ندب ناـسنا و ریاـس ماـسجا مرگ شبات نودام زمرق رـشتنم یم دننک . یماگنه هک کی مـسج مرگ رد هدودحم دید رگسح تکرح یم ،دنک رییغت شبات یتفایرد طسوت رگسح صیخشت هداد هدش و لوژام یجورخ لاتیجید دیلوت یم دنک .

نابم ی رظن ی
-2-6 متسیس رادشه

-2-6-1 رزاب


لکش (2-6 ) رزاب

رزاب کی لدبم یکیرتکلا هب یتوص تسا هک اب تفایرد لانگیس ،بسانم يادص رادشه داجیا یم دنک .

-2-7 طابترا نودام زمرق


لکش (2-7 ) هدنریگ و هدنتسرف نودام زمرق

-2-7-2 موهفم IR

نودام زمرق ای Infrared یـشخب زا فیط یـسیطانغمورتکلا تـسا هک لوط جوم نآ رتـشیب زا رون زمرق یئرم تسا .
رد متــسیــس ياه لرتنک زا هار ،رود تاعلاطا لاتیجید اب تارییغت ینامز شبات IR لقتنم یم دنوــش . لرتنک ،نویزیولت متسیس ،هیوهت شخپ هدننک اه و يرایسب زا تازیهجت یگناخ زا نیا شور هدافتسا یم دننک .

نابم ی رظن ی
-2-7-3 هدنریگ IR

هدنریگ IR هفیظو تفایرد شبات نودام زمرق و لیدبت نآ هب لانگیس یکیرتکلا ار رب هدهع دراد .

-2-7-4 هدنتسرف IR

هدنتسرف IR هفیظو لیدبت لانگیس یکیرتکلا هب شبات نودام زمرق و لاسرا نآ ار رب هدهع دراد .

-2-7-5 لکتورپ ياه IR

تومیر ياه فلتخم زا لکتورپ ياه یفلتخم يارب لاقتنا نامرف هدافتـــسا یم دننک . زا لکتورپ ياه جیار یم ناوت هب :
NEC •
Sony •
Samsung •
Panasonic •
هراشا درک .

-2-7-6 هناخباتک 8266IRremoteESP

هناخباتک 8266IRremoteESP کی هناخباتک نتم زاب يارب لاــسرا و تفایرد لانگیــس ياه نودام زمرق يور 8266ESP و 32ESP تـسا . نیا هناخباتک زا ریگ هدن ياه IR جیار و دادعت يدایز زا لکتورپ ياه لرتنک زا هار رود ینابیتشپ یم دنک . [6]

نابم ی رظن ی
-2-8 را طابت ییویدار RF

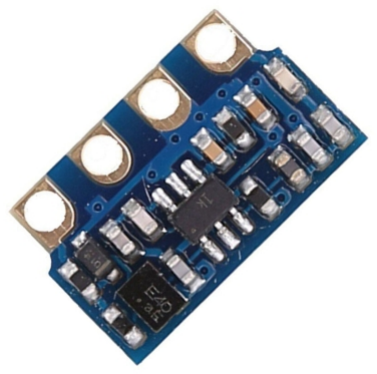
[picture p68: figure]

لکش (2-8 ) هدنریگ ییویدار

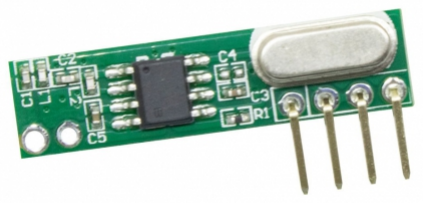
[picture p69: figure]

لکش (2-9 ) هدنتسرف ییویدار

-2-8-2 موهفم RF

RF ای Frequency Radio هب هدودحم يا زا سناکرف ياه جاوما یــسیطانغمورتکلا هتفگ یم دوــش هک يارب لاقتنا تاعلاطا هب تروص یب میس دروم هدافتسا رارق یم دنریگ . متسیس ياه ییویدار هداس یم دنناوت زا کی هدنتسرف و کی هدنریگ لیکشت دنوش . رتشیب متسیس ياه ییویدار زا دناب ياه 315 و 433 زترهاگم فتسا هدا یم دننک .

-2-8-3 هناخباتک RCSwitch

هـناـخباـتک RCSwitch يارب لرتنک يراـیـــسب زا تازیهجت ییویدار هداـــس رد دـناـب ياـه 315 و 433 زترهاـگم یحارط هدش تسا .
نیا هناخباتک ناکما تفایرد و لاــسرا دک ياه RF ار مهارف هدرک و زا پیچ اه و لکتورپ ياه جیار تازیهجت RF ینابیتشپ یم دنک . [5]

نابم ی رظن ی

### Wi-Fi طابترا -2-9

Wi-Fi یفرعم -2-9-1

Fi-Wi يروانف طابترا یب میـس ینتبم رب درادناتـسا ياه 802.11 IEEE تـسا هک ناکما لاـصتا تازیهجت هب هکبش ار مهارف یم دنک .
32ESP زا Fi-Wi اب درادناتسا ياه n/g/b802.11 ینابیتشپ یم دنک . [3]

-2-9-2 تلاح Station

رد تلاح Station ای STA، 32ESP دننام کی Client هب Point Access لصتم یم دوش . [9]

Access Point تلاح -2-9-3

رد تلاح Point Access ای AP، دوخ 32ESP کی هکبـش Fi-Wi داجیا یم دنک و ریاـس تازیهجت یم دنناوت هب نآ لصتم دنوش .[9]

AP_STA تلاح -2-9-4

رد تلاح STA_AP، 32ESP زا قیرط STA هب هکبـش یلـصا لـصتم یم دوـش و مه نامز کی Point Access داجیا یم دنک هک تیلباق لصتم ندش هب 32ESP نودب عطق ندش زا هکبش ار مهارف یم دنک . [9]

Captive Portal -2-9-5

Portal Captive یـشور تـسا هک رد نآ هاگتـسد لـصتم هدـش هب ،هکبـش لبق زا یـسرتـسد لومعم هب هکبـش اب کی هحفص تامیظنت هجاوم یم دوش .

نابم ی رظن ی

### -2-10 لکتورپ MQTT

-2-10-1 یفرعم MQTT

MQTT کی لکتورپ مایپ یناـسر کبـس رب هیاپ لدم Server/Client و Subscribe/Publish تـسا هک يارب طیحم ییاه دننام IoT و هکبــش ياه ياراد دحم تیدو عبانم یحارط هدــش تــسا . درادناتــسا 5.0 MQTT طسوت OASIS رشتنم هدش تسا . [4] یگژیو ياه مهم MQTT ترابع دنا زا :
- رابرس مک
Publish/Subscribe يرامعم•
- يزاسادج هدنتسرف و هدنریگ
- ینابیتشپ زا QoS
- بسانم يارب هاگتسد ياه ياراد تیدودحم
- طابترا رب رتسب IP/TCP

Publish/Subscribe يرامعم -2-10-2

رد MQTT هدنتـسرف و هدنریگ امیقتـسم اب رگیدکی طابترا دنرادن . رد ضوع کی Broker رد نایم نآ اه رارق دراد .
Publisℎer

!"#$%&'
C⎯⎯⎯⎯E Broker

!"#$%&'
C⎯⎯⎯⎯E Subscriber

MQTT Broker -2-10-3

Broker هـفیظو اـیرد تـف ماـیپ اـه و لاـــسرا نآ اـه هـب Client ییاـه ار دراد هـک Topic هـطوبرم ار Subscribe دندرک .

Publisher -2-10-4

Client يا هک کی مایپ رد کی Topic رشتنم یم دنک Publisher مان دراد .

نابم ی رظن ی
Subscriber -2-10-5

Client يا هک هقلاع دنم هب تفایرد مایپ ياه کی Topic ،تسا نآ Topic ار Subscribe یم دنک .

Topic/Payload -2-10-6

Topic کی ریسم یقطنم يارب هتسد يدنب مایپ ياه MQTT تسا . راتخاس یلک Topic اه هب تروص ریز تسا : < topic > / < subtopic > / < subtopic >

Payload ياوتحم مایپ MQTT تسا . درادـناـتـــسا MQTT اوتحم و بـلاـق Payload ار هـب دربراـک راذـگاو یم ؛دـنک نیارباـنب یم ناوت Payload ار هـب تروص ،نتم JSON ای هداد ياه رگید یحارط درک . [4]

QoS -2-10-7

[4] : دراد Quality of Service حطس هس MQTT :QoS 0
مایپ رثکادح کی راب لاسرا یم دوش و ینیمضت يارب لیوحت دوجو درادن . :QoS 1
مایپ لقادح کی راب لاسرا یم ،دوش نیاربانب ناکما تفایرد مایپ يرارکت دوجو دراد . :QoS 2
مایپ نیمضت یم دوش هک کی راب لیوحت یم دوش .

-2-10-8 طابترا MQTT زا قیرط WebSocket

رگرورم ياه بو هب تروـص میقتـسم يارب طابترا اب MQTT يور TCP بـسانم ؛دنتـسین نیاربانب يارب لاـصتا میقتسم رگرورم هب Broker MQTT زا WebSocket هدافتسا یم مینک . WebSocket کی طابترا ود هفرط و رادیاپ نیب Browser و Server داجیا یم دنک .

نابم ی رظن ی
-2-11 هریخذ يزاس تاعلاطا رد 32ESP

-2-11-1 هظفاح Flash

32ESP ياراد هظفاح Flash يارب يرادهگن Firmware و هداد ياه یمئاد تسا . زا نیا هظفاح یم ناوت يارب یتاعلاطا هدافتسا درک هک دیاب دعب زا restart زین یقاب دنامب .

LittleFS -2-11-2

LittleFS کی لیاف متسیس بسانم يارب هظفاح Flash متسیس ياه هتفهن تسا . رد 32ESP-Arduino، LittleFS هب ناونع یکی زا لیاف متـسیـس ياه لباق هدافتـسا رد 32ESP یفرعم هدـش تسا . [10]

# لصف 3 :

# لیلحت و یحارط متسیس

لحت یل حارط و ی سی متس

-3-1 همدقم

رد نیا ،لصف دنیارف لیلحت و یحارط هناماس دنمشوه شیاپ طیحم و لرتنک تاریهجت ینتبم رب تنرتنیا ایشا هئارا یم دوـش . فده زا یحارط نیا ،هناماـس داجیا کی باه دنمـشوه ینتبم رب رلرتنکورکیم 32ESP تـسا هک دناوتب نمـض تفایرد و شزادرپ تاعلاطا ،یطیحم ناکما لاـسرا هداد اه زا یرط ق هکبـش یب ،میـس داجیا رادـشه رد طیارــش صخــشم و نینچمه تفایرد و شخپزاب لانگیــس ياه یلرتنک نودام زمرق و سناکرف ییویدار ار مهارف دنک .
هناماـس یحارط هدـش زا هعومجم يا زا رگـسح ياه یطیحم لماـش رگـسح امد و تبوطر 11DHT، رگـسح دود و زاگ -2MQ، رگسح رون ینتبم رب LDR و رگسح خشت صی تکرح PIR لیکشت هدش تسا . هداد ياه لصاح زا نیا رگـسح اه طـسوت 32ESP تفایرد و شزادرپ هدـش و رد هزاب ياه ینامز صخـشم زا قیرط هکبـش Fi-Wi هب Broker MQTT لاسرا یم دنوش . هولاع رب تیلباق شیاپ ،طیحم هناماس ياراد متسیسریز یطابترا RF رد ود دناب یسناکرف 315 و 433 ترهاگم ز و کی متـسیـسریز طابترا نودام زمرق تـسا . نیا متـسیـسریز اه ناکما ،تفایرد هریخذ يزاـس و شخپزاب یخرب لانگیـس ياه یلرتنک تازیهجت فلتخم ار مهارف یم دننک . هب نیا ،بیترت 32ESP هب ناونع کی طـساو نایم تازیهجت ،یکیزیف هکبش و طبار يربراک لمع یم دنک .

-3-2 لیلحت يدنمزاین ياه متسیس

اب هجوت هب فادها هژورپ و تیلباق ياه ،رظندروم يدنمزاین ياه هناماس هب ود هورگ يدنمزاین ياه يدرکلمع و ریغ يدرکلمع میسقت هدش دنا .

-3-2-1 يدنمزاین ياه يدرکلمع

يدنمزاین ياه ،يدرکلمع نایب هدننک تیلباق اه و یفیاظو دنتسه هک هناماس دیاب ماجنا دهد . مهم نیرت يدنمزاین ه يا يدرکلمع متسیس یحارط هدش ترابع دنا زا :
- هناماس دیاب ناکما هزادنا يریگ يامد طیحم ار مهارف دنک .
- هناماس دیاب ناکما هزادنا يریگ تبوطر یبسن طیحم ار مهارف دنک .
- هناماس دیاب دناوتب تدش رون طیحم ار هزادنا يریگ دنک .
- هناماس دیاب دناوتب تارییغت یشان زا دوجو دود ای اگ ز رد طیحم ار ییاسانش دنک .
- هناماس دیاب تیلباق صیخشت تکرح رد طیحم ار هتشاد دشاب .
- هناماس دیاب رد تروص روبع رادقم زاگ زا هناتسآ نییعت ،هدش تیعضو رادشه ار لاعف دنک .
- هناماس دیاب رد طیارش رادشه رداق هب يزاسلاعف رزاب دشاب .
- ماس ا هن دیاب دناوتب تیعضو و تاعلاطا اهرگسح ار زا قیرط هکبش Fi-Wi لقتنم دنک .

لحت یل حارط و ی سی متس

- هناماس دیاب تیلباق يرارقرب طابترا اب کی Broker MQTT ار هتشاد دشاب .
- هناماس دیاب دناوتب تاعلاطا اهرگسح ار رد Topic ياه صخشم MQTT رشتنم دنک .
- هناماس دیاب دناوتب نامرف ياه تفایرد هدش زا قیرط MQTT ار شزادرپ و ارجا دنک .
- هناماس دیاب تیلباق تفایرد لانگیس ياه RF رد دناب 315 زترهاگم ار هتشاد دشاب .
- هناماس دیاب تیلباق تفایرد لانگیس ياه RF رد دناب 433 زترهاگم ار هتشاد دشاب .
- هناماس دیاب تیلباق تفایرد انگیس ل ياه IR ار هتشاد دشاب .
- هناماس دیاب تیلباق هریخذ يزاس لانگیس ياه RF و IR ار مهارف دنک .
- هناماس دیاب تیلباق لاسرا ددجم لانگیس ياه RF و IR هریخذ هدش ار هتشاد دشاب .
- هناماس دیاب دناوتب لانگیس ياه هریخذ هدش ار سپ زا هار يزادنا ددجم یبایزاب دنک .
- هناماــس دیاب ناکما میظنت تاعلاطا هکبــش Fi-Wi و MQTT ار نودب زاین هب رییغت و لیاپماک ددجم Firmware مهارف دنک .
- هناماس دیاب تاعلاطا اهرگسح و تیعضو رادشه ار رد کی دروبشاد تحت بو شیامن دهد .
- هناماس دیاب ناکما لاسرا نامرف ياه یلرتنک زا قیرط دروبشاد تحت بو ار هتشاد دشاب .

-3-2-2 يدنمزاین ياه ریغ يدرکلمع

يدنمزاین ياه ریغ يدرکلمع یگژیو ییاه ار صخشم یم دننک هک تیفیک هناماس ار نییعت یم دننک . مهم نیرت يدنمزاین ياه ریغ يدرکلمع متسیس ترابع دنا زا :
- تیلباق هعسوت
راتخاـس Firmware هناماـس هب تروـص رلاوژام یحارط هدش تسا ات هفاضا ندرک ،اهرگسح هجت تاری ای تیلباق ياه دیدج اب لقادح رییغت رد ریاس شخب ياه Firmware ناکما ریذپ دشاب .
- تیلباق يرادهگن
ره شخب زا ،متـسیـس زا هلمج تیریدم ،اهروـسنـس طابترا MQTT، طابترا RF، طابترا IR، تیریدم رادـشه و تیریدم هظفاح رد بلاق لوژام ياه لقتـسم هدایپ يزاـس هدـش تـسا . نیا راتخاـس م بجو هداس رت ندش دنیارف ،یسررب حلاصا و هعسوت مرن رازفا یم دوش .
- تیلباق يدنبرکیپ
تاعلاطا طوبرم هب هکبــش Fi-Wi و MQTT دیابن هب تروــص تباث و ریغ لباق رییغت رد Firmware رارق هتــشاد دنــشاب . هب نیمه ،روظنم هناماــس ياراد کی لاتروپ يدنبرکیپ تــسا هک ناکما رییغت تامیظنت کبش ه و MQTT ار مهارف یم دنک .
- يرادیاپ
عطق طابترا اب Broker MQTT دیابن بجوم فقوت درکلمع شخب ياه یلحم هناماــس دننام ندناوخ ،اهرگسح صیخشت تکرح ای درکلمع متسیس رادشه دوش . هب نیمه ،لیلد طابترا MQTT هب تروص لقتسم زا ریاس دنیارف ياه یلصا متسیس تیریدم یم دوش .
- ظفح تاعلاطا
تامیظنت هکبـش و لانگیـس ياه هریخذ هدـش RF و IR دیاب سپ زا خ شوما و نـشور ندـش هاگتـسد

لحت یل حارط و ی سی متس

زین ظفح دنوش . يارب نیا روظنم زا متسیس لیاف LittleFS دوجوم رد 32ESP هدافتسا هدش تسا .
- تیلباق یسرتسد
هناماـس دیاب ناکما یـسرتـسد ربراک هب تاعلاطا یطیحم و لاـسرا نامرف ياه یلرتنک ار زا قیرط طبار بو مهارف دنک . طابترا دروبشاد اب هناماس زا قیرط MQTT و WebSocket ماجنا یم دوش .

-3-3 يرامعم یلک متسیس

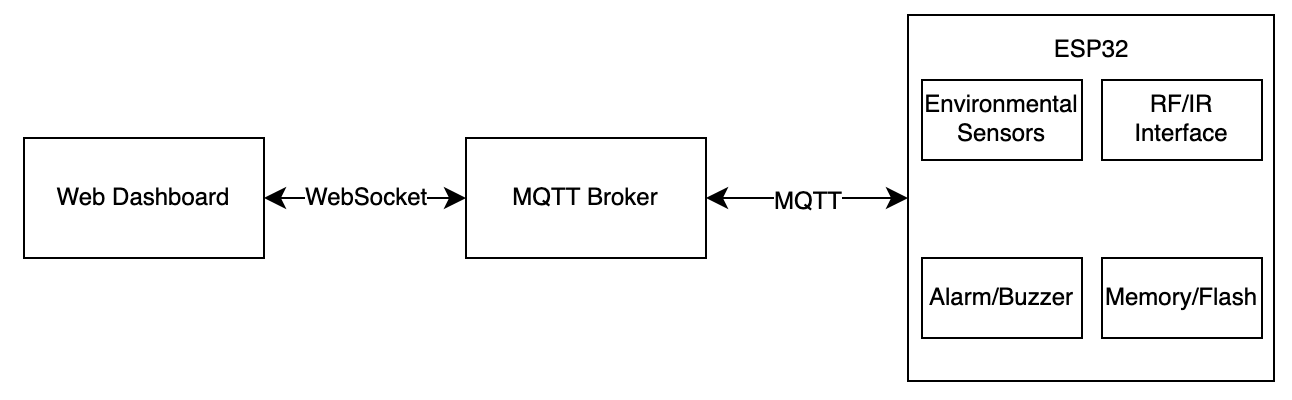
[picture p70: figure]

لکش (3-1 ) يرامعم یلک متسیس

يرامعم هناماـس هب هنوگ يا یحارط هدـش تـسا هک 32ESP هب ناونع هتـسه یـشزادرپ و ،یطابترا رد زکرم لـماـعت ناـیم ،اـهرگـــسح تازیهجت ،یلرتنک هـکبـــش و ربراـک رارق یم دریگ . رد نیا ،يراـمعم تاـعلاطا یطیحم طــسوت گــسح ر ياه لــصتم هب 32ESP تفایرد هدــش و سپ زا ،شزادرپ زا قیرط هکبــش Fi-Wi و لکتورپ MQTT هب Broker لاسرا یم دنوش . رد تمـس رگید ، ربراک یم دناوت زا قیرط دروبـشاد تحت بو هب تاعلاطا هناماس یسرتسد هتشاد و نامرف ياه یلرتنک رظندروم دوخ ار لاـــسرا دنک . نامرف اه سپ زا روبع زا Broker MQTT هب 32ESP لقتنم هدـــش و طسوت شخب تیریدم نامرف شزادرپ یم دنوش . يرامعم یلک متسیس ار یم ناوت هب هس شخب یلصا میسقت درک :
- هیلا تخس رازفا و عمج يروآ هداد
- هیلا شزادرپ و لرتنک ینتبم رب 32ESP
- هیلا یطابترا و طبار راک رب هشقن کیتامش رادم ار یم دیناوت رد شخب -8-1 هدهاشم نک دی .

-3-3-2 هیلا تخس رازفا و عمج يروآ هداد

رد هیلا تخس ،يرازفا هعومجم يا زا اهرگسح و لوژام ياه یطابترا هب درب 32ESP لصتم هدش دنا . نیا ازجا هفیظو تفایرد تاعلاطا یطیحم و طابترا اب تازیهجت یجراخ ار رب هدهع دنراد . رگسح ياه دروم هدافتسا رد نیا هیلا ترابع دنا زا :

لحت یل حارط و ی سی متس

- 11DHT يارب هزادنا يریگ امد و تبوطر
- -2MQ يارب هزادنا يریگ حطس زاگ و تبوطر
- LDR يارب هزادنا يریگ تدش رون طیحم
- PIR يارب صیخشت تکرح
نینچمه تازیهجت یطابترا لماـش هدنریگ و هدنتـسرف RF رد سناکرف ياه 315 و 433 زترهاگم و هدنریگ و هدنتسرف نودام زمرق دنتسه . 32ESP هداد ياـه یتفاـیرد زا نیا تازیهجت ار تـفاـیرد و يارب شزادرپ رد راـیتخا لوژاـم ياـه مرن فا يراز هطوبرم رارق یم دهد .

-3-3-3 هیلا شزادرپ و لرتنک

32ESP هتسه یلصا شزادرپ هناماس تسا . نیا شخب تیلوئسم تفایرد هداد ياه ُاهرگسح شزادرپ ،تاعلاطا تیریدم تیعـضو ،رادـشه لرتنک تازیهجت RF و IR، تیریدم هظفاح و يرارقرب طابترا اب Broker MQTT ار رب هدهع دراد .
مرن رازفا Firmware هب تروـص رلاوژام یحارط هدـش تـسا . رد نیا ،راتخاـس فیاظو فلتخم متـسیـس نایم لوژام ياه لقتـسم میـسقت هدـش دنا . يارب ،هنومن لوژام ياه یـصاـصتخا يارب روـسنـس ياه ,LDR -2,MQ PIR 11,DHT رد رظن هتفرگ هدــش و تیریدم MQTT ,IR ,RF و هظفاح زین رد لوژام ياه هناگادج ماجنا یم دوش .
نیا يرامعم ثعاب یم دوـش رییغت ای هعـسوت کی ،شخب یگتـسباو يرتمک هب ریاـس شخب ياه متـسیـس هتـشاد دشاب .

-3-3-4 هیلا یطابترا و طبار ربراک

طابترا نایم 32ESP و تخاـسریز مرن يرازفا هناماـس زا قیرط Fi-Wi رارقرب یم دوـش . سپ زا لاـصتا 32ESP هب ،هکبش هداد ياه هزادنا يریگ هدش طسوت لکتورپ MQTT هب Broker لاسرا یم دنوش . رد نیا هژورپ زا io.emqx.broker هب ناونع Broker MQTT هدافتسا هدش تسا . دروبـشاد تحت بو زین زا قیرط WebSocket هب Broker MQTT لـصتم یم دوـش . هب نیا ،بیترت دروبـشاد رداق تـسا هداد ياه رـشتنم هدـش طـسوت 32ESP ار تفایرد هدرک و تیعـضو یلعف متـسیـس ار هب ربراک شیامن دهد و نامرف ياه لاسرا هدش طسوت ربراک زین زا قیرط نیمه تخاسریز هب 32ESP لقتنم یم دنوش .

-3-4 یحارط تخس رازفا

رد یحارط تخـس يرازفا هناماـس زا لوژام -32WROOM32-ESP هب ناونع دحاو یـشزادرپ یلـصا هدافتـسا هدـش تـسا . باختنا نیا لوژام هب لیلد يرادروخرب زا تیلباق ياه یـشزادرپ ،بـسانم دادعت یفاک هیاپ ياه

لحت یل حارط و ی سی متس

يدورو و ،یجورخ لدبم ADC و نینچمه ینابیتشپ یلخاد زا طابترا Fi-Wi تروص هتفرگ تسا .

-3-4-1 دحاو شزادرپ يزکرم

لوژام -32WROOM32-ESP هب ناونع لرتنک هدننک یلــصا هناماــس باختنا هدــش تــسا . نیا درب هفیظو تـفاـیرد تاـعلاطا زا ،اـهرگـــسح شزادرپ هداد ،اـه تـیریدـم تازیهجت ،یطاـبترا يارجا قطنم ،رادـــشه هریخذ يزاس تاعلاطا و يرارقرب طابترا اب هکبش ار رب هدهع دراد . زا تیلباق Fi-Wi یلخاد 32ESP يارب لاـصتا هناماـس هب هکبـش حم یل و يرارقرب طابترا اب Broker MQTT هدافتـسا هدـش تـسا . نینچمه يدادعت زا هیاپ ياه GPIO يارب لاـصتا تازیهجت لاتیجید و هیاپ ياه ADC يارب تفایرد یجورخ ياه گولانآ رگسح ياه یطیحم دروم هدافتسا رارق هتفرگ تسا .

-3-4-2 متسیس هزادنا يریگ امد و تبوطر

يارب هزادنا يریگ يامد طیحم و تبوطر یبـسن زا رگـسح 11DHT هدافتـسا هدـش تـسا . نیا رگـسح زا قیرط کی طخ هداد لاتیجید اب 32ESP طابترا رارقرب یم دنک . يارـب ندـناوـخ تاـعلاـطا زا رـگـــسح زا هـناـخـباـتـک DHT Adafruit و عـباوـت ()readTemperature و ()readHumidity هدافتسا هدش تسا و هیاپ هداد 11DHT هب 15GPIO لصتم هدش تسا . تاعلاطا تفایرد هدـش زا رگـسح طـسوت Firmware شزادرپ هدـش و ریداقم امد و تبوطر هب تروـص هناگادج رد هناماس تبث و زا قیرط MQTT رشتنم یم دنوش .

-3-4-3 متسیس صیخشت دود و زاگ

يارب شیاپ دوجو دود و یخرب زاگ ياه لباق تــشا لاع زا رگــسح -2MQ هدافتــسا هدــش تــسا . رد نیا هژورپ یجورخ گولانآ رگسح دروم هدافتسا رارق هتفرگ و هب هیاپ 33GPIO زا 32ESP لصتم هدش تسا . رگـسح -2MQ يارب راک ندیـسر هب تیعـضو يراک بولطم زاین هب شیپ شیامرگ دراد هک زا قیرط 26GPIO نامرف مرگ ندـش هب رگـسح هداد یم دوـش . قبط ا تاعلاط ینف هئارا هدـش يارب هار يزادنا ،هیلوا روـسنـس دیاب رد دودح 24 تعاس مرگ دوش و سپس ناکما ندناوخ رادقم رگسح دوجو دراد . رادقم هدناوخ هدــش زا یجورخ گولانآ -2MQ طــسوت لدبم گولانآ هب لاتیجید 32ESP تفایرد یم دوــش . Firmware رادقم لــصاح ار زا قیرط MQTT هب دروبــشاد را لاــس هدرک و نینچمه اب کی هناتــسآ زا شیپ نییعت هدـش هـسیاقم یم دنک . رد تروـص روبع رادقم هزادنا يریگ هدـش زا هناتـسآ نییعت ،هدـش تیعـضو رادـشه ار لاعف هدرک و رزاب ار هب ادص رد یم دروآ و تیعضو رادشه ار زا قیرط MQTT هب دروبشاد لاسرا یم دنک .

لحت یل حارط و ی سی متس

-3-4-4 متسیس هزادنا يریگ تدش رون

ارب ي هزادنا يریگ نازیم رون طیحم زا LDR هدافتــسا هدــش تــسا . یجورخ گولانآ نیا لوژام هب 32GPIO لصتم هدش و رادقم نآ طسوت ADC هدناوخ یم دوش . رادقم لـصاح زا LDR رد هزاب ياه ینامز صخـشم طـسوت Firmware هنومن يرادرب هدـش و زا قیرط MQTT رشتنم یم دوش .

-3-4-5 متسیس صیخشت تکرح

يارب صیخـشت تکرح زا لوژام PIR هدافتـسا هدـش تـسا . یجورخ لاتیجید نیا لوژام هب 13GPIO لـصتم هدش تسا .
رد تروـص صیخـشت ،تکرح تیعـضو یجورخ PIR رییغت هدرک و Firmware نیا رییغت ار شزادرپ یم دنک و زا قیرط MQTT رــشتنم یم دنک . رد تروــص لاعف ندوب تیلباق صیخــشت ،تکرح عوقو تکرح یم دناوت بجوم لاعف ندش متسیس رادشه و لاسرا مایپ هطوبرم زا قیرط MQTT هب دروبشاد دوش .

-3-4-6 متسیس طابترا سناکرف ییویدار

یکی زا تیلباق ياه یلـصا ،هناماـس تفایرد و شخپزاب لانگیـس ياه ییویدار رد ود دناب ناکرف یـس 315 و 433 زترهاگم تسا .
هب لیلد توافت سناکرف نیا ود ،هورگ يارب ره دناب کی هدنریگ و هدنتـسرف لقتـسم رد رظن هتفرگ هدـش تـسا . نیا راتخاـس هب 32ESP نیا ناکما ار یم دهد هک لانگیـس ياه ود دناب ار هب تروـص لقتـسم تفایرد و لاـسرا دنک .
يارب دناب 315 زترهاگم زا لوژام دنریگ ه 61RXB و لوژام هدنتـسرف S34H هدافتـسا هدـش تـسا هک یجورخ اتید هدنریگ هب 22GPIO و يدورو اتید هدنتسرف هب 23GPIO لصتم هدش تسا . يارب دناب 433 زترهاگم زا لوژام هدنریگ 35RXB و لوژام هدنتـسرف S34H هدافتـسا هدـش تـسا هک یجورخ اتید هدنریگ هب 14GPIO و يدورو اتید هدنتسرف هب 27GPIO لصتم هدش تسا . رد دنیارف نتفرگ ،لانگیـس 32ESP اب ره ود هدنریگ RF طابترا رارقرب یم دنک و ،هدنریگ لانگیـس لاـسرا هدـش زا تومیر ياه RF ار تفایرد هدرک و تاعلاطا نآ طـسوت 32ESP شزادرپ یم دوـش . لانگیـس ياه تفایرد هدـش اب مان صخـشم رد هظفاح هریخذ یم دنوـش ات رد نامز يرگید دروم هدافتـسا رارق دنریگ . رد دنیارف لاـسرا لانگیـس زین 32ESP رب ساـسا دناب یـسناکرف لانگیـس دروم ،لاـسرا هدنتـسرف بـسانم ار باختنا هدرک و تاعلاطا لانگیس ار هب هدنتسرف یم دتسرف . يارب طابترا رارقرب ندرک اب لوژام اه زا هناخباتک RCSwitch هدافتسا هدش تسا .

لحت یل حارط و ی سی متس

-3-4-7 متسیس طابترا نودام زمرق

يارب طابترا نودام زمرق زا کی هدنریگ نودام زمرق و راهچ LED نودام زمرق هدافتــسا هدــش تــسا . هدنریگ نودام زمرق هب 17GPIO و LED ياه نودام زمرق هب 4GPIO لصتم هدش تسا . دنریگ ه IR، لانگیس ياه لاسرا هدش طسوت لرتنک ياه نودام زمرق ار تفایرد هدرک و تاعلاطا نآ اه طسوت 32ESP شزادرپ یم دوـش . لانگیـس ياه تفایرد هدـش اب مان صخـشم رد متـسیـس هریخذ یم دوـش ات رد نامز يرگید دروم هدافتـسا رارق دنریگ . يارب لاـسرا ،لانگیـس 32ESP تاعلاطا هریخذ دـش ه رد لانگیـس ار یبایزاب هدرک و زا قیرط LED ياه نودام ،زمرق نآ ار شخپزاب یم دنک . يارب تفایرد و لاسرا لانگیس اه زا هناخباتک 8266IRremoteESP هدافتسا هدش تسا .

-3-4-8 متسیس رادشه یتوص

يارب داجیا رادـشه یتوـص زا کی Buzzer Active هدافتـسا هدـش تـسا . يدورو نیا لوژام هب 19GPIO لـصتم هدش تسا .
رزاب رد یطیارـش دننام روبع رادقم -2MQ زا هناتـسآ نییعت هدـش ای صیخـشت تکرح رد تلاح ،لاعف یم دناوت طسوت Firmware لاعف دوش .

-3-4-9 LED تیعضو

کی LED تیعـضو يارب هئارا دروخزاب يرـصب زا تیعـضو درکلمع متـسیـس رد رظن تفرگ ه هدـش تـسا . نیا LED رد Firmware يارب شیامن تیعـضو تیلاعف هاگتـسد و نینچمه عوقو یخرب دادیور ياه طبترم اب تفایرد ای لاسرا لانگیس هدافتسا یم دوش . نیا LED هب 25GPIO لصتم هدش تسا .

### -3-5 هیاپ ياه 32ESP

لودج ریز طابترا تازیهجت یلصا اب هیاپ ياه 32ESP ار ناشن یم دهد :

لودج (3-1 ) هیاپ ياه 32ESP
| | | فیدر زیهجت هیاپ 32ESP عون يدورو / یجورخ
| | | 1 11DHT 15GPIO يدورو لاتیجید
لاتیجید یجورخ | GPIO26 | MQ-2 Heater | 2
گولانآ يدورو | GPIO33 | MQ-2 ADC | 3
گولانآ يدورو | GPIO32 | LDR ADC | 4

لحت یل حارط و ی سی متس

| | | 5 PIR 13GPIO يدورو لاتیجید
لاتیجید يدورو | GPIO22 | RF 315Mhz Receiver | 6
لاتیجید یجورخ | GPIO23 | RF 315Mhz Transmitter | 7
لاتیجید يدورو | GPIO14 | RF 433Mhz Receiver | 8
لاتیجید یجورخ | GPIO27 | RF 433Mhz Transmitter | 9
لاتیجید يدورو | GPIO17 | IR Receiver | 10
لاتیجید یجورخ | GPIO4 | IR LED | 11
| | | 12 Buzzer 19GPIO یجورخ لاتیجید
لاتیجید یجورخ | GPIO25 | Status LED | 13

-3-6 یحارط مرن رازفا و راتخاس Firmware

Firmware رب يور لوژام -32WROOM32-ESP و اب هدافتــسا زا طیحم هعــسوت PlatformIO و بوچراچ Arduino هدایپ يزاـس هدـش تـسا . اب هجوت هب ددعت فیاظو ،متـسیـس Firmware هب تروـص رلاوژام یحارط هدش تسا ات ره شخب زا هناماس تیلوئسم یصخشم هتشاد دشاب و یگتسباو نایم يازجا فلتخم شهاک دبای .

-3-6-1 راتخاس رلاوژام Firmware

لودج ریز هفیظو ره لوژام ار ناشن یم دهد :

لودج (3-2 ) هفیظو لوژام ياه Firmware
| لوژام هفیظو
| main هار يزادنا و لرتنک نایرج یلصا همانرب
تیریدم هرود يا اهرگسح و دادیور ياه حم ی یط | Sensors
| DHT تفایرد امد و تبوطر
| 2MQ تفایرد رادقم زاگ و دود
| LDR تفایرد رادقم رون
| PIR صیخشت تکرح
| MQTT يرارقرب طابترا اب Broker و لاسرا و تفایرد مایپ
| RF تفایرد و لاسرا لانگیس ياه RF
| IR تفایرد و لاسرا لانگیس ياه نودام زمرق
| Alarm تیریدم تیعضو رادشه و رزاب
| LED تیریدم LED تیعضو
MQTT و Wi-Fi يدنبرکیپ | Provisioning

لحت یل حارط و ی سی متس

| Memory هریخذ و یبایزاب تاعلاطا رد LittleFS
شزادرپ نامرف ياه ینتم | Serial پاچ و تفایرد و
| Config يرادهگن تامیظنت و رتماراپ ياه تباث

-3-6-2 دنیارف هار يزادنا متسیس

سپ زا نـشور ندـش 32ESP، عبات ()setup ارجا یم دوـش . نیا عبات هفیظو هدامآ يزاـس هیلوا يازجا متـسیـس ار رب هدهع دراد .
دنور هار يزادنا متسیس هب تروص ریز تسا :

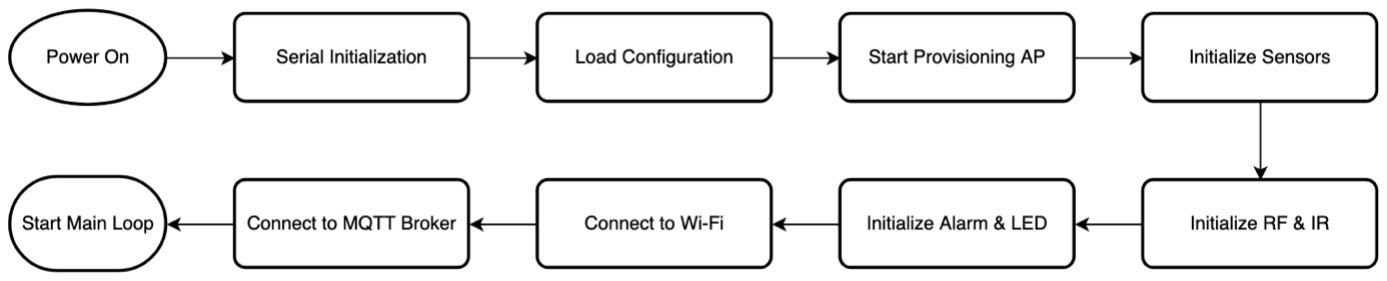
[picture p71: figure]

لکش (3-2 ) دنور هار يزادنا متسیس

رد ادتبا طابترا لایرـس اب رتویپماک رارقرب یم دوـش و سپـس تامیظنت و رتماراپ اه هدناوخ یم دوـش و سپـس رگا زاین دـشاب لاتروپ رب يا نتفرگ تاعلاطا AP و Broker MQTT زاب یم دوـش . سپ زا لیمکت ندـش ،تاعلاطا رگــسح اه و لوژام ياه یطابترا هار يزادنا یم دوــش و سپــس هب هکبــش Fi-Wi لــصتم هدــش و سپــس هب Broker MQTT لصتم یم دوش .

-3-6-3 هقلح یلصا يارجا همانرب

سپ زا نایاپ تایلمع هار ،يزادنا همانرب دراو عبات ()loop یم دوــش . نیا عبات هب تروــص موادم ارجا هدــش و فیاظو یلصا هناماس ار تیریدم یم دنک . رد ره راب ،ارجا لایرــس لانیمرت و MQTT يارب روتــسد ياه دیدج هدناوخ یم دوــش و سپــس رگــسح اه تیریدم یم دنوش .
دنور هقلح یلصا متسیس هب تروص ریز تسا :

لکش (3-3 ) دنور هقلح یلصا متسیس

لحت یل حارط و ی سی متس

-3-6-4 تیریدم اهرگسح

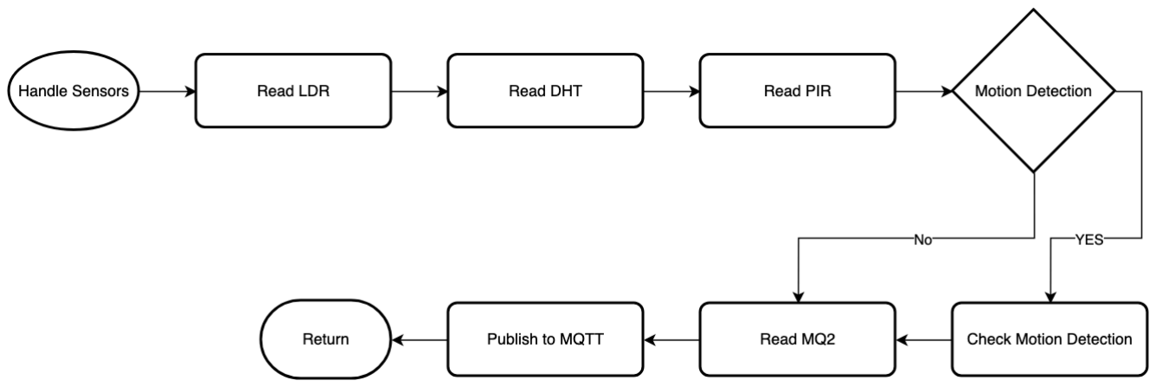
[picture p72: figure]

لکش (3-4 ) دنور تیریدم رگسح اه

تیریدم اهرگــسح رد لوژام Sensors ماجنا یم دوــش . نیا لوژام هفیظو یگنهامه نایم رویارد ياه فلتخم اهرگسح ار رب هدهع دراد .
تاعلاطا رگـسح ياه PIR، LDR، 11DHT و -2MQ رد لـصاوف ینامز صخـشم تفایرد یم دنوـش . سپ زا تفایرد هداد ،اه ریداقم تفایرد هدش رد Topic ياه هطوبرم طسوت MQTT رشتنم یم دنوش . رد هخسن ،یلعف هزاب ینامز يارب تفایرد تاعلاطا اهرگسح ربارب اب 10 هیناث تسا .

-3-6-5 تیریدم رگسح -2MQ

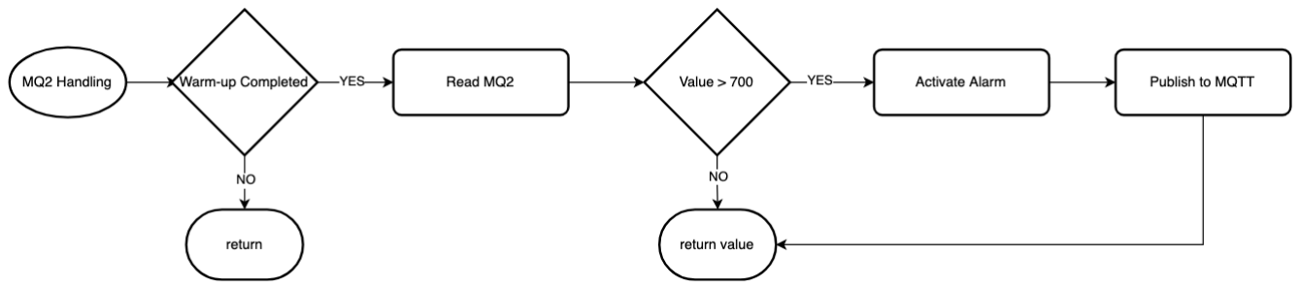
[picture p73: figure]

لکش (3-5 ) دنور تیریدم رگسح -2MQ

اب هجوت هب تیهام رگـسح -2MQ، نیا رگـسح هلـصافلاب سپ زا نـشور ندـش ،متـسیـس يارب هدافتـسا رد رظن هتفرگ یمن دوش . Firmware کی هرود مرگ ندش هیلوا يارب رگسح رد رظن هتفرگ تسا . سپ زا نایاپ نیا ،هرود رادقم یجورخ رگـسح رد هزاب ياه صخـشم ینامز طـسوت لوژام Sensors هدناوخ یم دوـش و اب رادقم هناتـسآ نییعت ـش هد هـسیاقم یم دوـش . رد تروـص روبع رادقم هدناوخ هدـش زا ،هناتـسآ ،متـسیـس تیعضو رادشه ار لاعف هدرک و مایپ هطوبرم ار زا قیرط MQTT رد Topic صخشم هدش رشتنم یم دنک . رد هخـسن ،یلعف مرگ ندـش هیلوا هب لیلد دوبمک ،نامز 5 هقیقد رد رظن هتفرگ هدـش تـسا و نینچمه هناتـسآ ربارب اب 700 رد رظن هتفرگ هدش تسا .

لحت یل حارط و ی سی متس

-3-6-6 تیریدم رگسح 11DHT

امد و تبوطر طیحم طـسوت رگـسح 11DHT هزادنا يریگ یم دوـش . رادقم یجورخ رگـسح رد هزاب ياه ینامز صخشم طسوت لوژام Sensors هدناوخ یم دوش . يارب هدافتـسا زا نیا ،رگـسح زا هناخباتک DHT Adafruit هدافتـسا هدـش تـسا . رد Firmware يارب هزادنا يریگ امد زا عبات readTemperature و يارب هزادنا يریگ تبوطر زا عبات readHumidity هدافتسا هدش تسا .

-3-6-7 تیریدم رگسح PIR

صیخـشت تکرح طـسوت رگـسح PIR ماجنا یم دوـش . تیعـضو یجورخ نیا رگـسح طـسوت 32ESP یـسررب یم دوش .
،متـسیـس هولاع رب تفایرد تیعـضو PIR، اکما ن لاعف ای لاعفریغ ندرک تیلباق صیخـشت تکرح ار زین مهارف یم دنک . يارب نیا روظنم زا نامرف ياه ریز هدافتسا هدش تسا : motion on
motion off
رد تروـص لاعف ندوب تیلباق صیخـشت تکرح و ییاـسانـش ،تکرح متـسیـس تیعـضو رادـشه ار لاعف هدرک و مایپ هطوبرم ار رد Topic صخشم هدش رشتنم یم دنک .

-3-6-8 تیریدم متسیس رادشه

لوژام Alarm هفیظو تیریدم تیعضو رادشه و لرتنک Buzzer ار رب هدهع دراد . ود دادیور یلصا یم دنناوت ثعاب داجیا تیعضو رادشه دنوش :
- روبع رادقم -2MQ زا هناتسآ نییعت هدش
- صیخشت تکرح رد یتلاح هک صیخشت تکرح لاعف دشاب نینچمه ناکما لرتنک میقتسم رزاب زا قیرط نامرف ياه متسیس دوجو دراد : buzzer on
buzzer off
رد ماگنه عوقو ،رادشه رزاب قباطم قطنم ینامز فیرعت ،هدش لاعف و لاعفریغ یم دوش . رد هخسن ،یلعف هخرچ ینامز ربارب اب 2 هیناث رد رظن هتفرگ هدش تسا .

لحت یل حارط و ی سی متس

### -3-7 یحارط طابترا Fi-Wi و MQTT

Wi-Fi طابترا -3-7-1

طابترا هکبـش يا هناماـس زا قیرط Fi-Wi یلخاد 32ESP رارقرب یم دوـش . Fi-Wi هفیظو لاـصتا هاگتـسد هب هکبش و مهارف ندرک ریسم یطابترا نایم 32ESP و Broker MQTT ار رب هدهع دراد . متسیس زا تلاح STA_AP_WIFI هدافتسا یم دنک . رد نیا ،تلاح 32ESP یم دناوت هب تروص نامزمه :
- هب هکبش Fi-Wi رظندروم هب ناونع Station لصتم دوش
- کی Point Access یصاصتخا يارب يدنبرکیپ داجیا دنک نیا شور ناکما يدنبرکیپ ددجم هاگتسد ار نودب زاین هب رییغت Firmware مهارف یم دنک .

-3-7-2 طابترا MQTT

يارب لدابت هداد نایم 32ESP و Broker و بشاد درو زا لکتورپ MQTT هدافتسا هدش تسا . طابترا MQTT زا لدم Subscriber/Publisher هدافتـسا یم دنک . رد نیا ،لدم 32ESP تاعلاطا رگـسح اه ار رد Topic ياه صخـشم رـشتنم یم دنک و رد نیع لاح یم دناوت مایپ ياه یلرتنک رـشتنم هدـش طـسوت دروبشاد ار تفایرد دنک .
رد نیا هژورپ Broker MQTT دروم هدافتسا io.emqx.broker تسا .

-3-7-2-1 راتخاس Topic ياه MQTT راتخاس Topic اه هب تروص ریز یحارط هدش تسا : < base > / < device > / < subtopic > رد نیا ،هژورپ رادقم هیاپ ربارب homeintelligence رارق هداد هدـش تـسا و مان هاگتـسد طـسوت ربراک نییعت یم دوش .

-3-7-2-2 Topic ياه طوبرم هب اهرگسح هداد ياه اهرگسح رد Topic ياه ازجم رشتنم یم دوش .

لودج (3-3 ) Topic ياه طوبرم هب اهرگسح
| Topic هداد
امد | ... /sensor/TEMP
تبوطر | ... /sensor/HUM
| LDR/sensor/ …تدش رون
| PIR/sensor/ …صیخشت تکرح

لحت یل حارط و ی سی متس

2MQ/sensor/ …دود و زاگ

-3-7-2-3 Topic رادشه
يارب علاطا یناسر دادیور ياه رادشه زا alarm/ …:Topic هدافتسا یم دوش . مایپ ياه لباق راشتنا رد نیا Topic لماش دراوم ریز تسا : MQ2 threshold exceed •
Motion Detected •
Motion ON •
Motion OFF •

-3-7-2-4 Topic نامرف
نامرف ياه یلرتنک زا قیرط command/ …:Topic تفایرد یم دوش . Firmware مایپ ياه تفایرد هدـش زا نیا Topic ار هب Handler Command لاـسرا هدرک و تایلمع رظانتم اب ،نامرف ارجا یم دوش .

-3-7-2-5 Topic تسرهف لانگیس ياه RF و IR يارب لاـــسرا تـــسرهف لاـنگیـــس ياـه RF و IR هـب دروبـــشاد زا Topic ياـه list/RF/…:Topic و list/IR/…:Topic هدافتسا یم دوش . مایپ ياه هداتسرف هدش رد نیا Topic رد بلاق JSON دنتسه .

-3-8 یحارط متسیس RF

یکی زا تیلباق ياه یلصا ،هژورپ ناکما تفایرد و شخپزاب لانگیس ياه RF رد ود دناب یسناکرف 315 و 433 زترهاگم تسا .
زا آ اجن هک هدنریگ و هدنتـسرف ياه RF دروم هدافتـسا کت سناکرف ،دنتـسه يارب ره دناب کی ریـسم تفایرد و لاسرا لقتسم رد رظن هتفرگ هدش تسا . يارب تیریدم لانگیس ياه RF زا هناخباتک RCSwitch هدافتسا هدش تسا .

-3-8-1 تفایرد لانگیس RF

نامرف ریز يارب عورش دنیارف تفایرد هدافتسا یم دوش : rf rx <name>
سپ زا يارجا ،نامرف متـسیـس ره ود هدنریگ RF ار یـسررب یم دنک . یماگنه هک کی لانگیـس تفایرد ،دوـش تاعلاطا طوبرم هب نآ جارختسا هدش و دناب یسناکرف دروم هدافتسا زین صخشم یم دوش .

لحت یل حارط و ی سی متس

-3-8-2 هریخذ لانگیس RF

سپ زا تفایرد ،لانگیس تاعلاطا نآ رد هظفاح یمئاد متسیس هب تروص JSON هریخذ یم دوش . لیاف طوبرم هب نیا تاعلاطا json.signals_rf/ تسا .

-3-8-3 شخپزاب لانگیس RF

يارب لاسرا ددجم کی لانگیس هریخذ هدش زا نامرف ریز هدافتسا یم دوش : rf tx <name>
Firmware دناب یـسناکرف هریخذ هدـش ار یـسررب هدرک و لانگیـس ار زا قیرط هدنتـسرف بـسانم لاـسرا یم دنک . نیاربانب ربراک ماگنه لاــسرا ددجم يزاین هب نییعت سناکرف درادن و متــسیــس هب تروــص راکدوخ هدنتــسرف بسانم ار باختنا یم دنک .

-3-8-4 تیریدم لانگیس ياه هریخذ هدش ًRF

نامرف ياه ریز يارب تیریدم لانگیس ياه RF هریخذ هدش رد رظن هتفرگ هدش تسا : rf list
rf del <name>
نامرف list، تسرهف لانگیس ياه هریخذ هدش ار شیامن هداد و تاعلاطا نآ اه ار زا قیرط MQTT زین رشتنم یم دنک .
نامرف del يارب فذح کی لانگیس صخشم زا هظفاح هدافتسا یم دوش .

-3-9 یحارط متسیس نودام زمرق

متسیس نودام زمرق زا ود شخب یلصا هدنریگ و هدنتسرف لیکشت هدش تسا . يارب تیریدم انگیس ل ياه نودام زمرق زا هناخباتک 8266IRremoteESP هدافتسا هدش تسا .

-3-9-1 تفایرد لانگیس IR

يارب عورش تفایرد کی لانگیس IR زا نامرف ریز هدافتسا یم دوش : ir rx <name>
سپ زا يارجا ،نامرف متسیس رظتنم تفایرد کی لانگیس نودام زمرق یم دنام . رد نامز تفایرد کی ،لانگیس متسیس تاعلاطا طوبرم نآ ار جارختسا یم دنک .

لحت یل حارط و ی سی متس

متــسیــس رداق هب شزادرپ یخرب لکتورپ ياه جیار دننام SONY، NEC، SAMSUNG و PANASOINC هدوب و رد تروص هتخانشان ندوب ،لکتورپ ناکما هریخذ تاعلاطا ماخ لانگیس زین دوجو دراد .

-3-9-2 هریخذ لانگیس IR

لانگیس ياه تفایرد هدش رد هظفاح یمئاد متسیس هب تروص JSON هریخذ یم دوش . لیاف طوبرم هب نیا تاعلاطا json.signals_ir/ تسا .

-3-9-3 شخپزاب لانگیس IR

يارب شخپزاب لانگیس هریخذ هدش زا نامرف ریز هدافتسا یم دوش : ir tx <name>
رد نیا ،دنیارف Firmware تاعلاطا لانگیـس ار یبایزاب هدرک و نآ ار طسوت LED نودام زمرق لاسرا یم دنک . رد یتروـص هک لکتورپ لانگیـس ینابیتـشپ ،دوـش هداد طـسوت لکتورپ هداتـسرف یم دوـش رد ریغ تروـصنیا هداد ماخ هریخذ هدش هب تروص لانگیس هداتسرف یم دوش .

-3-9-4 تیریدم لانگیس ياه هریخذ هدش IR

نامرف ياه ریز يارب تیریدم لانگیس ياه IR ذ هریخ هدش رد رظن هتفرگ هدش تسا : ir list
ir del <name>
نامرف list، تسرهف لانگیس ياه هریخذ هدش ار شیامن هداد و تاعلاطا نآ اه ار زا قیرط MQTT زین رشتنم یم دنک .
نامرف del يارب فذح کی لانگیس صخشم زا هظفاح هدافتسا یم دوش .

-3-10 یحارط متسیس هریخذ يزاس

يارب هریخذ يزاـس تاعلاطا یمئاد زا لیاف متـسیـس LittleFS هدافتـسا هدـش تـسا . هدافتـسا زا متـسیـس لیاف یلخاد 32ESP ناکما يرادهگن تاعلاطا نودب زاین هب هظفاح یجراخ ار مهارف یم دنک . رد هژورپ هس لیاف یلصا داجیا یم دنوش :

لودج (3-4 ) لیاف ياه تاعلاطا یمئاد متسیس
لیاف اوتحم

لحت یل حارط و ی سی متس

MQTT و Wi-Fi تامیظنت | /provisioning.json
| json.signals_rf/ لانگیس ياه هریخذ هدش RF
| json.signals_ir/ لانگیس ياه خذ هری هدش IR
| json.settings/ تامیظنت هاگتسد

تاعلاطا نیا لیاف اه سپ زا هار يزادنا ددجم هاگتسد لباق یبایزاب دنتسه .

-3-10-2 هریخذ تامیظنت Provisioning

تاعلاطا طوبرم هب هکبش و MQTT هب تروص JSON رد لیاف json.provisioning هریخذ یم دنوش . نیا تاعلاطا لماش دراوم ریز تسا : Wi-Fi هکبش SSID •
- زمر روبع Fi-Wi
MQTT Broker سردآ•
- تروپ MQTT
- مان يربراک و زمر روبع MQTT رد تروص هدافتسا
- مان یصاصتخا هاگتسد

-3-10-3 هریخذ تامیظنت هاگتسد

تاعلاطا طوبرم هب تامیظنت هاگتـسد هک اب شوماخ ندـش هاگتـسد دیاب هریخذ ،دنوـش هب تروـص JSON رد لیاف json.settings یخذ هر یم دنوش . نیا تاعلاطا لماش دراوم ریز تسا :
- تیعضو لاعف ندوب صیخشت تکرح

-3-10-4 راتخاس هریخذ لانگیس RF

تاعلاطا لانگیس ياه RF هب تروص JSON رد لیاف json.signals_rf هریخذ یم دنوش . تاعلاطا طوبرم هب ره لانگیس لماش دراوم ریز تسا :
- مان لانگیس
- دک لانگیس
- دادعت تیب
- لکتورپ

لحت یل حارط و ی سی متس

- لوط سلاپ
- دناب یسناکرف

-3-10-5 راتخاس هریخذ لانگیس IR

تاعلاطا لانگیس ياه IR هب تروص JSON رد لیاف json.signals_ir هریخذ یم دنوش . تاعلاطا طوبرم هب ره لانگیس لماش دراوم ریز تسا :
- مان لانگیس
- لکتورپ
- دک لانگیس
- دادعت تیب
- تاعلاطا هداد ماخ رد تروص زاین

### -3-11 یحارط متسیس Provisioning

یکی زا تیلباق ياه مرن يرازفا ،هناماس ناکما يدنبرکیپ Fi-Wi و MQTT نودب رییغت Firmware تسا . يارب نیا روظنم 32ESP رد تلاح STA_AP_WIFI لاعف یم دوــش . رد نیا ،تلاح هاگتــسد هولاع رب شلات يارب لاصتا هب هکبش Fi-Wi، کی Point Access یصاصتخا زین داجیا یم دنک . تاصخشم لاصتا هب AP رد لودج ریز هدمآ تسا .

لودج (3-5 ) تاصخشم AP
| هصخشم رادقم
Intelligence_Setup | SSID
12345678 | Password
192.168.4.1 | IP

Captive Portal -3-11-2

سپ زا لاــصتا ربراک هب Point Access، کی Poral Captive رد رایتخا يو رارق یم دریگ . نیا هحفــص ناکما دراو ندرک تاعلاطا دروم زاین يارب لاصتا هاگتسد هب هکبش و Broker MQTT ار مهارف یم دنک . سپ زا هریخذ ،تامیظنت تاعلاطا رد LittleFS هریخذ هدش و هاگتسد Restart یم دوش .

لحت یل حارط و ی سی متس

-3-11-3 لاصتا نامزمه AP و Station

رد یحارط ،متـسیـس Point Access طوبرم هب Provisioning اهنت رد نامز هار يزادنا هیلوا ،تـسین هکلب رد تلاح يداع زین لاعف یقاب یم دنام .

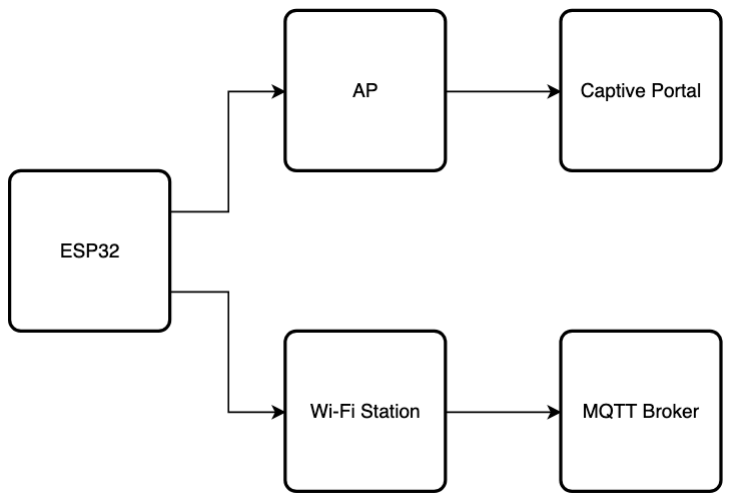
[picture p74: figure]

لکش (3-6 ) رادومن لاصتا هب هکبش

نیا یگژیو ناکما رییغت تامیظنت هکبـش ای MQTT ار رد ینامز هک 32ESP هب هکبـش لـصتم ،تـسا مهارف یم دنک .

### Web Dashboard یحارط -3-12

دروبشاد هب تروص less-Server یحارط هدش و امیقتسم زا قیرط WebSocket هب MQTT لصتم یم دوش . زا اـجنآ هـک رگرورم هـب تروـــص میقتـــسم زا MQTT يور TCP یناـبیتـــشپ یمن ،دـنک Broker دـیاـب تـیلباـق WebSocket ار لاعف هدرک دشاب .

-3-12-1 شیامن تاعلاطا اهرگسح

دروبشاد تاعلاطا تفایرد هدش زا Topic ياه طوبرم هب اهرگسح ار تفایرد هدرک و هب ربراک شیامن یم دهد . هداد اه هب تروـص هدنز زا Broker MQTT تفایرد یم دنوـش و زاین هب Refresh ندرک هحفـص يارب هدهاـشم تارییغت دوجو درادن .

لحت یل حارط و ی سی متس

-3-12-2 شیامن تیعضو رادشه

رد تروص تفایرد مایپ رادشه زا Topic ،هطوبرم دروبشاد تیعضو رادشه ار هب ربراک شیامن یم دهد .

-3-12-3 لاسرا نامرف زا قیرط دروبشاد

دروبشاد هولاع رب شیامن ،تاعلاطا ناکما لاسرا نامرف هب 32ESP ار زین مهارف یم دنک . نیا نامرف اه یم دنناوت لماش دراوم ریز دنشاب : buzzer on •
buzzer off •
motion on •
motion off •
rf rx <name> •
rf tx <name> •
rf del <name> •
rf list •
ir rx <name> •
ir tx <name> •
ir del <name> •
ir list •

-3-13 یحارط تیریدم اطخ و تاطابترا

اب هجوت هب یگتـسباو شخب یطابترا متـسیـس هب ،هکبـش لامتحا عطق Fi-Wi ای رد سرتـسد ندوبن MQTT Broker دوجو دراد . هب نیمه ،لیلد Firmware دنیارف لاـصتا هکبـش و لاـصتا MQTT ار هب تروـص لقتـسم تیریدم یم دنک .
رد تروـــص عطق طابترا اب Broker MQTT، متـــسیـــس شلات یم دنک طابترا ار اددجم رارقرب دنک . رد نیا ،طیارـش دنیارف ياه یلحم هاگتسد فقوتم یمن دوش و تیلباق ییاه دننام ندناوخ ،اهرگسح تیریدم رادشه و درکلمع شخب IR/RF نانچمه طسوت Firmware ارجا یم دنوش .

-3-14 هناخباتک ياه مرن يرازفا دروم هدافتسا

يارب هدایپ يزاس Firmware زا دنچ هناخباتک هدافتسا هدش تسا هک رد لودج ریز رکذ هدش تسا .

لحت یل حارط و ی سی متس

لودج (3-6 ) هناخباتک ياه دروم هدافتسا
| هناخباتک دربراک
DHT11 رگسح اب طابترا | DHT sensor library
| sensor Unified Adafruit هیلا كرتشم دروم هدافتسا هناخباتک ياه رگسح Adafruit
| RCSwitch تفایرد و لاسرا لانگیس ياه RF
| 8266IRremoteESP تفایرد و لاسرا لانگیس ياه IR
| ArduinoJSON شزادرپ و هریخذ هداد ياه JSON
| PubSubClient هدایپ يزاس طابترا MQTT

# لصف 4 :

# هدایپ يزاس هناماس

پی هدا زاس ی ھناماس

-4-1 همدقم

رد نیا ،لـصف دنیارف هدایپ يزاـس هناماـس حیرـشت یم دوـش . سپ زا یـسررب ینابم يرظن و یحارط هناماـس رد لـصف ياه ،نیـشیپ رد نیا لـصف هوحن لیدبت یحارط هئارا هدـش هب کی هناماـس یتایلمع دروم یـسررب رارق یم دریگ .
هدایپ يزاس ماجنا هدش لماش ود شخب یلصا Firmware هاگتسد و طبار يربراک تحت بو تسا . Firmware رب يور درب 32ESP و اب هدافتـــسا زا بوچراچ Arduino هعـــسوت هداد هدـــش و هفیظو تیریدم ،اهرگـسح شزادرپ هداد ياه ،یتفایرد لرتنک متـسیـس ،رادـشه تفایرد و لاـسرا لانگیـس ياه RF و IR، تیریدم طابترا Fi-Wi و MQTT و نینچمه هریخذ يزاس تاعلاطا ار رب هدهع دراد . رد شخب تخـس ،يرازفا 32ESP هب هعومجم يا زا اهرگـسح و تازیهجت یبناج لماـش رگـسح امد و تبوطر 11DHT، رگــسح زاگ و دود -2MQ، رگــسح رون ینتبم رب LDR، رگــسح صیخــشت تکرح PIR، هدنریگ و هدنتـسرف RF رد دناب ياه 315 و 433 ،زترهاگم هدنریگ و هدنتـسرف نودام زمرق و رزاب لـصتم هدـش تـسا . تاعلاطا تفایرد هدـش زا رگـسح اه طـسوت 32ESP شزادرپ هدـش و رد لـصاوف ینامز صخـشم هداتـسرف یم دوش .
رد شخب یطابترا هاگتـسد اب هدافتـسا زا Fi-Wi هب هکبـش لـصتم هدـش و يارب لدابت هداد و تفایرد نامرف ياه یلرتنک زا لکتورپ MQTT هدافتــسا یم دنک . Broker MQTT دروم هدافتــسا رد هدایپ يزاــس ییاهن ،هژورپ رـس سیو یمومع io.emqx.broker تـسا . نینچمه يارب يدنبرکیپ هیلوا و رییغت تامیظنت ،هکبـش هناماـسریز ینتبم رب Point Access و Portal Captive رد Firmware هدایپ يزاس هدش تسا . یکی رگید زا تیلباق ياه یلـصا ،هناماـس ناکما ،تفایرد هریخذ و شخپزاب لانگیـس ياه RF و IR تـسا . نیا باق تیل هاگتـسد ار زا کی هناماـس افرـص یتراظن هب کی طـساو یطابترا نایم تازیهجت یکینورتکلا و تخاـسریز دنمشوه لیدبت یم دنک .
،تیاهنرد کی Dashboard Web يارب هدهاـشم هداد ياه ،اهرگـسح تفایرد رادـشه اه و لاـسرا نامرف ياه یلرتنک یحارط هدش تسا . نیا دروبشاد امیقتسم اب Broker MQTT طابترا رارقرب هدرک و ناکما لماعت ربراک اب هاگتسد ار نودب زاین هب کی Backend یصاصتخا مهارف یم دنک .

-4-2 طیحم و رازبا ياه هعسوت

تامیظنت طوبرم هب طیحم هعسوت و یگتسباو ياه هژورپ رد لیاف ini.platformio فیرعت هدش تسا . نیا لیاف هب ناونع لیاف يدنبرکیپ یلـصا طیحم تخاـس ،هژورپ تاـصخـشم ،درب Framework، تعرـس طابترا ،لایرـس متسیس لیاف و هناخباتک ياه دروم هدافتسا ار نییعت یم دنک .

پی هدا زاس ی ھناماس

-4-2-1 تامیظنت درب و Framework

رد نیا هژورپ طیحم هعـسوت يارب درب 32ESP زا مرفتلپ 32espressif هدافتـسا یم دنک . Framework باختنا هدش زین Arduino تسا .
رتماراپ platform صخشم هدننک مرفتلپ هعسوت طوبرم هب هداوناخ 32ESP تسا . رتماراپ board زین يدنبرکیپ تخـس يرازفا طوبرم هب درب دروم هدافتـسا ار صخـشم یم دنک . رد نیا هژورپ زا تامیظنت یمومع dev32esp هدافتسا هدش تسا .

-4-2-2 تامیظنت طابترا لایرس

يارب هدهاــشم مایپ ياه یجورخ Firmware و یــسررب تیعــضو درکلمع ،هاگتــسد تعرــس طابترا Serial Monitor ربارب اب bauds 115200 نییعت هدش تسا . نیا طابترا رد دنیارف هعــسوت و شیامزآ هناماــس دربراک دراد و ناکما هدهاــشم مایپ ياه طوبرم هب هار يزادنا ،هاگتـسد تیعـضو لاـصتا ،هکبـش تاعلاطا اهرگـسح و تفایرد و لاـسرا نامرف اه رد Firmware ار مهارف یم دنک .

-4-2-3 متسیس لیاف LittleFS

رد هژورپ زا متـسیـس لیاف LittleFS يارب هریخذ يزاـس تاعلاطا يور هظفاح یلخاد 32ESP هدافتـسا هدـش تـسا . هدافتـسا زا LittleFS ناکما هریخذ یتاعلاطا ار مهارف یم دنک هک دیاب سپ زا شوماخ و نـشور ندـش هاـگتـــسد زین یقاـب دـنناـمب . رد هژورپ رـــضاـح زا نیا تـیلباـق يارب يرادـهگن تاـعلاطا طوبرم هـب تاـمیظنت Provisioning و نینچمه لانگیس ياه هریخذ هدش RF و IR هدافتسا هدش تسا .

-4-2-4 دنیارف تخاس و يراذگراب Firmware

لکش (4-1 ) دنور تخاس و يراذگراب Firmware

سپ زا هدامآ يزاـس طیحم هعـسوت و بـصن یگتـسباو ياه فیرعت ،هدـش Firmware هژورپ طـسوت PlatformIO هتخاس هدش و سپس رب يور درب 32ESP يراذگراب یم دوش .

پی هدا زاس ی ھناماس

-4-3 هدایپ يزاس تخس رازفا

-4-3-1 یفرعم راتخاس تخس يرازفا

رد یحارط هدایپ يزاـس ،هدـش يارب ره کی زا يازجا تخـس يرازفا هیاپ یـصخـشم زا GPIO ياه 32ESP صاـصتخا هداد هدـش تـسا . تـشاگن هیاپ اه رد لیاف يدنبرکیپ h.config زکرمتم هدـش ات رییغت تلااـصتا تخـس يرازفا نودب زاین هب تسج و وج رد ریاس شخب ياه Firmware ناکما ریذپ دشاب . دج ( لو 1-3 ) تشاگن هیاپ ياه دروم هدافتسا ار ناشن یم دهد .

-4-3-2 هدایپ يزاس رگسح امد و تبوطر 11DHT

يارب هزادنا يریگ امد و تبوطر طیحم زا رگــسح 11DHT و هناخباتک Sensors Adafruuit هدافتــسا هدــش تسا .
يارب هار يزادنا ،رگسح عبات ()setupDHT فیرعت هدش تسا :

void setupDHT()
{
dht.begin();
}
نیا عبات رد دنیارف هار يزادنا Firmware یناوخارف هدــش و طابترا مرن رازفا اب رگــسح 11DHT ار هدامآ یم دنک .
يارب تفایرد تبوطر ،طیحم عبات readHumidity یناوخارف یم دوش :

float readHumidity()
{
float input = dht.readHumidity();
if (isnan(input))
{
Serial.println("Failed to read humidity from DHT sensor"); }
return input;
}
هب نیمه لکش يارب تفایرد يامد ،طیحم عبات readTemperature یناوخارف یم دوش :

float readTemperature()
{
float input = dht.readTemperature();
if (isnan(input))
{
Serial.println("Failed to read temperature from DHT sensor"); }
return input;
}
رد نیا هدایپ ،يزاس رادقم رگسح یسررب یم دوش و سپس هجیتن هدنادرگرب یم دوش .

پی هدا زاس ی ھناماس

-4-3-3 هدایپ يزاس رگسح رون LDR

يارب هزادنا يریگ نازیم رون طیحم زا لوژام LDR هدافتسا هدش تسا . رادقم یجورخ اب هدافتسا زا عبات analogRead تفایرد یم دوش :

int readLDR()
{
int input = analogRead(LDR_PIN);
return input;
}
رد ،هـجیتن 32ESP رد ناـمز هـنومن يرادرب رادـقم ADC طوبرم هـب یجورخ LDR ار تـفاـیرد هدرک و نیا رادـقم هب ناونع هداد طوبرم هب تدش رون رد متسیس دروم هدافتسا رارق یم دریگ .

-4-3-4 هدایپ يزاس رگسح -2MQ

يارب صیخشت دود و زاگ ياه لباق لاعتشا زا رگسح -2MQ هدافتسا هدش تسا . رادقم یجورخ گولانآ اب ا هدافتس زا -2MQ تفایرد یم دوش :

int readMQ2()
{
return analogRead(MQ2_PIN); }

bool checkThreshold(int value) {
if (value > MQ2_THRESHOLD) {
return true;
}
return false;
}
رد نیا هلحرم رادقم ماخ ADC تفایرد یم دوـش و رد هلحرم دعب روبع زا هناتـسآ صیخـشت هداد یم دوـش . قطنم لاعف ندرک تیعضو رادشه رد شخب تیریدم روسنس اه هدایپ يزاس هدش تسا .

-4-3-5 هدایپ يزاس رگسح صیخشت تکرح PIR

يارب صیخشت تکرح زا رگسح PIR هدافتسا هدش تسا .

void setupPIR()
{
pinMode(PIR_PIN, INPUT);

motionDetectionEnabled = loadMotionDetection(); if (motionDetectionEnabled)

پی هدا زاس ی ھناماس

{
Serial.println("Motion detection restored to ON"); }
}
رد ماگنه هار ،يزادنا هیاپ طوبرم هب ناونع يدورو نت ظ می یم دوـش و تاعلاطا تیعـضو لاعف ندوب صیخـشت تکرح یبایزاب یم دوش .

int readPIR()
{
int input = digitalRead(PIR_PIN); if (input == HIGH)
{
return 1;
}
return 0;
}
رد نیا هدایپ ،يزاـس رادقم HIGH هب ناونع صیخـشت تکرح و رادقم LOW هب ناونع مدع صیخـشت تکرح رد رظن هتفرگ یم دوش .
يارب لرتنک تیلباق صیخشت ،تکرح ود ریغتم motionDetectionEnabled و motionDetectionTriggered رد Firmware فیرعت هدش تسا . ریغتم motionDetectionEnabled تیعــضو متــسیــس صیخــشت تکرح ار صخــشم یم دنک و ریغتم motionDetectionTriggered تیعضو کیرحت ندش متسیس ار صخشم یم دنک . لاعف ندرک تیلباق صیخــشت تکرح طــسوت عبات turnONMotionDetection ماجنا یم دوــش . رد نیا عبات هولاع رب رییغت تیعـضو ،یلخاد تیعـضو دیدج رد هظفاح هریخذ هدـش و زا قیرط MQTT زین علاطا یناـسر یم دوش . هب تروص ،هباشم عبات turnOFFMotionDetection تیلباق صیخشت تکرح ار ریغ لاعف یم دنک . تایئزج هدایپ يزاس رد لیاف cpp.pir/PIR/src تسویپ هدش ، لباق هدهاشم تسا .

-4-3-6 هدایپ يزاس متسیس رادشه یتوص

يارب داجیا رادـشه یتوـص زا کی Buzzer Active هدافتـسا هدـش تـسا . نیا رزاب اب قطنم Low-Active لرتنک یم ؛دوـش هب نیا ینعم هک حطـس یقطنم Low ثعاب لاعف ندـش رزاب و حطـس HIGH ثعاب لاعفریغ ندـش نآ یم دوش .
رد ماگنه هار ،يزادنا هیاپ صخـشم هدـش هب ناونع یجورخ میظنت هدـش و تیعـضو رزاب رد تلاح شوماخ رارق یم دریگ :

void setupBuzzer()
{
pinMode(BUZZER_PIN, OUTPUT);
stopAlarm();
}
عباـت startAlarm هـفیظو لاـعف ندرک رادـــشه ار رب هدـهع دراد . رد ،لـباـقم عباـت stopAlarm هـفیظو لاـعفریغ ندرک رادـشه ار رب هدهع دراد . رد تروـص لاعف ندوب ،رادـشه تیعـضو هیاپ یجورخ رزاب هب تروـص بوانتم طسوت updateAlarm رییغت یم دنک .

پی هدا زاس ی ھناماس

تایئزج هدایپ يزاس رد لیاف cpp.alarm/Alarm/src تسویپ ،هدش لباق هدهاشم تسا .

-4-4 هدایپ يزاس متسیس طابترا ییویدار RF

-4-4-1 یفرعم متسیس RF

یکی زا تیلباق ياه یلـصا ،هناماـس ناکما ،تفایرد هریخذ يزاـس و شخپزاب لانگیـس ياه ییویدار RF تـسا . نیا تیلباق اب فده داجیا ناکما لرتنک تازیهجت یکیرتکلا ياراد لرتنک زا هار رود رد هناماــس هدایپ يزاــس هدش تسا .
رد یحارط ،یلعف متـسیـس RF زا ود دناب یـسناکرف 315 و 433 زترهاگم ینابیتـشپ یم دنک . زا اجنآ هک هدنریگ و هدنتــسرف ره دناب هب تروــص لقتــسم لمع یم ،دننک يارب ره کی زا ود دناب کی هنومن لقتــسم زا سلاک RCSwitch رد Firmware داجیا هدش تسا .

-4-4-2 هار يزادنا متسیس RF

دنیارف هار يزادنا متـسیـس RF رد عبات setupRF ماجنا یم دوـش . رد نیا ،عبات هدنریگ و هدنتـسرف طوبرم هب ره ود دناب لاعف یم دنوش :

void setupRF()
{
rfSwitch433.enableReceive(RF_RX_433_PIN); rfSwitch433.enableTransmit(RF_TX_433_PIN); rfSwitch315.enableReceive(RF_RX_315_PIN); rfSwitch315.enableTransmit(RF_TX_315_PIN);
}
نیاربانب رد نامز هار يزادنا ،هاگتــسد ره ود هدنریگ يارب تفایرد لانگیــس و ره ود هدنتــسرف يارب لاــسرا لانگیس هدامآ یم دنوش .

-4-4-3 راتخاس هداد لانگیس RF

تاعلاطا ره لانگیس RF رد يراتخاس اب مان RFSignal هریخذ یم دوش :

struct RFSignal
{
String name;
uint32_t code;
uint16_t bits;
uint16_t protocol;
uint16_t pulse;

پی هدا زاس ی ھناماس

uint16_t band;
};
نیا راتخاـس لماـش تاعلاطا یلـصا دروم زاین يارب ییاـسانـش و شخپزاب کی لانگیـس RF تـسا هک رد لودج ریز زج ئ تای ره ریغتم هدروآ هدش تسا :

لودج (4-1 ) راتخاس هداد لانگیس RF
| | ریغتم عون هداد دربراک
| | name string مان لانگیس
| | code t_32uint دک یتفایرد لانگیس
دادعت تیب لانگیس | | bits t_16uint
لکتورپ صیخشت هداد هدش | | protocol t_16uint
سلاپ لوط | uint16_t | pulse
یسناکرف دناب | uint16_t | band
نینچمه هیارآ signals يارب هریخذ لانگیس ياه تفایرد هدش فیرعت هدش تسا .

-4-4-4 تفایرد لانگیس RF

دنیارف تفایرد لانگیـس طـسوت عبات readRFSignal ماجنا یم دوـش . نیا ،عبات تیعـضو ره ود هدنریگ ار یـسررب یم دنک .
رد ادتبا کی هراـشا رگ هب هدنریگ لاعف و يریغتم يارب يرادهگن دناب یـسناکرف فیرعت یم دوـش . سپـس هدنریگ 433 زترهاگم یـسررب یم دوـش . رد یتروـص هک هدنریگ 433 زترهاگم یلانگیـس تفایرد هدرکن ،دـشاب هدنریگ 315 هاگم زتر یسررب یم دوش . سپ زا ییاـسانـش هدنریگ ،لاعف رتماراپ ياه لانگیـس زا قیرط API هناخباتک RCSwitch جارختـسا یم دنوـش . رد تروــص ربتعم ندوب ،لانگیــس تاعلاطا نآ رد نیلوا تیعقوم دازآ هیارآ signals هریخذ یم دوــش . سپ زا شزادرپ زین تیعضو هدنریگ هب تلاح هیلوا هدنادرگزاب یم دوش ات هدامآ تفایرد لانگیس يدعب دشاب . تاـیئزج هداـیپ يزاـــس رد لـیاـف ياـه cpp.receiver/RF/src و cpp.general/RF/src تـــسویپ ،هدـــش لـباـق هدهاشم تسا .

-4-4-5 تیریدم دنیارف تفایرد لانگیس

تیریدم دنیارف تفایرد و هریخذ لانگیس رد عبات handleRFReceive ماجنا یم دوش . ادتبا رارق نتـشاد متـسیـس رد تلاح تفایرد یـسررب یم دوـش . رد تروـص تفایرد قفوم ،لانگیـس تیعـضو تفایرد هب تلاح لاعفریغ رییغت یم دنک و تاعلاطا تفایرد هدش رد هظفاح یمئاد متسیس هریخذ یم دوش . تایئزج هدایپ يزاس رد لیاف cpp.receiver/RF/src تسویپ ،هدش لباق هدهاشم تسا .

پی هدا زاس ی ھناماس

-4-4-6 پزاب شخ لانگیس RF

يارب لاسرا ددجم لانگیس هریخذ هدش زا عبات transmitRFSignal هدافتسا هدش تسا . شیپ زا ،لاـسرا دوجو لانگیـس و رابتعا لانگیـس و رتماراپ ياه یلـصا نآ یـسررب یم دوـش . سپـس اب وت جه هب دناب یسناکرف ،نآ هدنتسرف بسانم باختنا یم دوش . رد ،ادتبا لکتورپ و لوط سلاپ هریخذ هدـش يارب هدنتـسرف هطوبرم لقتنم یم دوـش . سپـس دک و دادعت تیب لانگیس لاسرا یم دوش .
تایئزج هدایپ يزاس رد لیاف cpp.transmitter/RF/src تسویپ ،هدش لباق هدهاشم تسا .

-4-4-7 تیریدم لانگیس ياه هریخذ هدش

يارب شیامن لانگیس ياه هریخذ ،هدش عبات listRFSignals هدایپ يزاس هدش تسا . رد تروـص دوجو نتـشاد ،لانگیـس تاعلاطا ره لانگیـس لماـش ،مان ،دناب ،دک دادعت تیب و لکتورپ زا قیرط Serial شیامن هداد یم دوـش و نینچمه هب تروـص کی ـشی JSON هتخاـس هدـش و زا قیرط MQTT رـشتنم یم دوش .
Topic طوبرم هب نیا تاعلاطا list/RF فیرعت هدـش تـسا هک ناکما ریدم تی لانگیـس اه ار زا قیرط دروبـشاد زین مهارف یم دنک .
تایئزج هدایپ يزاس رد لیاف cpp.general/RF/src تسویپ ،هدش لباق هدهاشم تسا .

-4-4-8 تسج و وج لانگیس RF

RFSignal *findRFSignalByName(const String &name) {
for (size_t i = 0; i < signalCount; i++)
{
if (signals[i].name == name)
{
return &signals[i];
}
}
return nullptr;
}
يارب ادیپ ندرک کی لانگیس RF رب ساسا مسا ،نآ عبات findRFSignalByName هدایپ يزاس هدش تسا . نیا ،عبات رد مامت لانگیـس ياه هریخذ هدـش تسج و وج یم دنک و رد تروص ادیپ ندرک لانگیس اب مسا هداد ،هدش نآ ار رب یم دنادرگ .

پی هدا زاس ی ھناماس

-4-4-9 فذح لانگیس هریخذ هدش

RFSignal *signal = findRFSignalByName(name); if (signal == nullptr)
{
Serial.println("RF signal not found"); return;
}

size_t index = signal - signals;
for (size_t i = index; i + 1 < signalCount; i++) {
signals[i] = signals[i + 1];
}
signalCount--;

if (saveRFSignals())
{
Serial.print("Deleted RF signal: "); Serial.println(name);
}
else
{
loadRFSignals();
Serial.println("Failed to delete RF signal"); }
يارب فذح لانگیـس هریخذ دـش ،ه رد ادتبا دوجو لانگیـس دروم رظن یـسررب یم دوـش . سپـس index نآ ادیپ هدـش و index ياه دعب نآ رد هیارآ signals، هب index یلبق دوخ تفیـش هداد یم دوـش و سپـس لانگیـس اه هریخذ یم دوش .

-4-4-10 قطنم یلک تفایرد و لاسرا RF

دنیارف تفایرد لانگیس رد هناماس هب تروص ریز تسا :

پی هدا زاس ی ھناماس

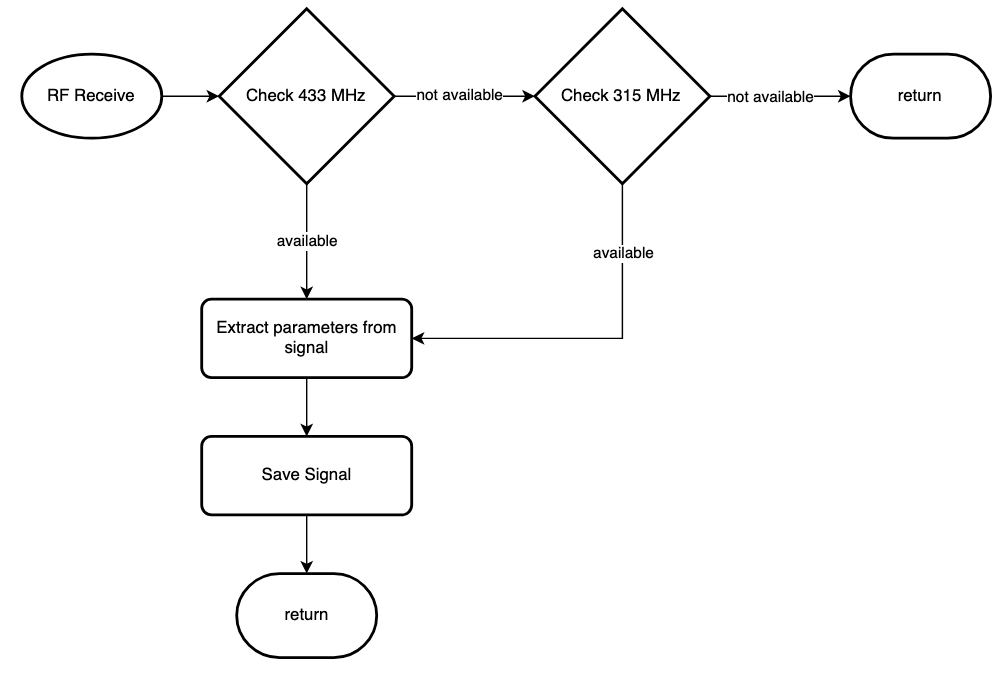
[picture p75: figure]

لکش (4-2 ) دنیارف تفایرد لانگیس RF

دنیارف لاسرا لانگیس رد هناماس هب تروص ریز تسا :

لکش (4-3 ) دنیارف لاسرا لانگیس RF

-4-5 هدایپ يزاس متسیس نودام مرق ز IR

-4-5-1 یفرعم متسیس نودام زمرق

یکی رگید زا تیلباق ياه ،هناماـس ناکما ،تفایرد هریخذ يزاـس و شخپزاب نامرف ياه نودام زمرق تـسا . نیا تیلباق اب فده مهارف ندرک ناکما لرتنک یتازیهجت هک زا لرتنک نودام زمرق هدافتسا یم دننک . رد نیا شخب زا کـی هدـنریگ نوداـم زمرق يارب تـفاـیرد لاـنگیـــس و راـهچ LED IR يارب لاـــسرا ددـجم نآ هدافتسا هدش تسا . شزادرپ لانگیس طسوت هناخباتک 8266IRremoteESP ماجنا یم دوش .

پی هدا زاس ی ھناماس

-4-5-2 هار يزادنا متسیس IR

يارب تیریدم متسیس نودام ،زمرق ود شی زا سلاک ياه IRrecv و IRsend داجیا هدش تسا . هدـنریگ هـفیظو تـفاـیرد و decode ندرک لاـنگیـــس ياـه نوداـم زمرق ار و هدـنتـــسرف هـفیظو encode ندرک و لاسرا لانگیس نودام زمرق ار رب هدهع دراد . هار يزادنا نیا ود شخب رد عبات setupIR ماجنا یم دوش :

void setupIR()
{
irReceiver.enableIRIn();
irTransmitter.begin();
}

-4-5-3 راتخاس هداد لانگیس IR

يارب هریخذ تاعلاطا لانگیس ياه نودام ،زمرق راتخاس IRSignal فیرعت هدش تسا :

struct IRSignal
{
String name;
decode_type_t protocol;
uint64_t value;
uint16_t bits;
uint16_t rawLength;
uint16_t rawData[MAX_IR_RAW_LENGTH];
};
نیا راتخاـس لماـش تاعلاطا یلـصا دروم زاین يارب ییاسانش و شخپزاب کی لانگیس IR تسا هک رد لودج ریز زج ئ تای ره ریغتم هدروآ هدش تسا :

لودج (4-2 ) راتخاس هداد لانگیس IR
| | ریغتم عون هداد دربراک
| | name string مان لانگیس
لکتورپ صیخشت هداد هدش | | protocol t_type_decode
لانگیس هدش Decode رادقم | uint64_t | value
| | bits t_16uint دادعت تیب لانگیس
| | length raw t_16uint دادعت هنومن هداد ماخ
لانگیس ماخ هداد | uint16_t[] | raw data
يارب هریخذ لانگیس ياه نودام زمرق زین هیارآ IRSignals فیرعت هدش تسا .

پی هدا زاس ی ھناماس

-4-5-4 تفایرد و Decode لانگیس IR

تفایرد لانگیس نودام زمرق طسوت عبات readIRSignal ماجنا یم دوش . رد ادـتبا کـی راـتخاـــس results_decode يارب تـفاـیرد هـجیتن Decode داـجیا هدـــش و هدـنریگ شلات یم دـنک لانگیــس جوم دو ار تفایرد دنک . سپ زا تفایرد ،لانگیــس ود تیعــضو overflow و rawlength يارب ربتعم ندوب هداد یسررب یم دوش . سپ زا ربتعم ندوب ،لانگیس کی index زا هیارآ IRSignals هب لانگیس صاصتخا هداد یم دوش و سپس رتماراپ ياه تفایرد هدش زا لانگیس رد نآ هریخذ یم دوش . هولاع رب طا تاعلا Decode ،هدـش هداد ماخ لانگیـس زین هریخذ یم ؛دوـش اریز همه لانگیـس ياه نودام زمرق امازلا طـسوت هناخباتک هب کی لکتورپ هتخانـش هدـش لباق Decode ندرک دنتـسین و يارب شخپزاب نیا لانگیـس اه هب هداد ماخ نآ زاین تسا . تایئزج هدایپ يزاـس رد لیاف ياه cpp.receiver/IR/src و cpp.general/IR/src تـسویپ ،هدـش لباق هدهاـشم تسا .

-4-5-5 تیریدم دنیارف تفایرد لانگیس

عبات handleIRReceive، دنیارف تفایرد و هریخذ لانگیس نودام زمرق ار تیریدم یم دنک . ادتبا رارق نتـشاد متـسیـس رد تلاح تفایرد یـسررب یم دوـش . رد تروـص تفایرد قفوم ،لانگیـس تیعـضو تفایرد هب تلاح لاعفریغ رییغت یم دنک و تاعلاطا تفایرد هدش رد هظفاح یمئاد متسیس هریخذ یم دوش . تایئزج هدایپ يزاس رد لیاف cpp.receiver/IR/src تسویپ ،هدش لباق هدهاشم تسا .

-4-5-6 شخپزاب لانگیس IR

دنیارف لاسرا لانگیس طسوت عبات transmitIRSignal ماجنا یم دوش . رد ،ادتبا دوجو و ابتعا ر لانگیـس یـسررب یم دوـش . سپـس اب هجوت هب لکتورپ هریخذ ،هدـش شور لاـسرا بـسانم باختنا یم دوش و لانگیس لاسرا یم دوش . رد لاح ،رـضاح Firmware زا لکتورپ ياه NEC، SONY، SAMSUNG و PANASONIC ینابیتـشپ یم دنک .
رد تروـص ینابیتـشپ ندـشن و ای سانـشان ندوب لکتورپ ،لانگیـس هداد ماخ لانگیـس اب سناکرف 38 زترهولیک شخپزاب یم دوش .
تایئزج هدایپ يزاس رد لیاف cpp.transmitter/IR/src تسویپ ،هدش لباق هدهاشم تسا .

-4-5-7 تیریدم لانگیس ياه هریخذ هدش

يارب شیامن لانگیس ياه هریخذ ،هدش عبات listIRSignals هدایپ يزاس هدش تسا .

پی هدا زاس ی ھناماس

رد تروـص دوجو نتـشاد ،لانگیـس تاعلاطا ره لانگیـس لماـش ،مان ،لکتورپ دادعت تیب و لوط هداد ماخ زا قیرط Serial شیامن هداد یم دوـش و نینچمه هب تروـص کی ـش ی JSON هتخاـس هدـش و زا قیرط MQTT رشتنم یم دوش .
Topic طوبرم هب نیا تاعلاطا list/IR فیرعت هدـش تـسا هک ناکما تیریدم گیـس لان اه ار زا قیرط دروبـشاد زین مهارف یم دنک .
تایئزج هدایپ يزاس رد لیاف cpp.general/IR/src تسویپ ،هدش لباق هدهاشم تسا .

-4-5-8 تسج و وج لانگیس IR

IRSignal *findIRSignalByName(const String &name) {
for (size_t i = 0; i < irSignalCount; i++) {
if (irSignals[i].name == name)
{
return &irSignals[i];
}
}
return nullptr;
}
يارب ادیپ ندرک کی لانگیس IR رب ساسا مسا ،نآ عبات findIRSignalByName هدایپ يزاس هدش تسا . نیا ،عبات رد مامت لانگیـس ياه هریخذ هدـش تسج و وج یم دنک و رد تروص ادیپ ندرک لانگیس اب مسا هداد ،هدش نآ ار رب یم دنادرگ .

-4-5-9 فذح لانگیس هریخذ هدش

IRSignal *signal = findIRSignalByName(name); if (signal == nullptr)
{
Serial.println("IR signal not found"); return;
}

size_t index = signal - irSignals;
for (size_t i = index; i + 1 < irSignalCount; i++) {
irSignals[i] = irSignals[i + 1];
}
irSignalCount--;

if (saveIRSignals())
{
Serial.print("Deleted IR signal: ");

پی هدا زاس ی ھناماس

Serial.println(name);
}
else
{
loadIRSignals();
Serial.println("Failed to delete IR signal"); }
يارب فذح لانگیـس هریخذ ،هدـش رد ادتبا دوجو لانگیـس دروم رظن یـسررب یم دوـش . سپـس index نآ ادیپ هدش و index ياه دعب نآ رد هیارآ irSignals، هب index یلبق دوخ تفیش هداد یم دوش و سپس لانگیس اه هریخذ یم دوش .

-4-5-10 قطنم یلک تفایرد و لاسرا IR

دنیارف تفایرد لانگیس رد هناماس به تروص ریز تسا :

لکش (4-4 ) دنیارف تفایرد لانگیس IR

دنیارف لاسرا لانگیس رد هناماس هب تروص ریز تسا :

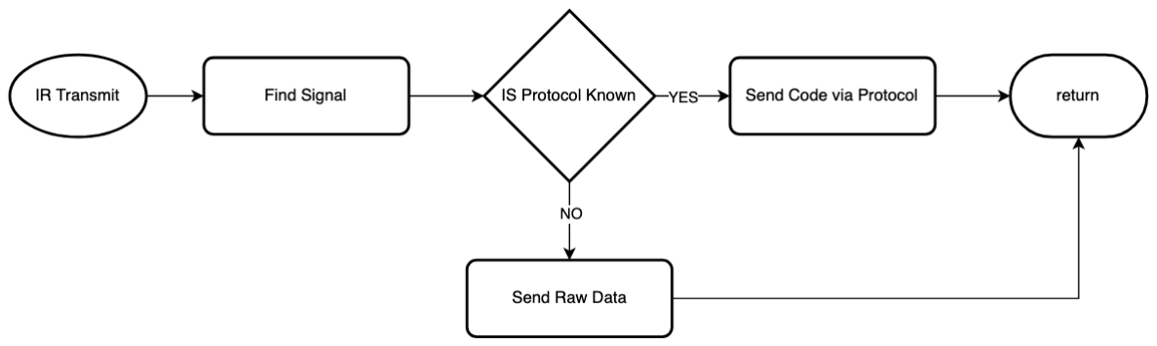
[picture p76: figure]

لکش (4-5 ) دنیارف لاسرا لانگیس IR

-4-6 هدایپ يزاس طابترا Fi-Wi و MQTT

-4-6-1 همدقم

هب روظنم داجیا طابترا نایم هاگتـسد و تخاـسریز مرن يرازفا ،هناماـس زا ود يروانف Fi-Wi و MQTT هدافتـسا

پی هدا زاس ی ھناماس

هدش تسا . طابترا Fi-Wi هفیظو لاصتا 32ESP هب هکبش یلحم و مهارف ندرک یسرتسد هب Broker MQTT ار رب هدهع دراد و لکتورپ MQTT زین يارب لدابت مایپ ياه یلرتنک و تاعلاطا اهرگسح ا هدافتس یم دوش .

MQTT Client داجیا -4-6-2

static WiFiClient wifiClient;
static PubSubClient mqttClient(wifiClient);
static MqttCommandHandler mqttCommandHandler = nullptr;
رد يادتبا لوژام MQTT، کی ـش ی زا سلاک WiFiClient و کی ـش ی زا سلاک PubSubClient داجیا هدـش تــــسا . نـیـنـچـمـه يارـب تـیرـیدـم ناـمرـف ياـه یـتـفاـیرد زا MQTT، کـی عـباـت Callback زا عوـن MQTTCommandHandler فیرعت هدش تسا .

-4-6-3 يرارقرب طابترا Fi-Wi

static void connectWiFi()
{
if (WiFi.status() == WL_CONNECTED) {
return;
}

const char *ssid = provisioningConfig.wifiSSID.length() > 0
? provisioningConfig.wifiSSID.c_str()
: WIFI_SSID;
const char *wpass = provisioningConfig.wifiPassword.length() > 0 ? provisioningConfig.wifiPassword.c_str() : WIFI_PASSWORD;

WiFi.begin(ssid, wpass);
}
هفیظو لاصتا هاگتسد هب هکبش Fi-Wi طسوت عبات connectWiFi ماجنا یم دوش . ادتبا تیعـضو یلعف لاـصتا یـسررب یم دوـش و رد یتروـص هک هاگتـسد زا لبق لـصتم ،دـشاب تایلمع لاـصتا ددجم ماجنا یمن دوـش . سپـس تاعلاطا هکبـش زا تامیظنت Provisioning ای ریداقم شیپ ضرف هدناوخ یم دوـش و رد تیاهن لاصتا هب هکبش Fi-Wi ماجنا یم دوش .

-4-6-4 لاصتا هب Broker MQTT

static bool connectMQTT()
{

پی هدا زاس ی ھناماس

const char *host = provisioningConfig.mqttHost.length() > 0 ? provisioningConfig.mqttHost.c_str() : MQTT_HOST;
uint16_t port = provisioningConfig.mqttPort > 0
? provisioningConfig.mqttPort
: MQTT_PORT;
const char *mqttUser = provisioningConfig.mqttUser.length() > 0
? provisioningConfig.mqttUser.c_str()
: MQTT_USER;
const char *mqttPass = provisioningConfig.mqttPassword.length() > 0 ? provisioningConfig.mqttPassword.c_str() : MQTT_PASSWORD;

bool connected = false;
if (strlen(mqttUser) > 0)
{
connected = mqttClient.connect(MQTT_CLIENT_ID, mqttUser, mqttPass); }
else
{
connected = mqttClient.connect(MQTT_CLIENT_ID); }

if (!connected)
{
Serial.print("MQTT connect failed, state="); Serial.println(mqttClient.state());
return false;
}

String commandTopic = topicFor(MQTT_COMMAND_TOPIC); mqttClient.subscribe(commandTopic.c_str());
return true;
سپ زا يرارقرب طابترا Fi-Wi، دنیارف لاـــصتا هب Broker MQTT طـــسوت عبات connectMQTT ماجنا یم دوش . رد تروص رارقرب ندوبن طابترا Fi-Wi، لاصتا MQTT ماجنا یمن دوش . ادـتبا تاـعلاطا Broker زا تاـمیظنت Provisioning و رد تروـــص دوبن نآ زا ریداـقم شیپ ضرف هدـناوخ یم دوـش . راتخاـس هدایپ يزاـس ناکما هدافتـسا زا مان يربراک و زمر روبع ار زین يارب لاـصتا مهارف هدرک تـسا . سپـس اب هجوت هب دوجو ای مدع دوجو مان ،يربراک یکی زا ود شور لاصتا هدافتسا یم دوش . سپ زا لاصتا قفوم هب Broker، هاگتسد هب Topic طوبرم هب تفایرد نامرف Subscribe یم دنک .

-4-6-5 هار يزادنا هیلوا MQTT

void setupMQTT(MqttCommandHandler commandHandler) {
mqttCommandHandler = commandHandler;

پی هدا زاس ی ھناماس

const char *host = provisioningConfig.mqttHost.length() > 0 ? provisioningConfig.mqttHost.c_str() : MQTT_HOST;
uint16_t port = provisioningConfig.mqttPort > 0
? provisioningConfig.mqttPort
: MQTT_PORT;

WiFi.setAutoReconnect(true); connectWiFi();
mqttClient.setServer(host, port); mqttClient.setCallback(mqttCallback);
}
يارب هار يزادنا هیلوا MQTT زا عبات setupMQTT هدافتسا هدش تسا . ادتبا commandHandler هک هب ناونع يدورو هداد یم ،دوــش هریخذ یم دوــش . سپــس تاعلاطا Broker زا تامیظنت Provisioning ای ریداقم شیپ ضرف هدناوخ یم دوـش . سپـس لاـصتا هب هکبـش Fi-Wi ماجنا یم دوش و رد رخآ هب Broker MQTT لصتم یم دوش .

-4-6-6 يرارقرب لاصتا ددجم MQTT

void handleMQTT()
{
if (WiFi.status() != WL_CONNECTED)
{
unsigned long now = millis();
if (now - lastReconnectAttempt >= MQTT_RECONNECT_INTERVAL) {
lastReconnectAttempt = now;
connectMQTT();
}
return;
}

if (!mqttClient.connected())
{
unsigned long now = millis();
if (now - lastReconnectAttempt >= MQTT_RECONNECT_INTERVAL) {
lastReconnectAttempt = now;
connectMQTT();
}
return;
}

mqttClient.loop();
}
رد لوط يارجا ،همانرب لاـصتا هاگتـسد هب هکبـش Fi-Wi و Broker کچ یم دوـش و رد تروـص دوجو نتـشاد

پی هدا زاس ی ھناماس

،داریا شلات يارب لاـصتا ددجم ماجنا یم دوـش . رد ریغ ،تروـصنیا تفایرد مایپ دیدج و يارجا Callback ياه يدورو ار هدهعرب دراد .

-4-6-7 تفایرد نامرف ياه MQTT

static void mqttCallback(char *topic, byte *payload, unsigned int length) {
String command;
command.reserve(length + 1);

for (unsigned int i = 0; i < length; i++)
{
command += static_cast<char>(payload[i]); }

command.trim();
Serial.print("MQTT command on "); Serial.print(topic);
Serial.print(": ");
Serial.println(command);

if (command.length() > 0 && mqttCommandHandler != nullptr) {
mqttCommandHandler(command);
}
}
يارب تفایرد مایپ ياه MQTT زا Callback هدافتسا هدش تسا . رد نیا عبات Payload یتفایرد هب کی String لیدبت یم دوــش و سپــس نامرف رد Monitor Serial شیامن هداد یم دوش و رد تیاهن ،نامرف هب Handler هطوبرم لقتنم یم دوش .

-4-6-8 راشتنا تاعلاطا رد MQTT

bool publishMQTT(const String &subTopic, const String &payload, bool retained) {
if (!mqttClient.connected())
{
return false;
}

String topic = topicFor(subTopic);
return mqttClient.publish(topic.c_str(), payload.c_str(), retained); }
يارب لاسرا تاعلاطا هب Broker، عبات publishMQTT هدایپ يزاس هدش تسا :

پی هدا زاس ی ھناماس

رد ادتبا لاصتا MQTT یسررب یم دوش و سپس Topic ییاهن هتخاس هدش و اب Payload رشتنم یم دوش .

-4-7 هدایپ يزاس يدنبرکیپ هیلوا و تیریدم لاصتا هب هکبش

هب روظنم يریگولج زا یگتسباو میقتسم تامیظنت هکبش و Broker MQTT هب دک Firmware، رد هژورپ کی ریز هناماـس لقتـسم اب ناونع Provisioning یحارط و پ هدای يزاـس هدـش تـسا . هفیظو نیا ،هناماـسریز تیریدم تاعلاطا زایندروم يارب لاــصتا 32ESP هب هکبــش Fi-Wi و Broker MQTT و نینچمه مهارف ندرک ناکما رییغت نیا تامیظنت نودب زاین هب رییغت ای لیاپماک ددجم Firmware تسا .

-4-7-1 راتخاس تاعلاطا يدنبرکیپ

رد لوژام Provisioning، تاعلاطا یطابترا هاگتـسد اب مان ProvisioningConfig رد بلاق راتخاـس ریز رعت یف هدش تسا :

struct ProvisioningConfig
{
String wifiSSID;
String wifiPassword;
String mqttHost;
uint16_t mqttPort;
String mqttUser;
String mqttPassword;
String client;
};
یا ن راتخاــس ناکما يرادهگن یمامت رتماراپ ياه زایندروم يارب يرارقرب طابترا هاگتــسد اب هکبــش و MQTT Broker ار مهارف یم دنک .
تایئزج ره ریغتم رد لودج ریز هدمآ تسا :

لودج (4-3 ) راتخاس هداد تامیظنت يدنبرکیپ
| | | ریغتم عون هداد دربراک
يرابجا | AP مان | String | wifiSSID
| Wi-Fi روبع زمر | String | wifiPassword يرابجا
| MQTT Broker سردآ | String | mqttHost يرابجا
| MQTT Broker تروپ | uint16_t | mqttPort يرابجا
| MQTT Broker يربراک مان | String | mqttUser يرایتخا
| MQTT Broker روبع زمر | String | mqttPassword يرایتخا
| مان هاگتسد يرابجا | | client String

پی هدا زاس ی ھناماس

-4-7-2 AP یصاصتخا يارب يدنبرکیپ

یکی زا تیلباق ياه هدایپ يزاس هدش رد ،هژورپ داجیا کی AP یصاصتخا يارب ماجنا تامیظنت هاگتسد تسا . درب 32ESP رد تلاح STA_AP_WIFI تیلاعف یم دنک . نیاربانب هاگتــسد یم دناوت هب تروــص نامزمه هب هکبش یلصا لصتم دشاب و کی هکبش یب میس یصاصتخا زین يارب يدنبرکیپ داجیا دنک .

-4-7-3 لاتروپ تحت بو يدنبرکیپ

يارب ماجنا ،تامیظنت کی لاتروپ تحت بو يور 32ESP ارجا یم دوش . ربراک یم دناوت اب لاصتا هنایار ای نفلت ه هارم دوخ هب هکبـش Setup-Intelligence و هعجارم هب سردآ 192.168.4.1 هب هحفـص يدنبرکیپ یـسرتـسد ادیپ دنک .

-4-7-4 هدایپ يزاس Portal Captive

يارب هداس رت ندش دنیارف ،يدنبرکیپ رد هژورپ زا مزیناکم Portal Captive هدافتسا هدش تسا . يارب نیا روظنم کـی Server DNS داـجیا هدـــش و ماـمت ی تـــساوخرد ياـه DNS هـب سردآ IP طوبرم هـب Point Access تیاده یم دنوش . نینچمه کی WebServer يور تروپ 80 داجیا هدش تسا .

-4-7-5 تیریدم تساوخرد ياه HTTP

server.on("/", HTTP_GET, handleRoot);
// OS connectivity-check probes — redirecting them (instead of returning the // expected "success"/204 response) is what makes the captive portal pop up
// automatically on iOS / Android / Windows.
server.on("/generate_204", HTTP_GET, redirectToPortal); | // Android
server.on("/gen_204", HTTP_GET, redirectToPortal); | // Android (alt)
server.on("/hotspot-detect.html", HTTP_GET, redirectToPortal); // Apple
server.on("/ncsi.txt", HTTP_GET, redirectToPortal); | // Windows
server.on("/connecttest.txt", HTTP_GET, redirectToPortal); | // Windows
server.on("/redirect", HTTP_GET, redirectToPortal); | // Windows
server.on("/save", HTTP_POST, handleSave);
server.onNotFound(handleNotFound);
رد لوژام Provisioning ریـسم ياه یفلتخم يارب تیریدم تـساوخرد يا HTTP فیرعت هدـش تـسا . مهم نیرت ،ریـسم ریـسم یلـصا / تـسا هک هحفـص يدنبرکیپ ار هب ربراک شیامن یم دهد . نینچمه ریـسم save/ يارب تفایرد تاعلاطا لاسرا هدش طسوت ربراک دروم سا هدافت رارق هتفرگ تسا . رد تروص تفایرد تساوخرد يارب ریسم ياه هتخانشان زین ربراک هب هحفص يدنبرکیپ تیاده یم دوش . يارب رتهب ندـش هبرجت ،يربراک Check Connectivity ياه متـسیـس ياه لماع هب هحفـص يدنبرکیپ تیاده

پی هدا زاس ی ھناماس

یم دنوش ات هب تروص راکدوخ دعب زا لصتم ندش ربراک هب AP، حفص ه يدنبرکیپ زاب دوش .

-4-7-6 تفایرد و یجنسرابتعا تامیظنت

عبات handleSave، تاعلاطا دراو هدـش طـسوت ربراک ار زا تـساوخرد HTTP تفایرد هدرک و کی هنومن دیدج زا ProvisioningConfig داجیا یم دنک . رتماراپ ياه طوبرم هب Fi-Wi و MQTT زا مرف تفایرد هدـش و سپـس یـسررب یم دنوـش . رد یتروـص هک مان ،هکبش سردآ Broker MQTT ای مان هاگتسد یلاخ ،دشاب تساوخرد اب ياطخ 400 در یم دوش . رد یتروص هک ربراک رد هحفص ،تامیظنت دلیف زمر روبع Fi-Wi ای MQTT ار یلاخ ،دراذگب همانرب رادقم یلبق ار ظفح یم دنک . رد ،هجیتن زمر روبع دوجوم رد هظفاح هب تروـص میقتـسم هب ربراک شیامن هداد یمن دوـش و ربراک يارب ظفح زمر روبع یلعف يزاین هب دراو ندرک ددجم نآ درادن . سپ زا ربتعم ندوب ،تاعلاطا تامیظنت طـسوت saveProvisioningConfig هریخذ یم دوـش و هاگتـسد اددجم هار يزادنا یم دوش .
تایئزج هدایپ س يزا رد لیاف cpp.provisioning/Provisioning/src تسویپ ،هدش لباق هدهاشم تسا .

-4-8 هدایپ يزاس تیریدم هظفاح و هریخذ يزاس تاعلاطا

رد نیا ،هژورپ هب روظنم ظفح تاعلاطا زایندروم متـسیـس سپ زا شوماخ و نـشور ندـش 32ESP، زا متـسیـس لیاف LittleFS هدافتـسا هدـش تـسا . نیا لوژام تیلوئـسم هریخذ يزاـس و یبایزاب تاعلاطا طوبرم هب تامیظنت ،متسیس تیعضو صیخشت تکرح و لانگیس ياه IR و RF ار رب هدهع دراد .

-4-8-1 متسیس لیاف LittleFS

يارب هریخذ يزاـس تاعلاطا زا هناخباتک LittleFS هدافتـسا هدـش تـسا . رد يادتبا تایلمع یـسرتـسد هب فاح ،هظ عبات یلخاد ensureLittleFS تیعضو هدامآ ندوب متسیس لیاف ار یسررب یم دنک .

-4-8-2 بلاق JSON

يارب یهدراتخاـس تاعلاطا هریخذ هدـش زا هناخباتک ArduinoJson هدافتـسا هدـش تـسا . تاعلاطا شیپ زا هریخذ يزاـس هب راتخاـس JSON لیدبت هدـش و ماگنه یبایزاب اددجم زا JSON هب راتخاـس ياه دروم هدافتـسا همانرب لیدبت یم دنوش .

پی هدا زاس ی ھناماس

-4-8-3 هریخذ و یبایزاب تیعضو صیخشت تکرح

زا اجنآ هک تیعـضو لاعف ای لاعفریغ ندوب صیخـشت تکرح دیاب سپ زا هار يزادنا ددجم هاگتـسد ظفح ،دوـش نیا رادقم رد لیاف json.settings/ هریخذ یم دوش . عبات saveMotionDetection رادقم تیعضو صیخشت تکرح ار تفایرد هدرک و نآ ار رد بلاق JSON هریخذ یم دـنک . رد ،لـباـقم عباـت loadMotionDetection لـیاـف تاـمیظنت ار زاـب هدرک و رادـقم هریخذ هدـــش ار یباـیزاـب یم دنک . رد یتروـص هک لیاف دوجو هتـشادن ،دـشاب متـسیـس هب تروـص شیپ رف ض تیلباق صیخـشت تکرح ار لاعفریغ یم دنک .
نیا تاعلاطا رد نامز يارجا setupPIR دروم هدافتـسا رارق هتفرگ و تیعـضو یلبق صیخـشت تکرح ار یبایزاب یم دنک .
تایئزج هدایپ يزاس رد لیاف cpp.memmory/Memmory/src تسویپ ،هدش لباق هدهاشم تسا .

-4-8-4 هریخذ و یبایزاب لانگیس ياه RF

لانگیس ياه RF تفایرد هدش طسوت متسیس رد لیاف json.signals_rf/ هریخذ یم دنوش . عبات saveRFSignals ادتبا کی هیارآ JSON داجیا هدرک و سپـس يارب ره ،لانگیـس کی ـش ی JSON داجیا هدرک و تاعلاطا لانگیس ياه دوجوم ار رد نآ رارق یم دهد . رد یاهن ،ت هیارآ JSON ار هریخذ یم دنک . عبات loadRFSignals ماگنه هار يزادنا ،متـسیـس تاعلاطا هریخذ هدـش رد متـسیـس ار یبایزاب یم دنک و رد هیارآ signals هک رد شخب -4-4-3 حیضوت هداد هدش ،تسا رارق یم دهد . تایئزج هدایپ يزاس رد لیاف cpp.memmory/Memmory/src تسویپ ،هدش لباق هدهاشم تسا .

-4-8-5 هریخذ و یبایزاب لانگیس ياه IR

لانگیس ياه IR تفایرد هدش طسوت متسیس رد لیاف json.signals_ir/ هریخذ یم دنوش . عبات saveIRSignals ادتبا کی هیارآ JSON داجیا هدرک و سپــس يارب ره ،لانگیــس کی ــش ی JSON داجیا هدرک و تاعلاطا لانگیس ياه دوجوم ار رد نآ رارق یم دهد . رد ،تیاهن هیارآ JSON ار هریخذ یم دنک . عبات loadIRSignals ماگنه هار يزادنا ،متـسیـس تاعلاطا هریخذ هدـش رد متـسیـس ار یبایزاب یم دنک و رد هیارآ irSignals هک در شخب -4-5-3 حیضوت هداد هدش ،تسا رارق یم دهد . تایئزج هدایپ يزاس رد لیاف cpp.memmory/Memmory/src تسویپ ،هدش لباق هدهاشم تسا .

-4-8-6 هریخذ و یبایزاب تامیظنت Provisioning

تاعلاطا طوبرم هب يدنبرکیپ هیلوا هاگتسد رد لیاف json.provisioning/ هریخذ یم دنوش .

پی هدا زاس ی ھناماس

عبات saveProvisioningConfig، کی یـش JSON هتخاـس و تامیظنت ار رد نآ رارق یم دهد و سپـس نآ ار هریخذ یم دـنک . عباـت loadProvisioningConfig، اـمیظنت ت ار زا لـیاـف هدـناوخ و رد provisioningConfig هک رد شخب -4-7-1 حیضوت هداد هدش ،تسا رارق یم دهد . تایئزج هدایپ يزاس رد لیاف cpp.memmory/Memmory/src تسویپ ،هدش لباق هدهاشم تسا .

-4-9 هار يزادنا و یگنهامه لوژام اه

هتـسه یلـصا همانرب لماـش ود عبات setup و loop تـسا . عبات setup اهنت کی راب رد ماگنه هار يزادنا 32ESP ارجا یم دوـش و هفیظو هدامآ يزاـس هیلوا متـسیـس ار هدهعرب دراد . سپ زا ،نآ عبات loop هب تروـص موادم ارجا هدش و فیاظو فلتخم متسیس ار تیریدم یم دنک .

-4-9-1 عبات setup

void setup()
{
Serial.begin(115200);
delay(200);

loadProvisioningConfig();
startConfigAP();

setupSensors();
setupMQTT(handleMqttCommand);
printHelp();
}
عبات setup هطقن عورش هار يزادنا متسیس تسا و اهنت کی راب سپ زا نشور ندش هاگتسد ارجا یم دوش . رد ادتبا طابترا لایرس اب خرن baud 115200 هار يزادنا یم دوش . سپس تامیطنت هریخذ هدش Provisioning زا هظفاح یلخاد یبایزاب هدش و Point Access طوبرم هب اماس هن يدنبرکیپ لاعف یم دوش . سپ زا ،نآ عبات setupSensors هفیظو هار يزادنا يازجا تخـس يرازفا متـسیـس ار رب هدهع یم دریگ . رد همادا طابترا MQTT میظنت هدش و رد تیاهن نامرف ياه لباق هدافتسا رد Monitor Serial شیامن هداد یم دنوش .

-4-9-2 عبات loop

void loop()
{
handleSerial();
handleMQTT();
handleConfigAP();

پی هدا زاس ی ھناماس

handleSensors();
}
سپ زا لیمکت تایلمع هار ،يزادنا عبات loop هب تروص موادم ارجا یم دوش . رد ره هخرچ یلصا ،همانرب راهچ هفیظو یلصا شزادرپ یم دنوش :
- تفایرد و شزادرپ نامرف ياه Serial
- تیریدم طابترا MQTT
- پ شزادر تساوخرد ياه Portal Captive
- تیریدم روسنس ،اه رادشه اه و لانگیس ياه RF و IR

-4-9-3 هار يزادنا لوژام ياه تخس يرازفا

void setupSensors()
{
setupMQ2();
setupDHT();
setupPIR();
setupBuzzer();
setupRF();
setupIR();
setupLDR();
nextMQ2ReadAt = millis() + MQ2_PREHEAT_DURATION; loadRFSignals();
loadIRSignals();
setupStatusLED();
}
عبات setupSensors رد لوژام Sensors هفیظو هدامآ يزاــس مامت روــسنــس اه و تازیهجت یبناج ار رب هدهع دراد .

-4-9-4 تیریدم نامرف ياه متسیس

نامرف ياه متـسیـس رد لوژام Serial شزادرپ یم دنوـش . نیا نامرف اه زا قیرط MQTT و Monitor Serial لباق تفایرد دنتسه .

-4-9-4-1 شزادرپ نامرف ياه RF نامرف ياه طوبرم هب RF لماش راهچ تایلمع یلصا دنتسه : rf rx <name>
rf tx <name>
rf del <name>
rf list
رد تروـص تفایرد نامرف <name <rx rf، ادتبا دوجو مان لانگیـس یـسررب یم دوـش . رد تروـص ربتعم ندوب

پی هدا زاس ی ھناماس

،تساوخرد متسیس دراو تیعضو تفایرد RF یم دوش . رد تروـص تفایرد نامرف <name <tx rf، ادتبا لانگیـس اب مان دروم رظن ادیپ یم دوـش و سپـس لانگیـس يارب لوژام RF لاسرا یم دوش .
تایئزج هدایپ يزاس رد لیاف cpp.serial/Serial/src تسویپ ،هدش لباق هدهاشم تسا .

-4-9-4-2 شزادرپ نامرف ياه IR نامرف ياه طوبرم هب IR لماش راهچ تایلمع یلصا دنتسه : ir rx <name>
ir tx <name>
ir del <name>
ir list
رد تروـص تفایرد نامرف <name <rx ir، ادتبا دوجو مان لانگیـس یـسررب یم دوـش . رد تروـص ربتعم ندوب ،تساوخرد متسیس دراو تیعضو تفایرد IR یم دوش . رد تروـص تفایرد نامرف <name <tx ir، ادتبا لانگیـس اب مان دروم رظن ادیپ یم دوـش و سپـس لانگیـس يارب لوژام IR لاسرا یم دوش .
تایئزج هدایپ يزاس رد لیاف cpp.serial/Serial/src تسویپ ،هدش لباق هدهاشم تسا .

-4-9-4-3 تیریدم نامرف ياه متسیس رادشه

if (action == "buzzer")
{
int subSeparator = argument.indexOf(' ');
String subAction = subSeparator == -1 ? argument : argument.substring(0, subSeparator);
String name = subSeparator == -1 ? "" : argument.substring(subSeparator + 1);

if (subAction == "on")
{
startAlarm();
return;
}

if (subAction == "off")
{
stopAlarm();
return;
}

Serial.println("Unknown command. Type: help");
return;
}
متسیس رادشه نامرف ياه ریز ار يارب لرتنک میقتسم Buzzer رد رایتخا ربراک رارق یم دهد : buzzer on
buzzer off

پی هدا زاس ی ھناماس

هولاع رب لرتنک ،یتسد متسیس رادشه یم دناوت طسوت دادیور ياه رگسح اه زین لاعف دوش . يارب عطق ندرک رادشه سپ زا عوقو کی ،دادیور زا نامرف off buzzer یم ناوت هدافتسا درک .

-4-9-4-4 تیریدم نامرف ياه صیخشت تکرح

if (action == "motion")
{
int subSeparator = argument.indexOf(' ');
String subAction = subSeparator == -1 ? argument : argument.substring(0, subSeparator);
String name = subSeparator == -1 ? "" : argument.substring(subSeparator + 1);

if (subAction == "on")
{
turnONMotionDetection();
return;
}

if (subAction == "off")
{
turnOFFMotionDetection();
return;
}

Serial.println("Unknown command. Type: help"); return;
}
صیخشت تکرح زین زا قیرط نامرف ياه ریز لباق لاعف ای لاعفریغ ندرک تسا : motion on
motion off
رد تروـص لاعف ای لاعفریغ ندـش تیلباق صیخـشت ،تکرح تیعـضو نآ رد هظفاح یلخاد هاگتـسد زین هریخذ یم دوش .

-4-9-5 تیریدم ندناوخ اهرگسح

void handleSensors()
{
handleRFReceive(receivingRF, receiveName); handleIRReceive(receivingIR, receiveName); updateAlarm();
updateStatusLED();
updatePulseLED();
checkMotionDetection();
printSensors();
}
ندناوخ اهرگسح رد لوژام Sensors طسوت عبات handleSensors ماجنا یم دوش .

پی هدا زاس ی ھناماس

رد نیا عبات ادتبا تیعضو تفایرد RF و IR یسررب یم دوش . سپس متسیس رادشه و LED هب یناسرزور هدش و تیعضو صیخشت تکرح یسررب یم دوش . رد تیاهن تاعلاطا اهرگسح هدناوخ و رشتنم یم دنوش .

-4-9-5-1 نامز يدنب ندناوخ رگسح اه يارب يریگولج زا ندناوخ شیب زا حد رگـسح اه و لاـسرا موادم تاعلاطا هب Broker، هلـصاف ینامز 10 هیناث نیب ره شناوخ رد رظن هتفرگ هدش تسا . هب لیلد زاین هب شیپ شیامرگ و نینچمه توافتم ندوب هلــصاف ینامز يارب ندناوخ رگــسح -2MQ، زا عبات 2printMQ هدافتسا هدش تسا . رد تروص ندیسر ،نامز ریداقم LDR، ،امد طر تبو و PIR هدناوخ هدش و زا قیرط MQTT رشتنم یم دوش . تایئزج هدایپ يزاس رد لیاف cpp.sensors/Sensors/src تسویپ ،هدش لباق هدهاشم تسا .

-4-10 هدایپ يزاس دروبشاد بو و طبار يربراک


لکش (4-6 ) دروبشاد بو

هب وظنم ر مهارف ندرک کی طبار يربراک يارب هدهاـشم تیعـضو ،اهرگـسح تفایرد دادیور ياه رادـشه و لاـسرا نامرف ياه یلرتنک هب ،متـسیـس کی دروبـشاد تحت بو يارب هناماـس یحارط و هدایپ يزاـس هدـش تـسا . نیا دروبـشاد هب تروـص میقتـسم اب Broker MQTT طابترا رارقرب یم دنک و يارب لدابت هداد نایم طبار يربراک و درب 32ESP زا لکتورپ WebSocket over MQTT هدافتسا یم دوش .

پی هدا زاس ی ھناماس

-4-10-2 شخب تامیظنت طابترا اب MQTT

یکی زا تمـسق ياه یلـصا ،دروبـشاد شخب تامیظنت طابترا اب Broker MQTT تـسا . ربراک یم دناوت رتماراپ ياه دروم زاین يارب يرارقرب طابترا ار رد نیا شخب دراو دنک . دروبشاد يارب لاصتا هب Broker زا ود تلاح WebSocket و WebSocketSecure ینابیتشپ یم دنک .

-4-10-3 تفایرد و شزادرپ هداد ياه رگسح اه

هداد ياه اهرگـسح طـسوت 32ESP رد Topic ياه صخـشم رـشتنم یم دنوـش . یماگنه هک کی مایپ MQTT تفایرد یم ،دوـش ادتبا Topic نآ یـسررب هدـش و رب ساـسا Topic، مایپ به تراک رگـسح رظانتم هداتـسرف هدـش و شیامن هداد یم دوش .
يارب شیازفا تیلباق لیلحت ،هداد يارب رگسح ياه يددع رادومن تارییغت زین رد رظن هتفرگ هدش تسا . يارب يریگولج زا شیامن هداد ییاه هک نکمم تـسا طوبرم هب هتـشذگ ،دنـشاب دروبـشاد نامز نیرخآ تفایرد تاعلاطا ره رگــسح ار بث ت یم دنک . رگا شیب زا 30 هیناث زا نیرخأ مایپ کی رگــسح هتــشذگ ،دــشاب تراک هطوبرم هب ناونع هداد یمیدق تملاع يراذگ یم دوش .

-4-10-4 لاسرا نامرف ياه یلرتنک

دروبشاد هولاع رب تفایرد ،هداد ناکما لاسرا نامرف هب 32ESP ار زین مهارف یم دنک . يارب نامرف ياه تفایرد و لاــسرا و فذح و شیامن لانگیــس ياه IR و RF یم ناوت زا شخب نامرف ياه دروبـشاد هدافتـسا درک . نینچمه ناکما لاعف ای لاعفریغ ندرک صیخـشت تکرح و عطق و لـصو ندرک متـسیـس رادشه هاگتسد یم ناوت زا دروبشاد هدافتسا درک .

-4-10-5 متسیس رادشه دروبشاد

يارب شیامن دادیور ياه ،مهم کی راون رادشه رد تمسق ییلااب دروبشاد یحارط هدش سا ت. مایپ ياه طوبرم متسیس صیخشت تکرح و ملاعا دود و قیرح رد نیا تمسق شیامن هداد یم دوش .

-4-10-6 هریخذ تامیظنت دروبشاد

تامیظنت لاـصتا هب Broker دراو هدـش طـسوت ،ربراک رد localstorage رگرورم هریخذ یم دنوـش . نیا شور ثعاب یم دوش ربراک يارب ره راب ارجا ندرک ،دروبشاد يزاین هب دراو ندرک تاعلاطا هتشادن دشاب .

# لصف 5 :

# نومزآ و یبایزرا متسیس

زرا و نومزآ ی با ی سی متس

-5-1 همدقم

سپ از یحارط و هدایپ يزاـس شخب ياه تخـس يرازفا و مرن يرازفا ،هناماـس مزلا تـسا درکلمع متـسیـس رد طیارش فلتخم دروم شیامزآ و یبایزرا رارق دریگ . فده زا ماجنا نومزأ ،اه یـسررب تحـص درکلمع يازجا فلتخم ،هناماـس لبایزرا طابترا نایم لوژام ياه تخـس يرازفا و مرن يرازفا تسا .

-5-2 شور مزآ نو و یبایزرا هناماس

-5-2-1 طیحم و تازیهجت دروم هدافتسا

نومزآ هناماس رب يور درب هعسوت DevKit 32ESP ماجنا هدش تسا . رد شخب ،اهرگـسح زا رگـسح 11DHT يارب هزادنا يریگ امد و ،تبوطر لوژام LDR يارب هزادنا يریگ تدـش ،رون یجورخ گولانآ روــسنــس -2MQ يارب صیخــشت دود و زاگ ياه لباق ا لاعتــش و زا لوژام PIR يارب صیخشت تکرح هدافتسا هدش تسا . نینچمه زا کـی Buzzer Active و هدـنتـــسرف و هدـنریگ RF رد ود دـناـب یـــسناـکرف 315 و 433 زترهاـگم و هدنتسرف و هدنریگ IR هدافتسا هدش تسا .

-5-2-2 رایعم ياه یبایزرا

يارب یبایزرا درکلمع ،هناماس رایعم ياه ریز رد رظن هتفرگ هدش تسا :
- تحص تفایرد تاعلاطا زا رگسح ياه یطیحم
- تحص صیخشت طیارش رادشه
- تحص درکلمع متسیس رادشه یتوص
- تحص يرارقرب طابترا Fi-Wi
- تحص يرارقرب طابترا اب Broker MQTT
- تحص تفایرد نامرف ياه یلرتنک
- تحص ،تفایرد هریخذ و لاسرا لانگیس ياه RF
- تحص ،تفایرد هریخذ و لاسرا لانگیس ياه IR
- تحص درکلمع متسیس Provisioning
- تحص درکلمع دروبشاد بو

زرا و نومزآ ی با ی سی متس

-5-3 نومزآ درکلمع اهرگسح

-5-3-1 نومزآ رگسح امد و تبوطر

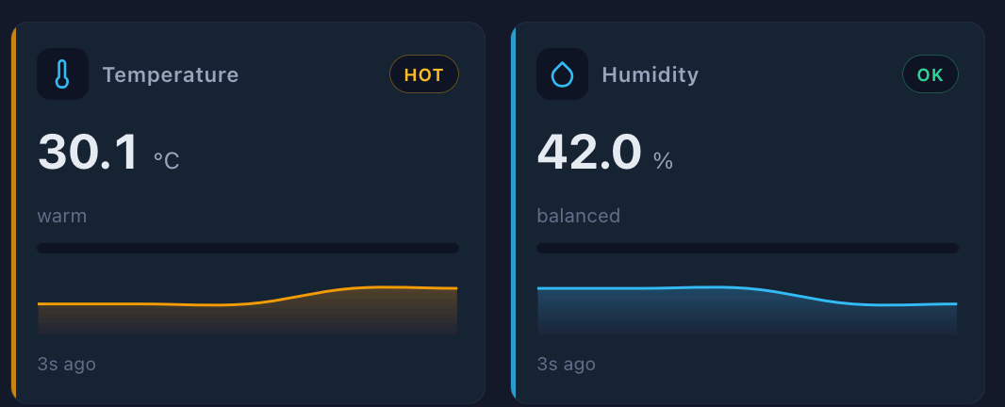
[picture p77: figure]

لکش (5-1 ) جیاتن رگسح امد و تبوطر

يارب یـسررب درکلمع رگـسح 11DHT، هداد ياه امد و تبوطر هب تروـص هرود يا زا قیرط عباوت طوبرم هب نیا رگسح تفایرد یم دنوش .
روطنامه هک هدهاشم یم دوش نیا رگسح هب یتسرد راک یم دنک .

-5-3-2 نومزآ رگسح رون

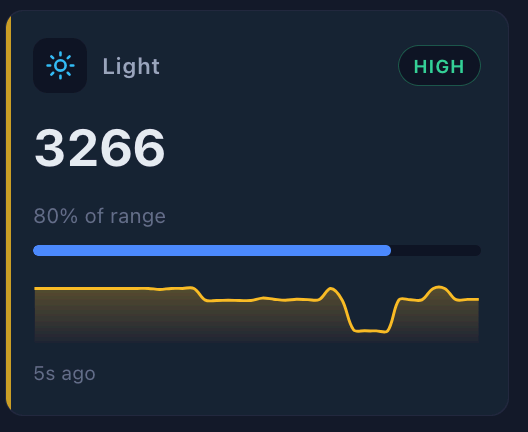
[picture p78: figure]

لکش (5-2 ) هجیتن رگسح رون

يارب یـسررب درکلمع رگـسح LDR، طیارـش يرون طیحم رییغت هداد هدـش و راتفر رادقم یجورخ LDR یـسررب یم دوش . راظتنا یم ر دو اب رییغت تدش ،رون رادقم هدناوخ هدش زا يدورو گولانآ زین رییغت دنک . روطنامه هک هدهاــشم یم دوــش نیا رگــسح هب یتــسرد راک یم دنک و اب رییغت رون طیحم ریداقم توافتم یجورخ یم دهد .

زرا و نومزآ ی با ی سی متس

-5-3-3 نومزآ رگسح دود و شتآ

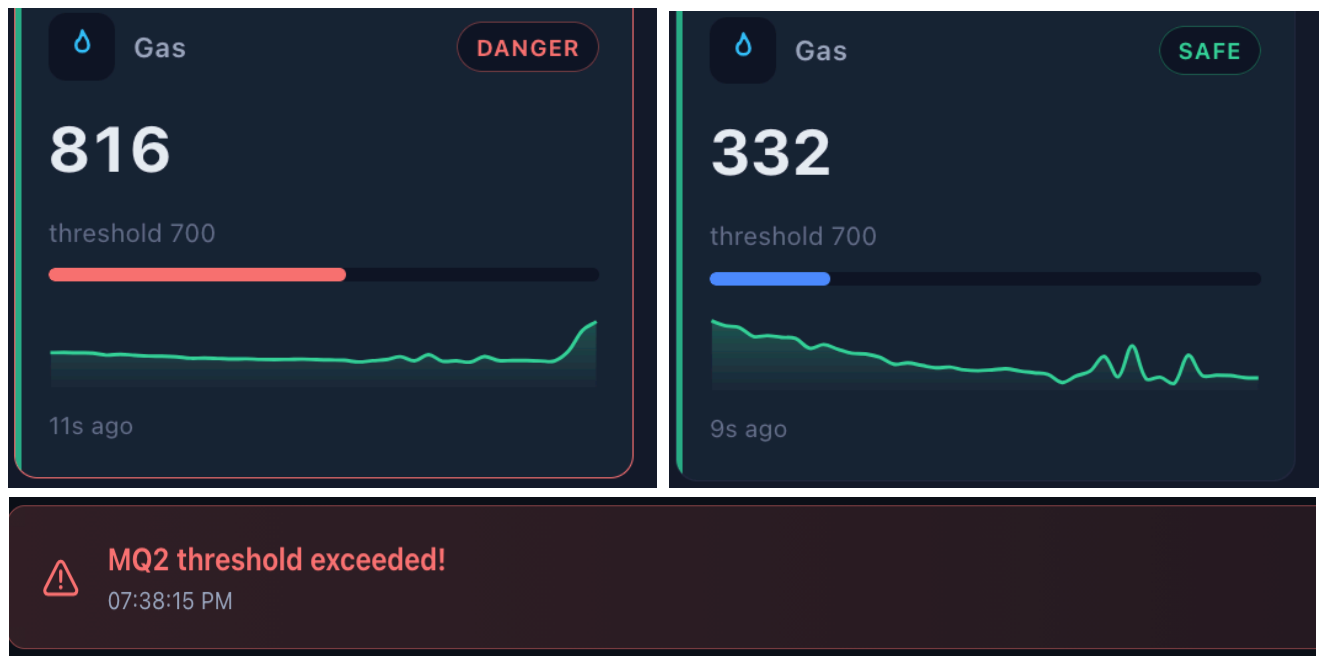
[picture p79: figure]

لکش (5-3 ) جیاتن رگسح دود و شتآ

رد نومزآ نیا ،شخب ادتبا هاگتـسد رد طیارـش يداع رارق هتفرگ و رادقم یجورخ یـسررب یم دوـش . سپـس رد طیارش دود و شتآ رارق هتفرگ و شنکاو متسیس تبسن هب شیازفا رادقم روسنس یبایزرا یم دوش . روطنامه هک هدهاـشم یم دوـش نیا رگـسح رد طیارـش يداع يددع رد هزاب 300 ات 350 و رد یارـش ط شتآ يددع رتلااب زا 700 هک هب ناونع هناتسآ شتآ رد رظن هتفرگ هدش تسا یم دهد . نینچمه هدهاـشم یم دوـش هک رد نامز ،شتآ تیعـضو رادـشه ار لاعف هدرک و مایپ هطوبرم ار هب ناونع رادـشه لاسرا یم دنک .

-5-3-4 نومزآ رگسح صیخشت تکرح

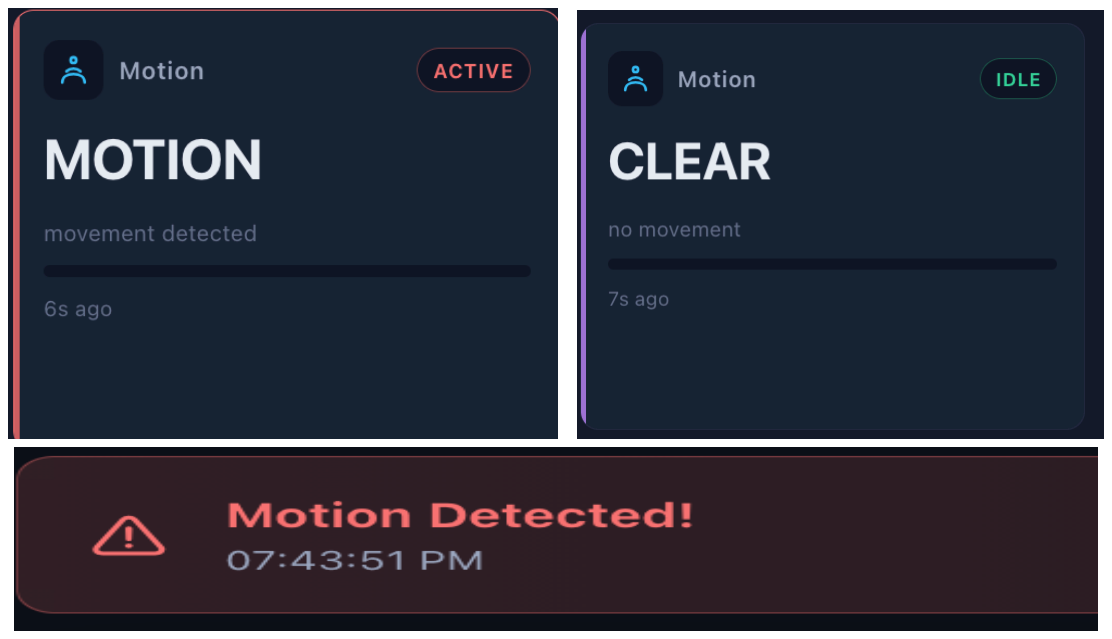
[picture p80: figure]

لکش (5-4 ) جیاتن رگسح صیخشت تکرح

زرا و نومزآ ی با ی سی متس

يارب یـسررب درکلمع ـسح ،رگ رگـسح ادتبا رد طیارـش يداع رارق هداد یم دوـش و سپـس کی یـش رد يولج ،نآ ناکت هداد یم دوش و شنکاو متسیس یبایزرا یم دوش . روطنامه هک هدهاـشم یم دوـش نیا رگـسح هب یتـسرد تکرح ار صیخـشت یم دهد و رد یتروـص هک تیلباق صیخشت تکرح متسیس لاعف ،دشاب تیعضو رادشه ار لاعف هدرک و مایپ هطوبرم ار لاسرا یم دنک .

-5-4 نومزآ هناماس رادشه

رد نیا ،نومزآ درکلمع Buzzer دروم یـسررب رارق یم دریگ . رد تروـص لاعف ندـش تیعـضو ،رادـشه Buzzer هب تروـص بوانتم لاعف و ریغ لاعف یم دوـش و رد تروـص لاعفریغ ندـش تیعـضو ،رادـشه Buzzer لاعفریغ یم دوش .
Buzzer رد نیا نومزآ هب یتــسرد لمع هدرک و رد نامز رادــشه لاعف هدــش و اب ریغ لاعف ندرک ،رادــشه Buzzer زین لاعفریغ یم دوش .

### -5-5 نومزآ لاصتا هب Fi-Wi و Broker MQTT

لکش (5-5 ) هجیتن نومزآ لاصتا هب هکبش و Broker MQTT

رد نیا ،نومزآ درکلمع لاــصتا هب fi-Wi و Broker MQTT و نینچمه لاــسرا و رد تفای مایپ دروم یــسررب رارق یم دریگ .
روطنامه هک هدهاـشم یم ،دوـش هاگتـسد هب یتـسرد هب هکبـش Fi-Wi و سپـس هب Broker MQTT لـصتم یم دوش . لاسرا مایپ و تفایرد مایپ زا Broker زین هب یتسرد راک یم دنک .

-5-6 نومزآ دروبشاد هناماس

رد نیا نومزآ درکلمع شخب ياه فلتخم دروبشاد دروم ررب یس رارق یم دریگ .

زرا و نومزآ ی با ی سی متس

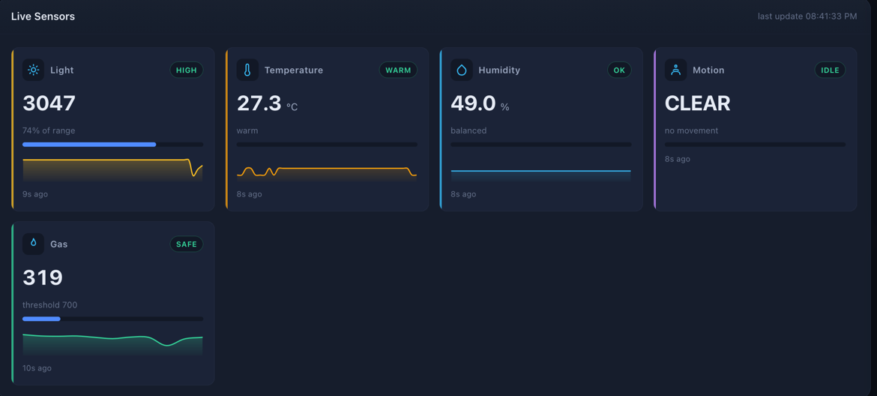
[picture p81: figure]

لکش (5-6 ) شیامن تاعلاطا اهرگسح رد دروبشاد

رد ،ادتبا شخب شیامن تاعلاطا رگسح اه دروم یسررب رارق هتفرگ یم دوش هک هب یتسرد راک یم دنک .

لکش (5-7 ) شیامن رادشه رد دروبشاد

سپس ، شخب شیامن تیعضو رادشه دروم یسررب رارق هتفرگ یم دوش هک هب یتسرد راک یم دنک .


لکش (5-8 ) لاسرا نامرف زا دروبشاد

و رد ،رخآ شخب لاـسرا نامرف زا دروبـشاد هب هاگتـسد دروم یـسررب رارق هتفرگ یم دوـش هک هب یتـسرد راک یم دنک .

زرا و نومزآ ی با ی سی متس

-5-7 نومزآ متسیس RF

-5-7-1 نومزآ تفایرد لانگیس RF

لکش (5-9 ) تفایرد لانگیس RF

رد نیا نومزآ تفایرد لانگیس زا تومیر دروم یسررب رارق یم دریگ . روطنامه هک هدهاشم یم ،دوش لانگیس هب تروص تسرد زا تومیر RF تفایرد هدش و اب مان هداد هدش هریخذ یم دوش .

-5-7-2 نومزآ لاسرا لانگیس RF

لکش (5-10 ) لاسرا لانگیس RF

رد نیا نومزآ لاسرا لانگیس هریخذ هدش دروم یسررب رارق یم دریگ . روطنامه هک هدهاشم یم ،دوش لانگیس هریخذ هدش هب یتسرد لاسرا یم دوش .

-5-7-3 نومزآ تیریدم لانگیس RF

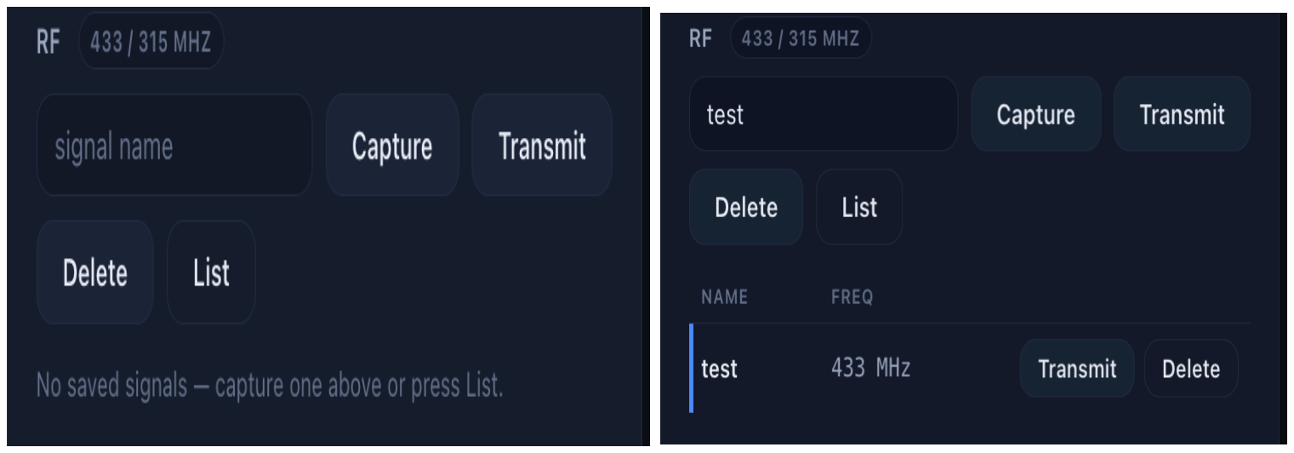
[picture p82: figure]

زرا و نومزآ ی با ی سی متس

لکش (5-11 ) تیریدم لانگیس RF

رد نیا نومزآ تیریدم لانگیـس اه لماـش تـسرهف ندرک مامت لانگیـس اه و فذح کی لانگیـس صخـشم دروم یسررب رارق یم دریگ .
روطنامه هک هدهاـشم یم ،دوـش تـسرهف لانگیـس اه هب یتـسرد شیامن هداد یم دوـش و نینچمه سپ از فذح کی ،لانگیس نآ زا تسرهف فذح یم دوش .

-5-8 نومزآ متسیس IR

-5-8-1 نومزآ تفایرد لانگیس IR


لکش (5-12 ) تفایرد لانگیس IR

رد نیا نومزآ تفایرد لانگیس زا لرتنک IR دروم یسررب رارق یم دریگ . روطنامه هک هدهاـشم یم ،دوـش لانگیـس هب تروـص تـسرد زا لرتنک IR تفایرد هدـش و اب مان هداد هدـش هریخذ یم دوش .

-5-8-2 نومزآ لاسرا لانگیس IR

لکش (5-13 ) لاسرا لانگیس IR

رد نیا نومزآ لاسرا لانگیس هریخذ هدش دروم یسررب رارق یم دریگ . روطنامه هک هدهاشم یم ،دوش لانگیس هریخذ هدش هب یتسرد را لاس یم دوش .

زرا و نومزآ ی با ی سی متس

-5-8-3 نومزآ تیریدم لانگیس IR

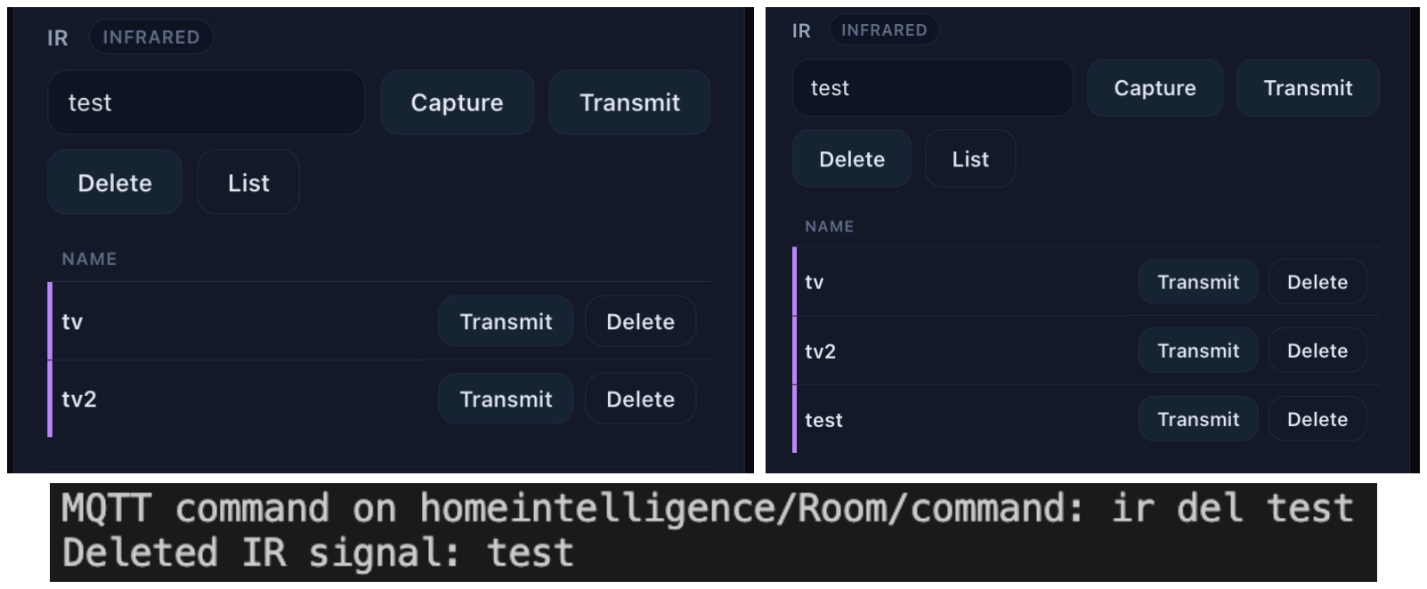
[picture p83: figure]

لکش (5-14 ) تیریدم لانگیس IR

رد نیا نومزآ تیریدم لانگیـس اه لماـش تـسرهف ندرک مامت لانگیـس اه و فذح کی لانگیـس صخـشم دروم یسررب رارق یم دریگ .
روطنامه هک هدهاـشم یم ،دوـش تـسرهف لانگیـس اه هب یتـسرد شیامن هداد یم دوـش و نینچمه سپ زا فذح کی ،لانگیس نآ زا تسرهف فذح یم دوش .

زرا و نومزآ ی با ی سی متس

### -5-9 نومزآ ریز هناماس Provisioning

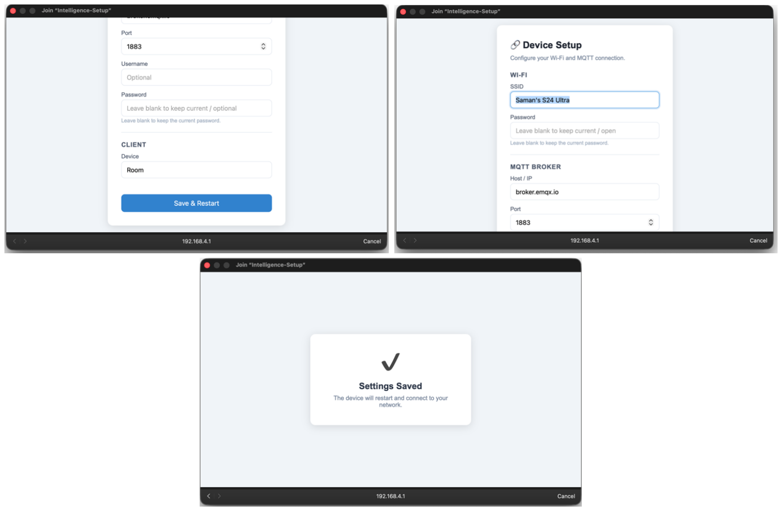
[picture p84: figure]

لکش (5-15 ) هحفص تامیظنت Provisioning

رد نیا نومزآ درکلمع هناماسریز Provisioning دروم یسررب رارق یم دریگ . روطنامه هک هدهاـشم یم ،دوـش هحفـص تامیطنت سپ زا لاـصتا هب تروـص راکدوخ شیامن هداد یم دوـش و سپ زا دراو ندرک ،تاعلاطا تامیظنت هریخذ هدش و ESP هار يزادنا ددجم یم دوش .

-5-10 عمج يدنب لصف

رد نیا ،لصف درکلمع متسیس هعسوت هتفای رد طیارش فلتخم دروم نومزآ و یسررب رارق تفرگ . جیاتن نیا نومزآ اه ییانبم يارب یبایزرا نازیم ققحت فادها هژورپ و ییاـسانـش طاقن توق و فعـض هناماـس ار مهارف یم دننک .

# لصف 6 :

# هجیتن يریگ

تن ی هج گیری

-6-1 همدقم

رد نیا ،لـصف جیاتن لـصاح زا ،یحارط هدایپ يزاـس و یبایزرا هناماـس دنمـشوه صیخـشت دود و شتآ و لرتنک تازیهجت یکیرتکلا هئارا یم دوـش . فده یلـصا نیا ،هژورپ یحارط و هعـسوت کی هناماـس ینتبم رب تنرتنیا ایـشا هدوب تــسا هک دناوتب هولاع رب شیاپ یخرب رتماراپ ياه ،یطیحم طیارــش يداعریغ دننام شیازفا نازیم زاگ و دود ای صیخـشت تکرح ار ییاـسانـش هدرک و رد تروـص ،زاین رادـشه بـسانم ار لاعف ک دن . نینچمه اب هدافتـسا زا تاـطاـبترا نوداـم زمرق ( IR ( و سناـکرف ییویدار (RF(، ناـکما ،تـفاـیرد هریخذ و لاـــسرا ددـجم ناـمرف ياـه لرتنک زا هار رود مهارف هدش تسا .

-6-2 عمج يدنب لحارم ماجنا هژورپ

رد نیا هژورپ ادتبا يدنمزاین ياه هناماـس یـسررب دش . رب ساسا نیا يدنمزاین ،اه کی امعم ير تخس يرازفا و مرن يرازفا ینتبم رب 32ESP یحارط دیدرگ . رد شخب تخـس ،رازفا رگـسح 11DHT يارب هزادنا يریگ امد و ،تبوطر لوژام LDR يارب هزادنا يریگ تدـش ،رون رگـسح -2MQ يارب هزادنا يریگ رادقم دود و زاگ ياه لباق لاعتـشا و رگـسح PIR يارب صیخـشت تکرح رد رظن هتفرگ دندش .
در شخب یطابترا تخـس ،رازفا زا لوژام ياه 61RXB و 35RXB يارب نتفرگ لانگیـس ياه ییویدار و زا ود لوژام S34H يارب لاسرا لانگیس ياه ییویدار رد دناب یسناکرف 315 و 433 زترهاگم هدافتسا دش . نینچمه زا هدنریگ نودام زمرق و LED نودام زمرق يارب تاطابترا نودام زمرق هدافتسا دش . رد شخب تخـس ،رازفا همانرب هب تروـص رلاوژام یحارط هدـش و فیاظو فلتخم نایم لوژام اه میـسقت هدـش دنا . نیا راتخاس بجوم هدش تسا هک هعسوت و يرادهگن مرن رازفا تبسن هب کی همانرب هچراپکی هداس رت دشاب .

-6-3 جیاتن لصاح زا هدایپ يزاس

جیاتن هدایپ يزاـس ناـشن یم دهد هک هناماـس هتـسناوت تـسا هعومجم يا زا فیاظو دروم رظن هژورپ ار رد کی راتخاس دحاو هدایپ يزاس دنک . تیلباق ياه لصاح هدش لماش دراوم ریز تسا :
- تفایرد تاعلاطا امد و تبوطر زا رگسح 11DHT
- تفایرد رادقم تدش رون زا رگسح LDR
- تفایرد رادقم ود د و زاگ ياه لباق لاعتشا زا رگسح 2MQ
- صیخشت تیعضو تکرح طسوت رگسح PIR
- لاعف يزاس رادشه یتوص رد طیارش رطخ
- ،تفایرد هریخذ و لاسرا لانگیس ياه ییویدار رد ود دناب یسناکرف 315 و 433 زترهاگم
- ،تفایرد هریخذ و لاسرا لانگیس ياه نودام زمرق

تن ی هج گیری
- لاصتا هب هکبش Fi-Wi و Broker MQTT
- لاسرا هداد ياه رگسح اه هب دروبشاد
- تفایرد نامرف ياه یلرتنک زا دروبشاد

-6-4 تیدودحم ياه هژورپ

اب دوجو هدایپ يزاس تیلباق ياه یلصا ، هناماس ياراد تیدودحم ییاه تسا هک دیاب دروم هجوت رارق دنریگ . ،تـسخن رادقم یجورخ -2MQ رد نیا هژورپ هب تروـص میقتـسم و اب کی رادقم هناتـسآ مرن يرازفا یـسررب یم دوـش . نیاربانب نیا رادقم هب طیارـش ،یطیحم نامز مرگ ندـش رگـسح و یگژیو ياه یکیزیف نآ هتـسباو تـسا و يارب هدافتـسا هب ناونع هناماـس درادناتـسا ملاعا قیرح دنمزاین نویـساربیلاک و یـسررب ياه یـصـصخت رتـشیب ي دهاوخ دوب .
،مود تیلباق RF و IR هب يراگزاـس تازیهجت رظندروم اب عون لانگیـس ياه لباق تفایرد و لاـسرا طسوت تخس رازفا و هناخباتک ياه هدافتـسا هدـش هتـسباو تـسا . نیاربانب یمن ناوت نیمـضت درک هک مامت تازیهجت دوجوم رد رازاب اب نیا هناماس لباق لرتنک دنشاب . نینچمه Broker دروم هدافتـسا رد هدایپ يزاـس ،ییاهن کی Broker یمومع تـسا . نیاربانب يارب هدافتـسا رد طیحم ياه یعقاو و ،ساـسح هدافتـسا زا تخاـسریز یـصاـصتخا و لامعا راکوزاـس ياه یتینما دننام زارحا تیوه و يراگنزمر طابترا هیصوت یم دوش .

-6-5 داهنشیپ ياه هعسوت رد هدنیآ

-6-5-1 شیازفا تینما تاطابترا

رد هخـسن ياه هدنیآ یم ناوت طابترا MQTT ار هب TLS over MQTT و يارب Broker زارحا تیوه بـسانم فیرعت دومن .

-6-5-2 هدافتسا زا Broker یصاصتخا

هب ياج هدافتسا زا Broker ،یمومع یم ناوت کی Broker یصاصتخا رد رورس اب تخاسریز يربا رقتسم درک .

-6-5-3 هعسوت تیلباق OTA

هفاـضا ندرک تیلباق (OTA (Air-The-Over یم دناوت ناکما یناـسرزورب Firmware هاگتـسد ار نودب لاـصتا یکیزیف 32ESP هب هنایار مهارف دنک .

تن ی هج گیری
-6-5-4 هفاضا ندرک تاطابترا نیزگیاج

رد هـخـــسن ياـه هدـنیآ یم ناوت رد راـنک Fi-Wi زا يرواـنف ییاـه دـنناـم GSM، LoRa اـی ریاـــس شور ياـه یطابترا هدافتسا درک ات رد تروص عطق هکبش Fi-Wi، ریسم ینیزگیاج يارب لاسرا رادشه دوجو هتشاد دشاب .

-6-6 عمج يدنب ییاهن

رد ،عومجم جیاتن هژورپ ناــشن یم دهد هک یم ناوت اب هدافتــسا زا کی درب مک هنیزه و بیکرت رگــسح ياه ،یطیحم طابترا MQTT و تیلباق ياه RF و IR، کی باه دنمشوه هروظنمدنچ يارب شیاپ و لرتنک طیحم داجیا درک . اب نیا ،لاح يارب لیدبت نیا هنومن یهاگـشناد هب کی لوـصحم لباق دافتـسا ه رد طیحم ياه ،یعقاو ماجنا نویـساربیلاک قیقد رگـسح ،اه شیازفا تینما تاطابترا و هدافتـسا زا تخاـسریز یطابترا یـصاـصتخا و ماجنا نومزآ ياه درادناتسا يرورض دهاوخ دوب .

# لصف 7 :

# عجارم

89

عجارم
عجارم

Bibliography

[1] National Institute of Standards and Technology (NIST), "IoT Device," 2024. [Online]. Available: https://csrc.nist.gov/glossary/term/iot_device. [Accessed August 2026].
[2] J. Voas, "Networks of 'Things'," National Institute of Standards and Technology, NIST Special Publications 800-183, 2016.
[3] Espressif Systems, "ESP32 series Datasheet," Espressif Systems.
[4] A. Banks, E. Briggs, K. Borgendale and R. Gupta, "MQTT Version 5.0," OASIS Standards, 2019.
[5] S. Ullrich, "rc-switch: Arduino library to operate 315/433 MHz remote controlled devices," [Online]. Available: https://github.com/sui77/rc-switch. [Accessed August 2026].
[6] D. Conran et al., "IRremoteESP8266: Infrared remote library for ESP8266/ESP32," [Online]. Available: https://github.com/crankyoldgit/IRremoteESP8266. [Accessed August 2026].
[7] Hanwei Electronics Group Corporation, "MQ-2 Gas Sensor Datasheet," Hanwei Electronics Group Corporation.
[8] Adafruit Industries, "DHT Sensor Library Documentation," [Online]. Available: https://adafruit.github.io/DHT-sensor-library/. [Accessed August 2026].
[9] Espressif Systems, "Arduino ESP32 Wi-Fi Documentation," Espressif Systems.
[10] Arduino ESP32, "LittleFS File System Documentation," Espressif Systems.

# لصف 8 :

# تسویپ اه

-8-1 هشقن کیتامش رادم
